balena-io-hardware/fin-info-doc/documentation/PDF/balenaFin/v1.1/conformity/CAN/Lab/DFS.pdf

JianYan Testing Group Shenzhen Co., Ltd.

### Report No: JYTSZE201205705

Authorized Signature:

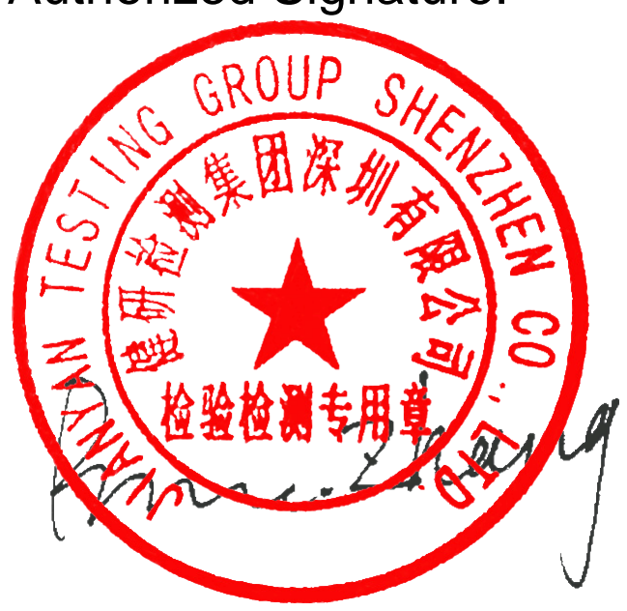
[picture p44: figure]

Bruce Zhang
Laboratory Manager
This report details the results of the testing carried out on one sample. The results contained in this test report do not relate to other samples of the same product and does not permit the use of the JYT product certification mark. The manufacturer should ensure that all products in series production are in conformity with the product sample detailed in this report.

This report may only be reproduced and distributed in full. If the product in this report is used in any configuration other than that detailed in the report, the manufacturer must ensure the new system complies with all relevant standards.

This document cannot be reproduced except in full, without prior written approval of the Company. Any unauthorized alteration, forgery or falsification of the content or appearance of this document is unlawful and offenders may be prosecuted to the fullest extent of the law. Unless otherwise stated the results shown in this test report refer only to the sample(s) tested and such sample(s) are retained for 90 days only.

## 1 Cover Page

# DFS TEST REPORT

Applicant: | Balena Ltd.
Address of Applicant: | 6th Floor, One London Wall London, London, EC2Y 5EB United Kingdom

### Equipment Under Test (EUT)

Product Name: | balenaFin
Model No.: | v1.1
HVIN: | FINV10
Trade mark: | balenaFin
Canada IC: | 26817-FIN0110
Applicable standards: | RSS-247 Issue 2，February 2017
Date of sample receipt: | 23 Aug., 2019
Date of Test: | 24 Aug., to 26 Dec., 2019
Date of report issued: | 12 Jan., 2021
Test Result: | PASS *

*In the configuration tested, the EUT complied with the standards specified above.

### Report No: JYTSZE201205705

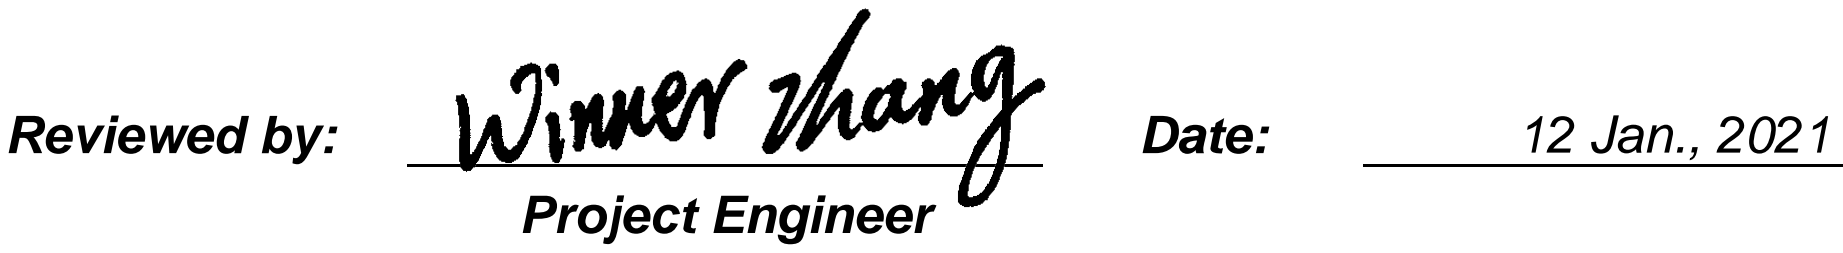
[picture p45: figure]
Reviewed by:; Date:; 12 Jan., 2021; Project Engineer

JianYan Testing Group Shenzhen Co., Ltd. | Project No.: JYTSZE2012057
No.110~116, Building B, Jinyuan Business Building, Xixiang Road,
Bao’an District, Shenzhen, Guangdong, China
Telephone: +86 (0) 755 23118282 Fax: +86 (0) 755 23116366 | Page 2 of 13

## 2 Version

Version No. | Date | Description
00 | 18 Dec., 2020 | Original
01 | 12 Jan., 2021 | Add HVIN
Tested by: | Date: | 12 Jan., 2021

### Test Engineer

Telephone: +86 (0) 755 23118282 Fax: +86 (0) 755 23116366 | Page 3 of 13

## 3 Contents

Page

Telephone: +86 (0) 755 23118282 Fax: +86 (0) 755 23116366 | Page 4 of 13

## 4 Test Summary

Test Items | Limit | Result
Channel Availability Check | > 60 seconds | N/A
UNII Detection Bandwidth | > 100% of the UNII 99% transmission power bandwidth | N/A
Statistical Performance Check | Radar type 1,2,3,4 ≧ 60% Aggregate Radar type 1~4 and 5 ≧ 80% Radar type 6 ≧ 70% | N/A
Channel Move Time | < 10 seconds | N/A
Channel Closing Transmission Time | < 20ms + aggregate of 60ms over remaining 10 second period | Pass
Non-Occupancy Period | > 30 minutes | N/A

Remark:
1. Pass: means meet the requirements.
2. N/A: means not applicable.
3. The cable insertion loss used by “RF Output Power” and other conduction measurement items is 0.5dB (provided by the customer).

Test Method:

ANSI C63.4-2014
ANSI C63.10-2013
KDB 789033 D02 General UNII Test Procedures New Rules v02r01

Telephone: +86 (0) 755 23118282 Fax: +86 (0) 755 23116366 | Page 5 of 13

## 5 General Information

## 5.1 Client Information

Applicant: | Balena Ltd.
Address: | 6th Floor, One London Wall London, London, EC2Y 5EB United Kingdom
Manufacturer: | Balena Ltd.
Address: | 6th Floor, One London Wall London, London, EC2Y 5EB United Kingdom
Factory: | Fae Technology S.p.a.
Address: | Via C. Battisti, 136 Gazzaniga (BG) 24025 - Italia
5.2 General Description of E.U.T.
Product Name: | balenaFin
Model No.: | v1.1
Transmitter frequency range: | Band 2: 5250MHz-5350MHz Band 3: 5470MHz-5725MHz
Modulation type: | OFDM
WLAN Function: | 802.11a/802.11n/802.11ac
Bandwidth: | 20MHz/40MHz/80MHz
Antenna Type: | Internal Antenna External Antenna
Antenna Gain: | Internal Antenna: 1dBi External Antenna: 2dBi
DFS Operation Type: | Master Device Slaver Device with Radar detection function Slaver Device without Radar detection function
Power supply: | DC3.3V
Test Sample Condition: | The test samples were provided in good working order with no visible defects.

## 5.3 Test Environment and test mode

Data Load mode: | Keep the EUT in normal transmitting mode by WiFi
Temperature: | 20 ~ 25 ℃
Humidity: | 60% ~ 65%
Atmospheric pressure: | 1012 kPa

## 5.4 Description of Support Units

Manufacturer | Description | Model | Serial Number
GSP | Adapter | GSCV0600S019V12E | N/A
Raspberry Pi | Compute Module | Compute Module 3/3+ Lite | N/A

## 5.5 Related Submittal(s) / Grant (s)

This is an original grant, no related submittals and grants.

## 5.6 Additions to, deviations, or exclusions from the method

No

Telephone: +86 (0) 755 23118282 Fax: +86 (0) 755 23116366 | Page 6 of 13

## 5.7 Laboratory Facility

The test facility is recognized, certified, or accredited by the following organizations:
- FCC - Designation No.: CN1211
JianYan Testing Group Shenzhen Co., Ltd. has been accredited as a testing laboratory by FCC(Federal Communications Commission). The test firm Registration No. is 727551.
- ISED – CAB identifier.: CN0021
The 3m Semi-anechoic chamber of JianYan Testing Group Shenzhen Co., Ltd. has been Registered by Certification and Engineering Bureau of Industry Canada for radio equipment testing with Registration No.: 10106A-1.
- A2LA - Registration No.: 4346.01
This laboratory is accredited in accordance with the recognized International Standard ISO/IEC 17025:2005 General requirements for the competence of testing and calibration laboratories. The test scope can be found as below link: https://portal.a2la.org/scopepdf/4346-01.pdf

## 5.8 Laboratory Location

JianYan Testing Group Shenzhen Co., Ltd.
Address: No.110~116, Building B, Jinyuan Business Building, Xixiang Road, Bao’an District, Shenzhen, Guangdong, China
Tel: +86-755-23118282, Fax:+86-755-23116366
Email: info@ccis-cb.com, Website: http://www.ccis-cb.com

## 5.9 Test Instruments list

Test Equipment | Manufacturer | Model No. | Serial No. | Cal. Due date (mm-dd-yy) | Cal. Due date (mm-dd-yy)
Spectrum Analyzer | Agilent | N9020A | MY50510123 | 11-10-2018 | 11-09- 2019
11-09-2019 | 11-08- 2020
Vector Signal Generator | Agilent | N5182A | MY49060014 | 11-10-2018 | 11-09- 2019
11-09-2019 | 11-08- 2020
RF Switch Unit | Ascentest | AT890-RFB | -- | -- | --
DFS Test Software | MWRFTEST | MTS 8310 | Version: 2.0.0.0
N7607B Signal Studio | KEYSIGHT | -- | Version: 2.0.0.1

Telephone: +86 (0) 755 23118282 Fax: +86 (0) 755 23116366 | Page 7 of 13

## 6 DFS Technical Requirements

## 6.1 DFS Parameters

Table D.1: Applicability of DFS Requirements Prior to Use of a Channel
Requirement | Operational Mode
Master | Client Without Radar Detection | Client With Radar Detection
Non-Occupancy period | Yes | Not required | Yes
DFS Detection Threshold | Yes | Not required | Yes
Channel Availability Check Time | Yes | Not required | Not required
U-NII Detection Bandwidth | Yes | Not required | Yes

Table D.2: Applicability of DFS requirements during normal operation
Requirement | Operational Mode
Master | Client Without Radar Detection
DFS Detection Threshold | Yes | Not required
Channel Closing Transmission Time | Yes | Yes
Channel Move Time | Yes | Yes
U-NII Detection Bandwidth | Yes | Not required
Additional requirements for devices with multiple bandwidth modes | Operational Mode
Master Device or Client with Radar Detection | Client Without Radar Detection
U-NII Detection Bandwidth and Statistical Performance Check | All BW modes must be tested | Not required
Channel Move Time and Channel Closing Transmission Time | Test using widest BW mode available | Test using the widest BW mode available for the link
All other tests | Any single BW mode | Not required
Note: Frequencies selected for statistical performance check (Section 7.8.4) should include several frequencies within the radar detection bandwidth and frequencies near the edge of the radar detection bandwidth. For 802.11 devices it is suggested to select frequencies in each of the bonded 20 MHz channels and the channel center frequency.

Table D.3: DFS Detection Thresholds
Maximum Transmit Power | Value (See Notes 1,2, and 3)
EIRP ≧ 200 mW | -64 dBm
EIRP < 200 mW and power spectral density < 10 dBm/MHz | -62 dBm
EIRP < 200 mW that do not meet the power spectral density requirement | -64 dBm

Note 1: This is the level at the input of the receiver assuming a 0 dBi receive antenna.
Note 2: Throughout these test procedures an additional 1 dB has been added to the amplitude of the test transmission waveforms to account for variations in measurement equipment. This will ensure that the test signal is at or above the detection threshold level to trigger a DFS response.
Note 3: EIRP is based on the highest antenna gain. For MIMO devices refer to KDB Publication 662911 D01.

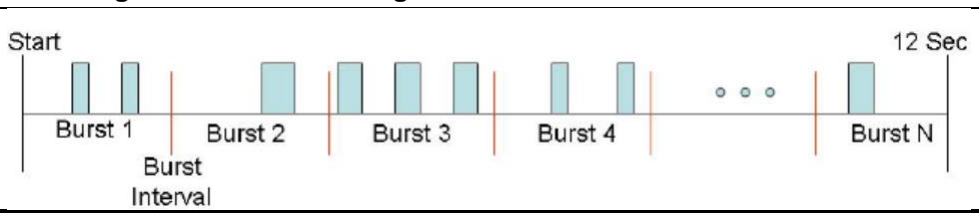
[picture p46: figure]

Telephone: +86 (0) 755 23118282 Fax: +86 (0) 755 23116366 | Page 8 of 13

Table D.4: DFS requirement values
Parameter | Value
Non-occupancy period | Minimum 30 minutes
Channel Availability Check Time | 60 seconds
Channel Move Time | 10 seconds (See Note 1)
Channel Closing Transmission Time | 200 ms + an aggregate of 60ms over remaining 10 second period (See Notes 1 and 2)
U-NII Detection Bandwidth | Minimum 100% of the UNII 99% transmission power bandwidth (See Note 3)

Note 1: Channel Move Time and the Channel Closing Transmission Time should be performed with Radar Type
0. The measurement timing begins at the end of the Radar Type 0 burst.
Note 2: The Channel Closing Transmission Time is comprised of 200 milliseconds starting at the beginning of the Channel Move Time plus any additional intermittent control signals required to facilitate a Channel move (an aggregate of 60 milliseconds) during the remainder of the 10 second period. The aggregate duration of control signals will not count quiet periods in between transmissions.
Note 3: During the U-NII Detection Bandwidth detection test, radar type 0 should be used. For each frequency step, the minimum percentage of detection is 90 percent. Measurements are performed with no data traffic.

Table D.5: Short Pulse Radar Test Waveforms
Radar Type | Pulse Width (μsec) | PRI (μsec) | Number of Pulses | Minimum Percentage of Successful Detection | Minimum Number of Trials
0 | 1 | 1428 | 18 | See Note 1 | See Note 1
1 | 1 | Test A Test B | | 60% | 30
2 | 1-5 | 150-230 | 23-29 | 60% | 30
3 | 6-10 | 200-500 | 16-18 | 60% | 30
4 | 11-20 | 200-500 | 12-16 | 60% | 30
Aggregate (Radar Types 1-4) | | | | 80% | 120
Note 1: Short Pulse Radar Type 0 should be used for the detection bandwidth test, channel move time, and channel closing time tests.

Table D.6: Long Pulse Radar Test Waveform
Radar Type | Pulse Width (μsec) | Chirp Width (MHz) | PRI (μsec) | Number of Pulses per Burst | Number of Bursts | Minimum Percentage of Successful Detection | Minimum Number of Trials
5 | 50-100 | 5-20 | 1000-2000 | 1-3 | 8-20 | 80% | 30

Long Pulse Radar Test Signal Wave form 12 second transmission

Table D.7: Frequency Hopping Radar Test Waveform
Radar Type | Pulse Width (μsec) | PRI (μsec) | Pulses per Hop | Hopping Rate (kHz) | Hopping Sequence Length (msec) | Minimum Percentage of Successful Detection | Minimum Number of Trials
6 | 1 | 333 | 0 | 0.333 | 300 | 70% | 30


Telephone: +86 (0) 755 23118282 Fax: +86 (0) 755 23116366 | Page 9 of 13

## 6.2 DFS Technical Requirements

Requirement | DFS Operational mode
Master | Slave without Radar Detection | Slave with Radar Detection
Channel Availability Check | √ | Not Required | Not Required
UNII Detection Bandwidth | √ | Not Required | √
Statistical Performance Check | √ | Not Required | √
Channel Move Time | √ | Not Required | √
Channel Closing Transmission Time | √ | √ | √
Non-Occupancy Period | √ | Not Required | √

## 6.3 DFS Threshold Level

DFS Threshold Level
5250MHz ~ 5350MHz | -62 dBm @ antenna connector
5470MHz ~ 5725MHz | -62 dBm @ antenna connector
Note: The worst case level was selected to perform the test.

## 6.4 Test Setup Block

For master device

For Slaver without radar detection function device


Telephone: +86 (0) 755 23118282 Fax: +86 (0) 755 23116366 | Page 10 of 13

For Slaver with radar detection function device

## 6.5 EUT Configuration for DFS Test

Test Items | Channel Frequency
Channel Closing Transmission Time | 5290MHz, 5530MHz

## 7 Test Result

## 7.1 Channel Move Time and Channel Closing Transmission Time

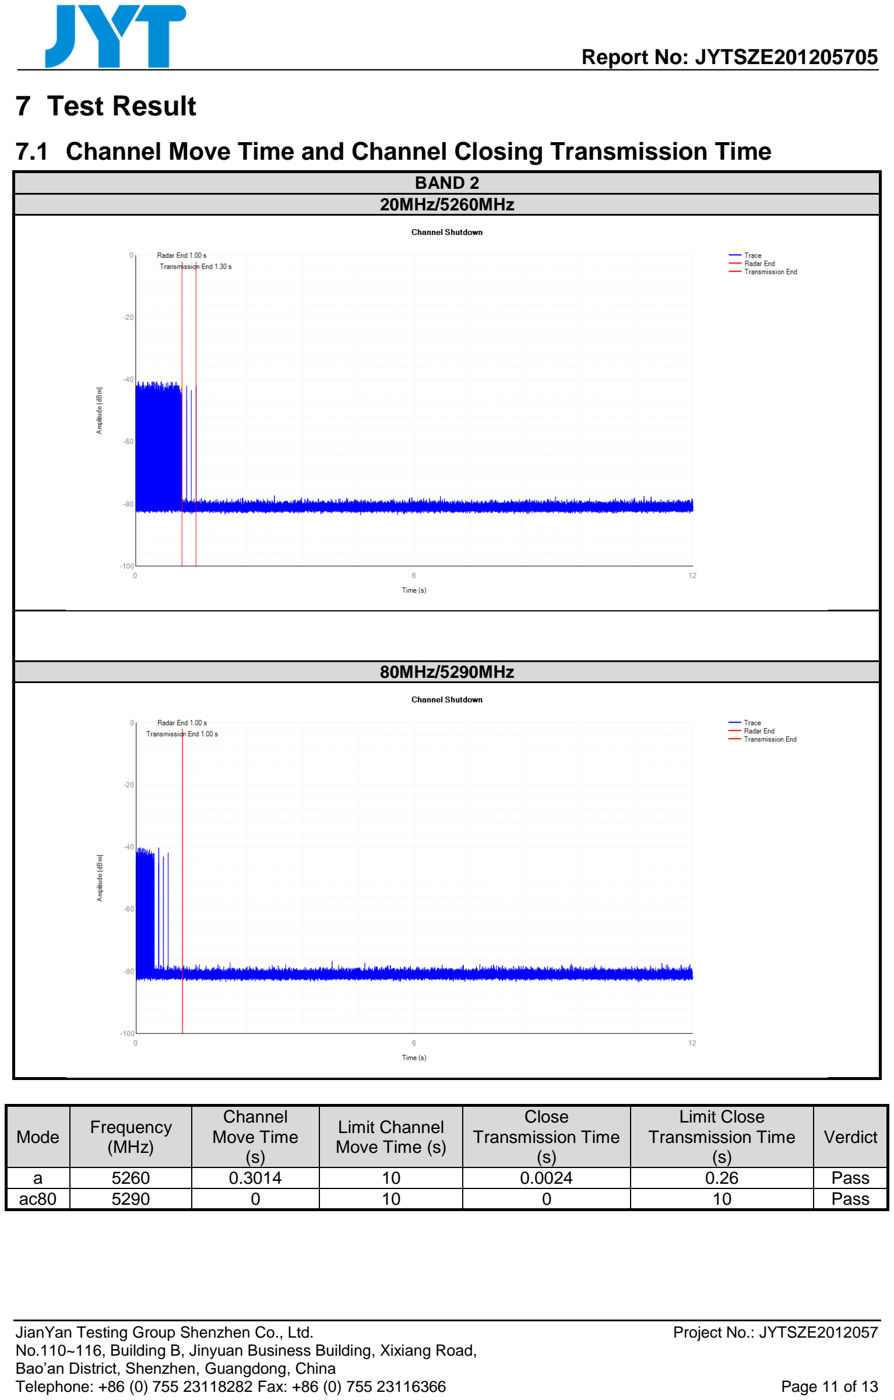
[picture p47: page 11]

Telephone: +86 (0) 755 23118282 Fax: +86 (0) 755 23116366 | Page 11 of 13

BAND 2
20MHz/5260MHz

80MHz/5290MHz

Mode | Frequency (MHz) | Channel Move Time (s) | Limit Channel Move Time (s) | Close Transmission Time (s) | Limit Close Transmission Time (s) | Verdict
a | 5260 | 0.3014 | 10 | 0.0024 | 0.26 | Pass
ac80 | 5290 | 0 | 10 | 0 | 10 | Pass

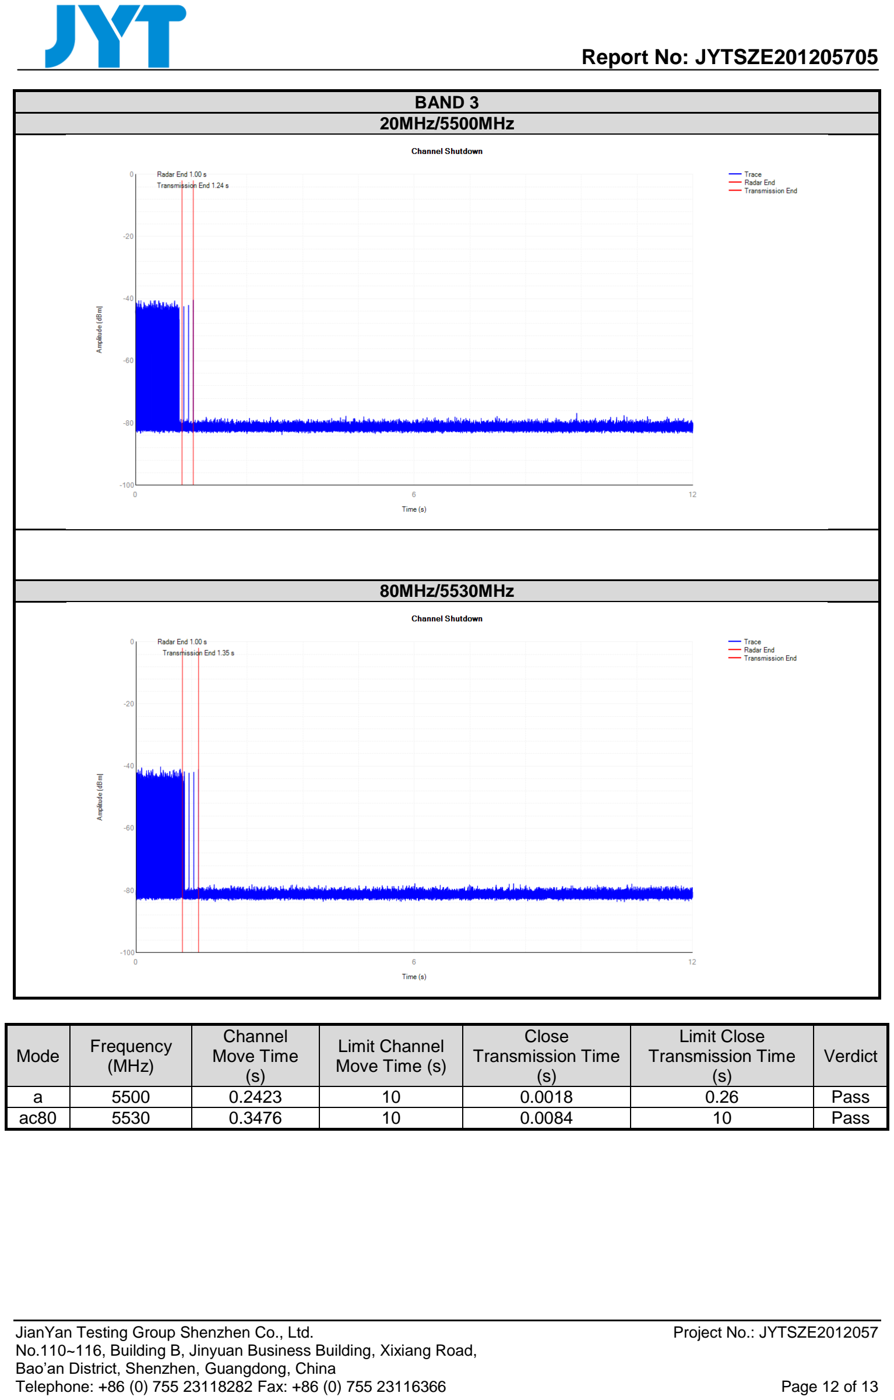
[picture p48: page 12]

Telephone: +86 (0) 755 23118282 Fax: +86 (0) 755 23116366 | Page 12 of 13

BAND 3
20MHz/5500MHz

80MHz/5530MHz

Mode | Frequency (MHz) | Channel Move Time (s) | Limit Channel Move Time (s) | Close Transmission Time (s) | Limit Close Transmission Time (s) | Verdict
a | 5500 | 0.2423 | 10 | 0.0018 | 0.26 | Pass
ac80 | 5530 | 0.3476 | 10 | 0.0084 | 10 | Pass

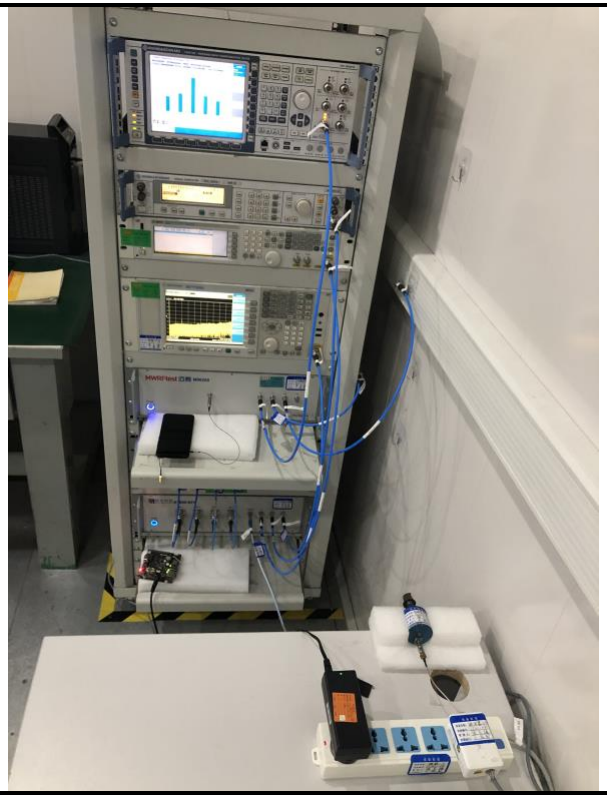
[picture p49: figure]

Telephone: +86 (0) 755 23118282 Fax: +86 (0) 755 23116366 | Page 13 of 13

## 8 Test Setup Photo

## 9 EUT Constructional Details

### Reference to the test report No.: JYTSZE201205701

### ------ End of report ------
