balena-io-hardware/fin-info-doc/documentation/PDF/balenaFin/v1.0/conformity/FCC/Lab/FCC_EMC.pdf

Applicant: Resin.io

Report: EMC_SL18040601-RIO-001_FCC_ISED

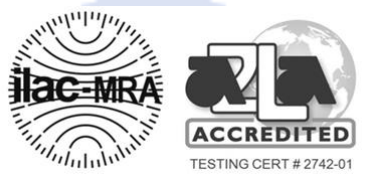
[picture p77: figure]

SIEMIC | 775 Montague Expressway, Milpitas, CA 95035 | Ph.+1 408-526-1188 | Fax: +1 408-526-1088 | www.siemic.com

Page 1 of 27

# EMC TEST REPORT

## Report: EMC_ SL18040601-RIO-001_FCC_ISED

## Supersedes: None

Applicant Name: | Resin.io
Product Name: | Balena Fin
Model Name: | Balena Fin
Test Standard: | FCC 15 Subpart B (Class A) ICES 003 Issue 6:2017
Test Method: | ANCI C63.4
Date of Test: | 04-30/2018 & 05/01/2018
Report Issue Date: | 05/21/2018
Test Result: | ☒ Pass | ☐ Fail
Equipment complied with the specifications: | ☒

Equipment did not comply with the specifications: ☐

This test report is issued under the authority of:

Full Name: | Kushal Shastri | Full Name: | Anish Kumar
Title: | EMC Test Engineer | Title: | Compliance Engineer(Reviewer)
This test report may be reproduced in full only. Test result presented in this test report is applicable to the tested sample only.

### ISSUED BY: SIEMIC Laboratories 775 Montague Expressway, Milpitas, CA 95035 USA

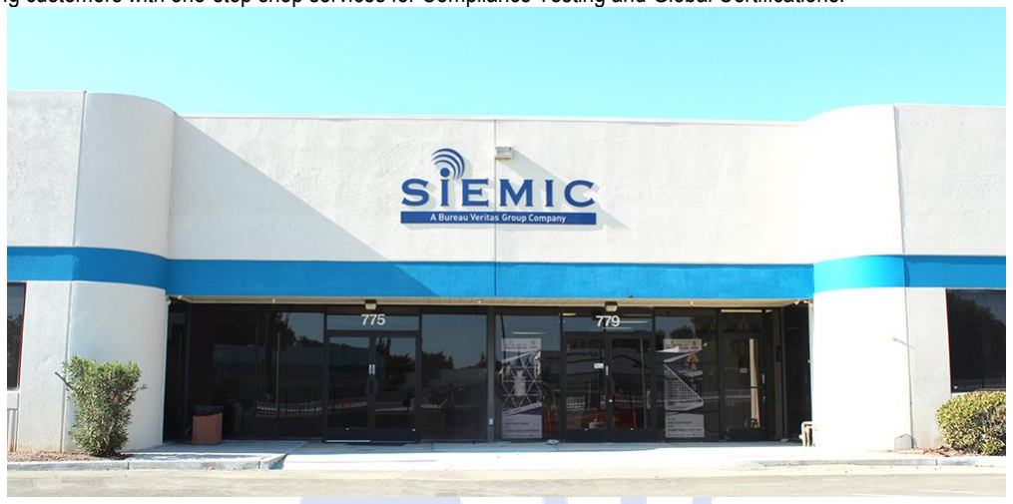
[picture p78: figure]

Page 2 of 27

# Laboratory Introduction

SIEMIC, headquartered in the heart of Silicon Valley, with superior facilities in US and Asia, is one of the leading independent testing and certification facilities providing customers with one-stop shop services for Compliance Testing and Global Certifications.

In addition to testing (http://www.siemic.com/Pages/ComplianceTest.htm) and certification, (http://www.siemic.com/Pages/GlobalCertification.htm) SIEMIC provides initial design reviews and compliance management (http://www.siemic.com/Pages/Management.htm) throughout a project. Our extensive experience with China, (http://www.siemic.com/Pages/ChinaApprovals.htm) Asia Pacific, (http://www.siemic.com/Pages/AsiaApprovals.htm) North America, European, and International (http://www.siemic.com/Pages/GlobalCertification.htm) compliance requirements, assures the fastest, most cost effective way to attain regulatory compliance for the global markets. (http://www.siemic.com/Pages/GlobalCertification.htm)

Accreditations for conformity assessment
Country/Region Accreditation Body | Scope
USA | FCC, A2LA | EMC, RF/Wireless, Telecom
Canada | IC, A2LA, NIST | EMC, RF/Wireless, Telecom
Taiwan | BSMI, NCC, NIST | EMC, RF, Telecom, Safety
Hong Kong | OFTA, NIST | RF/Wireless, Telecom
Australia | NATA, NIST | EMC, RF, Telecom, Safety
Korea | KCC/RRA, NIST | EMI, EMS, RF, Telecom, Safety
Japan | VCCI, JATE, TELEC, RFT | EMI, RF/Wireless, Telecom
Mexico | NOM, COFETEL, Caniety | Safety, EMC, RF/Wireless, Telecom
Europe | A2LA, NIST | EMC, RF, Telecom, Safety
Israel | MOC, NIST | EMC, RF, Telecom, Safety

Accreditations for conformity assessment
Country/Region Accreditation Body | Scope
USA | FCC TCB, NIST | EMC, RF, Telecom
Canada | ISED FCB, NIST | EMC, RF, Telecom
Singapore | iDA, NIST | EMC, RF, Telecom
EU | NB | EMC & RED Directive
Japan | MIC (RCB 208) | RF, Telecom
Hong Kong | OFTA (US002) | RF, Telecom

Page 3 of 27

### Table of Contents

Page 4 of 27

## 1. Report revision history

Report No. | Version No. | Description | Issue Date
EMC_SL18040601-RIO-001_FCC_ISED | Original Report | FCC_ISED Report | 05/21/2018

## 2. Executive summary

The purpose of this test program was to demonstrate compliance of following product:

Company: Resin.io
Product: Balena Fin
Model: Balena Fin

against the current Stipulated Standards. The specified model product stated above has demonstrated compliance with the Stipulated Standard listed on 1st page.

## 3. Customer information

Applicant Name: | Resin.io
Applicant Address: | 7 Winkley Street, London E2 6PY, UK
Manufacturer Name: | Resin.io
Manufacturer Address: | 7 Winkley Street, London E2 6PY, UK

## 4. Test site information

Lab Performing Tests: | SIEMIC Laboratories
Lab Address: | 775 Montague Expressway, Milpitas, CA 95035
FCC Test Site No: | 881796
IC Test Site No: | 4842D-2

## 5. Modification

Index | Item | Description | Note
1 | N/A | N/A | -

Page 5 of 27

## 6. Test software version

Test Item | Vendor | Software | Version
Radiated Emission | EMISoft | EMISoft Vasona | V6.0
Conducted Emission | EMISoft | EMISoft Vasona | V5.0

Page 6 of 27

## 7. EUT Information

### 7.1. EUT Description

Product Name: | Balena Fin
Trade Name: | Resin.in
Model No: | Balena Fin
Serial No.: | N/A
Input Power: | 120VAC/60Hz
Date of EUT received: | 04/15/2018
Equipment Class: | Class A
Highest frequency generated or used in the device or on which the device operates or tunes: | 5.8GHz
Port/Connectors: | 1 X RJ45, 2 X USB, 1 X mini USB, 1 X HDMI
Remark: | N/A

Page 7 of 27

### 7.2. EUT Test modes / Configuration description

### 7.2.1.EUT Test modes: Pre-test mode

Pre-scan Test Mode

Mode 1 | Normal Operation- Manufacturer specific
Remark: | EUT was continuously communicating with laptop via wired connection through a router.

### 7.2.2.EUT Test modes: Final test mode

Final Test Mode

Mode 1 | Normal Operation- Manufacturer specific
Remark: | EUT was continuously communicating with laptop via wired connection through a router.

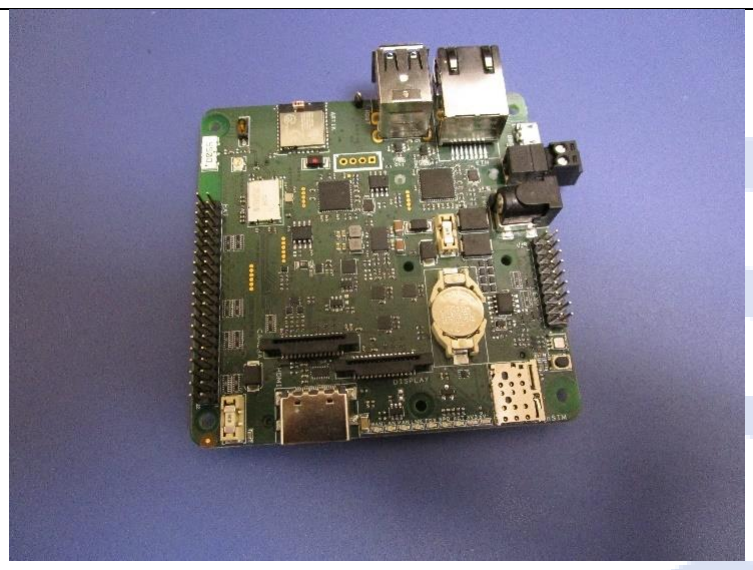
[picture p79: figure]

Page 8 of 27

### 7.3. EUT Photos

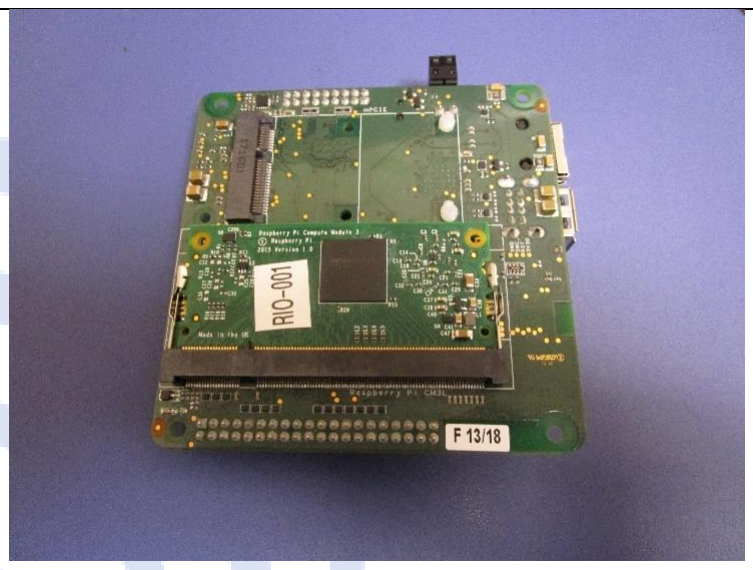
[picture p80: figure]

Picture-1 | Picture-2

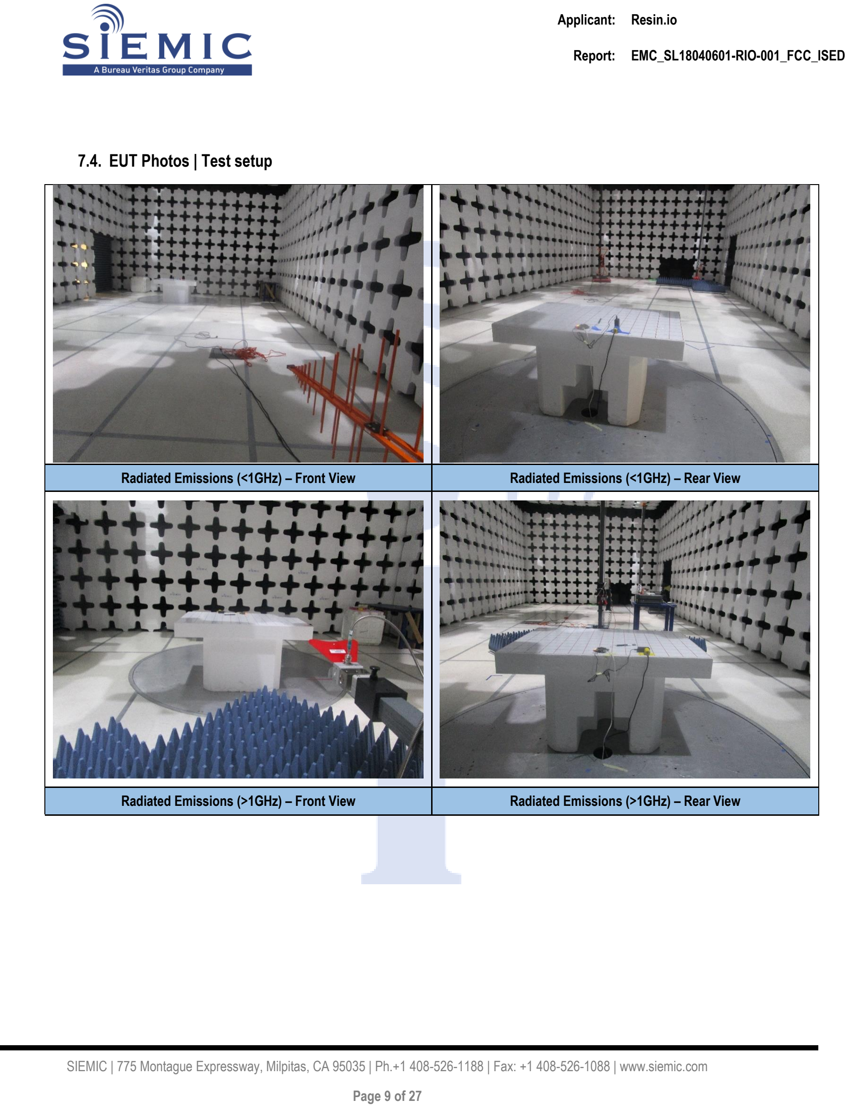
[picture p81: page 9]

Page 9 of 27

### 7.4. EUT Photos | Test setup

Radiated Emissions (<1GHz) – Front View | Radiated Emissions (<1GHz) – Rear View
Radiated Emissions (>1GHz) – Front View | Radiated Emissions (>1GHz) – Rear View

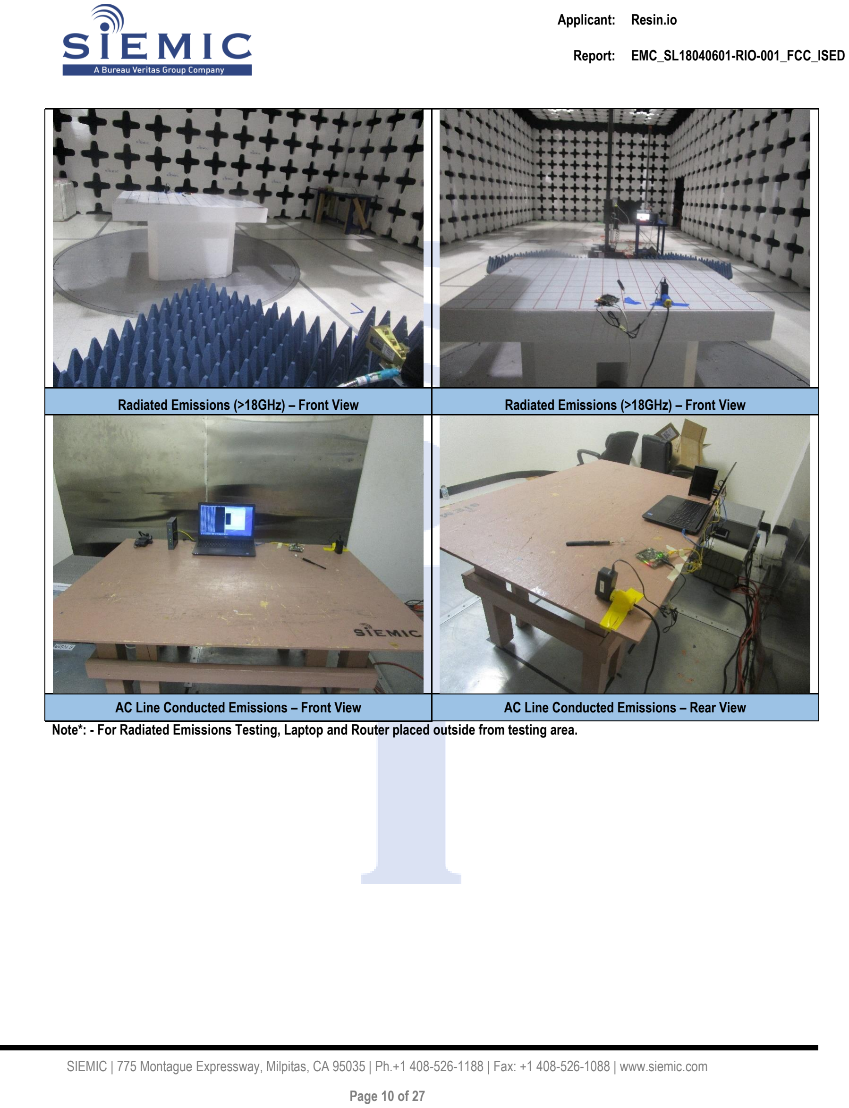
[picture p82: page 10]

Page 10 of 27

Radiated Emissions (>18GHz) – Front View | Radiated Emissions (>18GHz) – Front View
AC Line Conducted Emissions – Front View | AC Line Conducted Emissions – Rear View
Note*: - For Radiated Emissions Testing, Laptop and Router placed outside from testing area.

Page 11 of 27

## 8. Supporting equipment / Software / Cabling information

### 8.1. Support equipment

Item | Support Equipment Description | Model | Serial Number | Manufacturer
1 | Router | WNR3500L | 215802000480 | Net gear
2 | Laptop | Vostro 1520 | C6ZKQK1 | DELL

### 8.2. I/O Ports

Item | Connection Start | Connection Stop | Length / shielding Info
From | I/O Port | To | I/O Port | Length (m) | Shielding
1 | Laptop | RJ45 | Router | RJ45 | <3M | No
2 | EUT | RJ45 | Router | RJ45 | <3M | No

### 8.3. Test software description

Test Item | Software | Description
1 | Command Prompt | For Continuously pinging the EUT via Laptop
2 | Resin.io | Manufacturer Provided Test Mode Software

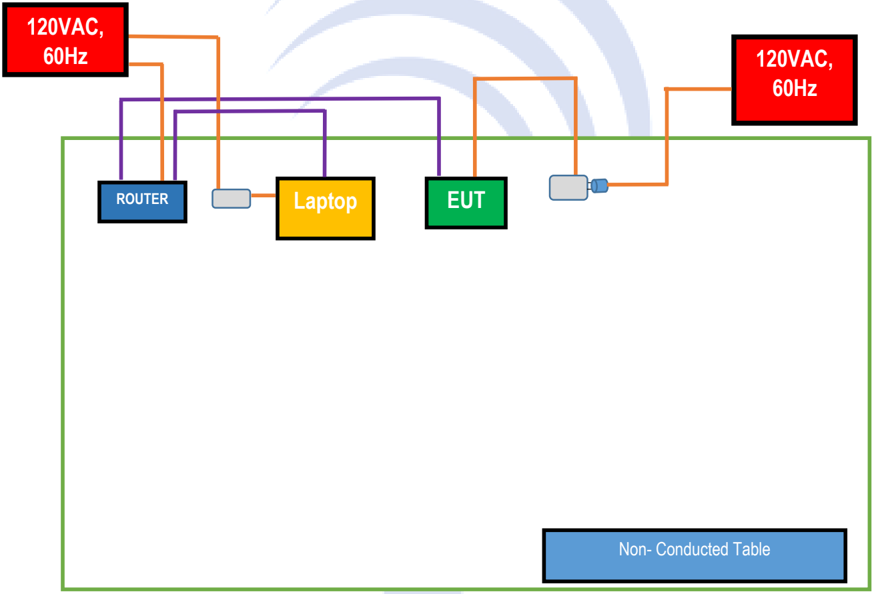
[picture p83: figure]
Non- Conducted Table; EUT; 120VAC, 60Hz; ROUTER; Laptop

Page 12 of 27

### 8.4. System setup block diagram

RJ45

### POWER Cable

Page 13 of 27

## 9. Test summary

Emissions
Test Item | Test Standard | Test Method / Procedure | Pass / Fail
AC Conducted Emissions | FCC 15 Subpart B (Class A) ICES 003 Issue 6:2017 | ANSI C63.4:2014 | X Pass Fail N/A
Radiated Spurious Emissions Below 1GHz | FCC 15 Subpart B (Class A) ICES 003 Issue 6:2017 | ANSI C63.4:2014 | X Pass Fail N/A
Radiated Spurious Emissions Above 1GHz | FCC 15 Subpart B (Class A) ICES 003 Issue 6:2017 | ANSI C63.4:2014 | X Pass Fail N/A

## 10.Measurement uncertainty

Emissions
Test Item | Frequency Range | Description | Uncertainty
AC Conducted Emissions | 150KHz – 30MHz | Confidence level of approximately 95% (in the case where distributions are normal), with a coverage factor of 2 | ±3.5dB
Radiated Spurious Emissions | 30MHz – 1GHz | Confidence level of approximately 95% (in the case where distributions are normal), with a coverage factor of 2 (for EUTs < 0.5m X 0.5m X 0.5m) | +5.6dB/-4.5dB
Radiated Spurious Emissions | >1GHz | Confidence level of approximately 95% (in the case where distributions are normal), with a coverage factor of 2 (for EUTs < 0.5m X 0.5m X 0.5m) | +4.3dB/-4.1dB

Page 14 of 27

## 11.Frequency Range of Radiated Measurements

### (b) For unintentional radiators:

(1) Except as otherwise indicated in paragraphs (b)(2) or (b)(3) of this section, for an unintentional radiator, including a digital device, the spectrum shall be investigated from the lowest radio frequency signal generated or used in the device, without going below the lowest frequency for which a radiated emission limit is specified, up to the frequency shown in the following table:
(2) A unintentional radiator, excluding a digital device, in which the highest frequency generated in the device, the highest frequency used

in the device and the highest frequency on which the device operates or tunes are less than 30 MHz and which, in accordance with §15.109, is required to comply with standards on the level of radiated emissions within the frequency range 9 kHz to 30 MHz, such as a CB receiver or a device designed to conduct its radio frequency emissions via connecting wires or cables, e.g., a carrier current system not intended to radiate, shall be investigated from the lowest radio frequency generated or used in the device, without going below 9 kHz (25 MHz for CB receivers), up to the frequency shown in the following table. If the unintentional radiator contains a digital device, the upper frequency to be investigated shall be that shown in the table below or in the table in paragraph (b)(1) of this section, as based on both the highest frequency generated and the highest frequency used in the digital device, whichever range is higher.

Highest frequency generated or used in the device or on which the device operates or tunes (MHz) | Upper frequency of measurement range (MHz)
Below 1.705 | 30
1.705-10 | 400
10-30 | 500
(3) Except for a CB receiver, a receiver employing superheterodyne techniques shall be investigated from 30 MHz up to at least the second harmonic of the highest local oscillator frequency generated in the device. If such receiver is controlled by a digital device, the frequency range shall be investigated up to the higher of the second harmonic of the highest local oscillator frequency generated in the device or the upper frequency of the measurement range specified for the digital device in paragraph (b)(1) of this section.

Example:

If the EUT has a transceiver operating or tunes at 2.4GHz, then both the Receiver, and the Transmitter needs to be tested separately to the Fifth Harmonic (e.g. Upper Frequency range would be 12GHz). A Transceiver consists of both a transmitter and a receiver, the receiver portion of which is always subject to the part 15 Subpart B Unintentional Radiator rules.

highest frequency generated or used in the device or on which the device operates or tunes (MHz) | Upper frequency of measurement range (MHz)
Below 1.705 | 30.
1.705-108 | 1000.
108-500 | 2000.
500-1000 | 5000.
Above 1000 | 5th harmonic of the highest frequency or 40 GHz, whichever is lower.

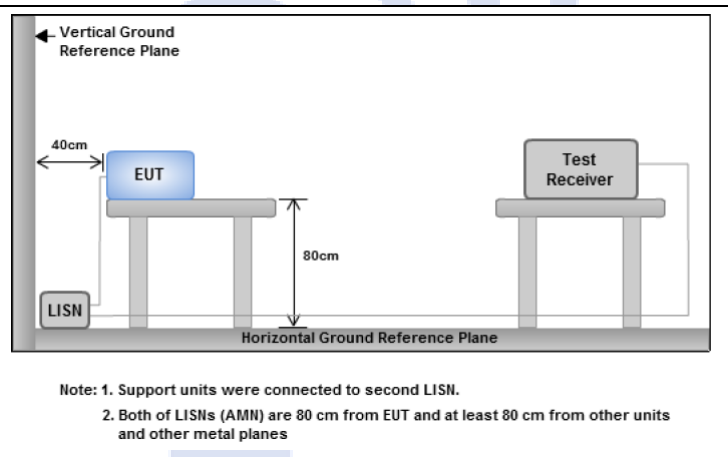
[picture p84: figure]

Page 15 of 27

## 12.Guideline for interference allowed

### 12.1. Conducted emissions

Spec | Item | Requirement | Applicable
§ 15.107 ICES 003 Issue 6:2017 | a) Except for Class A digital devices, for equipment that is designed to be connected to the public | utility (AC) power line, the radio frequency voltage that is conducted back onto the AC power line on any frequency or frequencies within the band 150 kHz to 30 MHz shall not exceed the limits set in § 15.107 (a), as measured using a 50 μH/50 ohms line impedance stabilization network (LISN). Limits for Conducted Emissions at the Mains Ports | YES
Section | Frequency ranges (MHz) | Limit (dBuV)
QP | Average
Class A devices | 0.15 ~ 0.5 | 79 | 66
0.5 ~ 30 | 73 | 60
NOTE 1 The lower limit shall apply at the transition frequencies.

Test Setup

Procedure

1. The EUT and supporting equipment were set up in accordance with the requirements of the standard on top of a 1.5m x 1m x 0.8m high, non-metallic table.
2. The power supply for the EUT was fed through a 50 /50 H EUT LISN, connected to filtered mains.
3. The RF OUT of the EUT LISN was connected to the EMI test receiver via a low-loss coaxial cable.
4. All other supporting equipment was powered separately from another main supply.
5. The EUT was switched on and allowed to warm up to its normal operating condition.
6. A scan was made on the Neutral/Phase line (for AC mains) or Earth line over the required frequency range using an EMI test receiver.
7. High peaks, relative to the limit line, were then selected.
8. The EMI test receiver was then tuned to the selected frequencies and the necessary measurements made with a receiver bandwidth setting of 10 kHz. For FCC tests, only Quasi-peak measurements were made; while for CISPR/EN tests, both Quasi-peak and Average measurements were made
9. All possible modes of operation were investigated. Only the 6 worst case emissions were measured and reported. All other emissions were relatively insignificant.

Page 16 of 27

Description of the
Conducted
Emission
Program

This EMC Measurement software, EMI Soft Vasona offers a common user interface for electromagnetic interference (EMI) measurements. This software is a modern and powerful tool for controlling and monitoring EMI test receivers and EMC test systems. It guarantees reliable collection, evaluation, and documentation of measurement results. Basically, this program will run a pre-scan measurement before it proceeds with the final measurement. The pre-scan routine will run the common scan range from 15 kHz to 30 MHz; the program will first start a peak and average scan on selectable measurement time and step size. After the program complete the pre-scan, this program will perform the Quasi Peak and Average measurement, based on the pre-scan peak data reduction result.

Sample Calculation Example | At 20 MHz limit = 250 µV = 47.96 dBµV Transducer factor of LISN, pulse limiter & cable loss at 20 MHz = 11.20 dB Q-P reading obtained directly from EMI Receiver = 40.00 dBµV (Calibrated for system losses) Therefore, Q-P margin = 47.96 – 40.00 = 7.96 i.e. 7.96 dB below limit
Remarks | N/A
Test Data: | Yes | X N/A
Test Plot: | Yes (See below) | X N/A

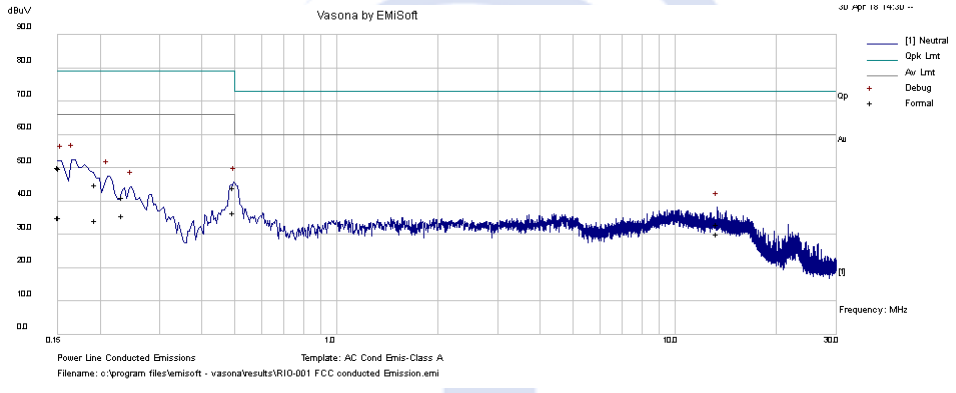
[picture p85: figure]

Page 17 of 27

Test specification: | AC Conducted Emissions (Class A)
Environmental Conditions: | Temp(°C): | 22.60 | Result:
| Humidity (%): | 46.70 | | X Pass
| Atmospheric(mbar): | 1019.30
Mains Power: | 120Vac, 60Hz
Tested by: | Kushal Shastri
Test Date: | 04/30/2018
Remarks: | Neutral Connection
Frequency (MHz) | Raw (dBuV) | Cable Loss (dB) | Factors (dB) | Level (dBuV) | Measurement Type | Line/ Neutral | Limit (dBuV) | Margin (dB) | Pass /Fail
0.151792 | 40.54 | 9.33 | 0.05 | 49.92 | Quasi Peak | Neutral | 79 | -29.08 | Pass
0.15 | 40.65 | 9.33 | 0.05 | 50.03 | Quasi Peak | Neutral | 79 | -28.97 | Pass
0.19378 | 35.47 | 9.32 | 0.04 | 44.83 | Quasi Peak | Neutral | 79 | -34.17 | Pass
0.497519 | 34.62 | 9.33 | 0.04 | 43.99 | Quasi Peak | Neutral | 79 | -35.01 | Pass
0.232978 | 31.89 | 9.32 | 0.04 | 41.25 | Quasi Peak | Neutral | 79 | -37.75 | Pass
13.35767 | 23.44 | 9.37 | 0.32 | 33.12 | Quasi Peak | Neutral | 73 | -39.88 | Pass
0.151792 | 25.7 | 9.33 | 0.05 | 35.08 | Average | Neutral | 66 | -30.92 | Pass
0.15 | 25.65 | 9.33 | 0.05 | 35.03 | Average | Neutral | 66 | -30.97 | Pass
0.19378 | 24.76 | 9.32 | 0.04 | 34.13 | Average | Neutral | 66 | -31.87 | Pass
0.497519 | 27.3 | 9.33 | 0.04 | 36.66 | Average | Neutral | 66 | -29.34 | Pass
0.232978 | 26.43 | 9.32 | 0.04 | 35.79 | Average | Neutral | 66 | -30.21 | Pass
13.35767 | 20.54 | 9.37 | 0.32 | 30.22 | Average | Neutral | 60 | -29.78 | Pass

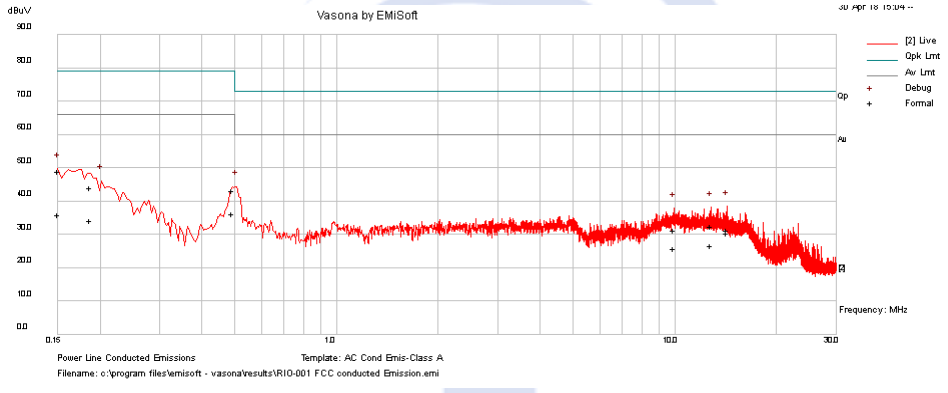
[picture p86: figure]

Page 18 of 27

Test specification: | AC Conducted Emissions (Class A)
Environmental Conditions: | Temp(°C): | 22.60 | Result:
| Humidity (%): | 46.70 | | X Pass
| Atmospheric(mbar): | 1019.30
Mains Power: | 120Vac, 60Hz
Tested by: | Kushal Shastri
Test Date: | 04/30/2018
Remarks: | Live Connection
Frequency (MHz) | Raw (dBuV) | Cable Loss (dB) | Factors (dB) | Level (dBuV) | Measurement Type | Line/ Neutral | Limit (dBuV) | Margin (dB) | Pass /Fail
0.494104 | 33.87 | 9.33 | 0.04 | 43.24 | Quasi Peak | Live | 79 | -35.76 | Pass
0.150086 | 39.45 | 9.33 | 0.05 | 48.83 | Quasi Peak | Live | 79 | -30.17 | Pass
0.187599 | 34.75 | 9.32 | 0.04 | 44.12 | Quasi Peak | Live | 79 | -34.88 | Pass
14.27571 | 21.57 | 9.37 | 0.34 | 31.29 | Quasi Peak | Live | 73 | -41.71 | Pass
12.80789 | 22.69 | 9.37 | 0.31 | 32.37 | Quasi Peak | Live | 73 | -40.63 | Pass
9.938124 | 21.26 | 9.96 | 0.22 | 31.44 | Quasi Peak | Live | 73 | -41.56 | Pass
0.494104 | 26.74 | 9.33 | 0.04 | 36.11 | Average | Live | 66 | -29.89 | Pass
0.150086 | 26.67 | 9.33 | 0.05 | 36.05 | Average | Live | 66 | -29.95 | Pass
0.187599 | 24.84 | 9.32 | 0.04 | 34.2 | Average | Live | 66 | -31.8 | Pass
14.27571 | 20.73 | 9.37 | 0.34 | 30.45 | Average | Live | 60 | -29.55 | Pass
12.80789 | 16.87 | 9.37 | 0.31 | 26.55 | Average | Live | 60 | -33.45 | Pass
9.938124 | 15.51 | 9.96 | 0.22 | 25.7 | Average | Live | 60 | -34.3 | Pass

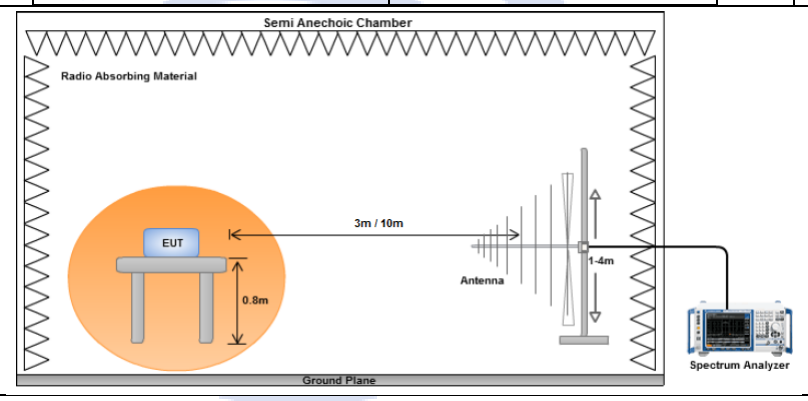
[picture p87: figure]

Page 19 of 27

### 12.2. Radiated Emissions Below 1GHz (Class A)

Requirement(s):

Spec | Item | Requirement | Applicable
§ 15.109 ICES 003 Issue 6:2017 | a) Except for Class A digital devices, the field strength of radiated emissions from unintentional | radiators at a distance of 3 meters shall not exceed the following values: | Yes
Frequency range (MHz) | Quasi Peak Limit (uV/m)
30 – 88 | 38
88 – 216 | 44
216 960 | 47
Above 960 | 49

Test Setup

Procedure

1. The EUT and supporting equipment were set up in accordance with the requirements of the standard on top of a 1.5m X 1.0m X 0.8m high, non-metallic table
2. The EUT was switched on and allowed to warm up to its normal operating condition.
3. The test was carried out at the selected frequency points obtained from the EUT characterisation. Maximization of the emissions, was carried out by rotating the EUT, changing the antenna polarization, and adjusting the antenna height in the following manner:
a. Vertical or horizontal polarisation (whichever gave the higher emission level over a full rotation of the EUT) was chosen.
b. The EUT was then rotated to the direction that gave the maximum emission.
c. Finally, the antenna height was adjusted to the height that gave the maximum emission.
4. A Quasi-peak measurement was then made for that frequency point.
5. Steps 3 and 4 were repeated for the next frequency point, until all selected frequency points were measured.
6. The frequency range covered was from 30MHz to 1GHz using the broadband antenna.

Description of
the Radiated
Emissions
Program

This EMC Measurement software, EMI Soft Vasona offers a common user interface for electromagnetic interference (EMI) measurements. This software is a modern and powerful tool for controlling and monitoring EMI test receivers and EMC test systems. It guarantees reliable collection, evaluation, and documentation of measurement results. Basically, this program will run a pre-scan measurement before it proceeds with the final measurement. The pre-scan routine will run the scan on four different antenna heights, 2 antenna polarity, and 360 degrees table rotation. For example, the program was set to run 30 MHz to 1 GHz scan; the program will first start from a meter antenna height and divide the 30 MHz to 1 GHz into 10 separate parts of maximum hold sweeps. Each parts of maximum hold sweep, the program will collect the data from 0 degree to 360 degrees table rotation. After the program complete the 1m scan, the antenna continues to rise to 2m and continue the scan. The step will repeated for all specified antenna height and polarity. This program will perform the Quasi Peak measurement after the signal maximization process and pre-scan routine. The final measurement will be based on the pre-scan data reduction result.

Page 20 of 27

Sample Calculation Example | At 300 MHz limit = 200 µV/m = 46.00 dBµV/m Log-periodic antenna factor & cable loss at 300 MHz = 18.50 dB Q-P reading obtained directly from EMI Receiver = 40.00 dBµV/m (Calibrated level including antenna factors & cable losses Therefore, Q-P margin = 46.00 – 40.00 = 6.00 i.e. 6 dB below limit
Remarks | N/A
Test Data: | X Yes (See below) | N/A
Test Data: | X Yes (See below) | N/A

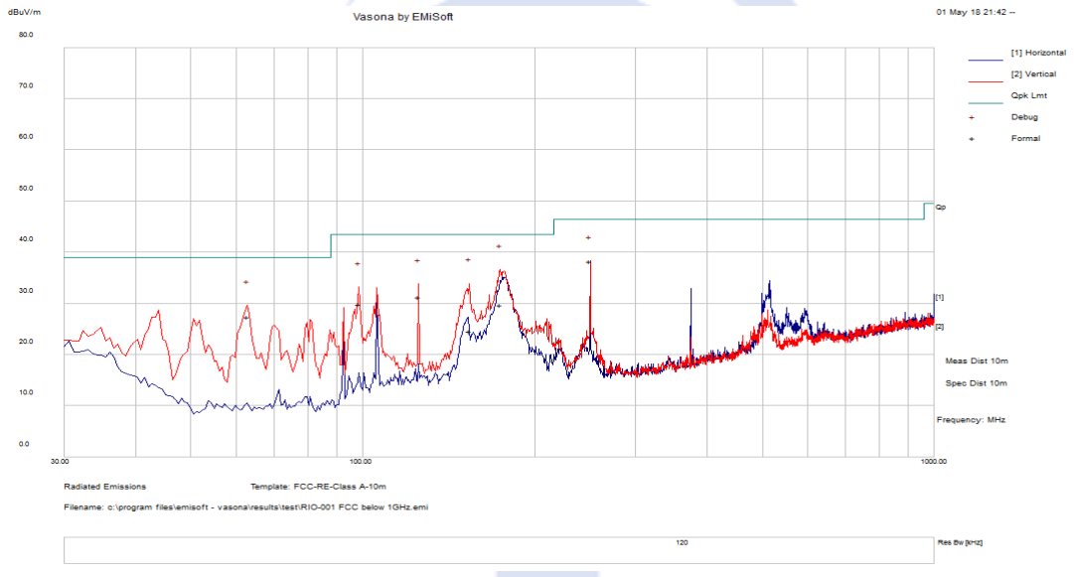
[picture p88: figure]

Page 21 of 27

### Radiated Emission Test Results (Below 1GHz, Class A)

Test specification: | Radiated Emissions (Below 1GHz)
Environmental Conditions: | Temp(°C): | 25.7 | Result:
| Humidity (%): | 43.3 | | X Pass
| Atmospheric(mbar): | 1014.9
Mains Power: | 120VAC~60Hz
Tested by: | Kushal Shastri | | | Fail
Test Date: | 05/01/2018
Remarks: | The testing was done in a 3m chamber
Frequency (MHz) | Raw (dBuV) | Cable Loss (dB) | AF (dB) | Level (dBuV/m) | Measurement Type | Pol | Hgt (cm) | Azt (Deg) | Limit (dBuV/m) | Margin (dB) | Pass /Fail
173.7413 | 41.99 | 12.38 | -24.57 | 29.8 | Quasi Max | V | 176 | 259 | 43.5 | -13.7 | Pass
249.9972 | 50.54 | 12.93 | -25.2 | 38.27 | Quasi Max | V | 105 | 18 | 46.4 | -8.14 | Pass
62.77125 | 43.5 | 11.53 | -27.69 | 27.34 | Quasi Max | V | 169 | 34 | 39 | -11.66 | Pass
153.8784 | 35.96 | 12.21 | -23.61 | 24.57 | Quasi Max | V | 251 | 138 | 43.5 | -18.94 | Pass
125.0022 | 42.09 | 12.12 | -22.93 | 31.29 | Quasi Max | V | 100 | 78 | 43.5 | -12.22 | Pass
98.48094 | 43.86 | 11.87 | -25.8 | 29.93 | Quasi Max | V | 247 | 45 | 43.5 | -13.57 | Pass

Page 22 of 27

### 12.3. Radiated Emissions above 1GHz (Class A)

Requirement(s):

Spec | Item | Requirement | Applicable
§ 15.109 ICES 003 Issue 6:2017 | a) Except for Class A digital devices, the field strength of radiated emissions from | unintentional radiators at a distance of 3 meters shall not exceed the following values: | YES
Frequency range (GHz) | Average limit dB(uV/m) | Peak limit dB(uV/m)
Above 1 | 60 | 80

Test Setup

Procedure

1. The EUT and supporting equipment were set up in accordance with the requirements of the standard on top of a 1.5m X 1.0m X 0.8m high, non-metallic table
2. The EUT was switched on and allowed to warm up to its normal operating condition.
3. The test was carried out at the selected frequency points obtained from the EUT characterisation. Maximization of the emissions, was carried out by rotating the EUT, changing the antenna polarization, and adjusting the antenna height in the following manner:
a. Vertical or horizontal polarisation (whichever gave the higher emission level over a full rotation of the EUT) was chosen.
b. The EUT was then rotated to the direction that gave the maximum emission.
c. Finally, the antenna height was adjusted to the height that gave the maximum emission.
4. A Peak and Average measurement was then made for that frequency point.
5. Steps 3 and 4 were repeated for the next frequency point, until all selected frequency points were measured.
6. The frequency range covered was from 1GHz to 6GHz (for FCC tests, until the 5th harmonic for operating frequencies > 1000MHz) using a horn antenna.
Remarks | NA
Test Data: | X Yes (See below) | N/A
Test Data: | X Yes (See below) | N/A

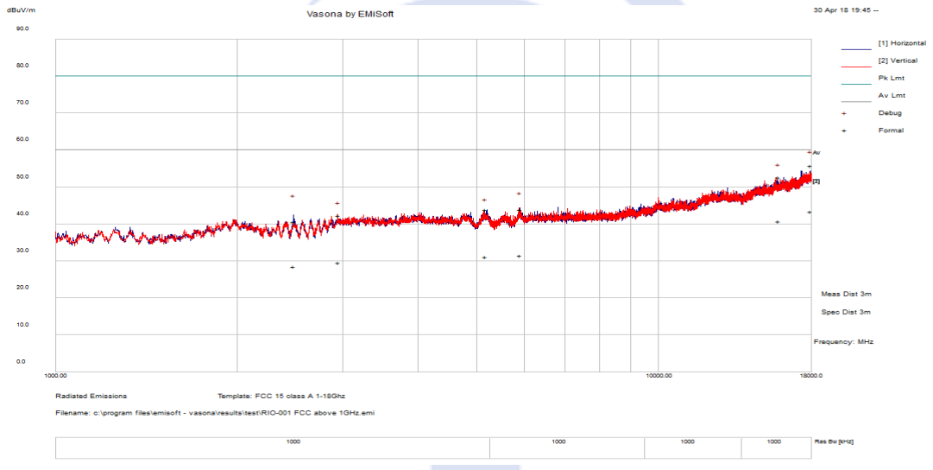
[picture p89: figure]

Page 23 of 27

Test specification: | Radiated Emissions (Above 1GHz)
Environmental Conditions: | Temp(°C): | 25.7 | Result:
| Humidity (%): | 43.3 | | X Pass
| Atmospheric(mbar): | 1014.9
Mains Power: | 120VAC~60Hz
Tested by: | Kushal Shastri | | | Fail
Test Date: | 04/30/2018
Remarks: | 1-18GHz. The testing was done in a 10m chamber
Frequency (MHz) | Raw (dBuV) | Cable Loss (dB) | AF (dB) | Level (dBuV/m) | Measurement Type | Pol | Hgt (cm) | Azt (Deg) | Limit (dBuV/m) | Margin (dB) | Pass /Fail
17938.16 | 39.26 | 7.93 | 8.69 | 55.87 | Peak Max | H | 104 | 86 | 80 | -24.13 | Pass
15897.38 | 39.09 | 7.8 | 5.86 | 52.76 | Peak Max | V | 239 | 93 | 80 | -27.25 | Pass
5899.807 | 39.8 | 4.75 | -0.6 | 43.96 | Peak Max | V | 135 | 156 | 80 | -36.04 | Pass
2484.191 | 41.26 | 3 | -3.66 | 40.6 | Peak Max | H | 287 | 90 | 80 | -39.41 | Pass
5171.113 | 40.64 | 4.33 | -1.03 | 43.95 | Peak Max | V | 142 | 38 | 80 | -36.05 | Pass
2948.423 | 40.91 | 3.25 | -1.79 | 42.37 | Peak Max | V | 118 | 196 | 80 | -37.63 | Pass
17938.16 | 26.88 | 7.93 | 8.69 | 43.5 | Average Max | H | 104 | 86 | 60 | -16.5 | Pass
15897.38 | 27.11 | 7.8 | 5.86 | 40.77 | Average Max | V | 239 | 93 | 60 | -19.23 | Pass
5899.807 | 27.44 | 4.75 | -0.6 | 31.59 | Average Max | V | 135 | 156 | 60 | -28.41 | Pass
2484.191 | 29.21 | 3 | -3.66 | 28.55 | Average Max | H | 287 | 90 | 60 | -31.45 | Pass
5171.113 | 27.84 | 4.33 | -1.03 | 31.15 | Average Max | V | 142 | 38 | 60 | -28.85 | Pass
2948.423 | 28.11 | 3.25 | -1.79 | 29.57 | Average Max | V | 118 | 196 | 60 | -30.43 | Pass

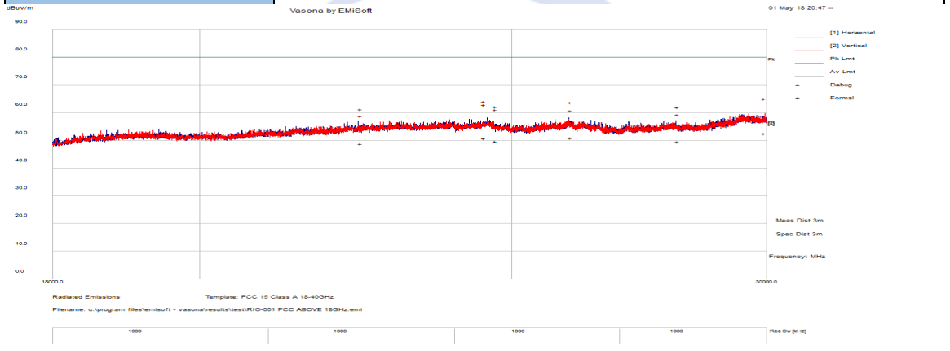
[picture p90: figure]

Page 24 of 27

Test specification: | Radiated Emissions (Above 18GHz)
Environmental Conditions: | Temp(°C): | 25.7 | Result:
| Humidity (%): | 43.3 | | X Pass
| Atmospheric(mbar): | 1014.9
Mains Power: | 120VAC~60Hz
Tested by: | Kushal Shastri | | | Fail
Test Date: | 05/01/2018
Remarks: | 18-30GHz. The testing was done in a 10m chamber.
Frequency (MHz) | Raw (dBuV) | Cable Loss (dB) | AF (dB) | Level (dBuV/m) | Measurement Type | Pol | Hgt (cm) | Azt (Deg) | Limit (dBuV/m) | Margin (dB) | Pass /Fail
29950.07 | 41.46 | 11 | 12.66 | 65.13 | Peak Max | V | 220 | 62 | 80 | -14.87 | Pass
24505.69 | 38.39 | 9.82 | 14.59 | 62.8 | Peak Max | H | 214 | 310 | 80 | -17.2 | Pass
24707.73 | 38.38 | 9.91 | 13.88 | 62.17 | Peak Max | V | 259 | 2 | 80 | -17.83 | Pass
26080.13 | 41.24 | 10.21 | 12.21 | 63.66 | Peak Max | V | 316 | 192 | 80 | -16.34 | Pass
28146.24 | 39.7 | 10.91 | 11.38 | 62 | Peak Max | V | 243 | 235 | 80 | -18 | Pass
22433.19 | 38.56 | 9.37 | 13.33 | 61.26 | Peak Max | V | 103 | 215 | 80 | -18.74 | Pass
29950.07 | 28.87 | 11 | 12.66 | 52.54 | Average Max | V | 220 | 62 | 60 | -7.46 | Pass
24505.69 | 26.44 | 9.82 | 14.59 | 50.85 | Average Max | H | 214 | 310 | 60 | -9.15 | Pass
24707.73 | 25.92 | 9.91 | 13.88 | 49.71 | Average Max | V | 259 | 2 | 60 | -10.29 | Pass
26080.13 | 28.59 | 10.21 | 12.21 | 51.01 | Average Max | V | 316 | 192 | 60 | -8.99 | Pass
28146.24 | 27.24 | 10.91 | 11.38 | 49.54 | Average Max | V | 243 | 235 | 60 | -10.46 | Pass
22433.19 | 26.13 | 9.37 | 13.33 | 48.83 | Average Max | V | 103 | 215 | 60 | -11.17 | Pass

Page 25 of 27

## 13.Annex A | Test instruments and method

Instrument | Model | Serial # | Cal Cycle | Cal Due | In use
| | Conducted Emissions
EMI Test Receiver | ESIB 40 | 100179 | 1 Year | 07/21/2018 | YES
Transient Limiter (9kHz - 100MHz) | EM-7600-5 | 106 | 1 Year | 09/07/2018 | YES
LISN (9kHz - 30MHz) | 3816/2NM | 214372 | 1 Year | 09/27/2018 | YES

Radiated Emissions

50 GHz Spectrum Analyzer | N9030B | MY57140374 | 1 Year | 09/06/2018 | YES
Hybrid Antenna | JB6 | A111717 | 1 Year | 12/05/2018 | YES
Double Ridged Waveguide Horn Antenna (1 - 18 GHz) | 3117 | 218554 | 2 Years | 11/29/2019 | YES
18-40GHz Horn Antenna | SAS-574 | 579 | 1 Year | 08/04/2018 | YES
RF Preamplifier | LPA-6-30 | 11170602 | 1 Year | 08/9/2018 | YES
Pre-Amplifier (1-26.5GHz) | 8449B | 3008A00715 | 1 Year | 8/16/2018 | YES
Pre-Amplifier (18 - 40GHz) | PA-840 | 181251 | 1 Year | 06/23/2018 | YES
5GHz Notch Filter | BRM50705 | 41 | 1 Year | 08/11/2018 | YES
2.4GHz Notch Filter | BRM50702 | G242 | 1 Year | 8/11/2018 | YES

Page 26 of 27

## 14.Annex B | SIEMIC Accreditation

Accreditations | Document | Scope / Remark
ISO 17025 (A2LA) | | Please see the documents for the detailed scope
ISO Guide 65 (A2LA) | | Please see the documents for the detailed scope
TCB Designation | A1, (http://www.siemic.com/Pages/Accreditations/FCC%20TCB%20Designation/Scope%20A1.pdf) A2, (http://www.siemic.com/Pages/Accreditations/FCC%20TCB%20Designation/Scope%20A2.pdf) A3, (http://www.siemic.com/Pages/Accreditations/FCC%20TCB%20Designation/Scope%20A3.pdf) A4, (http://www.siemic.com/Pages/Accreditations/FCC%20TCB%20Designation/Scope%20A4.pdf) B1, (http://www.siemic.com/Pages/Accreditations/FCC%20TCB%20Designation/Scope%20B1.pdf) B2, (http://www.siemic.com/Pages/Accreditations/FCC%20TCB%20Designation/Scope%20B2.pdf) B3, (http://www.siemic.com/Pages/Accreditations/FCC%20TCB%20Designation/Scope%20B3.pdf) B4, (http://www.siemic.com/Pages/Accreditations/FCC%20TCB%20Designation/Scope%20B4.pdf) C
FCC DoC Accreditation | FCC Declaration of Conformity Accreditation
FCC Site Registration | 3-meter site
FCC Site Registration | 10-meter site
IC Site Registration | 3-meter site
IC Site Registration | 10-meter site
EU NB | Radio & Telecommunications Terminal Equipment: EN45001 – EN ISO/IEC 17025
| Electromagnetic Compatibility: EN45001 – EN ISO/IEC 17025
Singapore iDA CB (Certification Body) | Phase I, (http://www.siemic.com/Pages/Accreditations/iDA/SIEMIC%20IDA%20Phase%20I.pdf) Phase II (http://www.siemic.com/Pages/Accreditations/iDA/Final%20recognition%20Letter%20from%20IDA%20for%20Phase%20II%20scope%20update%20request%20for%20SIEMIC,%20Inc.pdf)
Vietnam MIC CAB Accreditation | Please see the document for the detailed scope
Hong Kong OFCA | (Phase II) OFCA Foreign Certification Body for Radio and Telecom
| (Phase I) Conformity Assessment Body for Radio and Telecom
Industry Canada CAB | Radio: Scope A – All Radio Standard Specification in Category I
| Telecom: CS-03 Part I, II, V, VI, VII, VIII
Japan Recognized Certification Body Designation | Radio: A1. Terminal equipment for purpose of calling Telecom: B1. Specified radio equipment specified in Article 38-2, Paragraph 1, Item 1 of the Radio Law
Korea CAB Accreditation | EMI: KCC Notice 2008-39, RRL Notice 2008-3: CA Procedures for EMI KN22: Test Method for EMI EMS: KCC Notice 2008-38, RRL Notice 2008-4: CA Procedures for EM, KN24, KN61000-4-2, -4-3, -4-4, -4-5, -4-6, -4-8, -4-11: Test Method for EMS

Page 27 of 27

Radio: RRL Notice 2008-26, RRL Notice 2008-2, RRL Notice 2008-10,

RRL Notice 2007-49, RRL Notice 2007-20, RRL Notice 2007-21, RRL Notice 2007-80,

RRL Notice 2004-68

Telecom: President Notice 20664, RRL Notice 2007-30, RRL Notice 2008-7 with

attachments 1, 3, 5, 6; President Notice 20664, RRL Notice 2008-7 with attachment 4

Taiwan NCC CAB Recognition | LP0002, PSTN01, ADSL01, ID0002, IS6100, CNS14336, PLMN07, PLMN01, PLMN08
Taiwan BSMI CAB Recognition | CNS 13438
Japan VCCI | R-3083: Radiation 3-meter site C-3421: Main Ports Conducted Interference Measurement T-1597: Telecommunication Ports Conducted Interference Measurement
Australia CAB Recognition | EMC: AS/NZS CISPR 11, AS/NZS CISPR 14.1, AS/NZS CISPR22, AS/NZS 61000.6.3, AS/NZS 61000.6.4

Radio communications: AS/NZS 4281, AS/NZS 4268, AS/NZS 4280.1,

AS/NZS 4280.2, AS/NZS 4295, AS/NZS 4582, AS/NZS 4583, AS/NZS 4769.1,

AS/NZS 4769.2, AS/NZS 4770, AS/NZS 4771

Telecommunications: AS/ACIF S002:05, AS/ACIF S003:06, AS/ACIF S004:06,

AS/ACIF S006:01, AS/ACIF S016:01, AS/ACIF S031:01, AS/ACIF S038:01, AS/ACIF

S040:01, AS/ACIF S041:05, AS/ACIF S043.2:06, AS/ACIF S60950.1

Australia NATA Recognition | AS/ACIF S002, AS/ACIF S003, AS/ACIF S004, AS/ACIF S006, AS/ACIF S016,AS/ACIF S031, AS/ACIF S038, AS/ACIF S040, AS/ACIF S041, AS/ACIF S043.2
