balena-io-hardware/fin-info-doc/documentation/PDF/balenaFin/v1.1/conformity/IEC/IEC-62368-CB-Certificate.pdf

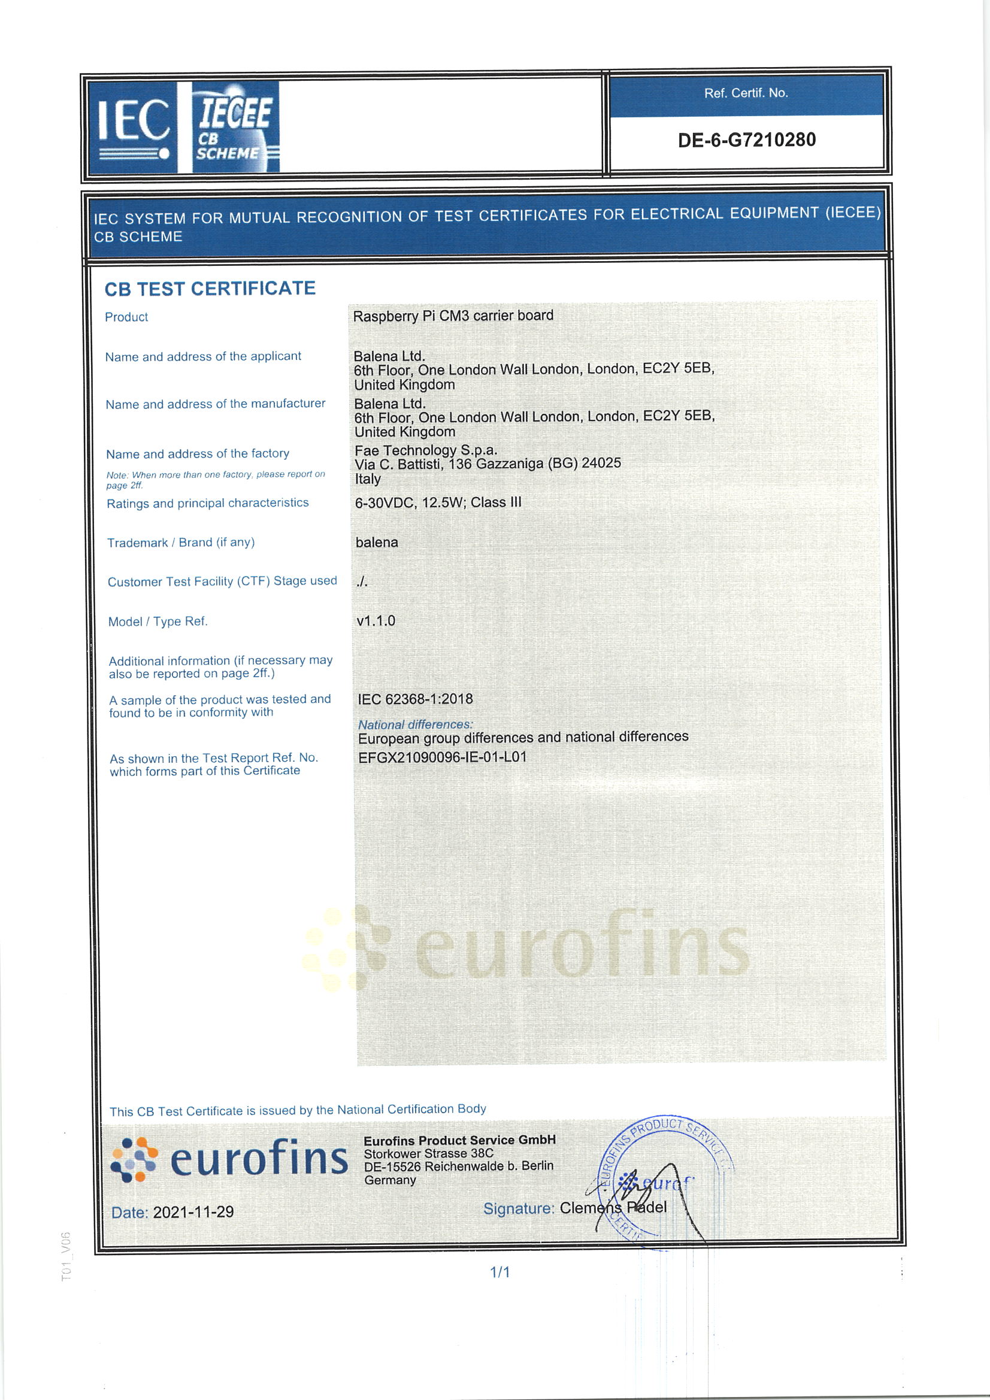
[picture p91: page 1]
