balena-io-hardware/fin-info-doc/documentation/markdown/balenaFin/v1.1/datasheet/pictures/fin_bottom_modem.jpg

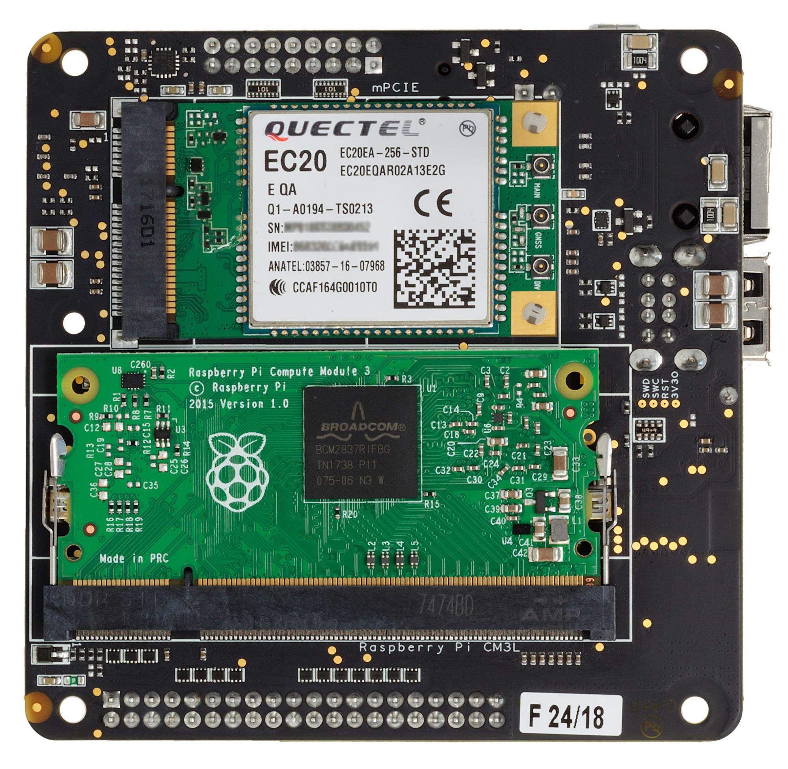
documentation/markdown/balenaFin/v1.1/datasheet/pictures/fin_bottom_modem.jpg
