balena-io-hardware/fin-info-doc/documentation/markdown/balenaFin/v1.1/datasheet/pictures/fin_device_type.png

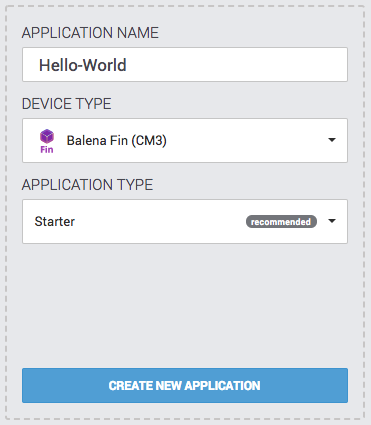
documentation/markdown/balenaFin/v1.1/datasheet/pictures/fin_device_type.png
