balena-io-hardware/fin-info-doc/software/drivers/sd8887/src/wlan/mapp/uaputl/uaputl.h

#define _UAP_H
#define UAP_VERSION         "4.10"
typedef signed char t_s8;
typedef unsigned char t_u8;
typedef signed short t_s16;
typedef unsigned short t_u16;
typedef signed int t_s32;
typedef unsigned int t_u32;
typedef signed long long t_s64;
typedef unsigned long long t_u64;
#if (BYTE_ORDER == LITTLE_ENDIAN)
#undef BIG_ENDIAN_SUPPORT
#endif
#define swap_byte_16(x) \
  ((t_u16)((((t_u16)(x) & 0x00ffU) << 8) | \
         (((t_u16)(x) & 0xff00U) >> 8)))
#define swap_byte_32(x) \
  ((t_u32)((((t_u32)(x) & 0x000000ffUL) << 24) | \
         (((t_u32)(x) & 0x0000ff00UL) <<  8) | \
         (((t_u32)(x) & 0x00ff0000UL) >>  8) | \
         (((t_u32)(x) & 0xff000000UL) >> 24)))
#define swap_byte_64(x) \
  ((t_u64)((t_u64)(((t_u64)(x) & 0x00000000000000ffULL) << 56) | \
         (t_u64)(((t_u64)(x) & 0x000000000000ff00ULL) << 40) | \
         (t_u64)(((t_u64)(x) & 0x0000000000ff0000ULL) << 24) | \
         (t_u64)(((t_u64)(x) & 0x00000000ff000000ULL) <<  8) | \
         (t_u64)(((t_u64)(x) & 0x000000ff00000000ULL) >>  8) | \
         (t_u64)(((t_u64)(x) & 0x0000ff0000000000ULL) >> 24) | \
         (t_u64)(((t_u64)(x) & 0x00ff000000000000ULL) >> 40) | \
         (t_u64)(((t_u64)(x) & 0xff00000000000000ULL) >> 56) ))
#ifdef BIG_ENDIAN_SUPPORT
#define uap_le16_to_cpu(x) swap_byte_16(x)
#define uap_le32_to_cpu(x) swap_byte_32(x)
#define uap_le64_to_cpu(x) swap_byte_64(x)
#define uap_cpu_to_le16(x) swap_byte_16(x)
#define uap_cpu_to_le32(x) swap_byte_32(x)
#define uap_cpu_to_le64(x) swap_byte_64(x)
#define endian_convert_request_header(x)                \
    {                                                   \
        (x)->cmd_code = uap_cpu_to_le16((x)->cmd_code);   \
        (x)->size = uap_cpu_to_le16((x)->size);         \
        (x)->seq_num = uap_cpu_to_le16((x)->seq_num);     \
        (x)->result = uap_cpu_to_le16((x)->result);     \
    }
#define endian_convert_response_header(x)               \
    {                                                   \
        (x)->cmd_code = uap_le16_to_cpu((x)->cmd_code);   \
        (x)->size = uap_le16_to_cpu((x)->size);         \
        (x)->seq_num = uap_le16_to_cpu((x)->seq_num);     \
        (x)->result = uap_le16_to_cpu((x)->result);     \
    }
#define endian_convert_tlv_header_out(x)            \
    {                                               \
        (x)->tag = uap_cpu_to_le16((x)->tag);       \
        (x)->length = uap_cpu_to_le16((x)->length); \
    }
#define endian_convert_tlv_header_in(x)             \
    {                                               \
        (x)->tag = uap_le16_to_cpu((x)->tag);       \
        (x)->length = uap_le16_to_cpu((x)->length); \
    }
#else
#define uap_le16_to_cpu(x) x
#define uap_le32_to_cpu(x) x
#define uap_le64_to_cpu(x) x
#define uap_cpu_to_le16(x) x
#define uap_cpu_to_le32(x) x
#define uap_cpu_to_le64(x) x
#define endian_convert_request_header(x)
#define endian_convert_response_header(x)
#define endian_convert_tlv_header_out(x)
#define endian_convert_tlv_header_in(x)
#endif
#define MRVLPRIVCMD          (SIOCDEVPRIVATE + 14)
#define UAP_IOCTL_CMD		(SIOCDEVPRIVATE + 2)
#define UAP_ADDBA_PARA          0
#define UAP_AGGR_PRIOTBL    1
#define UAP_ADDBA_REJECT    2
#define UAP_FW_INFO         4
#define UAP_DEEP_SLEEP      3
#define UAP_TX_DATA_PAUSE    5
#define UAP_SDCMD52_RW      6
#define UAP_SNMP_MIB        7
#define UAP_DOMAIN_INFO     8
#if defined(DFS_TESTING_SUPPORT)
#define UAP_DFS_TESTING     10
#endif
#define UAP_TX_BF_CFG       9
#define UAP_HS_CFG          11
#define UAP_HS_SET_PARA     12
#define UAP_MGMT_FRAME_CONTROL  13
#define UAP_TX_RATE_CFG      14
#define UAP_CAC_TIMER_STATUS	17
#define UAP_HT_TX_CFG           19
#define UAP_VHT_CFG             20
#define UAP_OPERATION_CTRL       22
#define UAP_CHAN_SWITCH_COUNT_CFG     23
#define UAP_POWER_MODE      (SIOCDEVPRIVATE + 3)
#define UAP_BSS_CTRL        (SIOCDEVPRIVATE + 4)
#define UAP_BSS_START               0
#define UAP_BSS_STOP                1
#define UAP_BSS_RESET               2
#define	UAP_RADIO_CTL       (SIOCDEVPRIVATE + 5)
#define UAP_BSS_CONFIG      (SIOCDEVPRIVATE + 6)
#define	UAP_STA_DEAUTH	    (SIOCDEVPRIVATE + 7)
#define UAPHOSTPKTINJECT    (SIOCDEVPRIVATE + 12)
#define UAP_GET_STA_LIST    (SIOCDEVPRIVATE + 11)
#define UAP_CUSTOM_IE       (SIOCDEVPRIVATE + 13)
#define MAX_MGMT_IE_INDEX       12
#define HS_CFG_FLAG_GET         0
#define HS_CFG_FLAG_SET         1
#define HS_CFG_FLAG_CONDITION   2
#define HS_CFG_FLAG_GPIO        4
#define HS_CFG_FLAG_GAP         8
#define HS_CFG_FLAG_ALL         0x0f
#define HS_CFG_CONDITION_MASK   0x4f
#define HS_CFG_CANCEL   0xffffffff
typedef struct _ds_hs_cfg {
	t_u32 subcmd;
	t_u32 flags;
	t_u32 conditions;
	t_u32 gpio;
	t_u32 gap;
} ds_hs_cfg;
typedef struct _ps_sleep_param {
	t_u32 ctrl_bitmap;
	t_u32 min_sleep;
	t_u32 max_sleep;
} ps_sleep_param;
typedef struct _inact_sleep_param {
	t_u32 inactivity_to;
	t_u32 min_awake;
	t_u32 max_awake;
} inact_sleep_param;
#define PS_FLAG_PS_MODE                 1
#define PS_FLAG_SLEEP_PARAM             2
#define PS_FLAG_INACT_SLEEP_PARAM       4
#define PS_MODE_DISABLE                      0
#define PS_MODE_PERIODIC_DTIM                1
#define PS_MODE_INACTIVITY                   2
#define SLEEP_PARAMETER                     1
#define INACTIVITY_SLEEP_PARAMETER          2
#define PS_SLEEP_PARAM_MIN                  5000
#define PS_SLEEP_PARAM_MAX                  32000
#define PS_AWAKE_PERIOD_MIN                 2000
typedef struct _ps_mgmt {
	t_u16 flags;
	t_u16 ps_mode;
	ps_sleep_param sleep_param;
	inact_sleep_param inact_param;
} ps_mgmt;
typedef struct _addba_param {
	t_u32 subcmd;
	t_u32 action;
	t_u32 timeout;
	t_u32 txwinsize;
	t_u32 rxwinsize;
	t_u8 txamsdu;
	t_u8 rxamsdu;
} addba_param;
#define DEFAULT_BLOCK_ACK_TIMEOUT   0xFFFF
#define MAX_TXRX_WINDOW_SIZE        0x3FF
#define MAX_NUM_TID     8
typedef struct _aggr_prio_tbl {
	t_u32 subcmd;
	t_u32 action;
	t_u8 ampdu[MAX_NUM_TID];
	t_u8 amsdu[MAX_NUM_TID];
} aggr_prio_tbl;
typedef struct _addba_reject_para {
	t_u32 subcmd;
	t_u32 action;
	t_u8 addba_reject[MAX_NUM_TID];
} addba_reject_para;
typedef struct _fw_info {
	t_u32 subcmd;
	t_u32 action;
	t_u32 fw_release_number;
	t_u8 hw_dev_mcs_support;
	t_u8 fw_bands;
	t_u16 region_code;
	t_u32 hw_dot_11n_dev_cap;
} fw_info;
#define ETH_ALEN    6
#define BF_GLOBAL_CONFIGURATION     0x00
#define TRIGGER_SOUNDING_FOR_PEER   0x01
#define SET_GET_BF_PERIODICITY      0x02
#define TX_BF_FOR_PEER_ENBL         0x03
#define SET_SNR_THR_PEER            0x04
#define MAX_PEER_MAC_TUPLES         10
typedef struct _bf_global_cfg_args {
	t_u8 bf_enbl;
	t_u8 sounding_enbl;
	t_u8 fb_type;
	t_u8 snr_threshold;
	t_u16 sounding_interval;
	t_u8 bf_mode;
	t_u8 reserved;
} bf_global_cfg_args;
typedef struct _trigger_sound_args {
	t_u8 peer_mac[ETH_ALEN];
	t_u8 status;
} trigger_sound_args;
typedef struct _bf_periodicity_args {
	t_u8 peer_mac[ETH_ALEN];
	t_u16 interval;
	t_u8 status;
} bf_periodicity_args;
typedef struct _tx_bf_peer_args {
	t_u8 peer_mac[ETH_ALEN];
	t_u16 reserved;
	t_u8 bf_enbl;
	t_u8 sounding_enbl;
	t_u8 fb_type;
} tx_bf_peer_args;
typedef struct _snr_thr_args {
	t_u8 peer_mac[ETH_ALEN];
	t_u8 snr;
} snr_thr_args;
typedef struct _tx_bf_cfg_para {
	t_u32 subcmd;
	t_u32 action;
	t_u16 bf_action;
	t_u16 bf_cmd_action;
	t_u32 no_of_peers;
	union {
		bf_global_cfg_args bf_global_cfg;
		trigger_sound_args bf_sound[MAX_PEER_MAC_TUPLES];
		bf_periodicity_args bf_periodicity[MAX_PEER_MAC_TUPLES];
		tx_bf_peer_args tx_bf_peer[MAX_PEER_MAC_TUPLES];
		snr_thr_args bf_snr[MAX_PEER_MAC_TUPLES];
	} body;
} tx_bf_cfg_para;
typedef struct _deep_sleep_para {
	t_u32 subcmd;
	t_u32 action;
	t_u16 deep_sleep;
	t_u16 idle_time;
} deep_sleep_para;
#define DEEP_SLEEP_IDLE_TIME	100
typedef struct _tx_data_pause_para {
	t_u32 subcmd;
	t_u32 action;
	t_u16 txpause;
	t_u16 txbufcnt;
} tx_data_pause_para;
#define TX_DATA_PAUSE_DISABLE   0
#define TX_DATA_PAUSE_ENABLE    1
#define MAX_TX_BUF_CNT	        2
typedef struct _snmp_mib_param {
	t_u32 subcmd;
	t_u32 action;
	t_u16 oid;
	t_u16 oid_val_len;
	t_u8 oid_value[0];
} snmp_mib_param;
typedef struct _domain_info_param {
	t_u32 subcmd;
	t_u32 action;
	t_u8 tlv[0];
} domain_info_param;
#if defined(DFS_TESTING_SUPPORT)
typedef struct _dfs_testing_param {
	t_u32 subcmd;
	t_u32 action;
	t_u32 usr_cac_period;
	t_u16 usr_nop_period;
	t_u8 no_chan_change;
	t_u8 fixed_new_chan;
} dfs_testing_para;
#endif
typedef struct _cscount_cfg_t {
	t_u32 subcmd;
	t_u32 action;
	t_u8 cs_count;
} cscount_cfg_t;
typedef struct _mgmt_frame_ctrl {
	t_u32 subcmd;
	t_u32 action;
	t_u32 mask;
} mgmt_frame_ctrl;
typedef struct _cac_timer_status {
	t_u32 subcmd;
	t_u32 action;
	t_u32 mode;
} cac_timer_status;
typedef struct _ht_tx_cfg {
	t_u16 httxcap;
	t_u16 httxinfo;
} ht_tx_cfg;
typedef struct _ht_tx_cfg_para {
	t_u32 subcmd;
	t_u32 action;
	ht_tx_cfg tx_cfg;
} ht_tx_cfg_para;
#define DEFAULT_DEV_NAME    "uap0"
#define UAP_SUCCESS     1
#define UAP_FAILURE     0
#define UAP_RET_MAC_BROADCAST   0x1FF
#define UAP_RET_MAC_MULTICAST   0x1FE
#define CMD_SUCCESS     0
#define CMD_FAILURE     -1
#define BSS_FAILURE_START_INVAL     2
#define MAX_LINE_LENGTH         240
#define MAX_CMD_LENGTH          100
#define MRVDRV_SIZE_OF_CMD_BUFFER       (2 * 1024)
#define MAX_NUM_CLIENTS         MAX_STA_COUNT
#define MAX_MAC_ONESHOT_FILTER  16
#define MAX_SSID_LENGTH         32
#define MIN_SSID_LENGTH         1
#define MAX_WPA_PASSPHRASE_LENGTH   64
#define MIN_WPA_PASSPHRASE_LENGTH   8
#define MAX_DATA_RATES          14
#define MAX_CONFIG_LINE         240
#define BASIC_RATE_SET_BIT      0x80
#define MAX_GRP_TIMER           86400
#define MAX_RETRY_LIMIT         254
#define MAX_PREAMBLE_TYPE       2
#define MAX_TX_POWER    30
#define MIN_TX_POWER    0
#define MAX_CHANNELS_BG 14
#define MAX_CHANNELS    165
#define DEFAULT_MAX_VALID_CHANNEL_BG 11
#define MAX_STA_COUNT   10
#define MAX_RTS_THRESHOLD   2347
#define MAX_FRAG_THRESHOLD 2346
#define MIN_FRAG_THRESHOLD 256
#define MAX_STAGE_OUT_TIME  864000
#define MIN_STAGE_OUT_TIME  50
#define MAX_DTIM_PERIOD 100
#define MAX_BEACON_PERIOD 4000
#define MIN_BEACON_PERIOD 50
#define MAX_IE_BUFFER_LEN 256
#define MAX_CUSTOM_IE_COUNT 4
#define MAX_RATES               12
#define DEFAULT_WAIT_TIME       3
#define MAX_DEAUTH_REASON_CODE     0xFFFF
#ifdef __GNUC__
#define PACK_START
#define PACK_END  __attribute__ ((packed))
#else
#define PACK_START   __packed
#define PACK_END
#endif
#define ACTION_GET  0
#define ACTION_SET  1
#define A2HEXDECIMAL(num)  \
    (strncasecmp("0x", (num), 2)?(unsigned int) strtoll((num),NULL,0):a2hex((num)))\
#define IS_HEX_OR_DIGIT(num) \
    (strncasecmp("0x", (num), 2)?ISDIGIT((num)):ishexstring((num)))\
#define MIN(a, b) ((a) < (b) ? (a) : (b))
typedef enum {
	RDEEPROM,
	SCANCHANNELS,
	TXPOWER,
	PROTOCOL,
	CHANNEL,
	CHANNEL_EXT,
	BAND,
	RATE,
	BROADCASTSSID,
	RTSTHRESH,
	FRAGTHRESH,
	DTIMPERIOD,
	RADIOCONTROL,
	TXBEACONRATE,
	MCBCDATARATE,
	PKTFWD,
	STAAGEOUTTIMER,
	PSSTAAGEOUTTIMER,
	AUTHMODE,
	GROUPREKEYTIMER,
	MAXSTANUM,
	BEACONPERIOD,
	RETRYLIMIT,
	STICKYTIMCONFIG,
	STICKYTIMSTAMACADDR,
	COEX2040CONFIG,
	TXRATECFG,
	RSNREPLAYPROT,
	PREAMBLETYPE,
	EAPOL_PWK_HSK,
	EAPOL_GWK_HSK,
	COEX_COMM_BITMAP,
	COEX_COMM_AP_COEX,
	COEX_PROTECTION,
	COEX_SCO_ACL_FREQ,
	COEX_ACL_ENABLED,
	COEX_ACL_BT_TIME,
	COEX_ACL_WLAN_TIME,
	PWK_CIPHER,
	GWK_CIPHER,
	RESTRICT_CLIENT_MODE,
	AKM_SUITE,
	WACPMODE
} valid_inputs;
enum { MSG_NONE, MSG_DEBUG, MSG_ALL };
typedef struct {
	t_u16 type;
	t_u16 len;
	char *name;
} oids_table;
#define CMD_NXP         "MRVL_CMD"
#define PRIV_CMD_HOSTCMD    "hostcmd"
#define BUF_HEADER_SIZE     4
#define TLVHEADER_LEN       4
#define APCMDHEADER              \
                        t_u32 buf_size;         \
                             \
                        t_u16 cmd_code;         \
                                     \
                        t_u16 size;             \
                          \
                        t_u16 seq_num;          \
                                   \
                        t_s16 result
#define TLVHEADER             \
                        t_u16 tag;      \
                           \
                        t_u16 length
typedef PACK_START struct _tlvbuf_header {
	t_u16 type;
	t_u16 len;
	t_u8 data[0];
} PACK_END tlvbuf_header;
#define BITMAP_ACS_MODE         0x01
#define BAND_SELECT_BOTH        0
#define BAND_SELECT_BG          1
#define BAND_SELECT_A           2
#define BITMAP_CHANNEL_ABOVE    0x02
#define BITMAP_CHANNEL_BELOW    0x04
#define CHANNEL_MODE_MASK       0x07
#define MAX_CHANNEL_ABOVE       9
#define DEFAULT_MAX_CHANNEL_ABOVE       7
#define MIN_CHANNEL_BELOW       5
#define DEFAULT_MAX_CHANNEL_ABOVE_NON_US       9
#define DEFAULT_MAX_CHANNEL_BELOW       11
#define DEFAULT_MAX_CHANNEL_BELOW_NON_US       13
enum {
	BAND_2GHZ = 0,
	BAND_5GHZ = 1,
	BAND_4GHZ = 2,
};
enum {
	SEC_CHAN_NONE = 0,
	SEC_CHAN_ABOVE = 1,
	SEC_CHAN_5MHZ = 2,
	SEC_CHAN_BELOW = 3
};
enum {
	CHAN_BW_20MHZ = 0,
	CHAN_BW_10MHZ,
	CHAN_BW_40MHZ,
	CHAN_BW_80MHZ,
};
enum {
	SCAN_MODE_MANUAL = 0,
	SCAN_MODE_ACS,
	SCAN_MODE_USER,
};
typedef PACK_START struct _Band_Config_t {
#ifdef BIG_ENDIAN_SUPPORT
	t_u8 scanMode:2;
	t_u8 chan2Offset:2;
	t_u8 chanWidth:2;
	t_u8 chanBand:2;
#else
	t_u8 chanBand:2;
	t_u8 chanWidth:2;
	t_u8 chan2Offset:2;
	t_u8 scanMode:2;
#endif
} PACK_END Band_Config_t;
typedef PACK_START struct _tlvbuf_channel_config {
	TLVHEADER;
	Band_Config_t bandcfg;
	t_u8 chan_number;
} PACK_END tlvbuf_channel_config;
typedef PACK_START struct _channel_list {
	Band_Config_t bandcfg;
	t_u8 chan_number;
	t_u8 reserved1;
	t_u16 reserved2;
	t_u16 reserved3;
} PACK_END channel_list;
typedef PACK_START struct _tlvbuf_channel_list {
	TLVHEADER;
	channel_list chan_list[0];
} PACK_END tlvbuf_channel_list;
typedef PACK_START struct _tlvbuf_tdls_ext_cap {
	TLVHEADER;
	t_u8 ext_cap[0];
} PACK_END tlvbuf_tdls_ext_cap;
typedef PACK_START struct _tlvbuf_ap_mac_address {
	TLVHEADER;
	t_u8 ap_mac_addr[ETH_ALEN];
} PACK_END tlvbuf_ap_mac_address;
typedef PACK_START struct _tlvbuf_ssid {
	TLVHEADER;
	t_u8 ssid[0];
} PACK_END tlvbuf_ssid;
typedef PACK_START struct _tlvbuf_beacon_period {
	TLVHEADER;
	t_u16 beacon_period_ms;
} PACK_END tlvbuf_beacon_period;
typedef PACK_START struct _tlvbuf_dtim_period {
	TLVHEADER;
	t_u8 dtim_period;
} PACK_END tlvbuf_dtim_period;
typedef PACK_START struct _tlvbuf_bss_status {
	TLVHEADER;
	t_u16 bss_status;
} PACK_END tlvbuf_bss_status;
typedef PACK_START struct _tlvbuf_phyparamdsset {
	TLVHEADER;
	t_u8 channel;
} PACK_END tlvbuf_phyparamdsset;
typedef PACK_START struct _tlvbuf_rates {
	TLVHEADER;
	t_u8 operational_rates[0];
} PACK_END tlvbuf_rates;
typedef PACK_START struct _tlvbuf_tx_power {
	TLVHEADER;
	t_u8 tx_power_dbm;
} PACK_END tlvbuf_tx_power;
typedef PACK_START struct _tlvbuf_bcast_ssid_ctl {
	TLVHEADER;
	t_u8 bcast_ssid_ctl;
} PACK_END tlvbuf_bcast_ssid_ctl;
typedef PACK_START struct _tlvbuf_rsn_replay_prot {
	TLVHEADER;
	t_u8 rsn_replay_prot;
} PACK_END tlvbuf_rsn_replay_prot;
typedef PACK_START struct _tlvbuf_preamble_ctl {
	TLVHEADER;
	t_u8 preamble_type;
} PACK_END tlvbuf_preamble_ctl;
typedef PACK_START struct _tlvbuf_antenna_ctl {
	TLVHEADER;
	t_u8 which_antenna;
	t_u8 antenna_mode;
} PACK_END tlvbuf_antenna_ctl;
typedef PACK_START struct _tlvbuf_rts_threshold {
	TLVHEADER;
	t_u16 rts_threshold;
} PACK_END tlvbuf_rts_threshold;
typedef PACK_START struct _tlvbuf_tx_data_rate {
	TLVHEADER;
	t_u16 tx_data_rate;
} PACK_END tlvbuf_tx_data_rate;
typedef PACK_START struct _tlvbuf_mcbc_data_rate {
	TLVHEADER;
	t_u16 mcbc_datarate;
} PACK_END tlvbuf_mcbc_data_rate;
#define PKT_FWD_FW_BIT  0x01
#define PKT_FWD_INTRA_BCAST 0x02
#define PKT_FWD_INTRA_UCAST 0x04
#define PKT_FWD_INTER_UCAST 0x08
typedef PACK_START struct _tlvbuf_pkt_fwd_ctl {
	TLVHEADER;
	t_u8 pkt_fwd_ctl;
} PACK_END tlvbuf_pkt_fwd_ctl;
typedef struct _sdcmd52_para {
	t_u32 subcmd;
	t_u32 action;
	t_u8 cmd52_params[3];
} sdcmd52_para;
typedef PACK_START struct _tlvbuf_sta_mac_addr_filter {
	TLVHEADER;
	t_u8 filter_mode;
	t_u8 count;
	t_u8 mac_address[0];
} PACK_END tlvbuf_sta_mac_addr_filter;
typedef PACK_START struct _tlvbuf_sta_ageout_timer {
	TLVHEADER;
	t_u32 sta_ageout_timer_ms;
} PACK_END tlvbuf_sta_ageout_timer;
typedef PACK_START struct _tlvbuf_ps_sta_ageout_timer {
	TLVHEADER;
	t_u32 ps_sta_ageout_timer_ms;
} PACK_END tlvbuf_ps_sta_ageout_timer;
typedef PACK_START struct _tlvbuf_max_sta_num {
	TLVHEADER;
	t_u16 max_sta_num_configured;
	t_u16 max_sta_num_supported;
} PACK_END tlvbuf_max_sta_num;
typedef PACK_START struct _tlvbuf_retry_limit {
	TLVHEADER;
	t_u8 retry_limit;
} PACK_END tlvbuf_retry_limit;
typedef PACK_START struct _tlvbuf_sticky_tim_config {
	TLVHEADER;
	t_u16 enable;
	t_u16 duration;
	t_u16 sticky_bitmask;
} PACK_END tlvbuf_sticky_tim_config;
typedef PACK_START struct _tlvbuf_sticky_tim_sta_mac_addr {
	TLVHEADER;
	t_u16 control;
	t_u8 sta_mac_address[ETH_ALEN];
} PACK_END tlvbuf_sticky_tim_sta_mac_addr;
typedef PACK_START struct _tlvbuf_2040_coex {
	TLVHEADER;
	t_u8 enable;
} PACK_END tlvbuf_2040_coex;
typedef PACK_START struct _tlvbuf_eapol_pwk_hsk_timeout {
	TLVHEADER;
	t_u32 pairwise_update_timeout;
} PACK_END tlvbuf_eapol_pwk_hsk_timeout;
typedef PACK_START struct _tlvbuf_eapol_pwk_hsk_retries {
	TLVHEADER;
	t_u32 pwk_retries;
} PACK_END tlvbuf_eapol_pwk_hsk_retries;
typedef PACK_START struct _tlvbuf_eapol_gwk_hsk_timeout {
	TLVHEADER;
	t_u32 groupwise_update_timeout;
} PACK_END tlvbuf_eapol_gwk_hsk_timeout;
typedef PACK_START struct _tlvbuf_eapol_gwk_hsk_retries {
	TLVHEADER;
	t_u32 gwk_retries;
} PACK_END tlvbuf_eapol_gwk_hsk_retries;
typedef PACK_START struct _custom_ie {
	t_u16 ie_index;
	t_u16 mgmt_subtype_mask;
	t_u16 ie_length;
	t_u8 ie_buffer[0];
} PACK_END custom_ie;
typedef PACK_START struct _tlvbuf_custom_ie {
	TLVHEADER;
	custom_ie ie_data[0];
} PACK_END tlvbuf_custom_ie;
typedef PACK_START struct _custom_ie_info {
	t_u16 buf_size;
	t_u16 buf_count;
} PACK_END custom_ie_info;
typedef PACK_START struct _tlvbuf_max_mgmt_ie {
	TLVHEADER;
	t_u16 count;
	custom_ie_info info[0];
} PACK_END tlvbuf_max_mgmt_ie;
#define PROTOCOL_NO_SECURITY        1
#define PROTOCOL_STATIC_WEP         2
#define PROTOCOL_WPA                8
#define PROTOCOL_WPA2               32
#define PROTOCOL_WPA2_MIXED         40
#define CIPHER_NONE                 0
#define CIPHER_WEP_40               1
#define CIPHER_WEP_104              2
#define CIPHER_TKIP                 4
#define CIPHER_AES_CCMP             8
#define CIPHER_BITMAP               0x0c
#define PROTOCOL_BITMAP             0x3E8
#define AES_CCMP_TKIP               12
typedef PACK_START struct _tlvbuf_auth_mode {
	TLVHEADER;
	t_u8 auth_mode;
} PACK_END tlvbuf_auth_mode;
typedef PACK_START struct _tlvbuf_protocol {
	TLVHEADER;
	t_u16 protocol;
} PACK_END tlvbuf_protocol;
typedef PACK_START struct _tlvbuf_cipher {
	TLVHEADER;
	t_u8 pairwise_cipher;
	t_u8 group_cipher;
} PACK_END tlvbuf_cipher;
typedef PACK_START struct _tlvbuf_pwk_cipher {
	TLVHEADER;
	t_u16 protocol;
	t_u8 pairwise_cipher;
	t_u8 reserved;
} PACK_END tlvbuf_pwk_cipher;
typedef PACK_START struct _tlvbuf_gwk_cipher {
	TLVHEADER;
	t_u8 group_cipher;
	t_u8 reserved;
} PACK_END tlvbuf_gwk_cipher;
typedef PACK_START struct _tlvbuf_group_rekey_timer {
	TLVHEADER;
	t_u32 group_rekey_time_sec;
} PACK_END tlvbuf_group_rekey_timer;
#define KEY_MGMT_NONE   0x04
#define KEY_MGMT_PSK    0x02
#define KEY_MGMT_EAP     0x01
#define KEY_MGMT_PSK_SHA256  0X100
#define MAX_AC_QUEUES   4
typedef PACK_START struct _tlvbuf_akmp {
	TLVHEADER;
	t_u16 key_mgmt;
	t_u16 key_mgmt_operation;
} PACK_END tlvbuf_akmp;
typedef PACK_START struct _tlvbuf_wep_key {
	TLVHEADER;
	t_u8 key_index;
	t_u8 is_default;
	t_u8 key[0];
} PACK_END tlvbuf_wep_key;
typedef PACK_START struct _tlvbuf_wpa_passphrase {
	TLVHEADER;
	t_u8 passphrase[0];
} PACK_END tlvbuf_wpa_passphrase;
typedef PACK_START struct _tlvbuf_frag_threshold {
	TLVHEADER;
	t_u16 frag_threshold;
} PACK_END tlvbuf_frag_threshold;
typedef PACK_START struct _mrvl_priv_cmd {
	t_u8 *buf;
	t_u32 used_len;
	t_u32 total_len;
} PACK_END mrvl_priv_cmd;
typedef PACK_START struct _apcmdbuf {
	APCMDHEADER;
} PACK_END apcmdbuf;
#define APCMDHEADERLEN  (sizeof(apcmdbuf))
typedef PACK_START struct _apcmdbuf_sys_info_request {
	APCMDHEADER;
} PACK_END apcmdbuf_sys_info_request;
typedef PACK_START struct _apcmdbuf_sys_info_response {
	APCMDHEADER;
	t_u8 sys_info[64];
} PACK_END apcmdbuf_sys_info_response;
typedef PACK_START struct _apcmdbuf_sys_reset {
	APCMDHEADER;
} PACK_END apcmdbuf_sys_reset;
typedef PACK_START struct _apcmdbuf_sys_configure {
	APCMDHEADER;
	t_u16 action;
} PACK_END apcmdbuf_sys_configure;
#define MAX_TX_PWR_INDOOR    17
typedef PACK_START struct _apcmdbuf_snmp_mib {
	APCMDHEADER;
	t_u16 action;
} PACK_END apcmdbuf_snmp_mib;
typedef PACK_START struct _apcmdbuf_bss_start {
	APCMDHEADER;
} PACK_END apcmdbuf_bss_start;
typedef PACK_START struct _apcmdbuf_bss_stop {
	APCMDHEADER;
} PACK_END apcmdbuf_bss_stop;
typedef PACK_START struct _APCMDBUF_STA_DEAUTH {
	APCMDHEADER;
	t_u8 sta_mac_address[ETH_ALEN];
} PACK_END APCMDBUF_STA_DEAUTH;
enum reg_commands {
	CMD_MAC = 1,
	CMD_BBP,
	CMD_RF
};
typedef PACK_START struct _apcmdbuf_reg_rdwr {
	APCMDHEADER;
	t_u16 action;
	t_u16 offset;
	t_u32 value;
} PACK_END apcmdbuf_reg_rdwr;
enum {
	DOMAIN_CODE_FCC = 0x01,
	DOMAIN_CODE_ETSI,
	DOMAIN_CODE_MKK,
	DOMAIN_CODE_IN,
	DOMAIN_CODE_MY,
};
typedef PACK_START struct _rgn_dom_code {
	TLVHEADER;
	t_u8 domain_code;
	t_u8 reserved;
} PACK_END rgn_dom_code_t;
typedef PACK_START struct _ieeetypes_subband_set {
	t_u8 first_chan;
	t_u8 no_of_chan;
	t_u8 max_tx_pwr;
} PACK_END ieeetypes_subband_set_t;
#define COUNTRY_CODE_LEN    3
#define MAX_SUB_BANDS 40
#define MAX_MULTI_DOMAIN_CAPABILITY_ENTRY_G 1
#define MAX_MULTI_DOMAIN_CAPABILITY_ENTRY_A 31
typedef PACK_START struct domain_param {
	TLVHEADER;
	t_u8 country_code[COUNTRY_CODE_LEN];
	ieeetypes_subband_set_t subband[0];
} PACK_END domain_param_t;
typedef PACK_START struct _apcmdbuf_cfg_80211d {
	APCMDHEADER;
	t_u16 action;
	domain_param_t domain;
} PACK_END apcmdbuf_cfg_80211d;
typedef PACK_START struct _apcmdbuf_mem_access {
	APCMDHEADER;
	t_u16 action;
	t_u16 reserved;
	t_u32 address;
	t_u32 value;
} PACK_END apcmdbuf_mem_access;
typedef PACK_START struct _apcmdbuf_eeprom_access {
	APCMDHEADER;
	t_u16 action;
	t_u16 offset;
	t_u16 byte_count;
	t_u8 value[1];
} PACK_END apcmdbuf_eeprom_access;
typedef PACK_START struct _tlvbuf_coex_common_cfg {
	TLVHEADER;
	t_u32 config_bitmap;
	t_u32 ap_bt_coex;
	t_u32 reserved[3];
} PACK_END tlvbuf_coex_common_cfg;
typedef PACK_START struct _tlvbuf_coex_sco_cfg {
	TLVHEADER;
	t_u16 protection_qtime[4];
	t_u16 protection_rate;
	t_u16 acl_frequency;
	t_u32 reserved[4];
} PACK_END tlvbuf_coex_sco_cfg;
typedef PACK_START struct _tlvbuf_coex_acl_cfg {
	TLVHEADER;
	t_u16 enabled;
	t_u16 bt_time;
	t_u16 wlan_time;
	t_u16 protection_rate;
	t_u32 reserved[4];
} PACK_END tlvbuf_coex_acl_cfg;
typedef PACK_START struct _tlvbuf_coex_stats {
	TLVHEADER;
	t_u32 null_not_sent;
	t_u32 null_queued;
	t_u32 null_not_queued;
	t_u32 cf_end_queued;
	t_u32 cf_end_not_queued;
	t_u32 null_alloc_fail;
	t_u32 cf_end_alloc_fail;
	t_u32 reserved[8];
} PACK_END tlvbuf_coex_stats;
typedef PACK_START struct _apcmdbuf_coex_config {
	APCMDHEADER;
	t_u16 action;
	t_u16 coex_reserved;
	t_u8 tlv_buffer[0];
} PACK_END apcmdbuf_coex_config;
#define MBIT(x)    (((t_u32)1) << (x))
#define IS_CHANNEL_WIDTH_40(Field2) (Field2 & MBIT(2))
#define GET_SECONDARY_CHAN(Field2) (Field2 & (MBIT(0) | MBIT(1)))
#define IS_RIFS_ALLOWED(Field2) (Field2 & MBIT(3))
#define GET_HT_PROTECTION(Field3) (Field3 & (MBIT(0) | MBIT(1)))
#define NONGF_STA_PRESENT(Field3) (Field3 & MBIT(2))
#define OBSS_NONHT_STA_PRESENT(Field3) (Field3 & MBIT(4))
typedef struct PACK_START _HTCap_t {
	t_u16 ht_cap_info;
	t_u8 ampdu_param;
	t_u8 supported_mcs_set[16];
	t_u16 ht_ext_cap;
	t_u32 tx_bf_cap;
	t_u8 asel;
} PACK_END HTCap_t, *pHTCap_t;
typedef struct PACK_START _HTInfo_t {
	t_u8 pri_chan;
	t_u8 field2;
	t_u16 field3;
	t_u16 field4;
	t_u8 basic_mcs_set[16];
} PACK_END HTInfo_t, *pHTInfo_t;
typedef t_u8 mlan_802_11_mac_addr[ETH_ALEN];
typedef struct _mlan_802_11_ssid {
	t_u32 ssid_len;
	t_u8 ssid[MAX_SSID_LENGTH];
} mlan_802_11_ssid;
typedef struct _scan_chan_list {
	t_u8 chan_number;
	Band_Config_t bandcfg;
} scan_chan_list;
typedef struct _mac_filter {
	t_u16 filter_mode;
	t_u16 mac_count;
	mlan_802_11_mac_addr mac_list[MAX_MAC_ONESHOT_FILTER];
} mac_filter;
typedef PACK_START struct _IEEEtypes_WmmAciAifsn_t {
#ifdef BIG_ENDIAN_SUPPORT
	t_u8 reserved:1;
	t_u8 aci:2;
	t_u8 acm:1;
	t_u8 aifsn:4;
#else
	t_u8 aifsn:4;
	t_u8 acm:1;
	t_u8 aci:2;
	t_u8 reserved:1;
#endif
} PACK_END IEEEtypes_WmmAciAifsn_t, *pIEEEtypes_WmmAciAifsn_t;
typedef PACK_START struct _IEEEtypes_WmmEcw_t {
#ifdef BIG_ENDIAN_SUPPORT
	t_u8 ecw_max:4;
	t_u8 ecw_min:4;
#else
	t_u8 ecw_min:4;
	t_u8 ecw_max:4;
#endif
} PACK_END IEEEtypes_WmmEcw_t, *pIEEEtypes_WmmEcw_t;
typedef PACK_START struct _IEEEtypes_WmmAcParameters_t {
	IEEEtypes_WmmAciAifsn_t aci_aifsn;
	IEEEtypes_WmmEcw_t ecw;
	t_u16 tx_op_limit;
} PACK_END IEEEtypes_WmmAcParameters_t, *pIEEEtypes_WmmAcParameters_t;
typedef PACK_START struct _WmmParameter_t {
	t_u8 ouitype[4];
	t_u8 ouisubtype;
	t_u8 version;
	t_u8 qos_info;
	t_u8 reserved;
	IEEEtypes_WmmAcParameters_t ac_params[MAX_AC_QUEUES];
} PACK_END WmmParameter_t, *pWmmParameter_t;
typedef struct _wpa_param {
	t_u8 pairwise_cipher_wpa;
	t_u8 pairwise_cipher_wpa2;
	t_u8 group_cipher;
	t_u8 rsn_protection;
	t_u32 length;
	t_u8 passphrase[64];
	t_u32 gk_rekey_time;
} wpa_param;
typedef struct _wep_key {
	t_u8 key_index;
	t_u8 is_default;
	t_u16 length;
	t_u8 key[26];
} wep_key;
typedef struct _wep_param {
	wep_key key0;
	wep_key key1;
	wep_key key2;
	wep_key key3;
} wep_param;
typedef struct _bss_config_t {
	mlan_802_11_mac_addr mac_addr;
	mlan_802_11_ssid ssid;
	t_u8 bcast_ssid_ctl;
	t_u8 radio_ctl;
	t_u8 dtim_period;
	t_u16 beacon_period;
	t_u8 rates[MAX_DATA_RATES];
	t_u16 tx_data_rate;
	t_u16 tx_beacon_rate;
	t_u16 mcbc_data_rate;
	t_u8 tx_power_level;
	t_u8 tx_antenna;
	t_u8 rx_antenna;
	t_u8 pkt_forward_ctl;
	t_u16 max_sta_count;
	mac_filter filter;
	t_u32 sta_ageout_timer;
	t_u32 ps_sta_ageout_timer;
	t_u16 rts_threshold;
	t_u16 frag_threshold;
	t_u16 retry_limit;
	t_u32 pairwise_update_timeout;
	t_u32 pwk_retries;
	t_u32 groupwise_update_timeout;
	t_u32 gwk_retries;
	t_u8 preamble_type;
	Band_Config_t bandcfg;
	t_u8 channel;
	t_u16 auth_mode;
	t_u16 protocol;
	t_u16 key_mgmt;
	wep_param wep_cfg;
	wpa_param wpa_cfg;
	t_u32 mgmt_ie_passthru_mask;
	t_u16 ht_cap_info;
	t_u8 ampdu_param;
	t_u8 supported_mcs_set[16];
	t_u16 ht_ext_cap;
	t_u32 tx_bf_cap;
	t_u8 asel;
	t_u8 enable_2040coex;
	t_u16 key_mgmt_operation;
	t_u16 bss_status;
#ifdef WIFI_DIRECT_SUPPORT
	t_u8 psk[32];
#endif
	t_u32 num_of_chan;
	scan_chan_list chan_list[MAX_CHANNELS];
	WmmParameter_t wmm_para;
	t_u32 uap_host_based_config;
} bss_config_t;
enum _mlan_band_def {
	BAND_B = 1,
	BAND_G = 2,
	BAND_A = 4,
	BAND_GN = 8,
	BAND_AN = 16,
	BAND_GAC = 32,
	BAND_AAC = 64,
};
typedef struct _sta_stats {
	t_u64 last_rx_in_msec;
} sta_stats;
typedef struct _sta_info {
	t_u8 mac_address[ETH_ALEN];
	t_u8 power_mfg_status;
	t_s8 rssi;
	t_u8 bandmode;
	sta_stats stats;
} sta_info;
typedef struct _sta_list {
	t_u16 sta_count;
	sta_info info[MAX_NUM_CLIENTS];
} sta_list;
typedef struct _deauth_param {
	t_u8 mac_addr[ETH_ALEN];
	t_u16 reason_code;
} deauth_param;
typedef PACK_START struct _apcmdbuf_bss_configure {
	t_u32 action;
} PACK_END apcmdbuf_bss_configure;
#define MAX_EEPROM_LEN         20
#define DEBUG_SUBCOMMAND_GMODE          1
#define DEBUG_SUBCOMMAND_MAJOREVTMASK   2
#define DEBUG_SUBCOMMAND_CHANNEL_SCAN   3
typedef PACK_START struct _channel_scan_entry_t {
	t_u8 chan_num;
	t_u8 num_of_aps;
	t_u32 cca_count;
	t_u32 duration;
	t_u32 channel_weight;
} PACK_END channel_scan_entry_t;
typedef PACK_START struct _channel_scan_entry {
	t_u8 num_channels;
	channel_scan_entry_t cst[0];
} PACK_END channel_scan_entry;
typedef PACK_START struct _apcmdbuf_cfg_data {
	APCMDHEADER;
	t_u16 action;
	t_u16 type;
	t_u16 data_len;
	t_u8 data[0];
} PACK_END apcmdbuf_cfg_data;
#define MAX_CFG_DATA_SIZE   2000
typedef PACK_START struct _apcmdbuf_pmf_params {
	APCMDHEADER;
	t_u16 action;
	PACK_START struct {
		t_u8 mfpc:1;
		t_u8 mfpr:1;
		t_u8 rsvd:6;
	} PACK_END params;
} PACK_END apcmdbuf_pmf_params;
#define HostCmd_CMD_ID_MASK             0x0fff
#define APCMD_RESP_CHECK            0x8000
#define APCMD_SYS_INFO              0x00ae
#define APCMD_SYS_RESET             0x00af
#define APCMD_SYS_CONFIGURE         0x00b0
#define APCMD_BSS_START             0x00b1
#define APCMD_BSS_STOP              0x00b2
#define APCMD_STA_LIST              0x00b3
#define APCMD_STA_DEAUTH            0x00b5
#define HostCmd_SNMP_MIB            0x0016
#define HostCmd_CMD_MAC_REG_ACCESS  0x0019
#define HostCmd_CMD_BBP_REG_ACCESS  0x001a
#define HostCmd_CMD_RF_REG_ACCESS   0x001b
#define HostCmd_EEPROM_ACCESS       0x0059
#define HostCmd_CMD_MEM_ACCESS      0x0086
#define HostCmd_CMD_802_11D_DOMAIN_INFO      0x005b
#define HostCmd_CMD_CFG_DATA        0x008f
#define OID_80211D_ENABLE           0x0009
#define OID_80211H_ENABLE           0x000a
#define HostCmd_ROBUST_COEX         0x00e0
#define HostCmd_CMD_PMF_PARAMS      0x0131
#define PROPRIETARY_TLV_BASE_ID         0x0100
#define MRVL_SSID_TLV_ID                0x0000
#define MRVL_RATES_TLV_ID               0x0001
#define MRVL_PHYPARAMDSSET_TLV_ID       0x0003
#define TLV_TYPE_DOMAIN                 0x0007
#define MRVL_CHANNELLIST_TLV_ID         (PROPRIETARY_TLV_BASE_ID + 0x01)	//0x0101
#define MRVL_AUTH_TLV_ID                (PROPRIETARY_TLV_BASE_ID + 0x1f)	//0x011f
#define MRVL_CHANNELCONFIG_TLV_ID       (PROPRIETARY_TLV_BASE_ID + 0x2a)	//0x012a
#define MRVL_AP_MAC_ADDRESS_TLV_ID      (PROPRIETARY_TLV_BASE_ID + 0x2b)	//0x012b
#define MRVL_BEACON_PERIOD_TLV_ID       (PROPRIETARY_TLV_BASE_ID + 0x2c)	//0x012c
#define MRVL_DTIM_PERIOD_TLV_ID         (PROPRIETARY_TLV_BASE_ID + 0x2d)	//0x012d
#define MRVL_TX_POWER_TLV_ID            (PROPRIETARY_TLV_BASE_ID + 0x2f)	//0x012f
#define MRVL_BCAST_SSID_CTL_TLV_ID      (PROPRIETARY_TLV_BASE_ID + 0x30)	//0x0130
#define MRVL_PREAMBLE_CTL_TLV_ID        (PROPRIETARY_TLV_BASE_ID + 0x31)	//0x0131
#define MRVL_ANTENNA_CTL_TLV_ID         (PROPRIETARY_TLV_BASE_ID + 0x32)	//0x0132
#define MRVL_RTS_THRESHOLD_TLV_ID       (PROPRIETARY_TLV_BASE_ID + 0x33)	//0x0133
#define MRVL_PKT_FWD_CTL_TLV_ID         (PROPRIETARY_TLV_BASE_ID + 0x36)	//0x0136
#define MRVL_STA_INFO_TLV_ID            (PROPRIETARY_TLV_BASE_ID + 0x37)	//0x0137
#define MRVL_STA_MAC_ADDR_FILTER_TLV_ID (PROPRIETARY_TLV_BASE_ID + 0x38)	//0x0138
#define MRVL_STA_AGEOUT_TIMER_TLV_ID    (PROPRIETARY_TLV_BASE_ID + 0x39)	//0x0139
#define MRVL_WEP_KEY_TLV_ID             (PROPRIETARY_TLV_BASE_ID + 0x3b)	//0x013b
#define MRVL_WPA_PASSPHRASE_TLV_ID      (PROPRIETARY_TLV_BASE_ID + 0x3c)	//0x013c
#define MRVL_PROTOCOL_TLV_ID            (PROPRIETARY_TLV_BASE_ID + 0x40)	//0x0140
#define MRVL_AKMP_TLV_ID                (PROPRIETARY_TLV_BASE_ID + 0x41)	//0x0141
#define MRVL_CIPHER_TLV_ID              (PROPRIETARY_TLV_BASE_ID + 0x42)	//0x0142
#define MRVL_FRAG_THRESHOLD_TLV_ID      (PROPRIETARY_TLV_BASE_ID + 0x46)	//0x0146
#define MRVL_GRP_REKEY_TIME_TLV_ID      (PROPRIETARY_TLV_BASE_ID + 0x47)	//0x0147
#define MRVL_MAX_STA_CNT_TLV_ID         (PROPRIETARY_TLV_BASE_ID + 0x55)	//0x0155
#define MRVL_RETRY_LIMIT_TLV_ID         (PROPRIETARY_TLV_BASE_ID + 0x5d)	//0x015d
#define MRVL_MCBC_DATA_RATE_TLV_ID      (PROPRIETARY_TLV_BASE_ID + 0x62)	//0x0162
#define MRVL_RSN_REPLAY_PROT_TLV_ID     (PROPRIETARY_TLV_BASE_ID + 0x64)	//0x0164
#define MRVL_MGMT_IE_LIST_TLV_ID        (PROPRIETARY_TLV_BASE_ID + 0x69)	//0x0169
#define MRVL_BT_COEX_COMMON_CFG_TLV_ID  (PROPRIETARY_TLV_BASE_ID + 0x6c)	//0x016c
#define MRVL_BT_COEX_SCO_CFG_TLV_ID     (PROPRIETARY_TLV_BASE_ID + 0x6d)	//0x016d
#define MRVL_BT_COEX_ACL_CFG_TLV_ID     (PROPRIETARY_TLV_BASE_ID + 0x6e)	//0x016e
#define MRVL_BT_COEX_STATS_TLV_ID       (PROPRIETARY_TLV_BASE_ID + 0x6f)	//0x016f
#define MRVL_EAPOL_PWK_HSK_TIMEOUT_TLV_ID   (PROPRIETARY_TLV_BASE_ID + 0x75)	//0x0175
#define MRVL_EAPOL_PWK_HSK_RETRIES_TLV_ID   (PROPRIETARY_TLV_BASE_ID + 0x76)	//0x0176
#define MRVL_EAPOL_GWK_HSK_TIMEOUT_TLV_ID   (PROPRIETARY_TLV_BASE_ID + 0x77)	//0x0177
#define MRVL_EAPOL_GWK_HSK_RETRIES_TLV_ID   (PROPRIETARY_TLV_BASE_ID + 0x78)	//0x0178
#define MRVL_PS_STA_AGEOUT_TIMER_TLV_ID     (PROPRIETARY_TLV_BASE_ID + 0x7b)	//0x017b
#define MRVL_CIPHER_PWK_TLV_ID              (PROPRIETARY_TLV_BASE_ID + 0x91)	//0x0191
#define MRVL_CIPHER_GWK_TLV_ID              (PROPRIETARY_TLV_BASE_ID + 0x92)	//0x0192
#define MRVL_BSS_STATUS_TLV_ID              (PROPRIETARY_TLV_BASE_ID + 0x93)	//0x0193
#define MRVL_RESTRICT_CLIENT_MODE_TLV_ID    (PROPRIETARY_TLV_BASE_ID + 0xC1)	//0x01C1
#define MRVL_STICKY_TIM_CONFIG_TLV_ID       (PROPRIETARY_TLV_BASE_ID + 0x96)	//0x0196
#define MRVL_STICKY_TIM_STA_MAC_ADDR_TLV_ID       (PROPRIETARY_TLV_BASE_ID + 0x97)	//0x0197
#define MRVL_2040_BSS_COEX_CONTROL_TLV_ID         (PROPRIETARY_TLV_BASE_ID + 0x98)	//0x0198
#define MRVL_MAX_MGMT_IE_TLV_ID             (PROPRIETARY_TLV_BASE_ID + 0xAA)	//0x01aa
#define MRVL_REGION_DOMAIN_CODE_TLV_ID            (PROPRIETARY_TLV_BASE_ID + 0xAB)	//0x01ab
#ifdef RX_PACKET_COALESCE
#define MRVL_RX_PKT_COAL_TLV_ID             (PROPRIETARY_TLV_BASE_ID + 0xC9)
#endif
#define MRVL_TX_BEACON_RATE_TLV_ID        (PROPRIETARY_TLV_BASE_ID + 288)	//0x0220
#ifdef RX_PACKET_COALESCE
typedef PACK_START struct _tlvbuf_rx_pkt_coal_t {
	TLVHEADER;
	t_u32 rx_pkt_count;
	t_u16 delay;
} PACK_END tlvbuf_rx_pkt_coal_t;
#endif
#define MRVL_AP_WMM_PARAM_TLV_ID            (PROPRIETARY_TLV_BASE_ID + 0xD0)
#define MRVL_TDLS_EXT_CAP_TLV_ID                0x007f
#define TDLS_PROHIBIT_MASK                            0x40
#define TDLS_PROHIBIT                       6
#define TDLS_CHANNEL_SWITCH_PROHIBIT_MASK             0x80
#define TDLS_CHANNEL_SWITCH_PROHIBIT        7
#define MAX_TDLS_EXT_CAP_LEN                64
#define HT_CAPABILITY_TLV_ID            0x2d
#define HT_INFO_TLV_ID                  0x3d
#define HT_CAP_CONFIG_MASK              0x10f3
#define DEFAULT_HT_CAP_VALUE            0x117e
#define HT_CAP_CHECK_MASK		0x10c
#define AMPDU_CONFIG_MASK               0x1f
#define IS_11N_40MHZ_ENABLED(cap)  ((cap) & 0x002) >> 1
#define IS_11N_20MHZ_SHORTGI_ENABLED(cap)  ((cap) & 0x0020) >> 5
#define IS_11N_GF_ENABLED(cap)  ((cap) & 0x0010) >> 4
#define MCS_SET_LEN     16
typedef PACK_START struct _tlvbuf_htcap_t {
	TLVHEADER;
	HTCap_t ht_cap;
} PACK_END tlvbuf_htcap_t;
typedef PACK_START struct _tlvbuf_htinfo_t {
	TLVHEADER;
	HTInfo_t ht_info;
} PACK_END tlvbuf_htinfo_t;
#define MAX_BITMAP_RATES_SIZE   18
typedef PACK_START struct _tx_rate_cfg_t {
	int subcmd;
	int action;
	int rate_format;
	int rate;
	int nss;
	int user_data_cnt;
	t_u16 bitmap_rates[MAX_BITMAP_RATES_SIZE];
} PACK_END tx_rate_cfg_t;
#define STREAM_2X2_MASK     0x20
#define MCS_SET_1_MASK      0x0000ff00
#define DEFAULT_MCS_SET_0   0xff
#define DEFAULT_MCS_SET_4   0x01
#define UAP_RATE_BITMAP_MCS0  32
#define UAP_RATE_BITMAP_MCS127 159
#define UAP_RATE_INDEX_MCS0   12
#define UAP_RATE_INDEX_MCS7   19
#define UAP_RATE_INDEX_MCS32  44
#define RESTRICT_CLIENT_MODE_ENABLE_MASK   0x01
#define B_ONLY_MASK   0x0100
#define A_ONLY_MASK   0x0200
#define G_ONLY_MASK   0x0400
#define N_ONLY_MASK   0x0800
#define AC_ONLY_MASK  0x1000
typedef enum _wmm_ac {
	AC_BE,
	AC_BK,
	AC_VI,
	AC_VO,
} wmm_ac;
typedef PACK_START struct _tlvbuf_restrict_client_mode {
	TLVHEADER;
	t_u16 mode_config;
} PACK_END tlvbuf_restrict_client_mode;
#define VENDOR_SPECIFIC_IE_TLV_ID   0xdd
#define WMM_PS_MASK                 0x7f
#define ENABLE_WMM_PS               128
#define DISABLE_WMM_PS              0
#define MAX_AC_QUEUES               4
typedef PACK_START struct _tlvbuf_wmm_para_t {
	TLVHEADER;
	WmmParameter_t wmm_para;
} PACK_END tlvbuf_wmm_para_t;
struct eth_priv_vhtcfg {
	t_u32 band;
	t_u32 txrx;
	t_u32 bwcfg;
	t_u32 vht_cap_info;
	t_u32 vht_tx_mcs;
	t_u32 vht_rx_mcs;
	t_u16 vht_rx_max_rate;
	t_u16 vht_tx_max_rate;
};
typedef struct _vht_cfg_para {
	t_u32 subcmd;
	t_u32 action;
	struct eth_priv_vhtcfg vht_cfg;
} vht_cfg_para;
struct eth_priv_uap_oper_ctrl {
	t_u16 ctrl;
	t_u16 chan_opt;
	t_u8 bandcfg;
	t_u8 channel;
};
typedef struct _uap_operation_ctrl {
	t_u32 subcmd;
	t_u32 action;
	struct eth_priv_uap_oper_ctrl uap_oper;
} uap_operation_ctrl;
#define MRVL_AP_WACP_MODE_TLV_ID        (PROPRIETARY_TLV_BASE_ID + 0x147)
typedef PACK_START struct _tlvbuf_wacp_mode_ {
	TLVHEADER;
	t_u8 wacp_mode;
} PACK_END tlvbuf_wacp_mode;
int mac2raw(char *mac, t_u8 *raw);
void print_mac(t_u8 *raw);
int uap_ioctl(t_u8 *cmd, t_u16 *size, t_u16 buf_size);
void print_auth(tlvbuf_auth_mode *tlv);
void print_tlv(t_u8 *buf, t_u16 len);
void print_cipher(tlvbuf_cipher *tlv);
void print_pwk_cipher(tlvbuf_pwk_cipher *tlv);
void print_gwk_cipher(tlvbuf_gwk_cipher *tlv);
void print_rate(tlvbuf_rates *tlv);
int string2raw(char *str, unsigned char *raw);
void print_mac_filter(tlvbuf_sta_mac_addr_filter *tlv);
int ishexstring(void *hex);
unsigned int a2hex(char *s);
int fparse_for_hex(FILE * fp, t_u8 *dst);
int is_input_valid(valid_inputs cmd, int argc, char *argv[]);
int is_cipher_valid(int pairwisecipher, int groupcipher);
int is_cipher_valid_with_proto(int pairwisecipher, int groupcipher,
			       int protocol);
int get_sys_cfg_rates(t_u8 *rates);
int is_tx_rate_valid(t_u8 rate);
int is_mcbc_rate_valid(t_u8 rate);
void hexdump_data(char *prompt, void *p, int len, char delim);
unsigned char hexc2bin(char chr);
int check_sys_config(t_u8 *buf, t_u16 len);
int check_bss_config(t_u8 *buf);
int get_max_sta_num_supported(t_u16 *max_sta_num_supported);
int get_sys_cfg_protocol(t_u16 *proto);
int is_cipher_valid_with_11n(int pairwisecipher, int groupcipher,
			     int protocol, int enable_11n);
int get_sys_cfg_11n(HTCap_t *pHtCap);
int get_fw_info(fw_info *pfw_info);
t_u8 parse_domain_file(char *country, int band,
		       ieeetypes_subband_set_t *sub_bands, t_u8 *pdomain_code);
int sg_snmp_mib(t_u16 action, t_u16 oid, t_u16 size, t_u8 *oid_buf);
int check_channel_validity_11d(int channel, int band, int set_domain);
int check_tx_pwr_validity_11d(t_u8 tx_pwr);
int prepare_host_cmd_buffer(char *fname, char *cmd_name, t_u8 *buf);
char *mlan_config_get_line(FILE * fp, char *s, t_s32 size, int *line);
static inline int
ISDIGIT(char *x)
{
	unsigned int i;
	for (i = 0; i < strlen(x); i++)
		if (isdigit(x[i]) == 0)
			return UAP_FAILURE;
	return UAP_SUCCESS;
}
static inline int
has_diff_band(int argc, char *argv[])
{
	int i = 0;
	int channel = 0;
	int band[MAX_CHANNELS];
	for (i = 0; i < argc; i++) {
		band[i] = -1;
		sscanf(argv[i], "%d.%d", &channel, &band[i]);
		if (band[i] == -1) {
			if (channel > MAX_CHANNELS_BG) {
				band[i] = 1;
			} else {
				band[i] = 0;
			}
		}
	}
	for (i = 0; i <= (argc - 2); i++) {
		if (band[i] != band[i + 1]) {
			return UAP_FAILURE;
		}
	}
	return UAP_SUCCESS;
}
static inline int
has_dup_channel(int argc, char *argv[])
{
	int i, j;
	for (i = 0; i < (argc - 1); i++) {
		for (j = i + 1; j < argc; j++) {
			if (atoi(argv[i]) == atoi(argv[j])) {
				return UAP_FAILURE;
			}
		}
	}
	return UAP_SUCCESS;
}
static inline int
has_dup_rate(int argc, char *argv[])
{
	int i, j;
	for (i = 0; i < (argc - 1); i++) {
		for (j = i + 1; j < argc; j++) {
			if ((A2HEXDECIMAL(argv[i]) & ~BASIC_RATE_SET_BIT) ==
			    (A2HEXDECIMAL(argv[j]) & ~BASIC_RATE_SET_BIT)) {
				return UAP_FAILURE;
			}
		}
	}
	return UAP_SUCCESS;
}
