balena-io-hardware/fin-info-doc/software/drivers/sd8887/src/wlan/mapp/mlanutl/mlanutl.c

/** @file  mlanutl.c
  *
  * @brief Program to control parameters in the mlandriver
  *
  *
  * Copyright 2014-2020 NXP
  *
  * This software file (the File) is distributed by NXP
  * under the terms of the GNU General Public License Version 2, June 1991
  * (the License).  You may use, redistribute and/or modify the File in
  * accordance with the terms and conditions of the License, a copy of which
  * is available by writing to the Free Software Foundation, Inc.,
  * 51 Franklin Street, Fifth Floor, Boston, MA 02110-1301 USA or on the
  * worldwide web at http://www.gnu.org/licenses/old-licenses/gpl-2.0.txt.
  *
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
  */
/************************************************************************
Change log:
     11/04/2011: initial version
************************************************************************/
#include <stdio.h>
#include <stdlib.h>
#include <unistd.h>
#include <string.h>
#include <ctype.h>
#include <signal.h>
#include <time.h>
#include <sys/time.h>
#include <getopt.h>

#include <sys/socket.h>
#include <linux/netlink.h>
#include <linux/if.h>
#include <sys/stat.h>
#include <net/ethernet.h>

#include    "mlanutl.h"

/** mlanutl version number */
#define MLANUTL_VER "M1.3"

/** Initial number of total private ioctl calls */
#define IW_INIT_PRIV_NUM    128
/** Maximum number of total private ioctl calls supported */
#define IW_MAX_PRIV_NUM     1024

/** Termination flag */
int terminate_flag = 0;

typedef struct {
	t_u8 chanNum;	  /**< Channel Number */
	t_u8 chanLoad;	  /**< Channel Load fraction */
	t_s16 anpi;	  /**< Channel ANPI */

} ChanRptInfo_t;

/********************************************************
			Local Variables
********************************************************/
#define BAND_B       (1U << 0)
#define BAND_G       (1U << 1)
#define BAND_A       (1U << 2)
#define BAND_GN      (1U << 3)
#define BAND_AN      (1U << 4)
#define BAND_GAC     (1U << 5)
#define BAND_AAC     (1U << 6)

static char *band[] = {
	"B",
	"G",
	"A",
	"GN",
	"AN",
	"GAC",
	"AAC",
};

/** Stringification of rateId enumeration */
const char *rateIdStr[] = { "1", "2", "5.5", "11", "--",
	"6", "9", "12", "18", "24", "36", "48", "54", "--",
	"M0", "M1", "M2", "M3", "M4", "M5", "M6", "M7",
	"H0", "H1", "H2", "H3", "H4", "H5", "H6", "H7"
};

#ifdef DEBUG_LEVEL1
#define MMSG        MBIT(0)
#define MFATAL      MBIT(1)
#define MERROR      MBIT(2)
#define MDATA       MBIT(3)
#define MCMND       MBIT(4)
#define MEVENT      MBIT(5)
#define MINTR       MBIT(6)
#define MIOCTL      MBIT(7)

#define MMPA_D      MBIT(15)
#define MDAT_D      MBIT(16)
#define MCMD_D      MBIT(17)
#define MEVT_D      MBIT(18)
#define MFW_D       MBIT(19)
#define MIF_D       MBIT(20)

#define MENTRY      MBIT(28)
#define MWARN       MBIT(29)
#define MINFO       MBIT(30)
#define MHEX_DUMP   MBIT(31)
#endif
static int process_multi_chan_cfg(int argc, char *argv[]);
static int process_multi_chan_policy(int argc, char *argv[]);
static int process_drcs_time_slicing_cfg(int argc, char *argv[]);
#ifdef RX_PACKET_COALESCE
static int process_rx_pkt_coalesce_cfg(int argc, char *argv[]);
static void print_rx_packet_coalesc_help(void);
#endif
static int process_version(int argc, char *argv[]);
static int process_bandcfg(int argc, char *argv[]);
static int process_hostcmd(int argc, char *argv[]);
static int process_httxcfg(int argc, char *argv[]);
static int process_htcapinfo(int argc, char *argv[]);
static int process_addbapara(int argc, char *argv[]);
static int process_aggrpriotbl(int argc, char *argv[]);
static int process_addbareject(int argc, char *argv[]);
static int process_delba(int argc, char *argv[]);
static int process_rejectaddbareq(int argc, char *argv[]);
static int process_vhtcfg(int argc, char *argv[]);
static int process_opermodecfg(int argc, char *argv[]);
static int process_datarate(int argc, char *argv[]);
static int process_txratecfg(int argc, char *argv[]);
static int process_getlog(int argc, char *argv[]);
static int process_getcfgchanlist(int argc, char *argv[]);
static int process_esuppmode(int argc, char *argv[]);
static int process_passphrase(int argc, char *argv[]);
static int process_deauth(int argc, char *argv[]);
#ifdef UAP_SUPPORT
static int process_getstalist(int argc, char *argv[]);
#endif
#if defined(WIFI_DIRECT_SUPPORT)
#if defined(STA_SUPPORT) && defined(UAP_SUPPORT)
static int process_bssrole(int argc, char *argv[]);
#endif
#endif
#ifdef STA_SUPPORT
static int process_setuserscan(int argc, char *argv[]);
static int wlan_process_getscantable(int argc, char *argv[],
				     wlan_ioctl_user_scan_cfg *scan_req);
static int process_getscantable(int argc, char *argv[]);
static int process_extcapcfg(int argc, char *argv[]);
static int process_cancelscan(int argc, char *argv[]);
#endif
static int process_deepsleep(int argc, char *argv[]);
static int process_ipaddr(int argc, char *argv[]);
static int process_otpuserdata(int argc, char *argv[]);
static int process_countrycode(int argc, char *argv[]);
static int process_tcpackenh(int argc, char *argv[]);
#ifdef REASSOCIATION
static int process_assocessid(int argc, char *argv[]);
#endif
#ifdef STA_SUPPORT
static int process_listeninterval(int argc, char *argv[]);
static int process_psmode(int argc, char *argv[]);
#endif
#ifdef DEBUG_LEVEL1
static int process_drvdbg(int argc, char *argv[]);
#endif
static int process_hscfg(int argc, char *argv[]);
static int process_hssetpara(int argc, char *argv[]);
static int process_wakeupresaon(int argc, char *argv[]);
static int process_mgmtfilter(int argc, char *argv[]);
static int process_scancfg(int argc, char *argv[]);
static int process_warmreset(int argc, char *argv[]);
static int process_txpowercfg(int argc, char *argv[]);
static int process_pscfg(int argc, char *argv[]);
static int process_bcntimeoutcfg(int argc, char *argv[]);
static int process_sleeppd(int argc, char *argv[]);
static int process_txcontrol(int argc, char *argv[]);
static int process_host_tdls_config(int argc, char *argv[]);
static int process_tdls_config(int argc, char *argv[]);
static int process_tdls_setinfo(int argc, char *argv[]);
static int process_tdls_discovery(int argc, char *argv[]);
static int process_tdls_setup(int argc, char *argv[]);
static int process_tdls_teardown(int argc, char *argv[]);
static int process_tdls_powermode(int argc, char *argv[]);
static int process_tdls_link_status(int argc, char *argv[]);
static int process_tdls_debug(int argc, char *argv[]);
static int process_tdls_channel_switch(int argc, char *argv[]);
static int process_tdls_stop_channel_switch(int argc, char *argv[]);
static int process_tdls_cs_params(int argc, char *argv[]);
static int process_tdls_disable_channel_switch(int argc, char *argv[]);
static int process_tdls_idle_time(int argc, char *argv[]);
static int process_dfs_offload_enable(int argc, char *argv[]);
static int process_customie(int argc, char *argv[]);
static int process_regrdwr(int argc, char *argv[]);
static int process_rdeeprom(int argc, char *argv[]);
static int process_memrdwr(int argc, char *argv[]);
static int process_sdcmd52rw(int argc, char *argv[]);
static int process_mefcfg(int argc, char *argv[]);
#ifdef STA_SUPPORT
static int process_arpfilter(int argc, char *argv[]);
#endif
static int process_cfgdata(int argc, char *argv[]);
static int process_mgmtframetx(int argc, char *argv[]);
static int process_mgmt_frame_passthrough(int argc, char *argv[]);
static int process_qconfig(int argc, char *argv[]);
static int process_addts(int argc, char *argv[]);
static int process_delts(int argc, char *argv[]);
static int process_wmm_qstatus(int argc, char *argv[]);
static int process_wmm_ts_status(int argc, char *argv[]);
static int process_qos_config(int argc, char *argv[]);
static int process_macctrl(int argc, char *argv[]);
static int process_fwmacaddr(int argc, char *argv[]);
static int process_regioncode(int argc, char *argv[]);
static int process_cfpinfo(int argc, char *argv[]);
static int process_offchannel(int argc, char *argv[]);
static int process_linkstats(int argc, char *argv[]);
#if defined(STA_SUPPORT)
static int process_pmfcfg(int argc, char *argv[]);
#endif
static int process_verext(int argc, char *argv[]);
#if defined(STA_SUPPORT) && defined(STA_WEXT)
static int process_radio_ctrl(int argc, char *argv[]);
#endif
static int process_wmm_cfg(int argc, char *argv[]);
static int process_wmm_param_config(int argc, char *argv[]);
#if defined(STA_SUPPORT)
static int process_11d_cfg(int argc, char *argv[]);
static int process_11d_clr_tbl(int argc, char *argv[]);
#endif
static int process_wws_cfg(int argc, char *argv[]);
#if defined(REASSOCIATION)
static int process_set_get_reassoc(int argc, char *argv[]);
#endif
static int process_txbuf_cfg(int argc, char *argv[]);
#ifdef STA_SUPPORT
static int process_set_get_auth_type(int argc, char *argv[]);
#endif
static int process_11h_local_pwr_constraint(int argc, char *argv[]);
static int process_thermal(int argc, char *argv[]);
static int process_beacon_interval(int argc, char *argv[]);
static int process_cwmode(int argc, char *argv[]);
#ifdef STA_SUPPORT
static int process_get_signal(int argc, char *argv[]);
#endif
static int process_inactivity_timeout_ext(int argc, char *argv[]);
static int process_11n_amsdu_aggr_ctrl(int argc, char *argv[]);
static int process_tx_bf_cap_ioctl(int argc, char *argv[]);
static int process_sdio_clock_ioctl(int argc, char *argv[]);
#if defined(SDIO_MULTI_PORT_TX_AGGR) || defined(SDIO_MULTI_PORT_RX_AGGR)
static int process_sdio_mpa_ctrl(int argc, char *argv[]);
#endif
static int process_sleep_params(int argc, char *argv[]);
#if defined(DFS_TESTING_SUPPORT)
static int process_dfs_testing(int argc, char *argv[]);
#endif
static int process_cfp_code(int argc, char *argv[]);
static int process_set_get_tx_rx_ant(int argc, char *argv[]);
static int process_get_txpwrlimit(int argc, char *argv[]);
static int process_get_chnrgpwr(int argc, char *argv[]);
static int process_compare_rgpwr(int argc, char *argv[]);
static int process_comparetrpc(int argc, char *argv[]);
static int process_sysclock(int argc, char *argv[]);
static int process_associate_ssid_bssid(int argc, char *argv[]);
static int process_tx_bf_cfg(int argc, char *argv[]);
static int process_wps_cfg(int argc, char *argv[]);
static int process_port_ctrl(int argc, char *argv[]);
static int process_bypassed_packet(int argc, char *argv[]);
/* #ifdef FW_WAKEUP_METHOD */
static int process_fw_wakeup_method(int argc, char *argv[]);
/* #endif */
static int process_sdcmd53rw(int argc, char *argv[]);
#if defined(WIFI_DIRECT_SUPPORT)
#endif
static int process_dscpmap(int argc, char *argv[]);
#ifdef WIFI_DIRECT_SUPPORT
static int process_miracastcfg(int argc, char *argv[]);
#endif
static int process_coex_rx_winsize(int argc, char *argv[]);
static int process_txaggrctrl(int argc, char *argv[]);
static int process_auto_tdls(int argc, char *argv[]);
static int process_get_sensor_temp(int argc, char *argv[]);
static int process_chan_graph(int argc, char *argv[]);
static int process_extend_channel_switch(int argc, char *argv[]);
#if defined(SDIO_SUSPEND_RESUME)
static int process_auto_arp(int argc, char *argv[]);
#endif
int process_tsf(int argc, char *argv[]);
static int process_dyn_bw(int argc, char *argv[]);
static int process_tx_ampdu_prot_mode(int argc, char *argv[]);
static int process_ctrldeauth(int argc, char *argv[]);
static int process_robustcoex(int argc, char *argv[]);
static int process_acs(int argc, char *argv[]);
static int process_bootsleep(int argc, char *argv[]);

struct command_node command_list[] = {
	{"version", process_version},
	{"bandcfg", process_bandcfg},
	{"hostcmd", process_hostcmd},
	{"httxcfg", process_httxcfg},
	{"htcapinfo", process_htcapinfo},
	{"addbapara", process_addbapara},
	{"aggrpriotbl", process_aggrpriotbl},
	{"addbareject", process_addbareject},
	{"delba", process_delba},
	{"rejectaddbareq", process_rejectaddbareq},
	{"vhtcfg", process_vhtcfg},
	{"opermodecfg", process_opermodecfg},
	{"getdatarate", process_datarate},
	{"txratecfg", process_txratecfg},
	{"getlog", process_getlog},
	{"esuppmode", process_esuppmode},
	{"passphrase", process_passphrase},
	{"deauth", process_deauth},
#ifdef UAP_SUPPORT
	{"getstalist", process_getstalist},
#endif
#if defined(WIFI_DIRECT_SUPPORT)
#if defined(STA_SUPPORT) && defined(UAP_SUPPORT)
	{"bssrole", process_bssrole},
#endif
#endif
#ifdef STA_SUPPORT
	{"setuserscan", process_setuserscan},
	{"getscantable", process_getscantable},
	{"extcapcfg", process_extcapcfg},
	{"cancelscan", process_cancelscan},
#endif
	{"deepsleep", process_deepsleep},
	{"ipaddr", process_ipaddr},
	{"otpuserdata", process_otpuserdata},
	{"countrycode", process_countrycode},
	{"tcpackenh", process_tcpackenh},
#ifdef REASSOCIATION
	{"assocessid", process_assocessid},
	{"assocessid_bssid", process_assocessid},
#endif
#ifdef STA_SUPPORT
	{"listeninterval", process_listeninterval},
	{"psmode", process_psmode},
#endif
#ifdef DEBUG_LEVEL1
	{"drvdbg", process_drvdbg},
#endif
	{"hscfg", process_hscfg},
	{"hssetpara", process_hssetpara},
	{"wakeupreason", process_wakeupresaon},
	{"mgmtfilter", process_mgmtfilter},
	{"scancfg", process_scancfg},
	{"warmreset", process_warmreset},
	{"txpowercfg", process_txpowercfg},
	{"pscfg", process_pscfg},
	{"bcntimeoutcfg", process_bcntimeoutcfg},
	{"sleeppd", process_sleeppd},
	{"txcontrol", process_txcontrol},
	{"host_tdls_config", process_host_tdls_config},
	{"tdls_config", process_tdls_config},
	{"tdls_setinfo", process_tdls_setinfo},
	{"tdls_discovery", process_tdls_discovery},
	{"tdls_setup", process_tdls_setup},
	{"tdls_teardown", process_tdls_teardown},
	{"tdls_powermode", process_tdls_powermode},
	{"tdls_link_status", process_tdls_link_status},
	{"tdls_debug", process_tdls_debug},
	{"tdls_channel_switch", process_tdls_channel_switch},
	{"tdls_stop_channel_switch", process_tdls_stop_channel_switch},
	{"tdls_cs_params", process_tdls_cs_params},
	{"tdls_disable_cs", process_tdls_disable_channel_switch},
	{"tdls_idle_time", process_tdls_idle_time},
	{"dfs_offload", process_dfs_offload_enable},
	{"customie", process_customie},
	{"regrdwr", process_regrdwr},
	{"rdeeprom", process_rdeeprom},
	{"memrdwr", process_memrdwr},
	{"sdcmd52rw", process_sdcmd52rw},
	{"mefcfg", process_mefcfg},
#ifdef STA_SUPPORT
	{"arpfilter", process_arpfilter},
#endif
	{"cfgdata", process_cfgdata},
	{"mgmtframetx", process_mgmtframetx},
	{"mgmtframectrl", process_mgmt_frame_passthrough},
	{"qconfig", process_qconfig},
	{"addts", process_addts},
	{"delts", process_delts},
	{"ts_status", process_wmm_ts_status},
	{"qstatus", process_wmm_qstatus},
	{"qoscfg", process_qos_config},
	{"macctrl", process_macctrl},
	{"fwmacaddr", process_fwmacaddr},
	{"regioncode", process_regioncode},
	{"cfpinfo", process_cfpinfo},
	{"offchannel", process_offchannel},
	{"linkstats", process_linkstats},
#if defined(STA_SUPPORT)
	{"pmfcfg", process_pmfcfg},
#endif
	{"verext", process_verext},
#if defined(STA_SUPPORT) && defined(STA_WEXT)
	{"radioctrl", process_radio_ctrl},
#endif
	{"wmmcfg", process_wmm_cfg},
	{"wmmparamcfg", process_wmm_param_config},
#if defined(STA_SUPPORT)
	{"11dcfg", process_11d_cfg},
	{"11dclrtbl", process_11d_clr_tbl},
#endif
	{"wwscfg", process_wws_cfg},
#if defined(REASSOCIATION)
	{"reassoctrl", process_set_get_reassoc},
#endif
	{"txbufcfg", process_txbuf_cfg},
#ifdef STA_SUPPORT
	{"authtype", process_set_get_auth_type},
#endif
	{"powercons", process_11h_local_pwr_constraint},
	{"thermal", process_thermal},
	{"bcninterval", process_beacon_interval},
	{"cwmode", process_cwmode},
#ifdef STA_SUPPORT
	{"getsignal", process_get_signal},
#endif
	{"inactivityto", process_inactivity_timeout_ext},
	{"amsduaggrctrl", process_11n_amsdu_aggr_ctrl},
	{"httxbfcap", process_tx_bf_cap_ioctl},
	{"sdioclock", process_sdio_clock_ioctl},
#if defined(SDIO_MULTI_PORT_TX_AGGR) || defined(SDIO_MULTI_PORT_RX_AGGR)
	{"mpactrl", process_sdio_mpa_ctrl},
#endif
	{"sleepparams", process_sleep_params},
#if defined(DFS_TESTING_SUPPORT)
	{"dfstesting", process_dfs_testing},
#endif
	{"cfpcode", process_cfp_code},
	{"antcfg", process_set_get_tx_rx_ant},
	{"get_chnrgpwr", process_get_chnrgpwr},
	{"comparergpwr", process_compare_rgpwr},
	{"get_txpwrlimit", process_get_txpwrlimit},
	{"getcfgchanlist", process_getcfgchanlist},
	{"comparetrpc", process_comparetrpc},
	{"dscpmap", process_dscpmap},
	{"changraph", process_chan_graph},
	{"associate", process_associate_ssid_bssid},
	{"httxbfcfg", process_tx_bf_cfg},
	{"wpssession", process_wps_cfg},
	{"port_ctrl", process_port_ctrl},
	{"pb_bypass", process_bypassed_packet},
/* #ifdef FW_WAKEUP_METHOD */
	{"fwwakeupmethod", process_fw_wakeup_method},
/* #endif */
	{"sysclock", process_sysclock},
	{"sdcmd53rw", process_sdcmd53rw},
	{"mc_cfg", process_multi_chan_cfg},
	{"mc_policy", process_multi_chan_policy},
	{"mc_cfg_ext", process_drcs_time_slicing_cfg},
#ifdef RX_PACKET_COALESCE
	{"rxpktcoal_cfg", process_rx_pkt_coalesce_cfg},
#endif
#if defined(WIFI_DIRECT_SUPPORT)
#endif
#ifdef WIFI_DIRECT_SUPPORT
	{"miracastcfg", process_miracastcfg},
#endif
	{"coex_rx_winsize", process_coex_rx_winsize},
	{"txaggrctrl", process_txaggrctrl},
	{"autotdls", process_auto_tdls},
	{"get_sensor_temp", process_get_sensor_temp},
	{"channel_switch", process_extend_channel_switch},
#if defined(SDIO_SUSPEND_RESUME)
	{"auto_arp", process_auto_arp},
#endif
	{"tsf", process_tsf},
	{"dyn_bw", process_dyn_bw},
	{"tx_ampdu_prot_mode", process_tx_ampdu_prot_mode},
	{"ctrldeauth", process_ctrldeauth},
	{"robustcoex", process_robustcoex},
	{"acs", process_acs},
	{"bootsleep", process_bootsleep},
};

static char *usage[] = {
	"Usage: ",
	"   mlanutl -v  (version)",
	"   mlanutl <ifname> <cmd> [...]",
	"   where",
	"   ifname : wireless network interface name, such as mlanX or uapX",
	"   cmd :",
	"         11dcfg",
	"         11dclrtbl",
	"         addbapara",
	"         addbareject",
	"         addts",
	"         aggrpriotbl",
	"         amsduaggrctrl",
	"         antcfg",
#ifdef STA_SUPPORT
	"         arpfilter",
#endif
#ifdef REASSOCIATION
	"         assocessid",
	"         assocessid_bssid",
#endif
	"         associate",
	"         authtype",
	"         autotdls",
	"         bandcfg",
	"         bcninterval",
#if defined(WIFI_DIRECT_SUPPORT)
#if defined(STA_SUPPORT) && defined(UAP_SUPPORT)
	"         bssrole",
#endif
#endif
	"         cfgdata",
	"         cfpcode",
	"         changraph",
	"         coex_rx_winsize",
	"         countrycode",
	"         customie",
	"         deauth",
	"         deepsleep",
	"         delba",
	"         delts",
#if defined(DFS_TESTING_SUPPORT)
	"         dfstesting",
#endif
#ifdef DEBUG_LEVEL1
	"         drvdbg",
#endif
	"         dscpmap",
	"         esuppmode",
#ifdef STA_SUPPORT
	"         extcapcfg",
	"         cancelscan",
#endif
	"         fwmacaddr",
/* #ifdef FW_WAKEUP_METHOD */
	"         fwwakeupmethod",
/* #endif */
	"         getdatarate",
	"         getlog",
#ifdef STA_SUPPORT
	"         getscantable",
#endif
	"         getsignal",
#ifdef UAP_SUPPORT
	"         getstalist",
#endif
	"         hostcmd",
	"         hscfg",
	"         hssetpara",
	"         mgmtfilter",
	"         htcapinfo",
	"         httxbfcap",
	"         httxbfcfg",
	"         httxcfg",
	"         inactivityto",
	"         ipaddr",
	"         linkstats",
#ifdef STA_SUPPORT
	"         listeninterval",
#endif
	"         macctrl",
	"         mefcfg",
	"         memrdwr",
#ifdef WIFI_DIRECT_SUPPORT
	"         miracastcfg",
#endif
	"         mgmtframectrl",
	"         mgmtframetx",
#if defined(SDIO_MULTI_PORT_TX_AGGR) || defined(SDIO_MULTI_PORT_RX_AGGR)
	"         mpactrl",
#endif
#if defined(WIFI_DIRECT_SUPPORT)
#if CFG80211_VERSION_CODE >= WIFI_DIRECT_KERNEL_VERSION
#endif
#endif
	"         offchannel",
	"         otpuserdata",
	"         passphrase",
	"         pb_bypass",
#if defined(STA_SUPPORT)
	"         pmfcfg",
#endif
	"         port_ctrl",
	"         powercons",
	"         pscfg",
#ifdef STA_SUPPORT
	"         psmode",
#endif
	"         qconfig",
	"         qoscfg",
	"         qstatus",
#ifdef STA_WEXT
	"         radioctrl",
#endif
	"         rdeeprom",
#if defined(REASSOCIATION)
	"         reassoctrl",
#endif
	"         regioncode",
	"         cfpinfo",
	"         regrdwr",
	"         rejectaddbareq",
	"         scancfg",
	"         sdcmd52rw",
	"         sdcmd53rw",
	"         sdioclock",
#ifdef STA_SUPPORT
	"         setuserscan",
#endif
	"         sleepparams",
	"         sleeppd",
	"         sysclock",
	"         tcpackenh",
	"         tdls_idle_time",
	"         tdls_channel_switch",
	"         tdls_config",
	"         tdls_cs_params",
	"         tdls_debug",
	"         tdls_disable_cs",
	"         tdls_discovery",
	"         tdls_link_status",
	"         tdls_powermode",
	"         tdls_setinfo",
	"         tdls_setup",
	"         tdls_stop_channel_switch",
	"         tdls_teardown",
	"         thermal",
	"         ts_status",
	"         tsf",
	"         txaggrctrl",
	"         txbufcfg",
	"         txcontrol",
	"         txpowercfg",
	"         txratecfg",
	"         verext",
	"         version",
	"         vhtcfg",
	"         opermodecfg",
	"         wakeupreason",
	"         warmreset",
	"         wmmcfg",
	"         wmmparamcfg",
	"         wpssession",
	"         wwscfg",
	"         mc_cfg",
	"         mc_policy",
	"         mc_cfg_ext",
#ifdef RX_PACKET_COALESCE
	"         rxpktcoal_cfg",
#endif
	"         get_sensor_temp",
	"         channel_switch",
	"         dfs_offload",

	"         tx_ampdu_prot_mode",
	"         cwmode",
	"         dyn_bw",
	"         ctrldeauth",
	"         robustcoex",
	"         get_chnrgpwr",
	"         comparergpwr",
	"         get_txpwrlimit",
	"         comparetrpc",
	"         getcfgchanlist",
};

/** Socket */
t_s32 sockfd;
/** Device name */
char dev_name[IFNAMSIZ + 1];
#define HOSTCMD "hostcmd"

#define BSSID_FILTER 1
#define SSID_FILTER 2
/********************************************************
			Global Variables
********************************************************/

int setuserscan_filter = 0;
int num_ssid_filter = 0;
/********************************************************
			Local Functions
********************************************************/

/**
 *    @brief isdigit for String.
 *
 *    @param x            Char string
 *    @return             MLAN_STATUS_FAILURE for non-digit.
 *                        MLAN_STATUS_SUCCESS for digit
 */
static int
ISDIGIT(char *x)
{
	unsigned int i;
	for (i = 0; i < strlen(x); i++)
		if (isdigit(x[i]) == 0)
			return MLAN_STATUS_FAILURE;
	return MLAN_STATUS_SUCCESS;
}

/**
 * Check of decimal or hex string
 * @param   num string
 */
#define IS_HEX_OR_DIGIT(num) \
    (strncasecmp("0x", (num), 2)?ISDIGIT((num)):ishexstring((num)))

/**
 *  @brief Convert char to hex integer
 *
 *  @param chr      Char to convert
 *  @return         Hex integer or 0
 */
int
hexval(t_s32 chr)
{
	if (chr >= '0' && chr <= '9')
		return chr - '0';
	if (chr >= 'A' && chr <= 'F')
		return chr - 'A' + 10;
	if (chr >= 'a' && chr <= 'f')
		return chr - 'a' + 10;

	return 0;
}

/**
 *  @brief Hump hex data
 *
 *  @param prompt   A pointer prompt buffer
 *  @param p        A pointer to data buffer
 *  @param len      The len of data buffer
 *  @param delim    Delim char
 *  @return         Hex integer
 */
t_void
hexdump(char *prompt, t_void *p, t_s32 len, char delim)
{
	t_s32 i;
	t_u8 *s = p;

	if (prompt) {
		printf("%s: len=%d\n", prompt, (int)len);
	}
	for (i = 0; i < len; i++) {
		if (i != len - 1)
			printf("%02x%c", *s++, delim);
		else
			printf("%02x\n", *s);
		if ((i + 1) % 16 == 0)
			printf("\n");
	}
	printf("\n");
}

/**
 *  @brief Convert char to hex integer
 *
 *  @param chr      Char
 *  @return         Hex integer
 */
t_u8
hexc2bin(char chr)
{
	if (chr >= '0' && chr <= '9')
		chr -= '0';
	else if (chr >= 'A' && chr <= 'F')
		chr -= ('A' - 10);
	else if (chr >= 'a' && chr <= 'f')
		chr -= ('a' - 10);

	return chr;
}

/**
 *  @brief Convert string to hex integer
 *
 *  @param s        A pointer string buffer
 *  @return         Hex integer
 */
t_u32
a2hex(char *s)
{
	t_u32 val = 0;

	if (!strncasecmp("0x", s, 2)) {
		s += 2;
	}

	while (*s && isxdigit(*s)) {
		val = (val << 4) + hexc2bin(*s++);
	}

	return val;
}

/*
 *  @brief Convert String to integer
 *
 *  @param value    A pointer to string
 *  @return         Integer
 */
t_u32
a2hex_or_atoi(char *value)
{
	if (value[0] == '0' && (value[1] == 'X' || value[1] == 'x')) {
		return a2hex(value + 2);
	} else {
		return (t_u32)atoi(value);
	}
}

/**
 *  @brief Convert string to hex
 *
 *  @param ptr      A pointer to data buffer
 *  @param chr      A pointer to return integer
 *  @return         A pointer to next data field
 */
char *
convert2hex(char *ptr, t_u8 *chr)
{
	t_u8 val;

	for (val = 0; *ptr && isxdigit(*ptr); ptr++) {
		val = (val * 16) + hexval(*ptr);
	}

	*chr = val;

	return ptr;
}

/**
 *  @brief Check the Hex String
 *  @param s  A pointer to the string
 *  @return   MLAN_STATUS_SUCCESS --HexString, MLAN_STATUS_FAILURE --not HexString
 */
int
ishexstring(char *s)
{
	int ret = MLAN_STATUS_FAILURE;
	t_s32 tmp;

	if (!strncasecmp("0x", s, 2)) {
		s += 2;
	}
	while (*s) {
		tmp = toupper(*s);
		if (((tmp >= 'A') && (tmp <= 'F')) ||
		    ((tmp >= '0') && (tmp <= '9'))) {
			ret = MLAN_STATUS_SUCCESS;
		} else {
			ret = MLAN_STATUS_FAILURE;
			break;
		}
		s++;
	}

	return ret;
}

/**
 *  @brief Convert String to Integer
 *  @param buf      A pointer to the string
 *  @return         Integer
 */
int
atoval(char *buf)
{
	if (!strncasecmp(buf, "0x", 2))
		return a2hex(buf + 2);
	else if (!ishexstring(buf))
		return a2hex(buf);
	else
		return atoi(buf);
}

/**
 *  @brief Display usage
 *
 *  @return       NA
 */
static t_void
display_usage(t_void)
{
	t_u32 i;
	for (i = 0; i < NELEMENTS(usage); i++)
		fprintf(stderr, "%s\n", usage[i]);
}

/**
 *  @brief Find and execute command
 *
 *  @param argc     Number of arguments
 *  @param argv     A pointer to arguments array
 *  @return         MLAN_STATUS_SUCCESS for success, otherwise failure
 */
static int
process_command(int argc, char *argv[])
{
	int i = 0, ret = MLAN_STATUS_NOTFOUND;
	struct command_node *node = NULL;

	for (i = 0; i < (int)NELEMENTS(command_list); i++) {
		node = &command_list[i];
		if (!strcasecmp(node->name, argv[2])) {
			ret = node->handler(argc, argv);
			break;
		}
	}

	return ret;
}

/**
 * @brief Converts a string to hex value
 *
 * @param str      A pointer to the string
 * @param raw      A pointer to the raw data buffer
 * @return         Number of bytes read
 **/
int
string2raw(char *str, unsigned char *raw)
{
	int len = (strlen(str) + 1) / 2;

	do {
		if (!isxdigit(*str)) {
			return -1;
		}
		*str = toupper(*str);
		*raw = CHAR2INT(*str) << 4;
		++str;
		*str = toupper(*str);
		if (*str == '\0')
			break;
		*raw |= CHAR2INT(*str);
		++raw;
	} while (*++str != '\0');
	return len;
}

/**
 *  @brief Prepare command buffer
 *  @param buffer   Command buffer to be filled
 *  @param cmd      Command id
 *  @param num      Number of arguments
 *  @param args     Arguments list
 *  @return         MLAN_STATUS_SUCCESS
 */
static int
prepare_buffer(t_u8 *buffer, char *cmd, t_u32 num, char *args[])
{
	t_u8 *pos = NULL;
	unsigned int i = 0;

	memset(buffer, 0, BUFFER_LENGTH);

	/* Flag it for our use */
	pos = buffer;
	strncpy((char *)pos, CMD_NXP, strlen(CMD_NXP));
	pos += (strlen(CMD_NXP));

	/* Insert command */
	strncpy((char *)pos, (char *)cmd, strlen(cmd));
	pos += (strlen(cmd));

	/* Insert arguments */
	for (i = 0; i < num; i++) {
		strncpy((char *)pos, args[i], strlen(args[i]));
		pos += strlen(args[i]);
		if (i < (num - 1)) {
			strncpy((char *)pos, " ", strlen(" "));
			pos += 1;
		}
	}

	return MLAN_STATUS_SUCCESS;
}

/**
 *  @brief Determine the netlink number
 *
 *  @param i socket number
 *
 *  @return         Netlink number to use
 */
static int
get_netlink_num(int i)
{
	FILE *fp;
	int netlink_num = NETLINK_NXP;
	char str[64];
	char *srch = "netlink_num";
	char filename[64] = { 0 };

	if (i == 0) {
		strcpy(filename, "/proc/mwlan/config");
	} else if (i > 0) {
		sprintf(filename, "/proc/mwlan/config%d", i);
	}
	/* Try to open /proc/mwlan/config$ */
	fp = fopen(filename, "r");
	if (fp) {
		while (!feof(fp)) {
			fgets(str, sizeof(str), fp);
			if (strncmp(str, srch, strlen(srch)) == 0) {
				netlink_num = atoi(str + strlen(srch) + 1);
				break;
			}
		}
		fclose(fp);
	} else {
		return -1;
	}
	return netlink_num;
}

/**
 *  @brief Read event data from netlink socket
 *
 *  @param sk_fd    Netlink socket handler
 *  @param buffer   Pointer to the data buffer
 *  @param nlh      Pointer to netlink message header
 *  @param msg      Pointer to message header
 *
 *  @return         Number of bytes read or MLAN_EVENT_FAILURE
 */
int
read_event_netlink_socket(int sk_fd, unsigned char *buffer,
			  struct nlmsghdr *nlh, struct msghdr *msg)
{
	int count = -1;
	count = recvmsg(sk_fd, msg, 0);
#if DEBUG
	printf("DBG:Waiting for message from NETLINK.\n");
#endif
	if (count < 0) {
		printf("ERR:NETLINK read failed!\n");
		terminate_flag++;
		return MLAN_EVENT_FAILURE;
	}
#if DEBUG
	printf("DBG:Received message payload (%d)\n", count);
#endif
	if (count > NLMSG_SPACE(NL_MAX_PAYLOAD)) {
		printf("ERR:Buffer overflow!\n");
		return MLAN_EVENT_FAILURE;
	}
	memset(buffer, 0, NL_MAX_PAYLOAD);
	memcpy(buffer, NLMSG_DATA(nlh), count - NLMSG_HDRLEN);
#if DEBUG
	hexdump(buffer, count - NLMSG_HDRLEN, ' ');
#endif
	return count - NLMSG_HDRLEN;
}

/**
 *  @brief Configure and read event data from netlink socket
 *
 *  @param sk_fd    Array of netlink sockets
 *  @param no_of_sk Number of netlink sockets opened
 *  @param recv_buf Pointer to the array of evt_buf structures
 *  @param timeout  Socket listen timeout value
 *  @param nlh      Pointer to netlink message header
 *  @param msg      Pointer to message header
 *
 *  @return         Number of bytes read or MLAN_EVENT_FAILURE
 */
int
read_event(int *sk_fd, int no_of_sk, evt_buf *recv_buf, int timeout,
	   struct nlmsghdr *nlh, struct msghdr *msg)
{
	struct timeval tv;
	fd_set rfds;
	int i = 0, max_sk_fd = sk_fd[0];
	int ret = MLAN_EVENT_FAILURE;

	/* Setup read fds */
	FD_ZERO(&rfds);
	for (i = 0; i < no_of_sk; i++) {
		if (sk_fd[i] > max_sk_fd)
			max_sk_fd = sk_fd[i];

		if (sk_fd[i] > 0)
			FD_SET(sk_fd[i], &rfds);
	}

	/* Initialize timeout value */
	if (timeout != 0)
		tv.tv_sec = timeout;
	else
		tv.tv_sec = UAP_RECV_WAIT_DEFAULT;
	tv.tv_usec = 0;

	/* Wait for reply */
	ret = select(max_sk_fd + 1, &rfds, NULL, NULL, &tv);
	if (ret == -1) {
		/* Error */
		terminate_flag++;
		return MLAN_EVENT_FAILURE;
	} else if (!ret) {
		/* Timeout. Try again */
		return MLAN_EVENT_FAILURE;
	}
	for (i = 0; i < no_of_sk; i++) {
		if (sk_fd[i] > 0) {
			if (FD_ISSET(sk_fd[i], &rfds)) {
				/* Success */
				recv_buf[i].flag = 1;
				recv_buf[i].length =
					read_event_netlink_socket(sk_fd[i],
								  recv_buf[i].
								  buffer, nlh,
								  msg);
				ret += recv_buf[i].length;
			}
		}
	}
	return ret;
}

/**
 *  @brief Signal handler
 *
 *  @param sig      Received signal number
 *
 *  @return         N/A
 */
void
sig_handler(int sig)
{
	printf("Stopping application.\n");
	terminate_flag = 1;
}

/**
 * @brief      Wait event specified by event ID, and return back the pointer.
 *
 * @param eventID                     Event ID
 * @param pEvent                   Pointer to the Event buffer
 * @param pEventLen                Pointer to the Event Length
 *
 * @return     MLAN_STATUS_SUCCESS/MLAN_STATUS_FAILURE
 */
static int
wait_event(t_u32 eventID, t_u8 *pEvent, int *pEventLen)
{
	int nl_sk[MAX_NO_OF_DEVICES];
	struct nlmsghdr *nlh = NULL;
	struct sockaddr_nl src_addr, dest_addr;
	struct msghdr msg;
	struct iovec iov;
	evt_buf evt_recv_buf[MAX_NO_OF_DEVICES];
	int num_events = 0;
	event_header *event = NULL;
	int ret = MLAN_EVENT_FAILURE;
	int netlink_num[MAX_NO_OF_DEVICES];
	char if_name[IFNAMSIZ + 1];
	t_u32 event_id = 0;
	int i = 0, no_of_sk = 0;
	int buf_len = 0;

	if (!pEvent || !pEventLen) {
		printf("ERR:Input paramater(s) 'pEvent' or 'pEventLen' is NULL");
		goto done;
	}

	buf_len = *pEventLen;
	*pEventLen = 0;
	/* Currently, we support maximum 4 devices */
	/* TODO: determine no_of_sk at run time */
	no_of_sk = MAX_NO_OF_DEVICES;

	for (i = 0; i < no_of_sk; i++) {
		/* Initialise */
		nl_sk[i] = -1;
		netlink_num[i] = get_netlink_num(i);
		if (netlink_num[i] >= 0) {
			/* Open netlink socket */
			nl_sk[i] = socket(PF_NETLINK, SOCK_RAW, netlink_num[i]);
			if (nl_sk[i] < 0) {
				printf("ERR:Could not open netlink socket.\n");
				ret = MLAN_EVENT_FAILURE;
				goto done;
			}

			/* Set source address */
			memset(&src_addr, 0, sizeof(src_addr));
			src_addr.nl_family = AF_NETLINK;
			src_addr.nl_pid = getpid();	/* Our PID */
			src_addr.nl_groups = NL_MULTICAST_GROUP;

			/* Bind socket with source address */
			if (bind
			    (nl_sk[i], (struct sockaddr *)&src_addr,
			     sizeof(src_addr)) < 0) {
				printf("ERR:Could not bind socket!\n");
				ret = MLAN_EVENT_FAILURE;
				goto done;
			}

			/* Set destination address */
			memset(&dest_addr, 0, sizeof(dest_addr));
			dest_addr.nl_family = AF_NETLINK;
			dest_addr.nl_pid = 0;	/* Kernel */
			dest_addr.nl_groups = NL_MULTICAST_GROUP;

			/* Initialize netlink header */
			nlh = (struct nlmsghdr *)
				malloc(NLMSG_SPACE(NL_MAX_PAYLOAD));
			if (!nlh) {
				printf("ERR: Could not alloc buffer\n");
				ret = MLAN_EVENT_FAILURE;
				goto done;
			}
			memset(nlh, 0, NLMSG_SPACE(NL_MAX_PAYLOAD));

			/* Initialize I/O vector */
			iov.iov_base = (void *)nlh;
			iov.iov_len = NLMSG_SPACE(NL_MAX_PAYLOAD);

			/* Initialize message header */
			memset(&msg, 0, sizeof(struct msghdr));
			msg.msg_name = (void *)&dest_addr;
			msg.msg_namelen = sizeof(dest_addr);
			msg.msg_iov = &iov;
			msg.msg_iovlen = 1;

			memset(&evt_recv_buf[i], 0, sizeof(evt_buf));
		}
	}

	signal(SIGTERM, sig_handler);
	signal(SIGINT, sig_handler);
	signal(SIGALRM, sig_handler);
	while (1) {
		if (terminate_flag) {
			printf("Stopping!\n");
			break;
		}
		ret = read_event(nl_sk, no_of_sk, evt_recv_buf, 0, nlh, &msg);

		/* No result. Loop again */
		if (ret == MLAN_EVENT_FAILURE) {
			continue;
		}
		if (ret == 0) {
			/* Zero bytes received */
			printf("ERR:Received zero bytes!\n");
			continue;
		}
		for (i = 0; i < no_of_sk; i++) {
			if (evt_recv_buf[i].flag == 1) {
				num_events++;

				memcpy(&event_id, evt_recv_buf[i].buffer,
				       sizeof(event_id));
				if (((event_id & 0xFF000000) == 0x80000000) ||
				    ((event_id & 0xFF000000) == 0)) {
					event = (event_header
						 *)(evt_recv_buf[i].buffer);
				} else {
					memset(if_name, 0, IFNAMSIZ + 1);
					memcpy(if_name, evt_recv_buf[i].buffer,
					       IFNAMSIZ);
					event = (event_header
						 *)((t_u8 *)(evt_recv_buf[i].
							     buffer) +
						    IFNAMSIZ);
					ret -= IFNAMSIZ;
					evt_recv_buf[i].length -= IFNAMSIZ;
				}
				if (event->event_id == eventID) {
					if (buf_len > evt_recv_buf[i].length) {
						*pEventLen =
							evt_recv_buf[i].length;
						memcpy(pEvent, (t_u8 *)event,
						       evt_recv_buf[i].length);
					} else {
						printf("ERR:Buffer length exceeded \n");
					}
					goto done;
				}
				/* Reset event flag after reading */
				evt_recv_buf[i].flag = 0;
			}
		}
		fflush(stdout);
	}

done:
	for (i = 0; i < no_of_sk; i++) {
		if (nl_sk[i] > 0)
			close(nl_sk[i]);
	}
	if (nlh)
		free(nlh);
	return 0;

}

/**
 * @brief      Set Robustcoex gpiocfg
 *
 * @param argc Number of arguments
 * @param argv Pointer to the arguments array
 *
 * @return     MLAN_STATUS_SUCCESS/MLAN_STATUS_FAILURE
 */

static int
process_robustcoex(int argc, char *argv[])
{
	t_u8 *buffer = NULL;
	struct eth_priv_cmd *cmd;
	struct ifreq ifr;

	if (argc <= 4) {
		printf("Err: Invalid number of arguments\n");
		printf("Usage: ./mlanutl <interface> robustcoex [gpiocfg] [value]\n");
		return MLAN_STATUS_FAILURE;
	}
	if (strcmp(argv[3], "gpiocfg") == 0) {
		if (argc != 7 && argc != 5) {
			printf("ERR: Invalid number of arguments\n");
			printf("Usage: ./mlanutl <interface> robustcoex gpiocfg [Enable][Gpionum][Gpiopolarity]\n");
			printf("Usage: ./mlanutl <interface> robustcoex gpiocfg [Disable]\n");
			return MLAN_STATUS_FAILURE;
		}
	} else {
		printf("ERR: Invalid arguments\n");
		printf("Usage: ./mlanutl <interface> robustcoex [gpiocfg][value]\n");
		return MLAN_STATUS_FAILURE;
	}
	/* Initialize buffer */
	buffer = (t_u8 *)malloc(BUFFER_LENGTH);
	if (!buffer) {
		printf("ERR:Cannot allocate buffer for command!\n");
		return MLAN_STATUS_FAILURE;
	}

	prepare_buffer(buffer, argv[2], (argc - 3), &argv[3]);
	cmd = (struct eth_priv_cmd *)malloc(sizeof(struct eth_priv_cmd));
	if (!cmd) {
		printf("ERR:Cannot allocate buffer for command!\n");
		free(buffer);
		return MLAN_STATUS_FAILURE;
	}

	/* Fill up buffer */
#ifdef USERSPACE_32BIT_OVER_KERNEL_64BIT
	memset(cmd, 0, sizeof(struct eth_priv_cmd));
	memcpy(&cmd->buf, &buffer, sizeof(buffer));
#else
	cmd->buf = buffer;
#endif
	cmd->used_len = 0;
	cmd->total_len = BUFFER_LENGTH;

	/* Perform IOCTL */
	memset(&ifr, 0, sizeof(struct ifreq));
	strncpy(ifr.ifr_ifrn.ifrn_name, dev_name, strlen(dev_name));
	ifr.ifr_ifru.ifru_data = (void *)cmd;

	if (ioctl(sockfd, MLAN_ETH_PRIV, &ifr)) {
		perror("mlanutl");
		fprintf(stderr, "mlanutl: robustcoex fail\n");
		if (cmd)
			free(cmd);
		if (buffer)
			free(buffer);
		return MLAN_STATUS_FAILURE;
	}

	if (buffer)
		free(buffer);
	if (cmd)
		free(cmd);

	return MLAN_STATUS_SUCCESS;
}

/**
 * @brief      Do acs scan
 *
 * @param argc Number of arguments
 * @param argv Pointer to the arguments array
 *
 * @return     MLAN_STATUS_SUCCESS/MLAN_STATUS_FAILURE
 */

static int
process_acs(int argc, char *argv[])
{
	t_u8 *buffer = NULL;
	struct eth_priv_cmd *cmd;
	struct ifreq ifr;
	acs_result *pacs_result = NULL;
	int i = 0;

	if (argc < 3) {
		printf("Err: Invalid number of arguments\n");
		printf("Usage: ./mlanutl <interface> acs [channels]\n");
		return MLAN_STATUS_FAILURE;
	}
	/* Initialize buffer */
	buffer = (t_u8 *)malloc(BUFFER_LENGTH);
	if (!buffer) {
		printf("ERR:Cannot allocate buffer for command!\n");
		return MLAN_STATUS_FAILURE;
	}

	prepare_buffer(buffer, argv[2], (argc - 3), &argv[3]);
	cmd = (struct eth_priv_cmd *)malloc(sizeof(struct eth_priv_cmd));
	if (!cmd) {
		printf("ERR:Cannot allocate buffer for command!\n");
		free(buffer);
		return MLAN_STATUS_FAILURE;
	}

	/* Fill up buffer */
#ifdef USERSPACE_32BIT_OVER_KERNEL_64BIT
	memset(cmd, 0, sizeof(struct eth_priv_cmd));
	memcpy(&cmd->buf, &buffer, sizeof(buffer));
#else
	cmd->buf = buffer;
#endif
	cmd->used_len = 0;
	cmd->total_len = BUFFER_LENGTH;

	/* Perform IOCTL */
	memset(&ifr, 0, sizeof(struct ifreq));
	strncpy(ifr.ifr_ifrn.ifrn_name, dev_name, strlen(dev_name));
	ifr.ifr_ifru.ifru_data = (void *)cmd;

	if (ioctl(sockfd, MLAN_ETH_PRIV, &ifr)) {
		perror("mlanutl");
		fprintf(stderr, "mlanutl: acs fail\n");
		if (cmd)
			free(cmd);
		if (buffer)
			free(buffer);
		return MLAN_STATUS_FAILURE;
	}

	/* Process result */
	if (cmd->used_len) {
		pacs_result = (acs_result *) buffer;
		printf("Best Channel: %d\n", pacs_result->best_ch);
		if (pacs_result->ch_stats_num) {
			printf("Channel Statistics:\n");
			for (i = 0; i < pacs_result->ch_stats_num; i++)
				printf("\t[CH %d]\t\ttotal_networks=%d\tcca_busy_duration=%d\n", pacs_result->ch_stats[i].chan_num, pacs_result->ch_stats[i].total_networks, pacs_result->ch_stats[i].cca_busy_duration);
		}
	}

	if (buffer)
		free(buffer);
	if (cmd)
		free(cmd);

	return MLAN_STATUS_SUCCESS;
}

/**
 *  @brief Get one line from the File
 *
 *  @param fp       File handler
 *  @param str      Storage location for data.
 *  @param size     Maximum number of characters to read.
 *  @param lineno   A pointer to return current line number
 *  @return         returns string or NULL
 */
char *
mlan_config_get_line(FILE * fp, char *str, t_s32 size, int *lineno)
{
	char *start, *end;
	int out, next_line;

	if (!fp || !str)
		return NULL;

	do {
read_line:
		if (!fgets(str, size, fp))
			break;
		start = str;
		start[size - 1] = '\0';
		end = start + strlen(str);
		(*lineno)++;

		out = 1;
		while (out && (start < end)) {
			next_line = 0;
			/* Remove empty lines and lines starting with # */
			switch (start[0]) {
			case ' ':	/* White space */
			case '\t':	/* Tab */
				start++;
				break;
			case '#':
			case '\n':
			case '\0':
				next_line = 1;
				break;
			case '\r':
				if (start[1] == '\n')
					next_line = 1;
				else
					start++;
				break;
			default:
				out = 0;
				break;
			}
			if (next_line)
				goto read_line;
		}

		/* Remove # comments unless they are within a double quoted
		 * string. Remove trailing white space. */
		end = strstr(start, "\"");
		if (end) {
			end = strstr(end + 1, "\"");
			if (!end)
				end = start;
		} else
			end = start;

		end = strstr(end + 1, "#");
		if (end)
			*end-- = '\0';
		else
			end = start + strlen(start) - 1;

		out = 1;
		while (out && (start < end)) {
			switch (*end) {
			case ' ':	/* White space */
			case '\t':	/* Tab */
			case '\n':
			case '\r':
				*end = '\0';
				end--;
				break;
			default:
				out = 0;
				break;
			}
		}

		if (*start == '\0')
			continue;

		return start;
	} while (1);

	return NULL;
}

/**
 *  @brief          Parse function for a configuration line
 *
 *  @param s        Storage buffer for data
 *  @param size     Maximum size of data
 *  @param stream   File stream pointer
 *  @param line     Pointer to current line within the file
 *  @param _pos     Output string or NULL
 *  @return         String or NULL
 */
static char *
config_get_line(char *s, int size, FILE * stream, int *line, char **_pos)
{
	*_pos = mlan_config_get_line(stream, s, size, line);
	return *_pos;
}

/**
 *  @brief Converts colon separated MAC address to hex value
 *
 *  @param mac      A pointer to the colon separated MAC string
 *  @param raw      A pointer to the hex data buffer
 *  @return         MLAN_STATUS_SUCCESS or MLAN_STATUS_FAILURE
 *                  MAC_BROADCAST   - if broadcast mac
 *                  MAC_MULTICAST   - if multicast mac
 */
static int
mac2raw(char *mac, t_u8 *raw)
{
	unsigned int temp_raw[ETH_ALEN];
	int num_tokens = 0;
	int i;

	if (strlen(mac) != ((2 * ETH_ALEN) + (ETH_ALEN - 1))) {
		return MLAN_STATUS_FAILURE;
	}
	num_tokens = sscanf(mac, "%2x:%2x:%2x:%2x:%2x:%2x",
			    temp_raw + 0, temp_raw + 1, temp_raw + 2,
			    temp_raw + 3, temp_raw + 4, temp_raw + 5);
	if (num_tokens != ETH_ALEN) {
		return MLAN_STATUS_FAILURE;
	}
	for (i = 0; i < num_tokens; i++)
		raw[i] = (t_u8)temp_raw[i];

	if (memcmp(raw, "\xff\xff\xff\xff\xff\xff", ETH_ALEN) == 0) {
		return MAC_BROADCAST;
	} else if (raw[0] & 0x01) {
		return MAC_MULTICAST;
	}
	return MLAN_STATUS_SUCCESS;
}

/**
 *  @brief Parses a command line
 *
 *  @param line     The line to parse
 *  @param args     Pointer to the argument buffer to be filled in
 *  @return         Number of arguments in the line or EOF
 */
static int
parse_line(char *line, char *args[])
{
	int arg_num = 0;
	int is_start = 0;
	int is_quote = 0;
	int length = 0;
	int i = 0;

	arg_num = 0;
	length = strlen(line);
	/* Process line */

	/* Find number of arguments */
	is_start = 0;
	is_quote = 0;
	for (i = 0; i < length; i++) {
		/* Ignore leading spaces */
		if (is_start == 0) {
			if (line[i] == ' ') {
				continue;
			} else if (line[i] == '\t') {
				continue;
			} else if (line[i] == '\n') {
				break;
			} else {
				is_start = 1;
				args[arg_num] = &line[i];
				arg_num++;
			}
		}
		if (is_start == 1) {
			/* Ignore comments */
			if (line[i] == '#') {
				if (is_quote == 0) {
					line[i] = '\0';
					arg_num--;
				}
				break;
			}
			/* Separate by '=' */
			if (line[i] == '=') {
				line[i] = '\0';
				is_start = 0;
				continue;
			}
			/* Separate by ',' */
			if (line[i] == ',') {
				line[i] = '\0';
				is_start = 0;
				continue;
			}
			/* Change ',' to ' ', but not inside quotes */
			if ((line[i] == ',') && (is_quote == 0)) {
				line[i] = ' ';
				continue;
			}
		}
		/* Remove newlines */
		if (line[i] == '\n') {
			line[i] = '\0';
		}
		/* Check for quotes */
		if (line[i] == '"') {
			is_quote = (is_quote == 1) ? 0 : 1;
			continue;
		}
		if (((line[i] == ' ') || (line[i] == '\t')) && (is_quote == 0)) {
			line[i] = '\0';
			is_start = 0;
			continue;
		}
	}
	return arg_num;
}

/**
 *  @brief Process version
 *  @param argc   Number of arguments
 *  @param argv   A pointer to arguments array
 *  @return     MLAN_STATUS_SUCCESS--success, otherwise--fail
 */
static int
process_version(int argc, char *argv[])
{
	t_u8 *buffer = NULL;
	struct eth_priv_cmd *cmd = NULL;
	struct ifreq ifr;

	/* Initialize buffer */
	buffer = (t_u8 *)malloc(BUFFER_LENGTH);
	if (!buffer) {
		printf("ERR:Cannot allocate buffer for command!\n");
		return MLAN_STATUS_FAILURE;
	}

	prepare_buffer(buffer, argv[2], 0, NULL);

	cmd = (struct eth_priv_cmd *)malloc(sizeof(struct eth_priv_cmd));
	if (!cmd) {
		printf("ERR:Cannot allocate buffer for command!\n");
		free(buffer);
		return MLAN_STATUS_FAILURE;
	}

	/* Fill up buffer */
#ifdef USERSPACE_32BIT_OVER_KERNEL_64BIT
	memset(cmd, 0, sizeof(struct eth_priv_cmd));
	memcpy(&cmd->buf, &buffer, sizeof(buffer));
#else
	cmd->buf = buffer;
#endif
	cmd->used_len = 0;
	cmd->total_len = BUFFER_LENGTH;

	/* Perform IOCTL */
	memset(&ifr, 0, sizeof(struct ifreq));
	strncpy(ifr.ifr_ifrn.ifrn_name, dev_name, strlen(dev_name));
	ifr.ifr_ifru.ifru_data = (void *)cmd;

	if (ioctl(sockfd, MLAN_ETH_PRIV, &ifr)) {
		perror("mlanutl");
		fprintf(stderr, "mlanutl: version fail\n");
		if (cmd)
			free(cmd);
		if (buffer)
			free(buffer);
		return MLAN_STATUS_FAILURE;
	}

	/* Process result */
	printf("Version string received: %s\n", buffer);

	if (buffer)
		free(buffer);
	if (cmd)
		free(cmd);

	return MLAN_STATUS_SUCCESS;
}

/**
 *  @brief Process band configuration
 *  @param argc   Number of arguments
 *  @param argv   A pointer to arguments array
 *  @return     MLAN_STATUS_SUCCESS--success, otherwise--fail
 */
static int
process_bandcfg(int argc, char *argv[])
{
	t_u8 *buffer = NULL;
	int i;
	struct eth_priv_cmd *cmd = NULL;
	struct eth_priv_bandcfg *bandcfg = NULL;
	struct ifreq ifr;

	/* Initialize buffer */
	buffer = (t_u8 *)malloc(BUFFER_LENGTH);
	if (!buffer) {
		printf("ERR:Cannot allocate buffer for command!\n");
		return MLAN_STATUS_FAILURE;
	}

	prepare_buffer(buffer, argv[2], (argc - 3), &argv[3]);

	cmd = (struct eth_priv_cmd *)malloc(sizeof(struct eth_priv_cmd));
	if (!cmd) {
		printf("ERR:Cannot allocate buffer for command!\n");
		free(buffer);
		return MLAN_STATUS_FAILURE;
	}

	/* Fill up buffer */
#ifdef USERSPACE_32BIT_OVER_KERNEL_64BIT
	memset(cmd, 0, sizeof(struct eth_priv_cmd));
	memcpy(&cmd->buf, &buffer, sizeof(buffer));
#else
	cmd->buf = buffer;
#endif
	cmd->used_len = 0;
	cmd->total_len = BUFFER_LENGTH;

	/* Perform IOCTL */
	memset(&ifr, 0, sizeof(struct ifreq));
	strncpy(ifr.ifr_ifrn.ifrn_name, dev_name, strlen(dev_name));
	ifr.ifr_ifru.ifru_data = (void *)cmd;

	if (ioctl(sockfd, MLAN_ETH_PRIV, &ifr)) {
		perror("mlanutl");
		fprintf(stderr, "mlanutl: bandcfg fail\n");
		if (cmd)
			free(cmd);
		if (buffer)
			free(buffer);
		return MLAN_STATUS_FAILURE;
	}

	/* Process result */
	bandcfg = (struct eth_priv_bandcfg *)buffer;
	if (argc == 3) {
		/* GET operation */
		printf("Band Configuration:\n");
		printf("  Infra Band: %d (", (int)bandcfg->config_bands);
		for (i = 0; i < 7; i++) {
			if ((bandcfg->config_bands >> i) & 0x1)
				printf(" %s", band[i]);
		}
		printf(" )\n");
		printf("  Adhoc Start Band: %d (",
		       (int)bandcfg->adhoc_start_band);
		for (i = 0; i < 7; i++) {
			if ((bandcfg->adhoc_start_band >> i) & 0x1)
				printf(" %s", band[i]);
		}
		printf(" )\n");
		printf("  Adhoc Start Channel: %d\n",
		       (int)bandcfg->adhoc_channel);
	}

	if (buffer)
		free(buffer);
	if (cmd)
		free(cmd);

	return MLAN_STATUS_SUCCESS;
}

/**
 *  @brief get hostcmd data
 *
 *  @param ln           A pointer to line number
 *  @param buf          A pointer to hostcmd data
 *  @param size         A pointer to the return size of hostcmd buffer
 *  @return             MLAN_STATUS_SUCCESS
 */
static int
mlan_get_hostcmd_data(FILE * fp, int *ln, t_u8 *buf, t_u16 *size)
{
	t_s32 errors = 0, i;
	char line[512], *pos, *pos1, *pos2, *pos3;
	t_u16 len;

	while ((pos = mlan_config_get_line(fp, line, sizeof(line), ln))) {
		(*ln)++;
		if (strcmp(pos, "}") == 0) {
			break;
		}

		pos1 = strchr(pos, ':');
		if (pos1 == NULL) {
			printf("Line %d: Invalid hostcmd line '%s'\n", *ln,
			       pos);
			errors++;
			continue;
		}
		*pos1++ = '\0';

		pos2 = strchr(pos1, '=');
		if (pos2 == NULL) {
			printf("Line %d: Invalid hostcmd line '%s'\n", *ln,
			       pos);
			errors++;
			continue;
		}
		*pos2++ = '\0';

		len = a2hex_or_atoi(pos1);
		if (len < 1 || len > BUFFER_LENGTH) {
			printf("Line %d: Invalid hostcmd line '%s'\n", *ln,
			       pos);
			errors++;
			continue;
		}

		*size += len;

		if (*pos2 == '"') {
			pos2++;
			pos3 = strchr(pos2, '"');
			if (pos3 == NULL) {
				printf("Line %d: invalid quotation '%s'\n", *ln,
				       pos);
				errors++;
				continue;
			}
			*pos3 = '\0';
			memset(buf, 0, len);
			memmove(buf, pos2, MIN(strlen(pos2), len));
			buf += len;
		} else if (*pos2 == '\'') {
			pos2++;
			pos3 = strchr(pos2, '\'');
			if (pos3 == NULL) {
				printf("Line %d: invalid quotation '%s'\n", *ln,
				       pos);
				errors++;
				continue;
			}
			*pos3 = ',';
			for (i = 0; i < len; i++) {
				pos3 = strchr(pos2, ',');
				if (pos3 != NULL) {
					*pos3 = '\0';
					*buf++ = (t_u8)a2hex_or_atoi(pos2);
					pos2 = pos3 + 1;
				} else
					*buf++ = 0;
			}
		} else if (*pos2 == '{') {
			t_u16 tlvlen = 0, tmp_tlvlen;
			mlan_get_hostcmd_data(fp, ln, buf + len, &tlvlen);
			tmp_tlvlen = tlvlen;
			while (len--) {
				*buf++ = (t_u8)(tmp_tlvlen & 0xff);
				tmp_tlvlen >>= 8;
			}
			*size += tlvlen;
			buf += tlvlen;
		} else {
			t_u32 value = a2hex_or_atoi(pos2);
			while (len--) {
				*buf++ = (t_u8)(value & 0xff);
				value >>= 8;
			}
		}
	}
	return MLAN_STATUS_SUCCESS;
}

/**
 *  @brief Prepare host-command buffer
 *  @param fp       File handler
 *  @param cmd_name Command name
 *  @param buf      A pointer to comand buffer
 *  @return         MLAN_STATUS_SUCCESS--success, otherwise--fail
 */
int
prepare_host_cmd_buffer(FILE * fp, char *cmd_name, t_u8 *buf)
{
	char line[256], cmdname[256], *pos, cmdcode[10];
	HostCmd_DS_GEN *hostcmd;
	t_u32 hostcmd_size = 0;
	int ln = 0;
	int cmdname_found = 0, cmdcode_found = 0;

	hostcmd = (HostCmd_DS_GEN *)(buf + sizeof(t_u32));
	hostcmd->command = 0xffff;

	snprintf(cmdname, sizeof(cmdname), "%s={", cmd_name);
	cmdname_found = 0;
	while ((pos = mlan_config_get_line(fp, line, sizeof(line), &ln))) {
		if (strcmp(pos, cmdname) == 0) {
			t_u16 len = 0;
			cmdname_found = 1;
			snprintf(cmdcode, sizeof(cmdcode), "CmdCode=");
			cmdcode_found = 0;
			while ((pos =
				mlan_config_get_line(fp, line, sizeof(line),
						     &ln))) {
				if (strncmp(pos, cmdcode, strlen(cmdcode)) == 0) {
					cmdcode_found = 1;
					hostcmd->command =
						a2hex_or_atoi(pos +
							      strlen(cmdcode));
					hostcmd->size = S_DS_GEN;
					mlan_get_hostcmd_data(fp, &ln,
							      buf +
							      sizeof(t_u32) +
							      hostcmd->size,
							      &len);
					hostcmd->size += len;
					break;
				}
			}
			if (!cmdcode_found) {
				fprintf(stderr,
					"mlanutl: CmdCode not found in conf file\n");
				return MLAN_STATUS_FAILURE;
			}
			break;
		}
	}

	if (!cmdname_found) {
		fprintf(stderr,
			"mlanutl: cmdname '%s' is not found in conf file\n",
			cmd_name);
		return MLAN_STATUS_FAILURE;
	}

	hostcmd->seq_num = 0;
	hostcmd->result = 0;
	hostcmd->command = cpu_to_le16(hostcmd->command);
	hostcmd->size = cpu_to_le16(hostcmd->size);

	hostcmd_size = (t_u32)(hostcmd->size);
	memcpy(buf, (t_u8 *)&hostcmd_size, sizeof(t_u32));

	return MLAN_STATUS_SUCCESS;
}

/**
 *  @brief Prints a MAC address in colon separated form from raw data
 *
 *  @param raw      A pointer to the hex data buffer
 *  @return         N/A
 */
void
print_mac(t_u8 *raw)
{
	printf("%02x:%02x:%02x:%02x:%02x:%02x", (unsigned int)raw[0],
	       (unsigned int)raw[1], (unsigned int)raw[2], (unsigned int)raw[3],
	       (unsigned int)raw[4], (unsigned int)raw[5]);
	return;
}

/**
 *  @brief Process host_cmd response
 *  @param cmd_name Command name
 *  @param buf      A pointer to the response buffer
 *  @return         MLAN_STATUS_SUCCESS--success, otherwise--fail
 */
int
process_host_cmd_resp(char *cmd_name, t_u8 *buf)
{
	t_u32 hostcmd_size = 0;
	HostCmd_DS_GEN *hostcmd = NULL;
	int ret = MLAN_STATUS_SUCCESS;

	buf += strlen(CMD_NXP) + strlen(cmd_name);
	memcpy((t_u8 *)&hostcmd_size, buf, sizeof(t_u32));
	buf += sizeof(t_u32);

	hostcmd = (HostCmd_DS_GEN *)buf;
	hostcmd->command = le16_to_cpu(hostcmd->command);
	hostcmd->size = le16_to_cpu(hostcmd->size);
	hostcmd->seq_num = le16_to_cpu(hostcmd->seq_num);
	hostcmd->result = le16_to_cpu(hostcmd->result);

	hostcmd->command &= ~HostCmd_RET_BIT;
	if (!hostcmd->result) {
		switch (hostcmd->command) {
		case HostCmd_CMD_CFG_DATA:
			{
				HostCmd_DS_802_11_CFG_DATA *pstcfgData =
					(HostCmd_DS_802_11_CFG_DATA *)(buf +
								       S_DS_GEN);
				pstcfgData->data_len =
					le16_to_cpu(pstcfgData->data_len);
				pstcfgData->action =
					le16_to_cpu(pstcfgData->action);

				if (pstcfgData->action == HostCmd_ACT_GEN_GET) {
					hexdump("cfgdata", pstcfgData->data,
						pstcfgData->data_len, ' ');
				}
				break;
			}
		case HostCmd_CMD_802_11_TPC_ADAPT_REQ:
			{
				mlan_ioctl_11h_tpc_resp *tpcIoctlResp =
					(mlan_ioctl_11h_tpc_resp *)(buf +
								    S_DS_GEN);
				if (tpcIoctlResp->status_code == 0) {
					printf("tpcrequest:  txPower(%d), linkMargin(%d), rssi(%d)\n", tpcIoctlResp->tx_power, tpcIoctlResp->link_margin, tpcIoctlResp->rssi);
				} else {
					printf("tpcrequest:  failure, status = %d\n", tpcIoctlResp->status_code);
				}
				break;
			}
		case HostCmd_CMD_802_11_CRYPTO:
			{
				t_u16 alg =
					le16_to_cpu((t_u16)
						    *(buf + S_DS_GEN +
						      sizeof(t_u16)));
				if (alg == CIPHER_TEST_AES_CCM ||
				    alg == CIPHER_TEST_GCMP) {
					HostCmd_DS_802_11_CRYPTO_AES_CCM
						*cmd_aes_ccm =
						(HostCmd_DS_802_11_CRYPTO_AES_CCM
						 *)(buf + S_DS_GEN);

					cmd_aes_ccm->encdec
						=
						le16_to_cpu(cmd_aes_ccm->
							    encdec);
					cmd_aes_ccm->algorithm =
						le16_to_cpu(cmd_aes_ccm->
							    algorithm);
					cmd_aes_ccm->key_length =
						le16_to_cpu(cmd_aes_ccm->
							    key_length);
					cmd_aes_ccm->nonce_length =
						le16_to_cpu(cmd_aes_ccm->
							    nonce_length);
					cmd_aes_ccm->AAD_length =
						le16_to_cpu(cmd_aes_ccm->
							    AAD_length);
					cmd_aes_ccm->data.header.type =
						le16_to_cpu(cmd_aes_ccm->data.
							    header.type);
					cmd_aes_ccm->data.header.len =
						le16_to_cpu(cmd_aes_ccm->data.
							    header.len);

					printf("crypto_result: encdec=%d algorithm=%d, KeyLen=%d," " NonceLen=%d,AADLen=%d,dataLen=%d\n", cmd_aes_ccm->encdec, cmd_aes_ccm->algorithm, cmd_aes_ccm->key_length, cmd_aes_ccm->nonce_length, cmd_aes_ccm->AAD_length, cmd_aes_ccm->data.header.len);

					hexdump("Key", cmd_aes_ccm->key,
						cmd_aes_ccm->key_length, ' ');
					hexdump("Nonce", cmd_aes_ccm->nonce,
						cmd_aes_ccm->nonce_length, ' ');
					hexdump("AAD", cmd_aes_ccm->AAD,
						cmd_aes_ccm->AAD_length, ' ');
					hexdump("Data", cmd_aes_ccm->data.data,
						cmd_aes_ccm->data.header.len,
						' ');
				} else if (alg == CIPHER_TEST_WAPI) {
					HostCmd_DS_802_11_CRYPTO_WAPI *cmd_wapi
						=
						(HostCmd_DS_802_11_CRYPTO_WAPI
						 *) (buf + S_DS_GEN);

					cmd_wapi->encdec
						= le16_to_cpu(cmd_wapi->encdec);
					cmd_wapi->algorithm
						=
						le16_to_cpu(cmd_wapi->
							    algorithm);
					cmd_wapi->key_length =
						le16_to_cpu(cmd_wapi->
							    key_length);
					cmd_wapi->nonce_length =
						le16_to_cpu(cmd_wapi->
							    nonce_length);
					cmd_wapi->AAD_length =
						le16_to_cpu(cmd_wapi->
							    AAD_length);

					printf("crypto_result: encdec=%d algorithm=%d, KeyLen=%d," " NonceLen=%d,AADLen=%d,dataLen=%d\n", cmd_wapi->encdec, cmd_wapi->algorithm, cmd_wapi->key_length, cmd_wapi->nonce_length, cmd_wapi->AAD_length, cmd_wapi->data_length);

					hexdump("Key", cmd_wapi->key,
						cmd_wapi->key_length, ' ');
					hexdump("Nonce", cmd_wapi->nonce,
						cmd_wapi->nonce_length, ' ');
					hexdump("AAD", cmd_wapi->AAD,
						cmd_wapi->AAD_length, ' ');
				} else {
					HostCmd_DS_802_11_CRYPTO *cmd =
						(HostCmd_DS_802_11_CRYPTO *)(buf
									     +
									     S_DS_GEN);
					cmd->encdec = le16_to_cpu(cmd->encdec);
					cmd->algorithm =
						le16_to_cpu(cmd->algorithm);
					cmd->key_IV_length =
						le16_to_cpu(cmd->key_IV_length);
					cmd->key_length =
						le16_to_cpu(cmd->key_length);
					cmd->data.header.type =
						le16_to_cpu(cmd->data.header.
							    type);
					cmd->data.header.len =
						le16_to_cpu(cmd->data.header.
							    len);

					printf("crypto_result: encdec=%d algorithm=%d,KeyIVLen=%d," " KeyLen=%d,dataLen=%d\n", cmd->encdec, cmd->algorithm, cmd->key_IV_length, cmd->key_length, cmd->data.header.len);
					hexdump("KeyIV", cmd->keyIV,
						cmd->key_IV_length, ' ');
					hexdump("Key", cmd->key,
						cmd->key_length, ' ');
					hexdump("Data", cmd->data.data,
						cmd->data.header.len, ' ');
				}
				break;
			}
		case HostCmd_CMD_802_11_AUTO_TX:
			{
				HostCmd_DS_802_11_AUTO_TX *at =
					(HostCmd_DS_802_11_AUTO_TX *)(buf +
								      S_DS_GEN);

				if (le16_to_cpu(at->action) ==
				    HostCmd_ACT_GEN_GET) {
					if (S_DS_GEN + sizeof(at->action) ==
					    hostcmd->size) {
						printf("auto_tx not configured\n");

					} else {
						MrvlIEtypesHeader_t *header =
							&at->auto_tx.header;

						header->type =
							le16_to_cpu(header->
								    type);
						header->len =
							le16_to_cpu(header->
								    len);

						if ((S_DS_GEN +
						     sizeof(at->action)
						     +
						     sizeof(MrvlIEtypesHeader_t)
						     + header->len ==
						     hostcmd->size) &&
						    (header->type ==
						     TLV_TYPE_AUTO_TX)) {

							AutoTx_MacFrame_t *atmf
								=
								&at->auto_tx.
								auto_tx_mac_frame;

							printf("Interval: %d second(s)\n", le16_to_cpu(atmf->interval));
							printf("Priority: %#x\n", atmf->priority);
							printf("Frame Length: %d\n", le16_to_cpu(atmf->frame_len));
							printf("Dest Mac Address: " "%02x:%02x:%02x:%02x:%02x:%02x\n", atmf->dest_mac_addr[0], atmf->dest_mac_addr[1], atmf->dest_mac_addr[2], atmf->dest_mac_addr[3], atmf->dest_mac_addr[4], atmf->dest_mac_addr[5]);
							printf("Src Mac Address: " "%02x:%02x:%02x:%02x:%02x:%02x\n", atmf->src_mac_addr[0], atmf->src_mac_addr[1], atmf->src_mac_addr[2], atmf->src_mac_addr[3], atmf->src_mac_addr[4], atmf->src_mac_addr[5]);

							hexdump("Frame Payload",
								atmf->payload,
								le16_to_cpu
								(atmf->
								 frame_len)
								-
								MLAN_MAC_ADDR_LENGTH
								* 2, ' ');
						} else {
							printf("incorrect auto_tx command response\n");
						}
					}
				}
				break;
			}
		case HostCmd_CMD_802_11_SUBSCRIBE_EVENT:
			{
				HostCmd_DS_802_11_SUBSCRIBE_EVENT *se =
					(HostCmd_DS_802_11_SUBSCRIBE_EVENT
					 *)(buf + S_DS_GEN);
				if (le16_to_cpu(se->action) ==
				    HostCmd_ACT_GEN_GET) {
					int len =
						S_DS_GEN +
						sizeof
						(HostCmd_DS_802_11_SUBSCRIBE_EVENT);
					printf("\nEvent\t\tValue\tFreq\tsubscribed\n\n");
					while (len < hostcmd->size) {
						MrvlIEtypesHeader_t *header =
							(MrvlIEtypesHeader_t
							 *)(buf + len);
						switch (le16_to_cpu
							(header->type)) {
						case TLV_TYPE_RSSI_LOW:
							{
								MrvlIEtypes_RssiThreshold_t
									*low_rssi
									=
									(MrvlIEtypes_RssiThreshold_t
									 *)(buf
									    +
									    len);
								printf("Beacon Low RSSI\t%d\t%d\t%s\n", low_rssi->RSSI_value, low_rssi->RSSI_freq, (le16_to_cpu(se->events) & 0x0001) ? "yes" : "no");
								break;
							}
						case TLV_TYPE_SNR_LOW:
							{
								MrvlIEtypes_SnrThreshold_t
									*low_snr
									=
									(MrvlIEtypes_SnrThreshold_t
									 *)(buf
									    +
									    len);
								printf("Beacon Low SNR\t%d\t%d\t%s\n", low_snr->SNR_value, low_snr->SNR_freq, (le16_to_cpu(se->events) & 0x0002) ? "yes" : "no");
								break;
							}
						case TLV_TYPE_FAILCOUNT:
							{
								MrvlIEtypes_FailureCount_t
									*failure_count
									=
									(MrvlIEtypes_FailureCount_t
									 *)(buf
									    +
									    len);
								printf("Failure Count\t%d\t%d\t%s\n", failure_count->fail_value, failure_count->fail_freq, (le16_to_cpu(se->events) & 0x0004) ? "yes" : "no");
								break;
							}
						case TLV_TYPE_BCNMISS:
							{
								MrvlIEtypes_BeaconsMissed_t
									*bcn_missed
									=
									(MrvlIEtypes_BeaconsMissed_t
									 *)(buf
									    +
									    len);
								printf("Beacon Missed\t%d\tN/A\t%s\n", bcn_missed->beacon_missed, (le16_to_cpu(se->events) & 0x0008) ? "yes" : "no");
								break;
							}
						case TLV_TYPE_RSSI_HIGH:
							{
								MrvlIEtypes_RssiThreshold_t
									*high_rssi
									=
									(MrvlIEtypes_RssiThreshold_t
									 *)(buf
									    +
									    len);
								printf("Bcn High RSSI\t%d\t%d\t%s\n", high_rssi->RSSI_value, high_rssi->RSSI_freq, (le16_to_cpu(se->events) & 0x0010) ? "yes" : "no");
								break;
							}

						case TLV_TYPE_SNR_HIGH:
							{
								MrvlIEtypes_SnrThreshold_t
									*high_snr
									=
									(MrvlIEtypes_SnrThreshold_t
									 *)(buf
									    +
									    len);
								printf("Beacon High SNR\t%d\t%d\t%s\n", high_snr->SNR_value, high_snr->SNR_freq, (le16_to_cpu(se->events) & 0x0020) ? "yes" : "no");
								break;
							}
						case TLV_TYPE_RSSI_LOW_DATA:
							{
								MrvlIEtypes_RssiThreshold_t
									*low_rssi
									=
									(MrvlIEtypes_RssiThreshold_t
									 *)(buf
									    +
									    len);
								printf("Data Low RSSI\t%d\t%d\t%s\n", low_rssi->RSSI_value, low_rssi->RSSI_freq, (le16_to_cpu(se->events) & 0x0040) ? "yes" : "no");
								break;
							}
						case TLV_TYPE_SNR_LOW_DATA:
							{
								MrvlIEtypes_SnrThreshold_t
									*low_snr
									=
									(MrvlIEtypes_SnrThreshold_t
									 *)(buf
									    +
									    len);
								printf("Data Low SNR\t%d\t%d\t%s\n", low_snr->SNR_value, low_snr->SNR_freq, (le16_to_cpu(se->events) & 0x0080) ? "yes" : "no");
								break;
							}
						case TLV_TYPE_RSSI_HIGH_DATA:
							{
								MrvlIEtypes_RssiThreshold_t
									*high_rssi
									=
									(MrvlIEtypes_RssiThreshold_t
									 *)(buf
									    +
									    len);
								printf("Data High RSSI\t%d\t%d\t%s\n", high_rssi->RSSI_value, high_rssi->RSSI_freq, (le16_to_cpu(se->events) & 0x0100) ? "yes" : "no");
								break;
							}
						case TLV_TYPE_SNR_HIGH_DATA:
							{
								MrvlIEtypes_SnrThreshold_t
									*high_snr
									=
									(MrvlIEtypes_SnrThreshold_t
									 *)(buf
									    +
									    len);
								printf("Data High SNR\t%d\t%d\t%s\n", high_snr->SNR_value, high_snr->SNR_freq, (le16_to_cpu(se->events) & 0x0200) ? "yes" : "no");
								break;
							}
						case TLV_TYPE_LINK_QUALITY:
							{
								MrvlIEtypes_LinkQuality_t
									*link_qual
									=
									(MrvlIEtypes_LinkQuality_t
									 *)(buf
									    +
									    len);
								printf("Link Quality Parameters:\n");
								printf("------------------------\n");
								printf("Link Quality Event Subscribed\t%s\n", (le16_to_cpu(se->events) & 0x0400) ? "yes" : "no");
								printf("Link SNR Threshold   = %d\n", le16_to_cpu(link_qual->link_SNR_thrs));
								printf("Link SNR Frequency   = %d\n", le16_to_cpu(link_qual->link_SNR_freq));
								printf("Min Rate Value       = %d\n", le16_to_cpu(link_qual->min_rate_val));
								printf("Min Rate Frequency   = %d\n", le16_to_cpu(link_qual->min_rate_freq));
								printf("Tx Latency Value     = %d\n", le32_to_cpu(link_qual->tx_latency_val));
								printf("Tx Latency Threshold = %d\n", le32_to_cpu(link_qual->tx_latency_thrs));

								break;
							}
						case TLV_TYPE_PRE_BEACON_LOST:
							{
								MrvlIEtypes_PreBeaconLost_t
									*pre_bcn_lost
									=
									(MrvlIEtypes_PreBeaconLost_t
									 *)(buf
									    +
									    len);
								printf("------------------------\n");
								printf("Pre-Beacon Lost Event Subscribed\t%s\n", (le16_to_cpu(se->events) & 0x0800) ? "yes" : "no");
								printf("Pre-Beacon Lost: %d\n", pre_bcn_lost->pre_beacon_lost);
								break;
							}
						default:
							printf("Unknown subscribed event TLV Type=%#x," " Len=%d\n", le16_to_cpu(header->type), le16_to_cpu(header->len));
							break;
						}

						len += (sizeof
							(MrvlIEtypesHeader_t)
							+
							le16_to_cpu(header->
								    len));
					}
				}
				break;
			}
		case HostCmd_CMD_MAC_REG_ACCESS:
		case HostCmd_CMD_BBP_REG_ACCESS:
		case HostCmd_CMD_RF_REG_ACCESS:
		case HostCmd_CMD_CAU_REG_ACCESS:
			{
				HostCmd_DS_REG *preg =
					(HostCmd_DS_REG *)(buf + S_DS_GEN);
				preg->action = le16_to_cpu(preg->action);
				if (preg->action == HostCmd_ACT_GEN_GET) {
					preg->value = le32_to_cpu(preg->value);
					printf("value = 0x%08x\n", preg->value);
				}
				break;
			}
		case HostCmd_CMD_MEM_ACCESS:
			{
				HostCmd_DS_MEM *pmem =
					(HostCmd_DS_MEM *)(buf + S_DS_GEN);
				pmem->action = le16_to_cpu(pmem->action);
				if (pmem->action == HostCmd_ACT_GEN_GET) {
					pmem->value = le32_to_cpu(pmem->value);
					printf("value = 0x%08x\n", pmem->value);
				}
				break;
			}
		case HostCmd_CMD_LINK_STATS_SUMMARY:
			{
				HostCmd_DS_LINK_STATS_SUMMARY *linkstats =
					(HostCmd_DS_LINK_STATS_SUMMARY *)(buf +
									  S_DS_GEN);
				/* GET operation */
				printf("Link Statistics: \n");
				/* format */
				printf("Duration:   %u\n",
				       (int)le32_to_cpu(linkstats->
							timeSinceLastQuery_ms));

				printf("Beacon count:     %u\n",
				       le16_to_cpu(linkstats->bcnCnt));
				printf("Beacon missing:   %u\n",
				       le16_to_cpu(linkstats->bcnMiss));
				printf("Beacon RSSI avg:  %d\n",
				       le16_to_cpu(linkstats->bcnRssiAvg));
				printf("Beacon SNR avg:   %d\n",
				       le16_to_cpu(linkstats->bcnSnrAvg));

				printf("Rx packets:       %u\n",
				       (int)le32_to_cpu(linkstats->rxPkts));
				printf("Rx RSSI avg:      %d\n",
				       le16_to_cpu(linkstats->rxRssiAvg));
				printf("Rx SNR avg:       %d\n",
				       le16_to_cpu(linkstats->rxSnrAvg));

				printf("Tx packets:       %u\n",
				       (int)le32_to_cpu(linkstats->txPkts));
				printf("Tx Attempts:      %u\n",
				       (int)le32_to_cpu(linkstats->txAttempts));
				printf("Tx Failures:      %u\n",
				       (int)le32_to_cpu(linkstats->txFailures));
				printf("Tx Initial Rate:  %s\n",
				       rateIdStr[linkstats->txInitRate]);

				printf("Tx AC VO:         %u [ %u ]\n",
				       le16_to_cpu(linkstats->
						   txQueuePktCnt[WMM_AC_VO]),
				       (int)le32_to_cpu(linkstats->
							txQueueDelay[WMM_AC_VO])
				       / 1000);
				printf("Tx AC VI:         %u [ %u ]\n",
				       le16_to_cpu(linkstats->
						   txQueuePktCnt[WMM_AC_VI]),
				       (int)le32_to_cpu(linkstats->
							txQueueDelay[WMM_AC_VI])
				       / 1000);
				printf("Tx AC BE:         %u [ %u ]\n",
				       le16_to_cpu(linkstats->
						   txQueuePktCnt[WMM_AC_BE]),
				       (int)le32_to_cpu(linkstats->
							txQueueDelay[WMM_AC_BE])
				       / 1000);
				printf("Tx AC BK:         %u [ %u ]\n",
				       le16_to_cpu(linkstats->
						   txQueuePktCnt[WMM_AC_BK]),
				       (int)le32_to_cpu(linkstats->
							txQueueDelay[WMM_AC_BK])
				       / 1000);
				break;
			}
		case HostCmd_CMD_WMM_PARAM_CONFIG:
			{
				HostCmd_DS_WMM_PARAM_CONFIG *wmm_param =
					(HostCmd_DS_WMM_PARAM_CONFIG *) (buf +
									 S_DS_GEN);
				printf("WMM Params: \n");
				printf("\tBE: AIFSN=%d, CW_MAX=%d CW_MIN=%d, TXOP=%d\n", wmm_param->ac_params[AC_BE].aci_aifsn.aifsn, wmm_param->ac_params[AC_BE].ecw.ecw_max, wmm_param->ac_params[AC_BE].ecw.ecw_min, le16_to_cpu(wmm_param->ac_params[AC_BE].tx_op_limit));
				printf("\tBK: AIFSN=%d, CW_MAX=%d CW_MIN=%d, TXOP=%d\n", wmm_param->ac_params[AC_BK].aci_aifsn.aifsn, wmm_param->ac_params[AC_BK].ecw.ecw_max, wmm_param->ac_params[AC_BK].ecw.ecw_min, le16_to_cpu(wmm_param->ac_params[AC_BK].tx_op_limit));
				printf("\tVI: AIFSN=%d, CW_MAX=%d CW_MIN=%d, TXOP=%d\n", wmm_param->ac_params[AC_VI].aci_aifsn.aifsn, wmm_param->ac_params[AC_VI].ecw.ecw_max, wmm_param->ac_params[AC_VI].ecw.ecw_min, le16_to_cpu(wmm_param->ac_params[AC_VI].tx_op_limit));
				printf("\tVO: AIFSN=%d, CW_MAX=%d CW_MIN=%d, TXOP=%d\n", wmm_param->ac_params[AC_VO].aci_aifsn.aifsn, wmm_param->ac_params[AC_VO].ecw.ecw_max, wmm_param->ac_params[AC_VO].ecw.ecw_min, le16_to_cpu(wmm_param->ac_params[AC_VO].tx_op_limit));
				break;
			}
		default:
			printf("HOSTCMD_RESP: CmdCode=%#04x, Size=%#04x,"
			       " SeqNum=%#04x, Result=%#04x\n",
			       hostcmd->command, hostcmd->size,
			       hostcmd->seq_num, hostcmd->result);
			hexdump("payload",
				(t_void *)(buf + S_DS_GEN),
				hostcmd->size - S_DS_GEN, ' ');
			break;
		}
	} else {
		printf("HOSTCMD failed: CmdCode=%#04x, Size=%#04x,"
		       " SeqNum=%#04x, Result=%#04x\n",
		       hostcmd->command, hostcmd->size,
		       hostcmd->seq_num, hostcmd->result);
	}
	return ret;
}

/**
 *  @brief Trims leading and traling spaces only
 *  @param str  A pointer to argument string
 *  @return     pointer to trimmed string
 */
char *
trim_spaces(char *str)
{
	char *str_end = NULL;

	if (!str)
		return NULL;

	/* Trim leading spaces */
	while (!*str && isspace(*str))
		str++;

	if (*str == 0)		/* All spaces? */
		return str;

	/* Trim trailing spaces */
	str_end = str + strlen(str) - 1;
	while (str_end > str && isspace(*str_end))
		str_end--;

	/* null terminate the string */
	*(str_end + 1) = '\0';

	return str;
}

/**
 *  @brief Process hostcmd command
 *  @param argc   Number of arguments
 *  @param argv   A pointer to arguments array
 *  @return     MLAN_STATUS_SUCCESS--success, otherwise--fail
 */
static int
process_hostcmd(int argc, char *argv[])
{
	t_u8 *buffer = NULL, *raw_buf = NULL;
	struct eth_priv_cmd *cmd = NULL;
	struct ifreq ifr;
	FILE *fp = NULL;
	FILE *fp_raw = NULL;
	FILE *fp_dtsi = NULL;
	char cmdname[256];
	boolean call_ioctl = TRUE;
	t_u32 buf_len = 0, i, j, k;
	char *line = NULL, *pos = NULL;
	int li = 0, blk_count = 0, ob = 0;
	int ret = MLAN_STATUS_SUCCESS;

	struct cmd_node {
		char cmd_string[256];
		struct cmd_node *next;
	};
	struct cmd_node *command = NULL, *header = NULL, *new_node = NULL;

	if (argc < 5) {
		printf("Error: invalid no of arguments\n");
		printf("Syntax: ./mlanutl mlanX hostcmd <hostcmd.conf> <cmdname>\n");
		ret = MLAN_STATUS_FAILURE;
		goto done;
	}

	snprintf(cmdname, sizeof(cmdname), "%s", argv[4]);

	if (!strcmp(cmdname, "generate_raw")) {
		call_ioctl = FALSE;
	}

	if (!call_ioctl && argc != 6) {
		printf("Error: invalid no of arguments\n");
		printf("Syntax: ./mlanutl mlanX hostcmd <hostcmd.conf> %s <raw_data_file>\n", cmdname);
		ret = MLAN_STATUS_FAILURE;
		goto done;
	}

	fp = fopen(argv[3], "r");
	if (fp == NULL) {
		fprintf(stderr, "Cannot open file %s\n", argv[3]);
		ret = MLAN_STATUS_FAILURE;
		goto done;
	}

	/* Initialize buffer */
	buffer = (t_u8 *)malloc(BUFFER_LENGTH);
	if (!buffer) {
		printf("ERR:Cannot allocate buffer for command!\n");
		fclose(fp);
		ret = MLAN_STATUS_FAILURE;
		goto done;
	}
	memset(buffer, 0, BUFFER_LENGTH);

	if (call_ioctl) {
		/* Prepare the hostcmd buffer */
		prepare_buffer(buffer, argv[2], 0, NULL);
		if (MLAN_STATUS_FAILURE ==
		    prepare_host_cmd_buffer(fp, cmdname,
					    buffer + strlen(CMD_NXP) +
					    strlen(argv[2]))) {
			fclose(fp);
			ret = MLAN_STATUS_FAILURE;
			goto done;
		}
		fclose(fp);
	} else {
		line = (char *)malloc(MAX_CONFIG_LINE);
		if (!line) {
			printf("ERR:Cannot allocate memory for line\n");
			fclose(fp);
			ret = MLAN_STATUS_FAILURE;
			goto done;
		}
		memset(line, 0, MAX_CONFIG_LINE);

		while (config_get_line(line, MAX_CONFIG_LINE, fp, &li, &pos)) {
			line = trim_spaces(line);
			if (line[strlen(line) - 1] == '{') {
				if (ob == 0) {
					new_node =
						(struct cmd_node *)
						malloc(sizeof(struct cmd_node));
					if (!new_node) {
						printf("ERR:Cannot allocate memory for cmd_node\n");
						fclose(fp);
						ret = MLAN_STATUS_FAILURE;
						goto done;
					}
					memset(new_node, 0,
					       sizeof(struct cmd_node));
					new_node->next = NULL;
					if (blk_count == 0) {
						header = new_node;
						command = new_node;
					} else {
						command->next = new_node;
						command = new_node;
					}
					strncpy(command->cmd_string, line,
						(strchr(line, '=') - line));
					memmove(command->cmd_string,
						trim_spaces(command->
							    cmd_string),
						strlen(trim_spaces
						       (command->cmd_string)) +
						1);
				}
				ob++;
				continue;	/* goto while() */
			}
			if (line[strlen(line) - 1] == '}') {
				ob--;
				if (ob == 0)
					blk_count++;
				continue;	/* goto while() */
			}
		}

		rewind(fp);	/* Set the source file pointer to the beginning again */
		command = header;	/* Set 'command' at the beginning of the command list */

		fp_raw = fopen(argv[5], "w");
		if (fp_raw == NULL) {
			fprintf(stderr,
				"Cannot open the destination raw_data file %s\n",
				argv[5]);
			fclose(fp);
			ret = MLAN_STATUS_FAILURE;
			goto done;
		}

		/* prepare .dtsi output */
		snprintf(cmdname, sizeof(cmdname), "%s.dtsi", argv[5]);
		fp_dtsi = fopen(cmdname, "w");
		if (fp_dtsi == NULL) {
			fprintf(stderr, "Cannot open the destination file %s\n",
				cmdname);
			fclose(fp);
			fclose(fp_raw);
			ret = MLAN_STATUS_FAILURE;
			goto done;
		}

		for (k = 0; k < blk_count && command != NULL; k++) {
			if (MLAN_STATUS_FAILURE ==
			    prepare_host_cmd_buffer(fp, command->cmd_string,
						    buffer))
				memset(buffer, 0, BUFFER_LENGTH);

			memcpy(&buf_len, buffer, sizeof(t_u32));
			if (buf_len) {
				raw_buf = buffer + sizeof(t_u32);	/* raw_buf points to start of actual <raw data> */
				printf("buf_len = %d\n", (int)buf_len);
				if (k > 0)
					fprintf(fp_raw, "\n\n");
				fprintf(fp_raw, "%s={\n", command->cmd_string);
				fprintf(fp_dtsi,
					"/ {\n\tnxp_cfgdata {\n\t\tnxp,%s = /bits/ 8 <\n",
					command->cmd_string);
				i = j = 0;
				while (i < buf_len) {
					for (j = 0; j < 16; j++) {
						fprintf(fp_raw, "%02x ",
							*(raw_buf + i));
						if (i >= 8) {
							fprintf(fp_dtsi,
								"0x%02x",
								*(raw_buf + i));
							if ((j < 16 - 1) &&
							    (i < buf_len - 1))
								fprintf(fp_dtsi,
									" ");
						}
						if (++i >= buf_len)
							break;
					}
					fputc('\n', fp_raw);
					fputc('\n', fp_dtsi);
				}
				fprintf(fp_raw, "}");
				fprintf(fp_dtsi, "\t\t>;\n\t};\n};\n");
			}
			command = command->next;
			rewind(fp);
		}

		fclose(fp_dtsi);
		fclose(fp_raw);
		fclose(fp);
	}

	if (call_ioctl) {
		cmd = (struct eth_priv_cmd *)
			malloc(sizeof(struct eth_priv_cmd));
		if (!cmd) {
			printf("ERR:Cannot allocate buffer for command!\n");
			ret = MLAN_STATUS_FAILURE;
			goto done;
		}

		/* Fill up buffer */
#ifdef USERSPACE_32BIT_OVER_KERNEL_64BIT
		memset(cmd, 0, sizeof(struct eth_priv_cmd));
		memcpy(&cmd->buf, &buffer, sizeof(buffer));
#else
		cmd->buf = buffer;
#endif
		cmd->used_len = 0;
		cmd->total_len = BUFFER_LENGTH;

		/* Perform IOCTL */
		memset(&ifr, 0, sizeof(struct ifreq));
		strncpy(ifr.ifr_ifrn.ifrn_name, dev_name, strlen(dev_name));
		ifr.ifr_ifru.ifru_data = (void *)cmd;

		if (ioctl(sockfd, MLAN_ETH_PRIV, &ifr)) {
			perror("mlanutl");
			fprintf(stderr, "mlanutl: hostcmd fail\n");
			ret = MLAN_STATUS_FAILURE;
			goto done;
		}

		/* Process result */
		process_host_cmd_resp(argv[2], buffer);
	}

done:
	while (header) {
		command = header;
		header = header->next;
		free(command);
	}
	if (line)
		free(line);
	if (buffer)
		free(buffer);
	if (cmd)
		free(cmd);

	return ret;
}

/**
 *  @brief Process HT Tx configuration
 *  @param argc   Number of arguments
 *  @param argv   A pointer to arguments array
 *  @return     MLAN_STATUS_SUCCESS--success, otherwise--fail
 */
static int
process_httxcfg(int argc, char *argv[])
{
	t_u8 *buffer = NULL;
	t_u32 *data = NULL;
	struct eth_priv_cmd *cmd = NULL;
	struct ifreq ifr;

	/* Initialize buffer */
	buffer = (t_u8 *)malloc(BUFFER_LENGTH);
	if (!buffer) {
		printf("ERR:Cannot allocate buffer for command!\n");
		return MLAN_STATUS_FAILURE;
	}

	prepare_buffer(buffer, argv[2], (argc - 3), &argv[3]);

	cmd = (struct eth_priv_cmd *)malloc(sizeof(struct eth_priv_cmd));
	if (!cmd) {
		printf("ERR:Cannot allocate buffer for command!\n");
		free(buffer);
		return MLAN_STATUS_FAILURE;
	}

	/* Fill up buffer */
#ifdef USERSPACE_32BIT_OVER_KERNEL_64BIT
	memset(cmd, 0, sizeof(struct eth_priv_cmd));
	memcpy(&cmd->buf, &buffer, sizeof(buffer));
#else
	cmd->buf = buffer;
#endif
	cmd->used_len = 0;
	cmd->total_len = BUFFER_LENGTH;

	/* Perform IOCTL */
	memset(&ifr, 0, sizeof(struct ifreq));
	strncpy(ifr.ifr_ifrn.ifrn_name, dev_name, strlen(dev_name));
	ifr.ifr_ifru.ifru_data = (void *)cmd;

	if (ioctl(sockfd, MLAN_ETH_PRIV, &ifr)) {
		perror("mlanutl");
		fprintf(stderr, "mlanutl: httxcfg fail\n");
		if (cmd)
			free(cmd);
		if (buffer)
			free(buffer);
		return MLAN_STATUS_FAILURE;
	}

	if (argc == 3) {
		/* Get result */
		data = (t_u32 *)buffer;
		printf("HT Tx cfg: \n");
		printf("    BG band:  0x%08x\n", data[0]);
		printf("     A band:  0x%08x\n", data[1]);
	}

	if (buffer)
		free(buffer);
	if (cmd)
		free(cmd);

	return MLAN_STATUS_SUCCESS;
}

/**
 *  @brief Process HT capability configuration
 *  @param argc   Number of arguments
 *  @param argv   A pointer to arguments array
 *  @return     MLAN_STATUS_SUCCESS--success, otherwise--fail
 */
static int
process_htcapinfo(int argc, char *argv[])
{
	t_u8 *buffer = NULL;
	struct eth_priv_cmd *cmd = NULL;
	struct eth_priv_htcapinfo *ht_cap = NULL;
	struct ifreq ifr;

	/* Initialize buffer */
	buffer = (t_u8 *)malloc(BUFFER_LENGTH);
	if (!buffer) {
		printf("ERR:Cannot allocate buffer for command!\n");
		return MLAN_STATUS_FAILURE;
	}

	prepare_buffer(buffer, argv[2], (argc - 3), &argv[3]);

	cmd = (struct eth_priv_cmd *)malloc(sizeof(struct eth_priv_cmd));
	if (!cmd) {
		printf("ERR:Cannot allocate buffer for command!\n");
		free(buffer);
		return MLAN_STATUS_FAILURE;
	}

	/* Fill up buffer */
#ifdef USERSPACE_32BIT_OVER_KERNEL_64BIT
	memset(cmd, 0, sizeof(struct eth_priv_cmd));
	memcpy(&cmd->buf, &buffer, sizeof(buffer));
#else
	cmd->buf = buffer;
#endif
	cmd->used_len = 0;
	cmd->total_len = BUFFER_LENGTH;

	/* Perform IOCTL */
	memset(&ifr, 0, sizeof(struct ifreq));
	strncpy(ifr.ifr_ifrn.ifrn_name, dev_name, strlen(dev_name));
	ifr.ifr_ifru.ifru_data = (void *)cmd;

	if (ioctl(sockfd, MLAN_ETH_PRIV, &ifr)) {
		perror("mlanutl");
		fprintf(stderr, "mlanutl: htcapinfo fail\n");
		if (cmd)
			free(cmd);
		if (buffer)
			free(buffer);
		return MLAN_STATUS_FAILURE;
	}

	/* Process result */
	if (argc == 3) {
		ht_cap = (struct eth_priv_htcapinfo *)buffer;
		printf("HT cap info: \n");
		printf("    BG band:  0x%08x\n", ht_cap->ht_cap_info_bg);
		printf("     A band:  0x%08x\n", ht_cap->ht_cap_info_a);
	}

	if (buffer)
		free(buffer);
	if (cmd)
		free(cmd);

	return MLAN_STATUS_SUCCESS;
}

/**
 *  @brief Process HT Add BA parameters
 *  @param argc   Number of arguments
 *  @param argv   A pointer to arguments array
 *  @return     MLAN_STATUS_SUCCESS--success, otherwise--fail
 */
static int
process_addbapara(int argc, char *argv[])
{
	t_u8 *buffer = NULL;
	struct eth_priv_cmd *cmd = NULL;
	struct ifreq ifr;
	struct eth_priv_addba *addba = NULL;

	/* Initialize buffer */
	buffer = (t_u8 *)malloc(BUFFER_LENGTH);
	if (!buffer) {
		printf("ERR:Cannot allocate buffer for command!\n");
		return MLAN_STATUS_FAILURE;
	}

	prepare_buffer(buffer, argv[2], (argc - 3), &argv[3]);

	cmd = (struct eth_priv_cmd *)malloc(sizeof(struct eth_priv_cmd));
	if (!cmd) {
		printf("ERR:Cannot allocate buffer for command!\n");
		free(buffer);
		return MLAN_STATUS_FAILURE;
	}

	/* Fill up buffer */
#ifdef USERSPACE_32BIT_OVER_KERNEL_64BIT
	memset(cmd, 0, sizeof(struct eth_priv_cmd));
	memcpy(&cmd->buf, &buffer, sizeof(buffer));
#else
	cmd->buf = buffer;
#endif
	cmd->used_len = 0;
	cmd->total_len = BUFFER_LENGTH;

	/* Perform IOCTL */
	memset(&ifr, 0, sizeof(struct ifreq));
	strncpy(ifr.ifr_ifrn.ifrn_name, dev_name, strlen(dev_name));
	ifr.ifr_ifru.ifru_data = (void *)cmd;

	if (ioctl(sockfd, MLAN_ETH_PRIV, &ifr)) {
		perror("mlanutl");
		fprintf(stderr, "mlanutl: addbapara fail\n");
		if (cmd)
			free(cmd);
		if (buffer)
			free(buffer);
		return MLAN_STATUS_FAILURE;
	}

	if (argc == 3) {
		/* Get */
		addba = (struct eth_priv_addba *)buffer;
		printf("Add BA configuration: \n");
		printf("    Time out : %d\n", addba->time_out);
		printf("    TX window: %d\n", addba->tx_win_size);
		printf("    RX window: %d\n", addba->rx_win_size);
		printf("    TX AMSDU : %d\n", addba->tx_amsdu);
		printf("    RX AMSDU : %d\n", addba->rx_amsdu);
	}

	if (buffer)
		free(buffer);
	if (cmd)
		free(cmd);

	return MLAN_STATUS_SUCCESS;
}

/**
 *  @brief Process Aggregation priority table parameters
 *  @param argc   Number of arguments
 *  @param argv   A pointer to arguments array
 *  @return     MLAN_STATUS_SUCCESS--success, otherwise--fail
 */
static int
process_aggrpriotbl(int argc, char *argv[])
{
	t_u8 *buffer = NULL;
	struct eth_priv_cmd *cmd = NULL;
	struct ifreq ifr;
	int i;

	/* Initialize buffer */
	buffer = (t_u8 *)malloc(BUFFER_LENGTH);
	if (!buffer) {
		printf("ERR:Cannot allocate buffer for command!\n");
		return MLAN_STATUS_FAILURE;
	}

	prepare_buffer(buffer, argv[2], (argc - 3), &argv[3]);

	cmd = (struct eth_priv_cmd *)malloc(sizeof(struct eth_priv_cmd));
	if (!cmd) {
		printf("ERR:Cannot allocate buffer for command!\n");
		free(buffer);
		return MLAN_STATUS_FAILURE;
	}

	/* Fill up buffer */
#ifdef USERSPACE_32BIT_OVER_KERNEL_64BIT
	memset(cmd, 0, sizeof(struct eth_priv_cmd));
	memcpy(&cmd->buf, &buffer, sizeof(buffer));
#else
	cmd->buf = buffer;
#endif
	cmd->used_len = 0;
	cmd->total_len = BUFFER_LENGTH;

	/* Perform IOCTL */
	memset(&ifr, 0, sizeof(struct ifreq));
	strncpy(ifr.ifr_ifrn.ifrn_name, dev_name, strlen(dev_name));
	ifr.ifr_ifru.ifru_data = (void *)cmd;

	if (ioctl(sockfd, MLAN_ETH_PRIV, &ifr)) {
		perror("mlanutl");
		fprintf(stderr, "mlanutl: aggrpriotbl fail\n");
		if (cmd)
			free(cmd);
		if (buffer)
			free(buffer);
		return MLAN_STATUS_FAILURE;
	}

	if (argc == 3) {
		/* Get */
		printf("Aggregation priority table cfg: \n");
		printf("    TID      AMPDU      AMSDU \n");
		for (i = 0; i < MAX_NUM_TID; i++) {
			printf("     %d        %3d        %3d \n",
			       i, buffer[2 * i], buffer[2 * i + 1]);
		}
	}

	if (buffer)
		free(buffer);
	if (cmd)
		free(cmd);

	return MLAN_STATUS_SUCCESS;
}

/**
 *  @brief Process HT Add BA reject configurations
 *  @param argc   Number of arguments
 *  @param argv   A pointer to arguments array
 *  @return     MLAN_STATUS_SUCCESS--success, otherwise--fail
 */
static int
process_addbareject(int argc, char *argv[])
{
	t_u8 *buffer = NULL;
	struct eth_priv_cmd *cmd = NULL;
	struct ifreq ifr;
	int i;

	/* Initialize buffer */
	buffer = (t_u8 *)malloc(BUFFER_LENGTH);
	if (!buffer) {
		printf("ERR:Cannot allocate buffer for command!\n");
		return MLAN_STATUS_FAILURE;
	}

	prepare_buffer(buffer, argv[2], (argc - 3), &argv[3]);

	cmd = (struct eth_priv_cmd *)malloc(sizeof(struct eth_priv_cmd));
	if (!cmd) {
		printf("ERR:Cannot allocate buffer for command!\n");
		free(buffer);
		return MLAN_STATUS_FAILURE;
	}

	/* Fill up buffer */
#ifdef USERSPACE_32BIT_OVER_KERNEL_64BIT
	memset(cmd, 0, sizeof(struct eth_priv_cmd));
	memcpy(&cmd->buf, &buffer, sizeof(buffer));
#else
	cmd->buf = buffer;
#endif
	cmd->used_len = 0;
	cmd->total_len = BUFFER_LENGTH;

	/* Perform IOCTL */
	memset(&ifr, 0, sizeof(struct ifreq));
	strncpy(ifr.ifr_ifrn.ifrn_name, dev_name, strlen(dev_name));
	ifr.ifr_ifru.ifru_data = (void *)cmd;

	if (ioctl(sockfd, MLAN_ETH_PRIV, &ifr)) {
		perror("mlanutl");
		fprintf(stderr, "mlanutl: addbareject fail\n");
		if (cmd)
			free(cmd);
		if (buffer)
			free(buffer);
		return MLAN_STATUS_FAILURE;
	}

	if (argc == 3) {
		/* Get */
		printf("Add BA reject configuration: \n");
		printf("    TID      Reject \n");
		for (i = 0; i < MAX_NUM_TID; i++) {
			printf("     %d        %d\n", i, buffer[i]);
		}
	}

	if (buffer)
		free(buffer);
	if (cmd)
		free(cmd);

	return MLAN_STATUS_SUCCESS;
}

/**
 *  @brief Process HT Del BA command
 *  @param argc   Number of arguments
 *  @param argv   A pointer to arguments array
 *  @return     MLAN_STATUS_SUCCESS--success, otherwise--fail
 */
static int
process_delba(int argc, char *argv[])
{
	t_u8 *buffer = NULL;
	struct eth_priv_cmd *cmd = NULL;
	struct ifreq ifr;

	/* Initialize buffer */
	buffer = (t_u8 *)malloc(BUFFER_LENGTH);
	if (!buffer) {
		printf("ERR:Cannot allocate buffer for command!\n");
		return MLAN_STATUS_FAILURE;
	}

	prepare_buffer(buffer, argv[2], (argc - 3), &argv[3]);

	cmd = (struct eth_priv_cmd *)malloc(sizeof(struct eth_priv_cmd));
	if (!cmd) {
		printf("ERR:Cannot allocate buffer for command!\n");
		free(buffer);
		return MLAN_STATUS_FAILURE;
	}

	/* Fill up buffer */
#ifdef USERSPACE_32BIT_OVER_KERNEL_64BIT
	memset(cmd, 0, sizeof(struct eth_priv_cmd));
	memcpy(&cmd->buf, &buffer, sizeof(buffer));
#else
	cmd->buf = buffer;
#endif
	cmd->used_len = 0;
	cmd->total_len = BUFFER_LENGTH;

	/* Perform IOCTL */
	memset(&ifr, 0, sizeof(struct ifreq));
	strncpy(ifr.ifr_ifrn.ifrn_name, dev_name, strlen(dev_name));
	ifr.ifr_ifru.ifru_data = (void *)cmd;

	if (ioctl(sockfd, MLAN_ETH_PRIV, &ifr)) {
		perror("mlanutl");
		fprintf(stderr, "mlanutl: delba fail\n");
		if (cmd)
			free(cmd);
		if (buffer)
			free(buffer);
		return MLAN_STATUS_FAILURE;
	}

	if (buffer)
		free(buffer);
	if (cmd)
		free(cmd);

	return MLAN_STATUS_SUCCESS;
}

/**
 *  @brief Process reject addba req command
 *  @param argc   Number of arguments
 *  @param argv   A pointer to arguments array
 *  @return     MLAN_STATUS_SUCCESS--success, otherwise--fail
 */
static int
process_rejectaddbareq(int argc, char *argv[])
{
	t_u8 *buffer = NULL;
	struct eth_priv_cmd *cmd = NULL;
	struct ifreq ifr;

	/* Initialize buffer */
	buffer = (t_u8 *)malloc(BUFFER_LENGTH);
	if (!buffer) {
		printf("ERR:Cannot allocate buffer for command!\n");
		return MLAN_STATUS_FAILURE;
	}

	prepare_buffer(buffer, argv[2], (argc - 3), &argv[3]);

	cmd = (struct eth_priv_cmd *)malloc(sizeof(struct eth_priv_cmd));
	if (!cmd) {
		printf("ERR:Cannot allocate buffer for command!\n");
		free(buffer);
		return MLAN_STATUS_FAILURE;
	}

	/* Fill up buffer */
#ifdef USERSPACE_32BIT_OVER_KERNEL_64BIT
	memset(cmd, 0, sizeof(struct eth_priv_cmd));
	memcpy(&cmd->buf, &buffer, sizeof(buffer));
#else
	cmd->buf = buffer;
#endif
	cmd->used_len = 0;
	cmd->total_len = BUFFER_LENGTH;

	/* Perform IOCTL */
	memset(&ifr, 0, sizeof(struct ifreq));
	strncpy(ifr.ifr_ifrn.ifrn_name, dev_name, strlen(dev_name));
	ifr.ifr_ifru.ifru_data = (void *)cmd;

	if (ioctl(sockfd, MLAN_ETH_PRIV, &ifr)) {
		perror("mlanutl");
		fprintf(stderr, "mlanutl: rejectaddbareq fail\n");
		if (cmd)
			free(cmd);
		if (buffer)
			free(buffer);
		return MLAN_STATUS_FAILURE;
	}

	/* Process result */
	printf("Reject addba req command response: %s\n", buffer);

	if (buffer)
		free(buffer);
	if (cmd)
		free(cmd);

	return MLAN_STATUS_SUCCESS;
}

/**
 *  @brief Process VHT configuration
 *  @param argc   Number of arguments
 *  @param argv   A pointer to arguments array
 *  @return     MLAN_STATUS_SUCCESS--success, otherwise--fail
 */
static int
process_vhtcfg(int argc, char *argv[])
{
	t_u8 *buffer = NULL;
	struct eth_priv_cmd *cmd = NULL;
	struct eth_priv_vhtcfg vhtcfg;
	struct ifreq ifr;
	t_u8 i, num = 0;

	/* Initialize buffer */
	buffer = (t_u8 *)malloc(BUFFER_LENGTH);
	if (!buffer) {
		printf("ERR:Cannot allocate buffer for command!\n");
		return MLAN_STATUS_FAILURE;
	}

	/* Sanity tests */
	if (argc < 5) {
		printf("Insufficient parameters\n");
		printf("For STA interface: mlanutl mlanX vhtcfg <band> <txrx> [bwcfg] [vhtcap]\n");
		printf("For uAP interface: mlanutl uapX vhtcfg <band> <txrx> [bwcfg] [vhtcap] [vht_tx_mcs] [vht_rx_mcs]\n");
		free(buffer);
		return MLAN_STATUS_FAILURE;
	}

	prepare_buffer(buffer, argv[2], (argc - 3), &argv[3]);

	cmd = (struct eth_priv_cmd *)malloc(sizeof(struct eth_priv_cmd));
	if (!cmd) {
		printf("ERR:Cannot allocate buffer for command!\n");
		free(buffer);
		return MLAN_STATUS_FAILURE;
	}

	/* Fill up buffer */
#ifdef USERSPACE_32BIT_OVER_KERNEL_64BIT
	memset(cmd, 0, sizeof(struct eth_priv_cmd));
	memcpy(&cmd->buf, &buffer, sizeof(buffer));
#else
	cmd->buf = buffer;
#endif
	cmd->used_len = 0;
	cmd->total_len = BUFFER_LENGTH;

	/* Perform IOCTL */
	memset(&ifr, 0, sizeof(struct ifreq));
	strncpy(ifr.ifr_ifrn.ifrn_name, dev_name, strlen(dev_name));
	ifr.ifr_ifru.ifru_data = (void *)cmd;

	if (ioctl(sockfd, MLAN_ETH_PRIV, &ifr)) {
		perror("mlanutl");
		fprintf(stderr, "mlanutl: vhtcfg fail\n");
		if (cmd)
			free(cmd);
		if (buffer)
			free(buffer);
		return MLAN_STATUS_FAILURE;
	}

	/* Process result */
	/* the first attribute is the number of vhtcfg entries */
	num = *buffer;
	if (argc == 5) {
		/* GET operation */
		printf("11AC VHT Configuration: \n");
		for (i = 0; i < num; i++) {
			memcpy(&vhtcfg, buffer + 1 + i * sizeof(vhtcfg),
			       sizeof(vhtcfg));
			/* Band */
			if (vhtcfg.band == 1)
				printf("Band: 2.4G\n");
			else
				printf("Band: 5G\n");
			/* BW confi9 */

			if (vhtcfg.bwcfg == 0)
				printf("    BW config: Follow BW in the 11N config\n");
			else
				printf("    BW config: Follow BW in VHT Capabilities\n");

			/* Tx/Rx */
			if (vhtcfg.txrx & 0x1)
				printf("    VHT operation for Tx: 0x%08x\n",
				       vhtcfg.vht_cap_info);
			if (vhtcfg.txrx & 0x2)
				/* VHT capabilities */
				printf("    VHT Capabilities Info: 0x%08x\n",
				       vhtcfg.vht_cap_info);
			/* MCS */
			if (vhtcfg.txrx & 0x2) {
				printf("    Tx MCS set: 0x%04x\n",
				       vhtcfg.vht_tx_mcs);
				printf("    Rx MCS set: 0x%04x\n",
				       vhtcfg.vht_rx_mcs);
			}
		}
	} else {
		/* SET operation */
	}

	if (buffer)
		free(buffer);
	if (cmd)
		free(cmd);

	return MLAN_STATUS_SUCCESS;
}

/**
 *  @brief Process Operating Mode Notification configuration
 *  @param argc   Number of arguments
 *  @param argv   A pointer to arguments array
 *  @return     MLAN_STATUS_SUCCESS--success, otherwise--fail
 */
static int
process_opermodecfg(int argc, char *argv[])
{
	t_u8 *buffer = NULL;
	struct eth_priv_cmd *cmd = NULL;
	struct eth_priv_opermodecfg *cfg = NULL;
	struct ifreq ifr;

	/* Initialize buffer */
	buffer = (t_u8 *)malloc(BUFFER_LENGTH);
	if (!buffer) {
		printf("ERR:Cannot allocate buffer for command!\n");
		return MLAN_STATUS_FAILURE;
	}

	prepare_buffer(buffer, argv[2], (argc - 3), &argv[3]);

	cmd = (struct eth_priv_cmd *)malloc(sizeof(struct eth_priv_cmd));
	if (!cmd) {
		printf("ERR:Cannot allocate buffer for command!\n");
		free(buffer);
		return MLAN_STATUS_FAILURE;
	}

	/* Fill up buffer */
#ifdef USERSPACE_32BIT_OVER_KERNEL_64BIT
	memset(cmd, 0, sizeof(struct eth_priv_cmd));
	memcpy(&cmd->buf, &buffer, sizeof(buffer));
#else
	cmd->buf = buffer;
#endif
	cmd->used_len = 0;
	cmd->total_len = BUFFER_LENGTH;

	/* Perform IOCTL */
	memset(&ifr, 0, sizeof(struct ifreq));
	strncpy(ifr.ifr_ifrn.ifrn_name, dev_name, strlen(dev_name));
	ifr.ifr_ifru.ifru_data = (void *)cmd;

	if (ioctl(sockfd, MLAN_ETH_PRIV, &ifr)) {
		perror("mlanutl");
		fprintf(stderr, "mlanutl: opermodecfg fail\n");
		if (cmd)
			free(cmd);
		if (buffer)
			free(buffer);
		return MLAN_STATUS_FAILURE;
	}

	/* Process result */
	cfg = (struct eth_priv_opermodecfg *)(buffer);
	printf("11AC Operating Mode Notification Configuration: \n");
	printf("    bw: %d\n", cfg->bw);
	printf("    nss: %d\n", cfg->nss);

	if (buffer)
		free(buffer);
	if (cmd)
		free(cmd);

	return MLAN_STATUS_SUCCESS;
}

static char *rate_format[3] = { "LG", "HT", "VHT" };

static char *lg_rate[] = { "1 Mbps", "2 Mbps", "5.5 Mbps", "11 Mbps",
	"6 Mbps", "9 Mbps", "12 Mbps", "18 Mbps",
	"24 Mbps", "36 Mbps", "48 Mbps", "54 Mbps"
};

/**
 *  @brief Process Get data rate
 *  @param argc   Number of arguments
 *  @param argv   A pointer to arguments array
 *  @return     MLAN_STATUS_SUCCESS--success, otherwise--fail
 */
static int
process_datarate(int argc, char *argv[])
{
	t_u8 *buffer = NULL;
	struct eth_priv_cmd *cmd = NULL;
	struct eth_priv_data_rate *datarate = NULL;
	struct ifreq ifr;
	char *bw[] = { "20 MHz", "40 MHz", "80 MHz", "160 MHz" };

	/* Initialize buffer */
	buffer = (t_u8 *)malloc(BUFFER_LENGTH);
	if (!buffer) {
		printf("ERR:Cannot allocate buffer for command!\n");
		return MLAN_STATUS_FAILURE;
	}

	prepare_buffer(buffer, argv[2], 0, NULL);

	cmd = (struct eth_priv_cmd *)malloc(sizeof(struct eth_priv_cmd));
	if (!cmd) {
		printf("ERR:Cannot allocate buffer for command!\n");
		free(buffer);
		return MLAN_STATUS_FAILURE;
	}

	/* Fill up buffer */
#ifdef USERSPACE_32BIT_OVER_KERNEL_64BIT
	memset(cmd, 0, sizeof(struct eth_priv_cmd));
	memcpy(&cmd->buf, &buffer, sizeof(buffer));
#else
	cmd->buf = buffer;
#endif
	cmd->used_len = 0;
	cmd->total_len = BUFFER_LENGTH;

	/* Perform IOCTL */
	memset(&ifr, 0, sizeof(struct ifreq));
	strncpy(ifr.ifr_ifrn.ifrn_name, dev_name, strlen(dev_name));
	ifr.ifr_ifru.ifru_data = (void *)cmd;

	if (ioctl(sockfd, MLAN_ETH_PRIV, &ifr)) {
		perror("mlanutl");
		fprintf(stderr, "mlanutl: getdatarate fail\n");
		if (cmd)
			free(cmd);
		if (buffer)
			free(buffer);
		return MLAN_STATUS_FAILURE;
	}

	/* Process result */
	datarate = (struct eth_priv_data_rate *)buffer;
	printf("Data Rate:\n");
	printf("  TX: \n");
	if (datarate->tx_rate_format <= 2) {
		printf("    Type: %s\n", rate_format[datarate->tx_rate_format]);
		if ((datarate->tx_rate_format == 0) &&
		    datarate->tx_data_rate <= 11)
			/* LG */
			printf("    Rate: %s\n",
			       lg_rate[datarate->tx_data_rate]);
		else {
			/* HT and VHT */
			if (datarate->tx_bw <= 3)
				printf("    BW:   %s\n", bw[datarate->tx_bw]);
			if (datarate->tx_gi == 0)
				printf("    GI:   Long\n");
			else
				printf("    GI:   Short\n");
			if (datarate->tx_rate_format == 3)
				printf("    NSS:  %d\n", datarate->tx_nss + 1);
			if (datarate->tx_mcs_index != 0xFF)
				printf("    MCS:  MCS %d\n",
				       (int)datarate->tx_mcs_index);
			else
				printf("    MCS:  Auto\n");
			printf("    Rate: %f Mbps\n",
			       (float)datarate->tx_data_rate / 2);
		}
	}

	printf("  RX: \n");
	if (datarate->rx_rate_format <= 2) {
		printf("    Type: %s\n", rate_format[datarate->rx_rate_format]);
		if ((datarate->rx_rate_format == 0) &&
		    datarate->rx_data_rate <= 11)
			/* LG */
			printf("    Rate: %s\n",
			       lg_rate[datarate->rx_data_rate]);
		else {
			/* HT and VHT */
			if (datarate->rx_bw <= 3)
				printf("    BW:   %s\n", bw[datarate->rx_bw]);
			if (datarate->rx_gi == 0)
				printf("    GI:   Long\n");
			else
				printf("    GI:   Short\n");
			if (datarate->rx_rate_format == 3)
				printf("    NSS:  %d\n", datarate->rx_nss + 1);
			if (datarate->rx_mcs_index != 0xFF)
				printf("    MCS:  MCS %d\n",
				       (int)datarate->rx_mcs_index);
			else
				printf("    MCS:  Auto\n");
			printf("    Rate: %f Mbps\n",
			       (float)datarate->rx_data_rate / 2);
		}
	}

	if (buffer)
		free(buffer);
	if (cmd)
		free(cmd);

	return MLAN_STATUS_SUCCESS;
}

/**
 *  @brief Process tx rate configuration
 *  @param argc   Number of arguments
 *  @param argv   A pointer to arguments array
 *  @return     MLAN_STATUS_SUCCESS--success, otherwise--fail
 */
static int
process_txratecfg(int argc, char *argv[])
{
	t_u8 *buffer = NULL;
	struct eth_priv_cmd *cmd = NULL;
	struct eth_priv_tx_rate_cfg *txratecfg = NULL;
	struct ifreq ifr;

	/* Initialize buffer */
	buffer = (t_u8 *)malloc(BUFFER_LENGTH);
	if (!buffer) {
		printf("ERR:Cannot allocate buffer for command!\n");
		return MLAN_STATUS_FAILURE;
	}

	prepare_buffer(buffer, argv[2], (argc - 3), &argv[3]);

	cmd = (struct eth_priv_cmd *)malloc(sizeof(struct eth_priv_cmd));
	if (!cmd) {
		printf("ERR:Cannot allocate buffer for command!\n");
		free(buffer);
		return MLAN_STATUS_FAILURE;
	}

	/* Fill up buffer */
#ifdef USERSPACE_32BIT_OVER_KERNEL_64BIT
	memset(cmd, 0, sizeof(struct eth_priv_cmd));
	memcpy(&cmd->buf, &buffer, sizeof(buffer));
#else
	cmd->buf = buffer;
#endif
	cmd->used_len = 0;
	cmd->total_len = BUFFER_LENGTH;

	/* Perform IOCTL */
	memset(&ifr, 0, sizeof(struct ifreq));
	strncpy(ifr.ifr_ifrn.ifrn_name, dev_name, strlen(dev_name));
	ifr.ifr_ifru.ifru_data = (void *)cmd;

	if (ioctl(sockfd, MLAN_ETH_PRIV, &ifr)) {
		perror("mlanutl");
		fprintf(stderr, "mlanutl: txratecfg fail\n");
		if (cmd)
			free(cmd);
		if (buffer)
			free(buffer);
		return MLAN_STATUS_FAILURE;
	}

	/* Process result */
	txratecfg = (struct eth_priv_tx_rate_cfg *)buffer;
	if (argc == 3) {
		/* GET operation */
		printf("Tx Rate Configuration: \n");
		/* format */
		if (txratecfg->rate_format == 0xFF) {
			printf("    Type:       0xFF (Auto)\n");
		} else if (txratecfg->rate_format <= 2) {
			printf("    Type:       %d (%s)\n",
			       txratecfg->rate_format,
			       rate_format[txratecfg->rate_format]);
			if (txratecfg->rate_format == 0)
				printf("    Rate Index: %d (%s)\n",
				       txratecfg->rate_index,
				       lg_rate[txratecfg->rate_index]);
			else if (txratecfg->rate_format >= 1)
				printf("    MCS Index:  %d\n",
				       (int)txratecfg->rate_index);
			if (txratecfg->rate_format == 2)
				printf("    NSS:        %d\n",
				       (int)txratecfg->nss);
		} else {
			printf("    Unknown rate format.\n");
		}
	}

	if (buffer)
		free(buffer);
	if (cmd)
		free(cmd);

	return MLAN_STATUS_SUCCESS;
}

/**
 *  @brief Process get channel list used by cfg80211
 *  @param argc   Number of arguments
 *  @param argv   A pointer to arguments array
 *  @return     MLAN_STATUS_SUCCESS--success, otherwise--fail
 */
static int
process_getcfgchanlist(int argc, char *argv[])
{
	t_u8 *buffer = NULL;
	struct eth_priv_cmd *cmd = NULL;
	struct ifreq ifr;
	int i = 0;
	wlan_ieee80211_chan_list *chan_list = NULL;

	/* Initialize buffer */
	buffer = (t_u8 *)malloc(BUFFER_LENGTH);
	if (!buffer) {
		printf("ERR:Cannot allocate buffer for command!\n");
		return MLAN_STATUS_FAILURE;
	}

	prepare_buffer(buffer, argv[2], (argc - 3), &argv[3]);

	cmd = (struct eth_priv_cmd *)malloc(sizeof(struct eth_priv_cmd));
	if (!cmd) {
		printf("ERR:Cannot allocate buffer for command!\n");
		free(buffer);
		return MLAN_STATUS_FAILURE;
	}

	/* Fill up buffer */
#ifdef USERSPACE_32BIT_OVER_KERNEL_64BIT
	memset(cmd, 0, sizeof(struct eth_priv_cmd));
	memcpy(&cmd->buf, &buffer, sizeof(buffer));
#else
	cmd->buf = buffer;
#endif
	cmd->used_len = 0;
	cmd->total_len = BUFFER_LENGTH;

	/* Perform IOCTL */
	memset(&ifr, 0, sizeof(struct ifreq));
	strncpy(ifr.ifr_ifrn.ifrn_name, dev_name, strlen(dev_name));
	ifr.ifr_ifru.ifru_data = (void *)cmd;

	if (ioctl(sockfd, MLAN_ETH_PRIV, &ifr)) {
		perror("mlanutl");
		fprintf(stderr, "mlanutl: getcfgchanlist\n");
		if (cmd)
			free(cmd);
		if (buffer)
			free(buffer);
		return MLAN_STATUS_FAILURE;
	}
	/* Process results */
	chan_list = (wlan_ieee80211_chan_list *) buffer;
	printf("Channel Flags:\n");
	printf("            IEEE80211_CHAN_DISABLED		= 1<<0\n");
	printf("            IEEE80211_CHAN_NO_IR		= 1<<1\n");
	printf("            IEEE80211_CHAN_RADAR		= 1<<3\n");
	printf("            IEEE80211_CHAN_NO_HT40PLUS		= 1<<4\n");
	printf("            IEEE80211_CHAN_NO_HT40MINUS		= 1<<5\n");
	printf("            IEEE80211_CHAN_NO_OFDM		= 1<<6\n");
	printf("            IEEE80211_CHAN_NO_80MHZ		= 1<<7\n");
	printf("            IEEE80211_CHAN_NO_160MHZ		= 1<<8\n");
	printf("            IEEE80211_CHAN_INDOOR_ONLY		= 1<<9\n");
	printf("            IEEE80211_CHAN_IR_CONCURRENT	= 1<<10\n");
	printf("            IEEE80211_CHAN_NO_20MHZ		= 1<<11\n");
	printf("            IEEE80211_CHAN_NO_10MHZ		= 1<<12\n");
	printf("---------------------------------------");
	printf("---------------------------------------\n");
	printf("# | chan  |  freq  | disable | NO_IR | RADAR |NO_OFDM|NO_HT40+|NO_HT40-|NO_80|\n");
	printf("---------------------------------------");
	printf("---------------------------------------\n");
	for (i = 0; i < chan_list->num_chan; i++) {
		printf("    [%03d]     %04d       %c       %c       %c       %c       %c       %c        %c\n", chan_list->chan_list[i].hw_value, chan_list->chan_list[i].center_freq, (chan_list->chan_list[i].flags & IEEE80211_CHAN_DISABLED) ? 'Y' : '-', (chan_list->chan_list[i].flags & IEEE80211_CHAN_NO_IR) ? 'Y' : '-', (chan_list->chan_list[i].flags & IEEE80211_CHAN_RADAR) ? 'Y' : '-', (chan_list->chan_list[i].flags & IEEE80211_CHAN_NO_OFDM) ? 'Y' : '-', (chan_list->chan_list[i].flags & IEEE80211_CHAN_NO_HT40PLUS) ? 'Y' : '-', (chan_list->chan_list[i].flags & IEEE80211_CHAN_NO_HT40MINUS) ? 'Y' : '-', (chan_list->chan_list[i].flags & IEEE80211_CHAN_NO_80MHZ) ? 'Y' : '-');
	}

	if (buffer)
		free(buffer);
	if (cmd)
		free(cmd);

	return MLAN_STATUS_SUCCESS;

}

/**
 *  @brief Process get wireless stats
 *  @param argc   Number of arguments
 *  @param argv   A pointer to arguments array
 *  @return     MLAN_STATUS_SUCCESS--success, otherwise--fail
 */
static int
process_getlog(int argc, char *argv[])
{
	t_u8 *buffer = NULL;
	struct eth_priv_cmd *cmd = NULL;
	struct eth_priv_get_log *stats = NULL;
	struct ifreq ifr;
	struct timeval tv;
	int i = 0;

	/* Initialize buffer */
	buffer = (t_u8 *)malloc(BUFFER_LENGTH);
	if (!buffer) {
		printf("ERR:Cannot allocate buffer for command!\n");
		return MLAN_STATUS_FAILURE;
	}

	prepare_buffer(buffer, argv[2], (argc - 3), &argv[3]);

	cmd = (struct eth_priv_cmd *)malloc(sizeof(struct eth_priv_cmd));
	if (!cmd) {
		printf("ERR:Cannot allocate buffer for command!\n");
		free(buffer);
		return MLAN_STATUS_FAILURE;
	}

	/* Fill up buffer */
#ifdef USERSPACE_32BIT_OVER_KERNEL_64BIT
	memset(cmd, 0, sizeof(struct eth_priv_cmd));
	memcpy(&cmd->buf, &buffer, sizeof(buffer));
#else
	cmd->buf = buffer;
#endif
	cmd->used_len = 0;
	cmd->total_len = BUFFER_LENGTH;

	/* Perform IOCTL */
	memset(&ifr, 0, sizeof(struct ifreq));
	strncpy(ifr.ifr_ifrn.ifrn_name, dev_name, strlen(dev_name));
	ifr.ifr_ifru.ifru_data = (void *)cmd;

	if (ioctl(sockfd, MLAN_ETH_PRIV, &ifr)) {
		perror("mlanutl");
		fprintf(stderr, "mlanutl: getlog fail\n");
		if (cmd)
			free(cmd);
		if (buffer)
			free(buffer);
		return MLAN_STATUS_FAILURE;
	}

	gettimeofday(&tv, NULL);

	/* Process results */
	stats = (struct eth_priv_get_log *)buffer;
	printf("Get log: timestamp %d.%06d sec\n", (int)tv.tv_sec,
	       (int)tv.tv_usec);
	printf("dot11GroupTransmittedFrameCount    %u\n"
	       "dot11FailedCount                   %u\n"
	       "dot11RetryCount                    %u\n"
	       "dot11MultipleRetryCount            %u\n"
	       "dot11FrameDuplicateCount           %u\n"
	       "dot11RTSSuccessCount               %u\n"
	       "dot11RTSFailureCount               %u\n"
	       "dot11ACKFailureCount               %u\n"
	       "dot11ReceivedFragmentCount         %u\n"
	       "dot11GroupReceivedFrameCount       %u\n"
	       "dot11FCSErrorCount                 %u\n"
	       "dot11TransmittedFrameCount         %u\n"
	       "wepicverrcnt-1                     %u\n"
	       "wepicverrcnt-2                     %u\n"
	       "wepicverrcnt-3                     %u\n"
	       "wepicverrcnt-4                     %u\n"
	       "beaconReceivedCount                %u\n"
	       "beaconMissedCount                  %u\n", stats->mcast_tx_frame,
	       stats->failed, stats->retry, stats->multi_retry,
	       stats->frame_dup, stats->rts_success, stats->rts_failure,
	       stats->ack_failure, stats->rx_frag, stats->mcast_rx_frame,
	       stats->fcs_error, stats->tx_frame, stats->wep_icv_error[0],
	       stats->wep_icv_error[1], stats->wep_icv_error[2],
	       stats->wep_icv_error[3], stats->bcn_rcv_cnt,
	       stats->bcn_miss_cnt);
	if (cmd->used_len == sizeof(struct eth_priv_get_log)) {
		printf("dot11TransmittedFragmentCount      %u\n",
		       stats->tx_frag_cnt);
		printf("dot11QosTransmittedFragmentCount   ");
		for (i = 0; i < 8; i++) {
			printf("%u ", stats->qos_tx_frag_cnt[i]);
		}
		printf("\ndot11QosFailedCount                ");
		for (i = 0; i < 8; i++) {
			printf("%u ", stats->qos_failed_cnt[i]);
		}
		printf("\ndot11QosRetryCount                 ");
		for (i = 0; i < 8; i++) {
			printf("%u ", stats->qos_retry_cnt[i]);
		}
		printf("\ndot11QosMultipleRetryCount         ");
		for (i = 0; i < 8; i++) {
			printf("%u ", stats->qos_multi_retry_cnt[i]);
		}
		printf("\ndot11QosFrameDuplicateCount        ");
		for (i = 0; i < 8; i++) {
			printf("%u ", stats->qos_frm_dup_cnt[i]);
		}
		printf("\ndot11QosRTSSuccessCount            ");
		for (i = 0; i < 8; i++) {
			printf("%u ", stats->qos_rts_suc_cnt[i]);
		}
		printf("\ndot11QosRTSFailureCount            ");
		for (i = 0; i < 8; i++) {
			printf("%u ", stats->qos_rts_failure_cnt[i]);
		}
		printf("\ndot11QosACKFailureCount            ");
		for (i = 0; i < 8; i++) {
			printf("%u ", stats->qos_ack_failure_cnt[i]);
		}
		printf("\ndot11QosReceivedFragmentCount      ");
		for (i = 0; i < 8; i++) {
			printf("%u ", stats->qos_rx_frag_cnt[i]);
		}
		printf("\ndot11QosTransmittedFrameCount      ");
		for (i = 0; i < 8; i++) {
			printf("%u ", stats->qos_tx_frm_cnt[i]);
		}
		printf("\ndot11QosDiscardedFrameCount        ");
		for (i = 0; i < 8; i++) {
			printf("%u ", stats->qos_discarded_frm_cnt[i]);
		}
		printf("\ndot11QosMPDUsReceivedCount         ");
		for (i = 0; i < 8; i++) {
			printf("%u ", stats->qos_mpdus_rx_cnt[i]);
		}
		printf("\ndot11QosRetriesReceivedCount       ");
		for (i = 0; i < 8; i++) {
			printf("%u ", stats->qos_retries_rx_cnt[i]);
		}
		printf("\ndot11RSNAStatsCMACICVErrors          %u\n"
		       "dot11RSNAStatsCMACReplays            %u\n"
		       "dot11RSNAStatsRobustMgmtCCMPReplays  %u\n"
		       "dot11RSNAStatsTKIPICVErrors          %u\n"
		       "dot11RSNAStatsTKIPReplays            %u\n"
		       "dot11RSNAStatsCCMPDecryptErrors      %u\n"
		       "dot11RSNAstatsCCMPReplays            %u\n"
		       "dot11TransmittedAMSDUCount           %u\n"
		       "dot11FailedAMSDUCount                %u\n"
		       "dot11RetryAMSDUCount                 %u\n"
		       "dot11MultipleRetryAMSDUCount         %u\n"
		       "dot11TransmittedOctetsInAMSDUCount   %llu\n"
		       "dot11AMSDUAckFailureCount            %u\n"
		       "dot11ReceivedAMSDUCount              %u\n"
		       "dot11ReceivedOctetsInAMSDUCount      %llu\n"
		       "dot11TransmittedAMPDUCount           %u\n"
		       "dot11TransmittedMPDUsInAMPDUCount    %u\n"
		       "dot11TransmittedOctetsInAMPDUCount   %llu\n"
		       "dot11AMPDUReceivedCount              %u\n"
		       "dot11MPDUInReceivedAMPDUCount        %u\n"
		       "dot11ReceivedOctetsInAMPDUCount      %llu\n"
		       "dot11AMPDUDelimiterCRCErrorCount     %u\n",
		       stats->cmacicv_errors,
		       stats->cmac_replays,
		       stats->mgmt_ccmp_replays,
		       stats->tkipicv_errors,
		       stats->tkip_replays,
		       stats->ccmp_decrypt_errors,
		       stats->ccmp_replays,
		       stats->tx_amsdu_cnt,
		       stats->failed_amsdu_cnt,
		       stats->retry_amsdu_cnt,
		       stats->multi_retry_amsdu_cnt,
		       stats->tx_octets_in_amsdu_cnt,
		       stats->amsdu_ack_failure_cnt,
		       stats->rx_amsdu_cnt,
		       stats->rx_octets_in_amsdu_cnt,
		       stats->tx_ampdu_cnt,
		       stats->tx_mpdus_in_ampdu_cnt,
		       stats->tx_octets_in_ampdu_cnt,
		       stats->ampdu_rx_cnt,
		       stats->mpdu_in_rx_ampdu_cnt,
		       stats->rx_octets_in_ampdu_cnt,
		       stats->ampdu_delimiter_crc_error_cnt);
	}

	if (buffer)
		free(buffer);
	if (cmd)
		free(cmd);

	return MLAN_STATUS_SUCCESS;
}

/**
 *  @brief Process esuppmode command
 *  @param argc   Number of arguments
 *  @param argv   A pointer to arguments array
 *  @return     MLAN_STATUS_SUCCESS--success, otherwise--fail
 */
static int
process_esuppmode(int argc, char *argv[])
{
	t_u8 *buffer = NULL;
	struct eth_priv_cmd *cmd = NULL;
	struct eth_priv_esuppmode_cfg *esuppmodecfg = NULL;
	struct ifreq ifr;

	/* Initialize buffer */
	buffer = (t_u8 *)malloc(BUFFER_LENGTH);
	if (!buffer) {
		printf("ERR:Cannot allocate buffer for command!\n");
		return MLAN_STATUS_FAILURE;
	}

	prepare_buffer(buffer, argv[2], (argc - 3), &argv[3]);

	cmd = (struct eth_priv_cmd *)malloc(sizeof(struct eth_priv_cmd));
	if (!cmd) {
		printf("ERR:Cannot allocate buffer for command!\n");
		free(buffer);
		return MLAN_STATUS_FAILURE;
	}

	/* Fill up buffer */
#ifdef USERSPACE_32BIT_OVER_KERNEL_64BIT
	memset(cmd, 0, sizeof(struct eth_priv_cmd));
	memcpy(&cmd->buf, &buffer, sizeof(buffer));
#else
	cmd->buf = buffer;
#endif
	cmd->used_len = 0;
	cmd->total_len = BUFFER_LENGTH;

	/* Perform IOCTL */
	memset(&ifr, 0, sizeof(struct ifreq));
	strncpy(ifr.ifr_ifrn.ifrn_name, dev_name, strlen(dev_name));
	ifr.ifr_ifru.ifru_data = (void *)cmd;

	if (ioctl(sockfd, MLAN_ETH_PRIV, &ifr)) {
		perror("mlanutl");
		fprintf(stderr, "mlanutl: esuppmode fail\n");
		if (cmd)
			free(cmd);
		if (buffer)
			free(buffer);
		return MLAN_STATUS_FAILURE;
	}

	/* Process result */
	esuppmodecfg = (struct eth_priv_esuppmode_cfg *)buffer;
	if (argc == 3) {
		/* GET operation */
		printf("Esupplicant Mode Configuration: \n");
		/* RSN mode */
		printf("    RSN mode:         0x%x ( ", esuppmodecfg->rsn_mode);
		if (esuppmodecfg->rsn_mode & MBIT(0))
			printf("No-RSN ");
		if (esuppmodecfg->rsn_mode & MBIT(3))
			printf("WPA ");
		if (esuppmodecfg->rsn_mode & MBIT(4))
			printf("WPA-None ");
		if (esuppmodecfg->rsn_mode & MBIT(5))
			printf("WPA2 ");
		printf(")\n");
		/* Pairwise cipher */
		printf("    Pairwise cipher:  0x%x ( ",
		       esuppmodecfg->pairwise_cipher);
		if (esuppmodecfg->pairwise_cipher & MBIT(2))
			printf("TKIP ");
		if (esuppmodecfg->pairwise_cipher & MBIT(3))
			printf("AES ");
		printf(")\n");
		/* Group cipher */
		printf("    Group cipher:     0x%x ( ",
		       esuppmodecfg->group_cipher);
		if (esuppmodecfg->group_cipher & MBIT(2))
			printf("TKIP ");
		if (esuppmodecfg->group_cipher & MBIT(3))
			printf("AES ");
		printf(")\n");
	}

	if (buffer)
		free(buffer);
	if (cmd)
		free(cmd);

	return MLAN_STATUS_SUCCESS;
}

/**
 *  @brief Process passphrase command
 *  @param argc   Number of arguments
 *  @param argv   A pointer to arguments array
 *  @return     MLAN_STATUS_SUCCESS--success, otherwise--fail
 */
static int
process_passphrase(int argc, char *argv[])
{
	t_u8 *buffer = NULL;
	struct eth_priv_cmd *cmd = NULL;
	struct ifreq ifr;

	/* Initialize buffer */
	buffer = (t_u8 *)malloc(BUFFER_LENGTH);
	if (!buffer) {
		printf("ERR:Cannot allocate buffer for command!\n");
		return MLAN_STATUS_FAILURE;
	}

	/* The argument being a string, this requires special handling */
	prepare_buffer(buffer, argv[2], 0, NULL);
	if (argc >= 4) {
		strcpy((char *)(buffer + strlen(CMD_NXP) + strlen(argv[2])),
		       argv[3]);
	}

	cmd = (struct eth_priv_cmd *)malloc(sizeof(struct eth_priv_cmd));
	if (!cmd) {
		printf("ERR:Cannot allocate buffer for command!\n");
		free(buffer);
		return MLAN_STATUS_FAILURE;
	}

	/* Fill up buffer */
#ifdef USERSPACE_32BIT_OVER_KERNEL_64BIT
	memset(cmd, 0, sizeof(struct eth_priv_cmd));
	memcpy(&cmd->buf, &buffer, sizeof(buffer));
#else
	cmd->buf = buffer;
#endif
	cmd->used_len = 0;
	cmd->total_len = BUFFER_LENGTH;

	/* Perform IOCTL */
	memset(&ifr, 0, sizeof(struct ifreq));
	strncpy(ifr.ifr_ifrn.ifrn_name, dev_name, strlen(dev_name));
	ifr.ifr_ifru.ifru_data = (void *)cmd;

	if (ioctl(sockfd, MLAN_ETH_PRIV, &ifr)) {
		perror("mlanutl");
		fprintf(stderr, "mlanutl: passphrase fail\n");
		if (cmd)
			free(cmd);
		if (buffer)
			free(buffer);
		return MLAN_STATUS_FAILURE;
	}

	/* Process result */
	printf("Passphrase Configuration: %s\n", (char *)buffer);

	if (buffer)
		free(buffer);
	if (cmd)
		free(cmd);

	return MLAN_STATUS_SUCCESS;
}

/**
 *  @brief Process deauth command
 *  @param argc   Number of arguments
 *  @param argv   A pointer to arguments array
 *  @return     MLAN_STATUS_SUCCESS--success, otherwise--fail
 */
static int
process_deauth(int argc, char *argv[])
{
	t_u8 *buffer = NULL;
	struct eth_priv_cmd *cmd = NULL;
	struct ifreq ifr;

	/* Initialize buffer */
	buffer = (t_u8 *)malloc(BUFFER_LENGTH);
	if (!buffer) {
		printf("ERR:Cannot allocate buffer for command!\n");
		return MLAN_STATUS_FAILURE;
	}

	/* The argument being a string, this requires special handling */
	prepare_buffer(buffer, argv[2], 0, NULL);
	if (argc >= 4) {
		strcpy((char *)(buffer + strlen(CMD_NXP) + strlen(argv[2])),
		       argv[3]);
	}

	cmd = (struct eth_priv_cmd *)malloc(sizeof(struct eth_priv_cmd));
	if (!cmd) {
		printf("ERR:Cannot allocate buffer for command!\n");
		free(buffer);
		return MLAN_STATUS_FAILURE;
	}

	/* Fill up buffer */
#ifdef USERSPACE_32BIT_OVER_KERNEL_64BIT
	memset(cmd, 0, sizeof(struct eth_priv_cmd));
	memcpy(&cmd->buf, &buffer, sizeof(buffer));
#else
	cmd->buf = buffer;
#endif
	cmd->used_len = 0;
	cmd->total_len = BUFFER_LENGTH;

	/* Perform IOCTL */
	memset(&ifr, 0, sizeof(struct ifreq));
	strncpy(ifr.ifr_ifrn.ifrn_name, dev_name, strlen(dev_name));
	ifr.ifr_ifru.ifru_data = (void *)cmd;

	if (ioctl(sockfd, MLAN_ETH_PRIV, &ifr)) {
		perror("mlanutl");
		fprintf(stderr, "mlanutl: deauth fail\n");
		if (cmd)
			free(cmd);
		if (buffer)
			free(buffer);
		return MLAN_STATUS_FAILURE;
	}

	if (buffer)
		free(buffer);
	if (cmd)
		free(cmd);

	return MLAN_STATUS_SUCCESS;
}

#ifdef UAP_SUPPORT
/**
 *  @brief Process getstalist command
 *  @param argc   Number of arguments
 *  @param argv   A pointer to arguments array
 *  @return     MLAN_STATUS_SUCCESS--success, otherwise--fail
 */
static int
process_getstalist(int argc, char *argv[])
{
	t_u8 *buffer = NULL;
	struct eth_priv_cmd *cmd = NULL;
	struct ifreq ifr;
	struct eth_priv_getstalist *list = NULL;
	int i = 0, rssi = 0;

	/* Initialize buffer */
	buffer = (t_u8 *)malloc(BUFFER_LENGTH);
	if (!buffer) {
		printf("ERR:Cannot allocate buffer for command!\n");
		return MLAN_STATUS_FAILURE;
	}

	/* The argument being a string, this requires special handling */
	prepare_buffer(buffer, argv[2], 0, NULL);

	cmd = (struct eth_priv_cmd *)malloc(sizeof(struct eth_priv_cmd));
	if (!cmd) {
		printf("ERR:Cannot allocate buffer for command!\n");
		free(buffer);
		return MLAN_STATUS_FAILURE;
	}

	/* Fill up buffer */
#ifdef USERSPACE_32BIT_OVER_KERNEL_64BIT
	memset(cmd, 0, sizeof(struct eth_priv_cmd));
	memcpy(&cmd->buf, &buffer, sizeof(buffer));
#else
	cmd->buf = buffer;
#endif
	cmd->used_len = 0;
	cmd->total_len = BUFFER_LENGTH;

	/* Perform IOCTL */
	memset(&ifr, 0, sizeof(struct ifreq));
	strncpy(ifr.ifr_ifrn.ifrn_name, dev_name, strlen(dev_name));
	ifr.ifr_ifru.ifru_data = (void *)cmd;

	if (ioctl(sockfd, MLAN_ETH_PRIV, &ifr)) {
		perror("mlanutl");
		fprintf(stderr, "mlanutl: getstalist fail\n");
		if (cmd)
			free(cmd);
		if (buffer)
			free(buffer);
		return MLAN_STATUS_FAILURE;
	}
	list = (struct eth_priv_getstalist *)(buffer + strlen(CMD_NXP) +
					      strlen(argv[2]));

	printf("Number of STA = %d\n\n", list->sta_count);

	for (i = 0; i < list->sta_count; i++) {
		printf("STA %d information:\n", i + 1);
		printf("=====================\n");
		printf("MAC Address: ");
		print_mac(list->client_info[i].mac_address);
		printf("\nPower mfg status: %s\n",
		       (list->client_info[i].power_mfg_status ==
			0) ? "active" : "power save");

	/** On some platform, s8 is same as unsigned char*/
		rssi = (int)list->client_info[i].rssi;
		if (rssi > 0x7f)
			rssi = -(256 - rssi);
		printf("Rssi : %d dBm\n\n", rssi);
	}

	if (buffer)
		free(buffer);
	if (cmd)
		free(cmd);

	return MLAN_STATUS_SUCCESS;
}
#endif

#if defined(WIFI_DIRECT_SUPPORT)
#if defined(STA_SUPPORT) && defined(UAP_SUPPORT)
/**
 *  @brief Process BSS role command
 *  @param argc   Number of arguments
 *  @param argv   A pointer to arguments array
 *  @return     MLAN_STATUS_SUCCESS--success, otherwise--fail
 */
static int
process_bssrole(int argc, char *argv[])
{
	t_u8 *buffer = NULL;
	struct eth_priv_cmd *cmd = NULL;
	struct ifreq ifr;

	/* Initialize buffer */
	buffer = (t_u8 *)malloc(BUFFER_LENGTH);
	if (!buffer) {
		printf("ERR:Cannot allocate buffer for command!\n");
		return MLAN_STATUS_FAILURE;
	}

	prepare_buffer(buffer, argv[2], (argc - 3), &argv[3]);

	cmd = (struct eth_priv_cmd *)malloc(sizeof(struct eth_priv_cmd));
	if (!cmd) {
		printf("ERR:Cannot allocate buffer for command!\n");
		free(buffer);
		return MLAN_STATUS_FAILURE;
	}

	/* Fill up buffer */
#ifdef USERSPACE_32BIT_OVER_KERNEL_64BIT
	memset(cmd, 0, sizeof(struct eth_priv_cmd));
	memcpy(&cmd->buf, &buffer, sizeof(buffer));
#else
	cmd->buf = buffer;
#endif
	cmd->used_len = 0;
	cmd->total_len = BUFFER_LENGTH;

	/* Perform IOCTL */
	memset(&ifr, 0, sizeof(struct ifreq));
	strncpy(ifr.ifr_ifrn.ifrn_name, dev_name, strlen(dev_name));
	ifr.ifr_ifru.ifru_data = (void *)cmd;

	if (ioctl(sockfd, MLAN_ETH_PRIV, &ifr)) {
		perror("mlanutl");
		fprintf(stderr, "mlanutl: bssrole fail\n");
		if (cmd)
			free(cmd);
		if (buffer)
			free(buffer);
		return MLAN_STATUS_FAILURE;
	}

	/* Process result */
	if (argc == 3) {
		/* GET operation */
		printf("BSS role: %d\n", buffer[0]);
	}

	if (buffer)
		free(buffer);
	if (cmd)
		free(cmd);

	return MLAN_STATUS_SUCCESS;
}
#endif
#endif

#ifdef STA_SUPPORT
/**
 *  @brief Helper function for process_getscantable_idx
 *
 *  @param pbuf     A pointer to the buffer
 *  @param buf_len  Buffer length
 *
 *  @return         NA
 *
 */
static void
dump_scan_elems(const t_u8 *pbuf, uint buf_len)
{
	uint idx;
	uint marker = 2 + pbuf[1];

	for (idx = 0; idx < buf_len; idx++) {
		if (idx % 0x10 == 0) {
			printf("\n%04x: ", idx);
		}

		if (idx == marker) {
			printf("|");
			marker = idx + pbuf[idx + 1] + 2;
		} else {
			printf(" ");
		}

		printf("%02x ", pbuf[idx]);
	}

	printf("\n");
}
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
int
main(int argc, char *argv[])
{
	int ret = MLAN_STATUS_SUCCESS;

	if ((argc == 2) && (strcmp(argv[1], "-v") == 0)) {
		fprintf(stdout, "NXP mlanutl version %s\n", MLANUTL_VER);
		exit(0);
	}
	if (argc < 3) {
		fprintf(stderr, "Invalid number of parameters!\n");
		display_usage();
		exit(1);
	}

	strncpy(dev_name, argv[1], IFNAMSIZ - 1);

	/*
	 * Create a socket
	 */
	sockfd = socket(AF_INET, SOCK_STREAM, 0);
	if (sockfd < 0) {
		fprintf(stderr, "mlanutl: Cannot open socket.\n");
		exit(1);
	}

	ret = process_command(argc, argv);

	if (ret == MLAN_STATUS_NOTFOUND) {
		ret = process_generic(argc, argv);

		if (ret) {
			fprintf(stderr, "Invalid command specified!\n");
			display_usage();
			ret = 1;
		}
	}

	close(sockfd);
	return ret;
}
