balena-io-hardware/fin-info-doc/software/drivers/sd8887/src/wlan/mlan/mlan_fw.h

#define _MLAN_FW_H_
#define INTF_HEADER_LEN     4
#ifdef PRAGMA_PACK
#pragma pack(push, 1)
#endif
#define WPA_CCMP_256_KEY_LEN 32
typedef MLAN_PACK_START struct {
	t_u8 dest_addr[MLAN_MAC_ADDR_LENGTH];
	t_u8 src_addr[MLAN_MAC_ADDR_LENGTH];
	t_u16 h803_len;
} MLAN_PACK_END Eth803Hdr_t;
typedef MLAN_PACK_START struct {
	t_u8 llc_dsap;
	t_u8 llc_ssap;
	t_u8 llc_ctrl;
	t_u8 snap_oui[3];
	t_u16 snap_type;
} MLAN_PACK_END Rfc1042Hdr_t;
typedef MLAN_PACK_START struct {
	Eth803Hdr_t eth803_hdr;
	Rfc1042Hdr_t rfc1042_hdr;
} MLAN_PACK_END RxPacketHdr_t;
#define B_SUPPORTED_RATES               5
#define G_SUPPORTED_RATES               9
#define BG_SUPPORTED_RATES              13
#define A_SUPPORTED_RATES               9
#define QOS_DATA                        8
#define SHORT_SLOT_TIME_DISABLED(CapInfo) (CapInfo &= ~MBIT(10))
#define SHORT_SLOT_TIME_ENABLED(CapInfo)  (CapInfo |= MBIT(10))
#define SPECTRUM_MGMT_DISABLED(CapInfo) (CapInfo &= ~MBIT(8))
#define SPECTRUM_MGMT_ENABLED(CapInfo)  ( CapInfo |= MBIT(8))
#define RADIO_MEASUREMENT_DISABLED(CapInfo) (CapInfo &= ~MBIT(12))
#define RADIO_MEASUREMENT_ENABLED(CapInfo)  ( CapInfo |= MBIT(12))
#define HOSTCMD_SUPPORTED_RATES         14
#define N_SUPPORTED_RATES               3
#ifdef STA_SUPPORT
#define ALL_802_11_BANDS           (BAND_A | BAND_B | BAND_G | BAND_GN | BAND_AAC | BAND_GAC)
#else
#define ALL_802_11_BANDS        (BAND_B | BAND_G | BAND_A)
#endif
#ifdef STA_SUPPORT
#define FW_MULTI_BANDS_SUPPORT  (MBIT(8)  | MBIT(9)  | MBIT(10) | MBIT(11) | \
							MBIT(12) | MBIT(13))
#else
#define FW_MULTI_BANDS_SUPPORT  (MBIT(8) | MBIT(9) | MBIT(10))
#endif
#define IS_SUPPORT_MULTI_BANDS(_adapter)        \
	(_adapter->fw_cap_info & FW_MULTI_BANDS_SUPPORT)
#define GET_FW_DEFAULT_BANDS(_adapter)  \
	(((((_adapter->fw_cap_info & 0x3000) << 1) | \
	  (_adapter->fw_cap_info & ~0xF000)) >> 8) & ALL_802_11_BANDS)
extern t_u8 SupportedRates_B[B_SUPPORTED_RATES];
extern t_u8 SupportedRates_G[G_SUPPORTED_RATES];
extern t_u8 SupportedRates_BG[BG_SUPPORTED_RATES];
extern t_u8 SupportedRates_A[A_SUPPORTED_RATES];
extern t_u8 SupportedRates_N[N_SUPPORTED_RATES];
extern t_u8 AdhocRates_G[G_SUPPORTED_RATES];
extern t_u8 AdhocRates_B[B_SUPPORTED_RATES];
extern t_u8 AdhocRates_BG[BG_SUPPORTED_RATES];
extern t_u8 AdhocRates_A[A_SUPPORTED_RATES];
#define WAKEUP_FW_UNCHANGED                     0
#define WAKEUP_FW_THRU_INTERFACE                1
#define WAKEUP_FW_THRU_GPIO                     2
#define DEF_WAKEUP_FW_GPIO                      0
#define DEFAULT_AUTO_DS_MODE                  MTRUE
#define DEFAULT_PS_MODE                 Wlan802_11PowerModePSP
#define EVENT_NAN_GENERIC 0x00000075
#define NAN_EVT_SUBTYPE_SD_EVENT 0
#define NAN_EVT_SUBTYPE_NAN_STARTED 1
#define NAN_EVT_SUBTYPE_SDF_TX_DONE 2
#define HostCmd_WEP_KEY_INDEX_MASK              0x3fff
#define WEP_40_BIT_LEN  5
#define WEP_104_BIT_LEN 13
#define KEY_INFO_ENABLED        0x01
typedef enum _KEY_TYPE_ID {
	KEY_TYPE_ID_WEP = 0,
	KEY_TYPE_ID_TKIP = 1,
	KEY_TYPE_ID_AES = 2,
	KEY_TYPE_ID_WAPI = 3,
	KEY_TYPE_ID_AES_CMAC = 4,
	KEY_TYPE_ID_CCMP_256 = 7,
} KEY_TYPE_ID;
#define KEY_INFO_MCAST_KEY      0x01
#define KEY_INFO_UCAST_KEY      0x02
typedef enum _KEY_INFO_WEP {
	KEY_INFO_WEP_MCAST = 0x01,
	KEY_INFO_WEP_UNICAST = 0x02,
	KEY_INFO_WEP_ENABLED = 0x04
} KEY_INFO_WEP;
typedef enum _KEY_INFO_TKIP {
	KEY_INFO_TKIP_MCAST = 0x01,
	KEY_INFO_TKIP_UNICAST = 0x02,
	KEY_INFO_TKIP_ENABLED = 0x04
} KEY_INFO_TKIP;
typedef enum _KEY_INFO_AES {
	KEY_INFO_AES_MCAST = 0x01,
	KEY_INFO_AES_UNICAST = 0x02,
	KEY_INFO_AES_ENABLED = 0x04,
	KEY_INFO_AES_MCAST_IGTK = 0x400,
} KEY_INFO_AES;
#define WPA_AES_KEY_LEN                 16
#define WPA_TKIP_KEY_LEN                32
#define CMAC_AES_KEY_LEN                16
#define WPA_IGTK_KEY_LEN                16
#define WAPI_KEY_LEN            50
typedef enum _KEY_INFO_WAPI {
	KEY_INFO_WAPI_MCAST = 0x01,
	KEY_INFO_WAPI_UNICAST = 0x02,
	KEY_INFO_WAPI_ENABLED = 0x04
} KEY_INFO_WAPI;
#define MV_ETH_FRAME_LEN   1514
#define MRVDRV_SNAP_HEADER_LEN          8
#define MAX_POLL_TRIES			100
#define MAX_MULTI_INTERFACE_POLL_TRIES  150
#define MAX_FIRMWARE_POLL_TRIES		100
#define EXTRA_LEN	256
#define MRVDRV_ETH_TX_PACKET_BUFFER_SIZE \
	(MV_ETH_FRAME_LEN + sizeof(TxPD) + EXTRA_LEN)
#define MRVDRV_ETH_RX_PACKET_BUFFER_SIZE \
	(MV_ETH_FRAME_LEN + sizeof(RxPD) \
	 + MRVDRV_SNAP_HEADER_LEN + EXTRA_LEN)
#define FIRMWARE_READY          0xfedc
#define FIRMWARE_TRANSFER_NBLOCK	2
typedef enum _WLAN_802_11_PRIVACY_FILTER {
	Wlan802_11PrivFilterAcceptAll,
	Wlan802_11PrivFilter8021xWEP
} WLAN_802_11_PRIVACY_FILTER;
typedef enum _WLAN_802_11_WEP_STATUS {
	Wlan802_11WEPEnabled,
	Wlan802_11WEPDisabled,
	Wlan802_11WEPKeyAbsent,
	Wlan802_11WEPNotSupported
} WLAN_802_11_WEP_STATUS;
#define CAL_SNR(RSSI, NF)		((t_s16)((t_s16)(RSSI) - (t_s16)(NF)))
#define MLAN_TX_DATA_BUF_SIZE_2K        2048
#define PROPRIETARY_TLV_BASE_ID                 0x0100
#define MRVL_TERMINATE_TLV_ID                   0xffff
#define TLV_TYPE_SSID                           0x0000
#define TLV_TYPE_RATES                          0x0001
#define TLV_TYPE_PHY_FH                         0x0002
#define TLV_TYPE_PHY_DS                         0x0003
#define TLV_TYPE_CF                             0x0004
#define TLV_TYPE_IBSS                           0x0006
#define TLV_TYPE_DOMAIN                         0x0007
#define TLV_TYPE_POWER_CONSTRAINT               0x0020
#define TLV_TYPE_POWER_CAPABILITY               0x0021
#define TLV_TYPE_HT_CAPABILITY                  0x002d
#define TLV_TYPE_HOST_MLME                      (PROPRIETARY_TLV_BASE_ID + 307)
#define TLV_TYPE_VENDOR_SPECIFIC_IE             0x00dd
#define TLV_TYPE_KEY_MATERIAL       (PROPRIETARY_TLV_BASE_ID + 0x00)
#define TLV_TYPE_CHANLIST           (PROPRIETARY_TLV_BASE_ID + 0x01)
#define TLV_TYPE_NUMPROBES          (PROPRIETARY_TLV_BASE_ID + 0x02)
#define TLV_TYPE_RSSI_LOW           (PROPRIETARY_TLV_BASE_ID + 0x04)
#define TLV_TYPE_SNR_LOW            (PROPRIETARY_TLV_BASE_ID + 0x05)
#define TLV_TYPE_FAILCOUNT          (PROPRIETARY_TLV_BASE_ID + 0x06)
#define TLV_TYPE_BCNMISS            (PROPRIETARY_TLV_BASE_ID + 0x07)
#define TLV_TYPE_LEDBEHAVIOR        (PROPRIETARY_TLV_BASE_ID + 0x09)
#define TLV_TYPE_PASSTHROUGH        (PROPRIETARY_TLV_BASE_ID + 0x0a)
#define TLV_TYPE_POWER_TBL_2_4GHZ   (PROPRIETARY_TLV_BASE_ID + 0x0c)
#define TLV_TYPE_POWER_TBL_5GHZ     (PROPRIETARY_TLV_BASE_ID + 0x0d)
#define TLV_TYPE_WMMQSTATUS         (PROPRIETARY_TLV_BASE_ID + 0x10)
#define TLV_TYPE_WILDCARDSSID       (PROPRIETARY_TLV_BASE_ID + 0x12)
#define TLV_TYPE_TSFTIMESTAMP       (PROPRIETARY_TLV_BASE_ID + 0x13)
#define TLV_TYPE_ARP_FILTER         (PROPRIETARY_TLV_BASE_ID + 0x15)
#define TLV_TYPE_RSSI_HIGH          (PROPRIETARY_TLV_BASE_ID + 0x16)
#define TLV_TYPE_SNR_HIGH           (PROPRIETARY_TLV_BASE_ID + 0x17)
#define TLV_TYPE_STARTBGSCANLATER   (PROPRIETARY_TLV_BASE_ID + 0x1e)
#define TLV_TYPE_REPEAT_COUNT       (PROPRIETARY_TLV_BASE_ID + 0xb0)
#define TLV_TYPE_AUTH_TYPE          (PROPRIETARY_TLV_BASE_ID + 0x1f)
#define TLV_TYPE_BSSID              (PROPRIETARY_TLV_BASE_ID + 0x23)
#define TLV_TYPE_LINK_QUALITY       (PROPRIETARY_TLV_BASE_ID + 0x24)
#define TLV_TYPE_RSSI_LOW_DATA      (PROPRIETARY_TLV_BASE_ID + 0x26)
#define TLV_TYPE_SNR_LOW_DATA       (PROPRIETARY_TLV_BASE_ID + 0x27)
#define TLV_TYPE_RSSI_HIGH_DATA     (PROPRIETARY_TLV_BASE_ID + 0x28)
#define TLV_TYPE_SNR_HIGH_DATA      (PROPRIETARY_TLV_BASE_ID + 0x29)
#define TLV_TYPE_CHANNELBANDLIST    (PROPRIETARY_TLV_BASE_ID + 0x2a)
#define TLV_TYPE_PASSPHRASE         (PROPRIETARY_TLV_BASE_ID + 0x3c)
#define TLV_TYPE_ENCRYPTION_PROTO   (PROPRIETARY_TLV_BASE_ID + 0x40)
#define TLV_TYPE_CIPHER             (PROPRIETARY_TLV_BASE_ID + 0x42)
#define TLV_TYPE_PMK                (PROPRIETARY_TLV_BASE_ID + 0x44)
#define TLV_TYPE_PRE_BCNMISS         (PROPRIETARY_TLV_BASE_ID + 0x49)
#define TLV_TYPE_WAPI_IE             (PROPRIETARY_TLV_BASE_ID + 0x5e)
#define TLV_TYPE_MGMT_IE             (PROPRIETARY_TLV_BASE_ID + 0x69)
#define TLV_TYPE_MAX_MGMT_IE         (PROPRIETARY_TLV_BASE_ID + 0xaa)
#define TLV_TYPE_KEY_PARAM_V2        (PROPRIETARY_TLV_BASE_ID + 0x9C)
#define TLV_TYPE_PS_PARAMS_IN_HS     (PROPRIETARY_TLV_BASE_ID + 0xB5)
#define TLV_TYPE_HS_WAKE_HOLDOFF     (PROPRIETARY_TLV_BASE_ID + 0xB6)
#define TLV_TYPE_HS_WAKEUP_SOURCE_GPIO     (PROPRIETARY_TLV_BASE_ID + 0x105)
#define TLV_TYPE_MGMT_FRAME_WAKEUP     (PROPRIETARY_TLV_BASE_ID + 0x116)
#define TLV_TYPE_WAKEUP_EXTEND       (PROPRIETARY_TLV_BASE_ID + 0x118)
#define TLV_TYPE_ROBUSTCOEX           (PROPRIETARY_TLV_BASE_ID + 0x11B)
#define TLV_TYPE_TDLS_IDLE_TIMEOUT   (PROPRIETARY_TLV_BASE_ID + 0xC2)
#define TLV_TYPE_HT_CAP              (PROPRIETARY_TLV_BASE_ID + 0x4a)
#define TLV_TYPE_HT_INFO             (PROPRIETARY_TLV_BASE_ID + 0x4b)
#define TLV_SECONDARY_CHANNEL_OFFSET (PROPRIETARY_TLV_BASE_ID + 0x4c)
#define TLV_TYPE_2040BSS_COEXISTENCE (PROPRIETARY_TLV_BASE_ID + 0x4d)
#define TLV_TYPE_OVERLAP_BSS_SCAN_PARAM (PROPRIETARY_TLV_BASE_ID + 0x4e)
#define TLV_TYPE_EXTCAP              (PROPRIETARY_TLV_BASE_ID + 0x4f)
#define TLV_TYPE_HT_OPERATIONAL_MCS_SET (PROPRIETARY_TLV_BASE_ID + 0x50)
#define TLV_TYPE_MGMT_FRAME          (PROPRIETARY_TLV_BASE_ID + 0x68)
#define TLV_TYPE_RXBA_SYNC           (PROPRIETARY_TLV_BASE_ID + 0x99)
#ifdef WIFI_DIRECT_SUPPORT
#define TLV_TYPE_UAP_PSK   (PROPRIETARY_TLV_BASE_ID + 0xa8)
#define TLV_TYPE_WIFI_DIRECT_NOA            (PROPRIETARY_TLV_BASE_ID + 0x83)
#define TLV_TYPE_WIFI_DIRECT_OPP_PS         (PROPRIETARY_TLV_BASE_ID + 0x84)
#endif
#define TLV_TYPE_2040_BSS_COEX_CONTROL\
		(PROPRIETARY_TLV_BASE_ID + 0x98)
#define TLV_BTCOEX_WL_AGGR_WINSIZE					(PROPRIETARY_TLV_BASE_ID + 0xca)
#define TLV_BTCOEX_WL_SCANTIME    					(PROPRIETARY_TLV_BASE_ID + 0Xcb)
#define TLV_TYPE_EAPOL_PKT                          (PROPRIETARY_TLV_BASE_ID + 0xcf)
#define TLV_TYPE_COALESCE_RULE                      (PROPRIETARY_TLV_BASE_ID + 0x9a)
#define TLV_TYPE_EES_CFG                            (PROPRIETARY_TLV_BASE_ID + 0xda)
#define TLV_TYPE_EES_NET_CFG                        (PROPRIETARY_TLV_BASE_ID + 0xdb)
#define ADDBA_TID_MASK   (MBIT(2) | MBIT(3) | MBIT(4) | MBIT(5))
#define DELBA_TID_MASK   (MBIT(12) | MBIT(13) | MBIT(14) | MBIT(15))
#define SSN_MASK         0xfff0
#define BA_RESULT_SUCCESS        0x0
#define BA_RESULT_FAILURE        0x1
#define BA_RESULT_TIMEOUT        0x2
#define BA_RESULT_DATA_INVALID   0x3
#define IS_BASTREAM_SETUP(ptr)  (ptr->ba_status)
#define BA_STREAM_NOT_ALLOWED   0xff
#define IS_11N_ENABLED(priv) ((priv->config_bands & BAND_GN || priv->config_bands & BAND_AN) \
	 && priv->curr_bss_params.bss_descriptor.pht_cap && !priv->curr_bss_params.bss_descriptor.disable_11n)
#define INITIATOR_BIT(DelBAParamSet) (((DelBAParamSet) & \
			MBIT(DELBA_INITIATOR_POS)) >> DELBA_INITIATOR_POS)
#define MLAN_TX_DATA_BUF_SIZE_4K        4096
#define MLAN_TX_DATA_BUF_SIZE_8K        8192
#define MLAN_TX_DATA_BUF_SIZE_12K        12288
#define MAX_RX_AMPDU_SIZE_64K   0x03
#define NON_GREENFIELD_STAS     0x04
#define HWSPEC_GREENFIELD_SUPP   MBIT(29)
#define HWSPEC_RXSTBC_SUPP   MBIT(26)
#define HWSPEC_SHORTGI40_SUPP    MBIT(24)
#define HWSPEC_SHORTGI20_SUPP    MBIT(23)
#define HWSPEC_LDPC_SUPP         MBIT(22)
#define HWSPEC_CHANBW40_SUPP     MBIT(17)
#define CAPINFO_40MHZ_INTOLARENT MBIT(8)
#define DEFAULT_11N_CAP_MASK_BG (HWSPEC_SHORTGI20_SUPP | HWSPEC_RXSTBC_SUPP | HWSPEC_LDPC_SUPP)
#define DEFAULT_11N_CAP_MASK_A  (HWSPEC_CHANBW40_SUPP | HWSPEC_SHORTGI20_SUPP | \
		HWSPEC_SHORTGI40_SUPP | HWSPEC_RXSTBC_SUPP | HWSPEC_LDPC_SUPP)
#define DEFAULT_11N_TX_BF_CAP   0x19E74608
#define IGN_HW_DEV_CAP      (CAPINFO_40MHZ_INTOLARENT)
#define ISSUPP_RSN_REPLAY_DETECTION(FwCapInfo) (FwCapInfo & MBIT(28))
#define ISSUPP_11NENABLED(FwCapInfo) (FwCapInfo & MBIT(11))
#define ISSUPP_MAXAMSDU(Dot11nDevCap) (Dot11nDevCap & MBIT(31))
#define ISSUPP_BEAMFORMING(Dot11nDevCap) (Dot11nDevCap & MBIT(30))
#define ISSUPP_GREENFIELD(Dot11nDevCap) (Dot11nDevCap & MBIT(29))
#define ISSUPP_AMPDU(Dot11nDevCap) (Dot11nDevCap & MBIT(28))
#define ISSUPP_MIMOPS(Dot11nDevCap) (Dot11nDevCap & MBIT(27))
#define ISSUPP_RXSTBC(Dot11nDevCap) (Dot11nDevCap & MBIT(26))
#define ISSUPP_TXSTBC(Dot11nDevCap) (Dot11nDevCap & MBIT(25))
#define ISSUPP_SHORTGI40(Dot11nDevCap) (Dot11nDevCap & MBIT(24))
#define RESETSUPP_SHORTGI40(Dot11nDevCap) (Dot11nDevCap &= ~MBIT(24))
#define ISSUPP_SHORTGI20(Dot11nDevCap) (Dot11nDevCap & MBIT(23))
#define ISSUPP_RXLDPC(Dot11nDevCap) (Dot11nDevCap & MBIT(22))
#define ISSUPP_GETTXBASTREAM(Dot11nDevCap) ((Dot11nDevCap >> 18) & 0xF)
#define ISSUPP_CHANWIDTH40(Dot11nDevCap) (Dot11nDevCap & MBIT(17))
#define ISSUPP_CHANWIDTH20(Dot11nDevCap) (Dot11nDevCap & MBIT(16))
#define ISSUPP_CHANWIDTH10(Dot11nDevCap) (Dot11nDevCap & MBIT(15))
#define ISENABLED_40MHZ_INTOLARENT(Dot11nDevCap) (Dot11nDevCap & MBIT(8))
#define RESET_40MHZ_INTOLARENT(Dot11nDevCap) (Dot11nDevCap &= ~MBIT(8))
#define ISSUPP_RXANTENNAD(Dot11nDevCap) (Dot11nDevCap & MBIT(7))
#define ISSUPP_RXANTENNAC(Dot11nDevCap) (Dot11nDevCap & MBIT(6))
#define ISSUPP_RXANTENNAB(Dot11nDevCap) (Dot11nDevCap & MBIT(5))
#define ISSUPP_RXANTENNAA(Dot11nDevCap) (Dot11nDevCap & MBIT(4))
#define ISSUPP_TXANTENNAD(Dot11nDevCap) (Dot11nDevCap & MBIT(3))
#define ISSUPP_TXANTENNAC(Dot11nDevCap) (Dot11nDevCap & MBIT(2))
#define ISSUPP_TXANTENNAB(Dot11nDevCap) (Dot11nDevCap & MBIT(1))
#define ISSUPP_TXANTENNAA(Dot11nDevCap) (Dot11nDevCap & MBIT(0))
#define SETSUPP_CHANWIDTH40(Dot11nDevCap) (Dot11nDevCap |= MBIT(17))
#define RESETSUPP_CHANWIDTH40(Dot11nDevCap) (Dot11nDevCap &= ~MBIT(17))
#define GET_TXMCSSUPP(DevMCSSupported) (DevMCSSupported >> 4)
#define GET_RXMCSSUPP(DevMCSSupported) (DevMCSSupported & 0x0f)
#define GETHT_SUPPCHANWIDTH(HTCapInfo) (HTCapInfo & MBIT(1))
#define GETHT_GREENFIELD(HTCapInfo) (HTCapInfo & MBIT(4))
#define GETHT_SHORTGI20(HTCapInfo) (HTCapInfo & MBIT(5))
#define GETHT_SHORTGI40(HTCapInfo) (HTCapInfo & MBIT(6))
#define GETHT_TXSTBC(HTCapInfo) (HTCapInfo & MBIT(7))
#define GETHT_RXSTBC(HTCapInfo) ((HTCapInfo >> 8) & 0x03)
#define GETHT_DELAYEDBACK(HTCapInfo) (HTCapInfo & MBIT(10))
#define GETHT_MAXAMSDU(HTCapInfo) (HTCapInfo & MBIT(11))
#define GETHT_40MHZ_INTOLARANT(HTCapInfo) (HTCapInfo & MBIT(14))
#define SETHT_LDPCCODINGCAP(HTCapInfo) (HTCapInfo |= MBIT(0))
#define SETHT_SUPPCHANWIDTH(HTCapInfo) (HTCapInfo |= MBIT(1))
#define SETHT_GREENFIELD(HTCapInfo) (HTCapInfo |= MBIT(4))
#define SETHT_SHORTGI20(HTCapInfo) (HTCapInfo |= MBIT(5))
#define SETHT_SHORTGI40(HTCapInfo) (HTCapInfo |= MBIT(6))
#define SETHT_TXSTBC(HTCapInfo) (HTCapInfo |= MBIT(7))
#define SETHT_RXSTBC(HTCapInfo, value) (HTCapInfo |= (value << 8))
#define SETHT_DELAYEDBACK(HTCapInfo) (HTCapInfo |= MBIT(10))
#define SETHT_MAXAMSDU(HTCapInfo) (HTCapInfo |= MBIT(11))
#define SETHT_DSSSCCK40(HTCapInfo) (HTCapInfo |= MBIT(12))
#define SETHT_40MHZ_INTOLARANT(HTCapInfo) (HTCapInfo |= MBIT(14))
#define SETHT_STATIC_SMPS(HTCapInfo) ((HTCapInfo) |= (MBIT(2) | MBIT(3)))
#define RESETHT_LDPCCODINGCAP(HTCapInfo) (HTCapInfo &= ~MBIT(0))
#define RESETHT_SUPPCHANWIDTH(HTCapInfo) (HTCapInfo &= ~MBIT(1))
#define RESETHT_GREENFIELD(HTCapInfo) (HTCapInfo &= ~MBIT(4))
#define RESETHT_SHORTGI20(HTCapInfo) (HTCapInfo &= ~MBIT(5))
#define RESETHT_SHORTGI40(HTCapInfo) (HTCapInfo &= ~MBIT(6))
#define RESETHT_TXSTBC(HTCapInfo) (HTCapInfo &= ~MBIT(7))
#define RESETHT_RXSTBC(HTCapInfo) (HTCapInfo &= ~(0x03 << 8))
#define RESETHT_DELAYEDBACK(HTCapInfo) (HTCapInfo &= ~MBIT(10))
#define RESETHT_MAXAMSDU(HTCapInfo) (HTCapInfo &= ~MBIT(11))
#define RESETHT_40MHZ_INTOLARANT(HTCapInfo) (HTCapInfo &= ~MBIT(14))
#define RESETHT_SM_POWERSAVE(HTCapInfo) ((HTCapInfo) &= ~(MBIT(2) | MBIT(3)))
#define RESETHT_EXTCAP_RDG(HTExtCap) (HTExtCap &= ~MBIT(11))
#define SETHT_MCS32(x) (x[4] |= 1)
#define SETHT_MCS_SET_DEFINED(x) (x[12] |= 1)
#define SETHT_RX_HIGHEST_DT_SUPP(x, y) ((*(t_u16 *) (x + 10)) = y)
#define AMPDU_FACTOR_64K	0x03
#define SETAMPDU_SIZE(x, y) do { \
	x = x & ~0x03; \
	x |= y & 0x03; \
} while (0) \
#define SETAMPDU_SPACING(x, y) do { \
	x = x & ~0x1c; \
	x |= (y & 0x07) << 2; \
} while (0) \
#define ISSUPP_BANDA(FwCapInfo) (FwCapInfo & MBIT(10))
#define ISALLOWED_CHANWIDTH40(Field2) (Field2 & MBIT(2))
#define SET_CHANWIDTH40(Field2) (Field2 |= MBIT(2))
#define RESET_CHANWIDTH40(Field2) (Field2 &= ~(MBIT(0) | MBIT(1) | MBIT(2)))
#define GET_SECONDARYCHAN(Field2) (Field2 & (MBIT(0) | MBIT(1)))
#define ISSUPP_EXTCAP_FILS(ext_cap) (ext_cap.FILS)
#define SET_EXTCAP_FILS(ext_cap) (ext_cap.FILS = 1)
#define RESET_EXTCAP_FILS(ext_cap) (ext_cap.FILS = 0)
#define ISSUPP_EXTCAP_TDLS(ext_cap) (ext_cap.TDLSSupport)
#define SET_EXTCAP_TDLS(ext_cap) (ext_cap.TDLSSupport = 1)
#define RESET_EXTCAP_TDLS(ext_cap) (ext_cap.TDLSSupport = 0)
#define ISSUPP_EXTCAP_TDLS_UAPSD(ext_cap) (ext_cap.TDLSPeerUAPSDSupport)
#define SET_EXTCAP_TDLS_UAPSD(ext_cap) (ext_cap.TDLSPeerUAPSDSupport = 1)
#define RESET_EXTCAP_TDLS_UAPSD(ext_cap) (ext_cap.TDLSPeerUAPSDSupport = 0)
#define ISSUPP_EXTCAP_TDLS_CHAN_SWITCH(ext_cap) (ext_cap.TDLSChannelSwitching)
#define SET_EXTCAP_TDLS_CHAN_SWITCH(ext_cap) (ext_cap.TDLSChannelSwitching = 1)
#define RESET_EXTCAP_TDLS_CHAN_SWITCH(ext_cap) (ext_cap.TDLSChannelSwitching = 0)
#define ISSUPP_EXTCAP_INTERWORKING(ext_cap) (ext_cap.Interworking)
#define SET_EXTCAP_INTERWORKING(ext_cap) (ext_cap.Interworking = 1)
#define RESET_EXTCAP_INTERWORKING(ext_cap) (ext_cap.Interworking = 0)
#define ISSUPP_EXTCAP_OPERMODENTF(ext_cap) (ext_cap.OperModeNtf)
#define SET_EXTCAP_OPERMODENTF(ext_cap) (ext_cap.OperModeNtf = 1)
#define RESET_EXTCAP_OPERMODENTF(ext_cap) (ext_cap.OperModeNtf = 0)
#define ISSUPP_EXTCAP_QOS_MAP(ext_cap) (ext_cap.Qos_Map)
#define SET_EXTCAP_QOS_MAP(ext_cap) (ext_cap.Qos_Map = 1)
#define RESET_EXTCAP_QOS_MAP(ext_cap) (ext_cap.Qos_Map = 0)
#define ISSUPP_EXTCAP_BSS_TRANSITION(ext_cap) (ext_cap.BSS_Transition)
#define SET_EXTCAP_BSS_TRANSITION(ext_cap) (ext_cap.BSS_Transition = 1)
#define RESET_EXTCAP_BSS_TRANSITION(ext_cap) (ext_cap.BSS_Transition = 0)
#define ISSUPP_EXTCAP_TDLS_WIDER_BANDWIDTH(ext_cap) (ext_cap.TDLSWildBandwidth)
#define SET_EXTCAP_TDLS_WIDER_BANDWIDTH(ext_cap) (ext_cap.TDLSWildBandwidth = 1)
#define RESET_EXTCAP_TDLS_WIDER_BANDWIDTH(ext_cap) (ext_cap.TDLSWildBandwidth = 0)
#define ISSUPP_EXTCAP_EXT_CHANNEL_SWITCH(ext_cap) (ext_cap.ExtChanSwitching)
#define SET_EXTCAP_EXT_CHANNEL_SWITCH(ext_cap) (ext_cap.ExtChanSwitching = 1)
#define SET_EXTCAP_EXT_TIMING_MEASUREMENT(ext_cap) (ext_cap.TimingMeasurement = 1)
#define RESET_EXTCAP_EXT_CHANNEL_SWITCH(ext_cap) (ext_cap.ExtChanSwitching = 0)
#define LLC_SNAP_LEN    8
#define BW_FOLLOW_HTCAP             0
#define BW_FOLLOW_VHTCAP            1
#define HWSPEC_11ACSGI80_SUPP       MBIT(5)
#define HWSPEC_11ACRXSTBC_SUPP      MBIT(8)
#define ISSUPP_11ACENABLED(FwCapInfo) (FwCapInfo & (MBIT(12)|MBIT(13)))
#define ISSUPP_11AC2GENABLED(FwCapInfo) (FwCapInfo & MBIT(12))
#define ISSUPP_11AC5GENABLED(FwCapInfo) (FwCapInfo & MBIT(13))
#define ISSUPP_11ACVHTHTCVHT(Dot11acDevCap) (Dot11acDevCap & MBIT(22))
#define ISSUPP_11ACVHTTXOPPS(Dot11acDevCap) (Dot11acDevCap & MBIT(21))
#define ISSUPP_11ACMURXBEAMFORMEE(Dot11acDevCap) (Dot11acDevCap & MBIT(20))
#define ISSUPP_11ACMUTXBEAMFORMEE(Dot11acDevCap) (Dot11acDevCap & MBIT(19))
#define ISSUPP_11ACSUBEAMFORMEE(Dot11acDevCap) (Dot11acDevCap & MBIT(12))
#define ISSUPP_11ACSUBEAMFORMER(Dot11acDevCap) (Dot11acDevCap & MBIT(11))
#define ISSUPP_11ACRXSTBC(Dot11acDevCap) (Dot11acDevCap & MBIT(8))
#define ISSUPP_11ACTXSTBC(Dot11acDevCap) (Dot11acDevCap & MBIT(7))
#define ISSUPP_11ACSGI160(Dot11acDevCap) (Dot11acDevCap & MBIT(6))
#define ISSUPP_11ACSGI80(Dot11acDevCap) (Dot11acDevCap & MBIT(5))
#define ISSUPP_11ACLDPC(Dot11acDevCap) (Dot11acDevCap & MBIT(4))
#define ISSUPP_11ACBW8080(Dot11acDevCap) (Dot11acDevCap & MBIT(3))
#define ISSUPP_11ACBW160(Dot11acDevCap) (Dot11acDevCap & MBIT(2))
#define SET_VHTCAP_MAXMPDULEN(VHTCapInfo, value) (VHTCapInfo |= (value & 0x03))
#define SET_VHTCAP_CHWDSET(VHTCapInfo, value) (VHTCapInfo |= ((value & 0x3) << 2))
#define SET_VHTCAP_RXSTBC(VHTCapInfo, value) (VHTCapInfo |= ((value & 0x7) << 8))
#define SET_VHTCAP_SNBFERANT(VHTCapInfo, value) (VHTCapInfo |= ((value & 0x7) << 13))
#define SET_VHTCAP_NUMSNDDM(VHTCapInfo, value) (VHTCapInfo |= ((value & 0x7) << 16))
#define SET_VHTCAP_MAXAMPDULENEXP(VHTCapInfo, value) (VHTCapInfo |= ((value & 0x7) << 23))
#define SET_VHTCAP_LINKADPCAP(VHTCapInfo, value) (VHTCapInfo |= ((value & 0x3) << 26))
#define RESET_11ACVHTLINKCAPA(Dot11acDevCap, value) (Dot11acDevCap &= ~(0x03))
#define RESET_11ACAMPDULENEXP(Dot11acDevCap, value) (Dot11acDevCap &= ~(0x07))
#define RESET_11ACVHTHTCVHT(Dot11acDevCap) (Dot11acDevCap &= ~MBIT(22))
#define RESET_11ACVHTTXOPPS(Dot11acDevCap) (Dot11acDevCap &= ~MBIT(21))
#define RESET_11ACMURXBEAMFORMEE(Dot11acDevCap) (Dot11acDevCap &= ~MBIT(20))
#define RESET_11ACMUTXBEAMFORMEE(Dot11acDevCap) (Dot11acDevCap &= ~MBIT(19))
#define RESET_11ACSOUNDINGNUM(Dot11acDevCap) (Dot11acDevCap &= ~((0x07) << 16))
#define RESET_11ACBFANTNUM(Dot11acDevCap) (Dot11acDevCap &= ~((0x07) << 13))
#define RESET_11ACSUBEAMFORMEE(Dot11acDevCap) (Dot11acDevCap &= ~MBIT(12))
#define RESET_11ACSUBEAMFORMER(Dot11acDevCap) (Dot11acDevCap &= ~MBIT(11))
#define RESET_11ACRXSTBC(Dot11acDevCap) (Dot11acDevCap &= ~((0x07) << 8))
#define RESET_11ACTXSTBC(Dot11acDevCap) (Dot11acDevCap &= ~MBIT(7))
#define RESET_11ACSGI160(Dot11acDevCap) (Dot11acDevCap &= ~MBIT(6))
#define RESET_11ACSGI80(Dot11acDevCap) (Dot11acDevCap &= ~MBIT(5))
#define RESET_11ACLDPC(Dot11acDevCap) (Dot11acDevCap &= ~MBIT(4))
#define RESET_11ACBW8080(Dot11acDevCap) (Dot11acDevCap &= ~MBIT(3))
#define RESET_11ACBW160(Dot11acDevCap) (Dot11acDevCap &= ~MBIT(2))
#define RESET_11ACMAXMPDULEN(Dot11acDevCap) (Dot11acDevCap &= ~(0x03))
#define DEFAULT_11AC_CAP_MASK_BG (HWSPEC_11ACSGI80_SUPP | HWSPEC_11ACRXSTBC_SUPP)
#define DEFAULT_11AC_CAP_MASK_A  (HWSPEC_11ACSGI80_SUPP | HWSPEC_11ACRXSTBC_SUPP)
#define GET_VHTCAP_MAXMPDULEN(VHTCapInfo) (VHTCapInfo & 0x3)
#define GET_VHTCAP_CHWDSET(VHTCapInfo)    ((VHTCapInfo >> 2) & 0x3)
#define GET_VHTCAP_RXSTBC(VHTCapInfo)     ((VHTCapInfo >> 8) & 0x7)
#define GET_VHTCAP_SNBFERANT(VHTCapInfo)  ((VHTCapInfo >> 13) & 0x7)
#define GET_VHTCAP_NUMSNDDM(VHTCapInfo)   ((VHTCapInfo >> 16) & 0x7)
#define GET_VHTCAP_MAXAMPDULENEXP(VHTCapInfo)   ((VHTCapInfo >> 23) & 0x7)
#define GET_VHTCAP_LINKADPCAP(VHTCapInfo)  ((VHTCapInfo >> 26) & 0x3)
#define SET_OPER_MODE_80M(oper_mode)  (oper_mode = (oper_mode & ~MBIT(0))| MBIT(1))
#define SET_OPER_MODE_40M(oper_mode)  (oper_mode = (oper_mode & ~MBIT(1))| MBIT(0))
#define SET_OPER_MODE_20M(oper_mode)  (oper_mode &= ~(0x03))
#define IS_OPER_MODE_20M(oper_mode) (((oper_mode) & (MBIT(0) | MBIT(1))) == 0)
#define SET_OPER_MODE_2NSS(oper_mode)  (oper_mode = (oper_mode &~(MBIT(5)|MBIT(6)))| MBIT(4))
#define SET_OPER_MODE_1NSS(oper_mode)  (oper_mode &= ~(MBIT(4)|MBIT(5)|MBIT(6)))
#define GET_VHTMCS(MCSMapSet)         (MCSMapSet & 0xFFFF)
#define GET_VHTNSSMCS(MCSMapSet, nss) ((MCSMapSet >> (2*(nss-1)))&0x3)
#define RET_VHTNSSMCS(MCSMapSet, nss) ((MCSMapSet >> (2*(nss-1)))&0x3)
#define SET_VHTNSSMCS(MCSMapSet, nss, value) \
            (MCSMapSet |= (value & 0x3) << (2 * (nss - 1)))
#define GET_DEVTXMCSMAP(DevMCSMap)      (DevMCSMap >> 16)
#define GET_DEVNSSTXMCS(DevMCSMap, nss) ((DevMCSMap >> (2*(nss-1)+16))&0x3)
#define SET_DEVNSSTXMCS(DevMCSMap, nss, value) \
            (DevMCSMap |= (value & 0x3) << (2 * (nss - 1) + 16))
#define RESET_DEVTXMCSMAP(DevMCSMap)    (DevMCSMap &= 0xFFFF)
#define GET_DEVRXMCSMAP(DevMCSMap)      (DevMCSMap & 0xFFFF)
#define GET_DEVNSSRXMCS(DevMCSMap, nss) ((DevMCSMap >> (2*(nss-1)))&0x3)
#define SET_DEVNSSRXMCS(DevMCSMap, nss, value) \
            (DevMCSMap |= (value & 0x3) << (2 * (nss - 1)))
#define RESET_DEVRXMCSMAP(DevMCSMap)    (DevMCSMap &= 0xFFFF0000)
#define TLV_TYPE_RATE_DROP_PATTERN  (PROPRIETARY_TLV_BASE_ID + 0x51)
#define TLV_TYPE_RATE_DROP_CONTROL  (PROPRIETARY_TLV_BASE_ID + 0x52)
#define TLV_TYPE_RATE_SCOPE         (PROPRIETARY_TLV_BASE_ID + 0x53)
#define TLV_TYPE_POWER_GROUP        (PROPRIETARY_TLV_BASE_ID + 0x54)
#define MOD_CLASS_HR_DSSS       0x03
#define MOD_CLASS_OFDM          0x07
#define MOD_CLASS_HT            0x08
#define MOD_CLASS_VHT           0x09
#define HT_BW_20    0
#define HT_BW_40    1
#define HT_BW_80    2
#define TLV_TYPE_BSS_SCAN_RSP        (PROPRIETARY_TLV_BASE_ID + 0x56)
#define TLV_TYPE_BSS_SCAN_INFO       (PROPRIETARY_TLV_BASE_ID + 0x57)
#define TLV_TYPE_CHANRPT_11H_BASIC   (PROPRIETARY_TLV_BASE_ID + 0x5b)
#define TLV_TYPE_IEEE_ACTION_FRAME   (PROPRIETARY_TLV_BASE_ID + 0x8c)
#define TLV_TYPE_SCAN_CHANNEL_GAP    (PROPRIETARY_TLV_BASE_ID + 0xc5)
#define TLV_TYPE_CHANNEL_STATS       (PROPRIETARY_TLV_BASE_ID + 0xc6)
#define TLV_TYPE_BSS_MODE            (PROPRIETARY_TLV_BASE_ID + 0xce)
#define HostCmd_CMD_GET_HW_SPEC               0x0003
#define HostCmd_CMD_802_11_SCAN               0x0006
#define HostCmd_CMD_802_11_GET_LOG            0x000b
#define HostCmd_CMD_MAC_MULTICAST_ADR         0x0010
#define HostCmd_CMD_802_11_EEPROM_ACCESS      0x0059
#define HostCmd_CMD_802_11_ASSOCIATE          0x0012
#define HostCmd_CMD_802_11_SNMP_MIB           0x0016
#define HostCmd_CMD_MAC_REG_ACCESS            0x0019
#define HostCmd_CMD_BBP_REG_ACCESS            0x001a
#define HostCmd_CMD_RF_REG_ACCESS             0x001b
#define HostCmd_CMD_802_11_RADIO_CONTROL      0x001c
#define HostCmd_CMD_802_11_RF_CHANNEL         0x001d
#define HostCmd_CMD_802_11_RF_TX_POWER        0x001e
#define HostCmd_CMD_802_11_RF_ANTENNA         0x0020
#define HostCmd_CMD_802_11_DEAUTHENTICATE     0x0024
#define HostCmd_CMD_802_11_DISASSOCIATE       0x0026
#define HostCmd_CMD_MAC_CONTROL               0x0028
#define HostCmd_CMD_802_11_AD_HOC_START       0x002b
#define HostCmd_CMD_802_11_AD_HOC_JOIN        0x002c
#define HostCmd_CMD_CW_MODE_CTRL              0x0239
#define HostCmd_CMD_802_11_KEY_MATERIAL       0x005e
#define HostCmd_CMD_802_11_AD_HOC_STOP        0x0040
#define HostCmd_CMD_802_11_MAC_ADDRESS        0x004D
#define HostCmd_CMD_WMM_TS_STATUS             0x005d
#define HostCmd_CMD_802_11D_DOMAIN_INFO       0x005b
#define HostCmd_CHANNEL_TRPC_CONFIG           0x00fb
#define HostCmd_CMD_802_11_TPC_INFO           0x005f
#define HostCmd_CMD_802_11_TPC_ADAPT_REQ      0x0060
#define HostCmd_CMD_802_11_CHAN_SW_ANN        0x0061
#define HostCmd_CMD_MEASUREMENT_REQUEST       0x0062
#define HostCmd_CMD_MEASUREMENT_REPORT        0x0063
#define HostCmd_CMD_802_11_SLEEP_PARAMS       0x0066
#define HostCmd_CMD_802_11_PS_INACTIVITY_TIMEOUT 0x0067
#define HostCmd_CMD_802_11_SLEEP_PERIOD       0x0068
#define HostCmd_CMD_802_11_BG_SCAN_CONFIG     0x006b
#define HostCmd_CMD_802_11_BG_SCAN_QUERY      0x006c
#define HostCmd_CMD_WMM_ADDTS_REQ             0x006E
#define HostCmd_CMD_WMM_DELTS_REQ             0x006F
#define HostCmd_CMD_WMM_QUEUE_CONFIG          0x0070
#define HostCmd_CMD_WMM_GET_STATUS            0x0071
#define HostCmd_CMD_802_11_FW_WAKE_METHOD     0x0074
#define HostCmd_CMD_802_11_SUBSCRIBE_EVENT    0x0075
#define HostCmd_CMD_802_11_TX_RATE_QUERY      0x007f
#define HostCmd_CMD_GET_TSF                   0x0080
#define HostCmd_CMD_WMM_QUEUE_STATS           0x0081
#define HostCmd_CMD_802_11_IBSS_COALESCING_STATUS 0x0083
#define HostCmd_CMD_MEM_ACCESS                0x0086
#define HostCmd_CMD_SDIO_GPIO_INT_CONFIG      0x0088
#ifdef MFG_CMD_SUPPORT
#define HostCmd_CMD_MFG_COMMAND               0x0089
#endif
#define HostCmd_CMD_INACTIVITY_TIMEOUT_EXT    0x008a
#define HostCmd_CMD_DBGS_CFG                  0x008b
#define HostCmd_CMD_GET_MEM                   0x008c
#define HostCmd_CMD_CFG_DATA                  0x008f
#define HostCmd_CMD_SDIO_PULL_CTRL            0x0093
#define HostCmd_CMD_ECL_SYSTEM_CLOCK_CONFIG   0x0094
#define HostCmd_CMD_VERSION_EXT               0x0097
#define HostCmd_CMD_MEF_CFG                   0x009a
#define HostCmd_CMD_RSSI_INFO                 0x00a4
#define HostCmd_CMD_FUNC_INIT                 0x00a9
#define HostCmd_CMD_FUNC_SHUTDOWN             0x00aa
#define HostCmd_CMD_802_11_ROBUSTCOEX                0x00e0
#define HostCmd_CMD_802_11_EAPOL_PKT    			0x012e
#define HostCmd_CMD_RSSI_INFO_EXT             0x0237
#define HostCmd_CMD_MULTI_CHAN_CONFIG                0x011e
#define HostCmd_CMD_MULTI_CHAN_POLICY                0x0121
#define TLV_TYPE_MULTI_CHAN_INFO             (PROPRIETARY_TLV_BASE_ID + 0xb7)
#define TLV_TYPE_MULTI_CHAN_GROUP_INFO_TLV_ID (PROPRIETARY_TLV_BASE_ID + 0xb8)
#define MRVL_DRCS_TIME_SLICE_TLV_ID  (PROPRIETARY_TLV_BASE_ID + 263)
#define HostCmd_CMD_DRCS_CONFIG                     0x024a
#ifdef RX_PACKET_COALESCE
#define TLV_TYPE_RX_PKT_COAL_CONFIG           (PROPRIETARY_TLV_BASE_ID + 0xC9)
#endif
#define HostCmd_CMD_CHAN_REPORT_REQUEST              0x00dd
#define HostCmd_CMD_SUPPLICANT_PMK            0x00c4
#define HostCmd_CMD_SUPPLICANT_PROFILE        0x00c5
#define HostCmd_CMD_11N_ADDBA_REQ             0x00ce
#define HostCmd_CMD_11N_CFG                   0x00cd
#define HostCmd_CMD_11N_ADDBA_RSP             0x00cf
#define HostCmd_CMD_11N_DELBA                 0x00d0
#define HostCmd_CMD_RECONFIGURE_TX_BUFF       0x00d9
#define HostCmd_CMD_AMSDU_AGGR_CTRL           0x00df
#define HostCmd_CMD_11AC_CFG                   0x0112
#define HostCmd_CMD_TX_BF_CFG                 0x0104
#define HostCmd_CMD_TXPWR_CFG                 0x00d1
#define  HostCmd_CMD_SOFT_RESET               0x00d5
#define HostCmd_CMD_TX_RATE_CFG               0x00d6
#define HostCmd_CMD_802_11_PS_MODE_ENH        0x00e4
#define HostCmd_CMD_802_11_HS_CFG_ENH         0x00e5
#define HostCmd_CMD_CAU_REG_ACCESS            0x00ed
#define  HostCmd_CMD_MGMT_IE_LIST             0x00f2
#define  HostCmd_CMD_TDLS_CONFIG              0x0100
#define HostCmd_CMD_TDLS_OPERATION          0x0122
#define HostCmd_CMD_SDIO_SP_RX_AGGR_CFG     0x0223
#define SDIO_SP_RX_AGGR_ENABLE          MBIT(16)
#define FW_CAPINFO_ECSA          MBIT(18)
#define FW_CAPINFO_GET_LOG          MBIT(20)
#define FW_CAPINFO_SUPPLICANT_SUPPORT    MBIT(21)
#define FW_CAPINFO_AUTH_SUPPORT    MBIT(22)
#define FW_CAPINFO_ADHOC_SUPPORT    MBIT(25)
#define IS_FW_SUPPORT_ADHOC(_adapter)    (_adapter->fw_cap_info & FW_CAPINFO_ADHOC_SUPPORT)
#define IS_FW_SUPPORT_SUPPLICANT(_adapter)    (_adapter->fw_cap_info & FW_CAPINFO_SUPPLICANT_SUPPORT)
#define IS_FW_SUPPORT_AUTHENTICATOR(_adapter)    (_adapter->fw_cap_info & FW_CAPINFO_AUTH_SUPPORT)
#ifdef RX_PACKET_COALESCE
#define HostCmd_CMD_RX_PKT_COALESCE_CFG       0x012c
#endif
#define  HostCmd_CMD_802_11_SCAN_EXT          0x0107
#define HostCmd_CMD_RX_MGMT_IND               0x010c
#define HostCmd_CMD_SET_BSS_MODE               0x00f7
#ifdef UAP_SUPPORT
#define HOST_CMD_APCMD_SYS_INFO                0x00ae
#define HOST_CMD_APCMD_SYS_RESET               0x00af
#define HOST_CMD_APCMD_SYS_CONFIGURE           0x00b0
#define HOST_CMD_APCMD_BSS_START               0x00b1
#define HOST_CMD_APCMD_BSS_STOP                0x00b2
#define HOST_CMD_APCMD_STA_LIST                0x00b3
#define HOST_CMD_APCMD_STA_DEAUTH              0x00b5
#define HOST_CMD_APCMD_OPER_CTRL              0x0233
#endif
#define HOST_CMD_PMIC_CONFIGURE                0x23E
#define HostCmd_CMD_CFG_TX_DATA_PAUSE           0x0103
#ifdef WIFI_DIRECT_SUPPORT
#define HOST_CMD_P2P_PARAMS_CONFIG              0x00ea
#define HOST_CMD_WIFI_DIRECT_MODE_CONFIG    0x00eb
#endif
#define HostCmd_CMD_802_11_REMAIN_ON_CHANNEL     0x010d
#define HostCmd_CMD_COALESCE_CFG                 0x010a
#define HostCmd_CMD_GTK_REKEY_OFFLOAD_CFG       0x010f
#define HostCmd_CMD_OTP_READ_USER_DATA          0x0114
#define HostCmd_CMD_HS_WAKEUP_REASON         0x0116
#define HostCmd_CMD_REJECT_ADDBA_REQ         0x0119
#define HostCmd_CMD_FW_DUMP_EVENT            0x0125
#define HostCMD_CONFIG_LOW_POWER_MODE   0x0128
#define HostCmd_CMD_TARGET_ACCESS            0x012a
#define HostCmd_DS_GET_SENSOR_TEMP	0x0227
#define HostCmd_CMD_WMM_PARAM_CONFIG                0x023a
#ifdef STA_SUPPORT
#define HostCmd_CMD_STA_CONFIGURE            0x023f
#endif
#define HostCmd_CMD_CHAN_REGION_CFG			0x0242
typedef enum _mod_grp {
	MOD_CCK,		//0
	MOD_OFDM_PSK,		//1
	MOD_OFDM_QAM16,		//2
	MOD_OFDM_QAM64,		//3
	MOD_HT_20_PSK,		//4
	MOD_HT_20_QAM16,	//5
	MOD_HT_20_QAM64,	//6
	MOD_HT_40_PSK,		//7
	MOD_HT_40_QAM16,	//8
	MOD_HT_40_QAM64,	//9
#ifdef STREAM_2x2
	MOD_HT2_20_PSK,		//10
	MOD_HT2_20_QAM16,	//11
	MOD_HT2_20_QAM64,	//12
	MOD_HT2_40_PSK,		//13
	MOD_HT2_40_QAM16,	//14
	MOD_HT2_40_QAM64,	//15
#endif
	MOD_VHT_20_QAM256,	//16
	MOD_VHT_40_QAM256,	//17
	MOD_VHT_80_PSK,		//18
	MOD_VHT_80_QAM16,	//19
	MOD_VHT_80_QAM64,	//20
	MOD_VHT_80_QAM256,	//21
#ifdef STREAM_2x2
	MOD_VHT2_20_QAM256,	//22
	MOD_VHT2_40_QAM256,	//23
	MOD_VHT2_80_PSK,	//24
	MOD_VHT2_80_QAM16,	//25
	MOD_VHT2_80_QAM64,	//26
	MOD_VHT2_80_QAM256,	//27
#endif
} mod_grp;
typedef MLAN_PACK_START struct _power_table_attr {
	t_u8 rows_2g;
	t_u8 cols_2g;
	t_u8 rows_5g;
	t_u8 cols_5g;
} MLAN_PACK_END power_table_attr_t;
#define FW_CFP_TABLE_MAX_ROWS_BG		14
#define FW_CFP_TABLE_MAX_COLS_BG		11
#define FW_CFP_TABLE_MAX_ROWS_A		39
#define FW_CFP_TABLE_MAX_COLS_A		17
#define HostCmd_CMD_DYN_BW                  0x0252
#define HostCmd_CMD_BOOT_SLEEP              0x0258
#define HostCmd_CMD_TX_AMPDU_PROT_MODE      0x0263
#define HostCmd_CMD_ACS     0x025a
typedef enum _ENH_PS_MODES {
	GET_PS = 0,
	SLEEP_CONFIRM = 5,
	DIS_AUTO_PS = 0xfe,
	EN_AUTO_PS = 0xff,
} ENH_PS_MODES;
#define HostCmd_RET_BIT                       0x8000
#define HostCmd_ACT_GEN_GET                   0x0000
#define HostCmd_ACT_GEN_SET                   0x0001
#define HostCmd_ACT_GEN_GET_CURRENT           0x0003
#define HostCmd_ACT_GEN_REMOVE                0x0004
#define HostCmd_ACT_GEN_RESET                 0x0005
#define HostCmd_ACT_SET_RX                    0x0001
#define HostCmd_ACT_SET_TX                    0x0002
#define HostCmd_ACT_SET_BOTH                  0x0003
#define HostCmd_ACT_GET_RX                    0x0004
#define HostCmd_ACT_GET_TX                    0x0008
#define HostCmd_ACT_GET_BOTH                  0x000c
#define HostCmd_RESULT_OK                     0x0000
#define HostCmd_RESULT_ERROR                  0x0001
#define HostCmd_RESULT_NOT_SUPPORT            0x0002
#define HostCmd_RESULT_PENDING                0x0003
#define HostCmd_RESULT_BUSY                   0x0004
#define HostCmd_RESULT_PARTIAL_DATA           0x0005
#define HostCmd_ACT_MAC_RX_ON                 0x0001
#define HostCmd_ACT_MAC_TX_ON                 0x0002
#define HostCmd_ACT_MAC_WEP_ENABLE            0x0008
#define HostCmd_ACT_MAC_ETHERNETII_ENABLE     0x0010
#define HostCmd_ACT_MAC_PROMISCUOUS_ENABLE    0x0080
#define HostCmd_ACT_MAC_ALL_MULTICAST_ENABLE  0x0100
#define HostCmd_ACT_MAC_RTS_CTS_ENABLE        0x0200
#define HostCmd_ACT_MAC_STRICT_PROTECTION_ENABLE  0x0400
#define HostCmd_ACT_MAC_FORCE_11N_PROTECTION_OFF  0x0800
#define HostCmd_ACT_MAC_ADHOC_G_PROTECTION_ON     0x2000
#define HostCmd_ACT_MAC_STATIC_DYNAMIC_BW_ENABLE  MBIT(16)
#define HostCmd_ACT_MAC_DYNAMIC_BW                MBIT(17)
#define HostCmd_BSS_MODE_BSS                0x0001
#define HostCmd_BSS_MODE_IBSS               0x0002
#define HostCmd_BSS_MODE_ANY                0x0003
#define HOST_SLEEP_CFG_GPIO_FF              0xff
#define HOST_SLEEP_CFG_GAP_FF               0xff
#define MRVDRV_NUM_OF_CMD_BUFFER        30
#define MRVDRV_MAX_BSSID_LIST           200
#define CMD_F_HOSTCMD           (1 << 0)
#define CMD_F_CANCELED          (1 << 1)
#define CMD_F_SCAN              (1 << 2)
#define HostCmd_CMD_ID_MASK             0x0fff
#define HostCmd_SEQ_NUM_MASK            0x00ff
#define HostCmd_BSS_NUM_MASK            0x0f00
#define HostCmd_BSS_TYPE_MASK           0xf000
#define HostCmd_SET_SEQ_NO_BSS_INFO(seq, num, type)    \
	((((seq) & 0x00ff) |         \
		(((num) & 0x000f) << 8)) | \
		(((type) & 0x000f) << 12))
#define HostCmd_GET_SEQ_NO(seq)       \
	((seq) & HostCmd_SEQ_NUM_MASK)
#define HostCmd_GET_BSS_NO(seq)         \
	(((seq) & HostCmd_BSS_NUM_MASK) >> 8)
#define HostCmd_GET_BSS_TYPE(seq)       \
	(((seq) & HostCmd_BSS_TYPE_MASK) >> 12)
#define EVENT_DUMMY_HOST_WAKEUP_SIGNAL  0x00000001
#define EVENT_LINK_LOST                 0x00000003
#define EVENT_LINK_SENSED               0x00000004
#define EVENT_MIB_CHANGED               0x00000006
#define EVENT_INIT_DONE                 0x00000007
#define EVENT_DEAUTHENTICATED           0x00000008
#define EVENT_DISASSOCIATED             0x00000009
#define EVENT_PS_AWAKE                  0x0000000a
#define EVENT_PS_SLEEP                  0x0000000b
#define EVENT_MIC_ERR_MULTICAST         0x0000000d
#define EVENT_MIC_ERR_UNICAST           0x0000000e
#define EVENT_ADHOC_BCN_LOST            0x00000011
#define EVENT_STOP_TX                   0x00000013
#define EVENT_START_TX                  0x00000014
#define EVENT_CHANNEL_SWITCH            0x00000015
#define EVENT_MEAS_REPORT_RDY           0x00000016
#define EVENT_WMM_STATUS_CHANGE         0x00000017
#define EVENT_BG_SCAN_REPORT            0x00000018
#define EVENT_BG_SCAN_STOPPED       0x00000065
#define EVENT_RSSI_LOW                  0x00000019
#define EVENT_SNR_LOW                   0x0000001a
#define EVENT_MAX_FAIL                  0x0000001b
#define EVENT_RSSI_HIGH                 0x0000001c
#define EVENT_SNR_HIGH                  0x0000001d
#define EVENT_IBSS_COALESCED            0x0000001e
#define EVENT_IBSS_STATION_CONNECT      0x00000020
#define EVENT_IBSS_STATION_DISCONNECT   0x00000021
#define EVENT_DATA_RSSI_LOW             0x00000024
#define EVENT_DATA_SNR_LOW              0x00000025
#define EVENT_DATA_RSSI_HIGH            0x00000026
#define EVENT_DATA_SNR_HIGH             0x00000027
#define EVENT_LINK_QUALITY              0x00000028
#define EVENT_PORT_RELEASE              0x0000002b
#define EVENT_PRE_BEACON_LOST           0x00000031
#define EVENT_ADDBA                     0x00000033
#define EVENT_DELBA                     0x00000034
#define EVENT_BA_STREAM_TIMEOUT         0x00000037
#define EVENT_AMSDU_AGGR_CTRL           0x00000042
#define EVENT_WEP_ICV_ERR               0x00000046
#define EVENT_HS_ACT_REQ                0x00000047
#define EVENT_BW_CHANGE                 0x00000048
#ifdef WIFI_DIRECT_SUPPORT
#define EVENT_WIFIDIRECT_GENERIC_EVENT         0x00000049
#define EVENT_WIFIDIRECT_SERVICE_DISCOVERY     0x0000004a
#endif
#define EVENT_REMAIN_ON_CHANNEL_EXPIRED        0x0000005f
#define EVENT_TDLS_GENERIC_EVENT        0x00000052
#define EVENT_CHANNEL_SWITCH_ANN        0x00000050
#define EVENT_RADAR_DETECTED            0x00000053
#define EVENT_CHANNEL_REPORT_RDY        0x00000054
#define EVENT_EXT_SCAN_REPORT           0x00000058
#define EVENT_EXT_SCAN_STATUS_REPORT    0x0000007f
#define EVENT_FW_DEBUG_INFO             0x00000063
#define EVENT_RXBA_SYNC                 0x00000059
#ifdef UAP_SUPPORT
#define EVENT_MICRO_AP_STA_DEAUTH       0x0000002c
#define EVENT_MICRO_AP_STA_ASSOC        0x0000002d
#define EVENT_MICRO_AP_BSS_START        0x0000002e
#define EVENT_MICRO_AP_BSS_IDLE         0x00000043
#define EVENT_MICRO_AP_BSS_ACTIVE       0x00000044
#endif
#define EVENT_TX_DATA_PAUSE                  0x00000055
#define EVENT_SAD_REPORT                     0x00000066
#define EVENT_MULTI_CHAN_INFO               0x0000006a
#define EVENT_TX_STATUS_REPORT               0x00000074
#define EVENT_BT_COEX_WLAN_PARA_CHANGE	 0x00000076
#define EVENT_RESET_PN_ON_REKEY         0x00000092
#define EVENT_EXCEED_MAX_P2P_CONN     0x00000089
#define EVENT_FW_HANG_REPORT     0x0000008F
#define EVENT_FW_DUMP_INFO      0x00000073
#define EVENT_ID_MASK                   0xffff
#define BSS_NUM_MASK                    0xf
#define EVENT_GET_BSS_NUM(event_cause)          \
	(((event_cause) >> 16) & BSS_NUM_MASK)
#define EVENT_GET_BSS_TYPE(event_cause)         \
	(((event_cause) >> 24) & 0x00ff)
#define TDLS_EVENT_TYPE_SETUP_FAILURE         1
#define TDLS_EVENT_TYPE_SETUP_REQ             2
#define TDLS_EVENT_TYPE_LINK_TORN_DOWN        3
#define TDLS_EVENT_TYPE_LINK_ESTABLISHED      4
#define TDLS_EVENT_TYPE_DEBUG                 5
#define TDLS_EVENT_TYPE_PACKET                6
#define TDLS_EVENT_TYPE_CHAN_SWITCH_RESULT    7
#define TDLS_EVENT_TYPE_START_CHAN_SWITCH     8
#define TDLS_EVENT_TYPE_CHAN_SWITCH_STOPPED    9
#define RXPD_FLAG_PKT_DIRECT_LINK             1
#define TDLS_BASE_CHANNEL   0
#define TDLS_OFF_CHANNEL    1
typedef MLAN_PACK_START struct _chan_switch_result {
	t_u8 current_channel;
	t_u8 status;
	t_u8 reason;
} MLAN_PACK_END chan_switch_result;
typedef MLAN_PACK_START struct _ie_data {
	t_u16 ie_length;
	t_u8 ie_ptr[0];
} MLAN_PACK_END tdls_ie_data;
typedef MLAN_PACK_START struct _Event_tdls_generic {
	t_u16 event_type;
	t_u8 peer_mac_addr[MLAN_MAC_ADDR_LENGTH];
	union {
		chan_switch_result switch_result;
		t_u8 cs_stop_reason;
		t_u16 reason_code;
		tdls_ie_data ie_data;
	} u;
} MLAN_PACK_END Event_tdls_generic;
typedef enum _tdls_error_code_e {
	NO_ERROR = 0,
	INTERNAL_ERROR,
	MAX_TDLS_LINKS_EST,
	TDLS_LINK_EXISTS,
	TDLS_LINK_NONEXISTENT,
	TDLS_PEER_STA_UNREACHABLE = 25,
} tdls_error_code_e;
typedef MLAN_PACK_START struct _event_nan_generic {
	t_u16 event_sub_type;
} MLAN_PACK_END event_nan_generic;
#define RXPD_FLAG_PN_CHECK_SUPPORT             (1 << 2)
typedef MLAN_PACK_START struct _Event_WEP_ICV_ERR {
	t_u16 reason_code;
	t_u8 src_mac_addr[MLAN_MAC_ADDR_LENGTH];
	t_u8 wep_key_index;
	t_u8 wep_key_length;
	t_u8 key[MAX_WEP_KEY_SIZE];
} MLAN_PACK_END Event_WEP_ICV_ERR;
typedef MLAN_PACK_START struct _WLAN_802_11_FIXED_IEs {
	t_u8 time_stamp[8];
	t_u16 beacon_interval;
	t_u16 capabilities;
} MLAN_PACK_END WLAN_802_11_FIXED_IEs;
typedef MLAN_PACK_START struct _WLAN_802_11_VARIABLE_IEs {
	t_u8 element_id;
	t_u8 length;
	t_u8 data[1];
} MLAN_PACK_END WLAN_802_11_VARIABLE_IEs;
#define TDLS_IDLE_TIMEOUT             60
typedef MLAN_PACK_START struct _MrvlIEtypes_TDLS_Idle_Timeout_t {
	MrvlIEtypesHeader_t header;
	t_u16 value;
} MLAN_PACK_END MrvlIEtypes_TDLS_Idle_Timeout_t;
#if defined(STA_SUPPORT)
#define PAIRWISE_CIPHER_SUITE_LEN    4
#define AKM_SUITE_LEN    4
#define MFPC_BIT    7
#define MFPR_BIT    6
#endif
#define MRVDRV_TxPD_POWER_MGMT_NULL_PACKET 0x01
#define MRVDRV_TxPD_POWER_MGMT_LAST_PACKET 0x08
#define MRVDRV_TxPD_FLAGS_TDLS_PACKET MBIT(4)
#define MRVDRV_TxPD_FLAGS_TX_PACKET_STATUS  MBIT(5)
#define PKT_TYPE_802DOT11   0x05
#define PKT_TYPE_MGMT_FRAME 0xE5
#define PKT_TYPE_AMSDU      0xE6
#define PKT_TYPE_BAR        0xE7
#define PKT_TYPE_DEBUG      0xEF
#define RXPD_CHAN_MASK		0x3FE0
#define TXPD_RATE_MASK		0xff8000
#define TXPD_BW_ENABLE		MBIT(20)
#define TXPD_TXPW_ENABLE    MBIT(7)
#define TXPD_TXPW_NEGATIVE	MBIT(6)
#define TXPD_TXRATE_ENABLE	MBIT(15)
#define TXPD_RETRY_ENABLE	MBIT(12)
typedef MLAN_PACK_START struct _TxPD {
	t_u8 bss_type;
	t_u8 bss_num;
	t_u16 tx_pkt_length;
	t_u16 tx_pkt_offset;
	t_u16 tx_pkt_type;
	t_u32 tx_control;
	t_u8 priority;
	t_u8 flags;
	t_u8 pkt_delay_2ms;
	t_u8 reserved;
	t_u32 tx_control_1;
} MLAN_PACK_END TxPD, *PTxPD;
typedef MLAN_PACK_START struct _RxPD {
	t_u8 bss_type;
	t_u8 bss_num;
	t_u16 rx_pkt_length;
	t_u16 rx_pkt_offset;
	t_u16 rx_pkt_type;
	t_u16 seq_num;
	t_u8 priority;
	t_u8 rx_rate;
	t_s8 snr;
	t_s8 nf;
	t_u8 rate_info;
	t_u8 reserved[3];
	t_u8 flags;
	t_u8 antenna;
	t_u64 toa_tod_tstamps;
	t_u32 rx_info;
	t_u32 hi_rx_count32;
	t_u16 lo_rx_count16;
	t_u8 reserved3[2];
} MLAN_PACK_END RxPD, *PRxPD;
typedef MLAN_PACK_START struct _IEEEtypes_FrameCtl_t {
	t_u8 protocol_version:2;
	t_u8 type:2;
	t_u8 sub_type:4;
	t_u8 to_ds:1;
	t_u8 from_ds:1;
	t_u8 more_frag:1;
	t_u8 retry:1;
	t_u8 pwr_mgmt:1;
	t_u8 more_data:1;
	t_u8 wep:1;
	t_u8 order:1;
} MLAN_PACK_END IEEEtypes_FrameCtl_t;
typedef MLAN_PACK_START struct _MrvlIETypes_MgmtFrameSet_t {
	t_u16 type;
	t_u16 len;
	IEEEtypes_FrameCtl_t frame_control;
} MLAN_PACK_END MrvlIETypes_MgmtFrameSet_t;
typedef MLAN_PACK_START struct _IEEEtypes_Beacon_t {
	t_u8 time_stamp[8];
	t_u16 beacon_interval;
	t_u16 cap_info;
} MLAN_PACK_END IEEEtypes_Beacon_t;
#define ASSOC_EVENT_FIX_SIZE    12
typedef MLAN_PACK_START struct _MrvlIEtypes_channel_band_t {
	MrvlIEtypesHeader_t header;
	Band_Config_t bandcfg;
	t_u8 channel;
} MLAN_PACK_END MrvlIEtypes_channel_band_t;
#ifdef UAP_SUPPORT
typedef MLAN_PACK_START struct _UapTxPD {
	t_u8 bss_type;
	t_u8 bss_num;
	t_u16 tx_pkt_length;
	t_u16 tx_pkt_offset;
	t_u16 tx_pkt_type;
	t_u32 tx_control;
	t_u8 priority;
	t_u8 flags;
	t_u8 pkt_delay_2ms;
	t_u8 reserved;
	t_u32 tx_control_1;
} MLAN_PACK_END UapTxPD, *PUapTxPD;
typedef MLAN_PACK_START struct _UapRxPD {
	t_u8 bss_type;
	t_u8 bss_num;
	t_u16 rx_pkt_length;
	t_u16 rx_pkt_offset;
	t_u16 rx_pkt_type;
	t_u16 seq_num;
	t_u8 priority;
	t_u8 rx_rate;
	t_s8 snr;
	t_s8 nf;
	t_u8 rate_info;
	t_u8 reserved1[3];
	t_u8 flags;
	t_u8 antenna;
	t_u64 toa_tod_tstamps;
	t_u32 rx_info;
	t_u32 hi_rx_count32;
	t_u16 lo_rx_count16;
	t_u8 reserved3[2];
} MLAN_PACK_END UapRxPD, *PUapRxPD;
typedef MLAN_PACK_START struct _IEEEtypes_AssocRqst_t {
	t_u16 cap_info;
	t_u16 listen_interval;
} MLAN_PACK_END IEEEtypes_AssocRqst_t;
typedef MLAN_PACK_START struct _IEEEtypes_ReAssocRqst_t {
	t_u16 cap_info;
	t_u16 listen_interval;
	t_u8 current_ap_addr[MLAN_MAC_ADDR_LENGTH];
} MLAN_PACK_END IEEEtypes_ReAssocRqst_t;
#endif
typedef MLAN_PACK_START struct _wlan_802_11_header {
	t_u16 frm_ctl;
	t_u16 duration_id;
	mlan_802_11_mac_addr addr1;
	mlan_802_11_mac_addr addr2;
	mlan_802_11_mac_addr addr3;
	t_u16 seq_ctl;
	mlan_802_11_mac_addr addr4;
} MLAN_PACK_END wlan_802_11_header;
typedef MLAN_PACK_START struct _wlan_mgmt_pkt {
	t_u16 frm_len;
	wlan_802_11_header wlan_header;
} MLAN_PACK_END wlan_mgmt_pkt;
#ifdef STA_SUPPORT
#define MAX_NO_OF_CHAN          40
typedef MLAN_PACK_START struct _chan_power_11d {
	t_u8 chan;
	t_u8 band;
	t_u8 pwr;
	t_u8 ap_seen;
} MLAN_PACK_END chan_power_11d_t;
typedef MLAN_PACK_START struct _parsed_region_chan_11d {
	chan_power_11d_t chan_pwr[MAX_NO_OF_CHAN];
	t_u8 no_of_chan;
} MLAN_PACK_END parsed_region_chan_11d_t;
#endif
typedef MLAN_PACK_START struct _ChanScanMode_t {
#ifdef BIG_ENDIAN_SUPPORT
	t_u8 reserved_7:1;
	t_u8 passive_to_active_scan:1;
	t_u8 first_chan:1;
	t_u8 hidden_ssid_report:1;
	t_u8 rsp_timeout_en:1;
	t_u8 multidomain_scan:1;
	t_u8 disable_chan_filt:1;
	t_u8 passive_scan:1;
#else
	t_u8 passive_scan:1;
	t_u8 disable_chan_filt:1;
	t_u8 multidomain_scan:1;
	t_u8 rsp_timeout_en:1;
	t_u8 hidden_ssid_report:1;
	t_u8 first_chan:1;
	t_u8 passive_to_active_scan:1;
	t_u8 reserved_7:1;
#endif
} MLAN_PACK_END ChanScanMode_t;
typedef MLAN_PACK_START struct _ChanScanParamSet_t {
	Band_Config_t bandcfg;
	t_u8 chan_number;
	ChanScanMode_t chan_scan_mode;
	t_u16 min_scan_time;
	t_u16 max_scan_time;
} MLAN_PACK_END ChanScanParamSet_t;
typedef MLAN_PACK_START struct _MrvlIEtypes_ChanListParamSet_t {
	MrvlIEtypesHeader_t header;
	ChanScanParamSet_t chan_scan_param[1];
} MLAN_PACK_END MrvlIEtypes_ChanListParamSet_t;
typedef MLAN_PACK_START struct _MrvlIEtypes_EESParamSet_t {
	MrvlIEtypesHeader_t header;
	t_u16 ees_mode;
	t_u16 report_cond;
	t_u16 high_period;
	t_u16 high_period_count;
	t_u16 mid_period;
	t_u16 mid_period_count;
	t_u16 low_period;
	t_u16 low_period_count;
} MLAN_PACK_END MrvlIEtypes_EESParamSet_t;
typedef MLAN_PACK_START struct _MrvlIEtype_EESNetworkCfg_t {
	MrvlIEtypesHeader_t header;
	t_u8 network_count;
	t_u8 max_conn_count;
	t_u8 black_list_exp;
} MLAN_PACK_END MrvlIEtype_EESNetworkCfg_t;
typedef struct _ChanBandParamSet_t {
	Band_Config_t bandcfg;
	t_u8 chan_number;
} ChanBandParamSet_t;
typedef MLAN_PACK_START struct _MrvlIEtypes_ChanBandListParamSet_t {
	MrvlIEtypesHeader_t header;
	ChanBandParamSet_t chan_band_param[1];
} MLAN_PACK_END MrvlIEtypes_ChanBandListParamSet_t;
typedef MLAN_PACK_START struct _MrvlIEtypes_RatesParamSet_t {
	MrvlIEtypesHeader_t header;
	t_u8 rates[1];
} MLAN_PACK_END MrvlIEtypes_RatesParamSet_t;
typedef MLAN_PACK_START struct _MrvlIEtypes_Bssid_List_t {
	MrvlIEtypesHeader_t header;
	t_u8 bssid[MLAN_MAC_ADDR_LENGTH];
} MLAN_PACK_END MrvlIEtypes_Bssid_List_t;
typedef MLAN_PACK_START struct _MrvlIEtypes_SsIdParamSet_t {
	MrvlIEtypesHeader_t header;
	t_u8 ssid[1];
} MLAN_PACK_END MrvlIEtypes_SsIdParamSet_t;
typedef MLAN_PACK_START struct _MrvlIEtypes_HostMlme_t {
	MrvlIEtypesHeader_t header;
	t_u8 host_mlme;
} MLAN_PACK_END MrvlIEtypes_HostMlme_t;
typedef MLAN_PACK_START struct _MrvlIEtypes_NumProbes_t {
	MrvlIEtypesHeader_t header;
	t_u16 num_probes;
} MLAN_PACK_END MrvlIEtypes_NumProbes_t;
typedef MLAN_PACK_START struct _MrvlIEtypes_WildCardSsIdParamSet_t {
	MrvlIEtypesHeader_t header;
	t_u8 max_ssid_length;
	t_u8 ssid[1];
} MLAN_PACK_END MrvlIEtypes_WildCardSsIdParamSet_t;
#define TSF_DATA_SIZE            8
typedef MLAN_PACK_START struct _MrvlIEtypes_TsfTimestamp_t {
	MrvlIEtypesHeader_t header;
	t_u8 tsf_data[1];
} MLAN_PACK_END MrvlIEtypes_TsfTimestamp_t;
typedef MLAN_PACK_START struct _CfParamSet_t {
	t_u8 cfp_cnt;
	t_u8 cfp_period;
	t_u16 cfp_max_duration;
	t_u16 cfp_duration_remaining;
} MLAN_PACK_END CfParamSet_t;
typedef MLAN_PACK_START struct _IbssParamSet_t {
	t_u16 atim_window;
} MLAN_PACK_END IbssParamSet_t;
typedef MLAN_PACK_START struct _MrvlIEtypes_SsParamSet_t {
	MrvlIEtypesHeader_t header;
	union {
		CfParamSet_t cf_param_set[1];
		IbssParamSet_t ibss_param_set[1];
	} cf_ibss;
} MLAN_PACK_END MrvlIEtypes_SsParamSet_t;
typedef MLAN_PACK_START struct _FhParamSet_t {
	t_u16 dwell_time;
	t_u8 hop_set;
	t_u8 hop_pattern;
	t_u8 hop_index;
} MLAN_PACK_END FhParamSet_t;
typedef MLAN_PACK_START struct _DsParamSet_t {
	t_u8 current_chan;
} MLAN_PACK_END DsParamSet_t;
typedef MLAN_PACK_START struct _MrvlIEtypes_PhyParamSet_t {
	MrvlIEtypesHeader_t header;
	union {
		FhParamSet_t fh_param_set[1];
		DsParamSet_t ds_param_set[1];
	} fh_ds;
} MLAN_PACK_END MrvlIEtypes_PhyParamSet_t;
typedef MLAN_PACK_START struct _MrvlIEtypes_AuthType_t {
	MrvlIEtypesHeader_t header;
	t_u16 auth_type;
} MLAN_PACK_END MrvlIEtypes_AuthType_t;
typedef MLAN_PACK_START struct _MrvlIEtypes_ScanChanGap_t {
	MrvlIEtypesHeader_t header;
	t_u16 gap;
} MLAN_PACK_END MrvlIEtypes_ScanChanGap_t;
typedef MLAN_PACK_START struct _MrvlIEtypes_ChannelStats_t {
	MrvlIEtypesHeader_t header;
	ChanStatistics_t chanStat[0];
} MLAN_PACK_END MrvlIEtypes_ChannelStats_t;
typedef MLAN_PACK_START struct {
	MrvlIEtypesHeader_t header;
	t_u8 srcAddr[MLAN_MAC_ADDR_LENGTH];
	t_u8 dstAddr[MLAN_MAC_ADDR_LENGTH];
	IEEEtypes_ActionFrame_t actionFrame;
} MLAN_PACK_END MrvlIETypes_ActionFrame_t;
typedef MLAN_PACK_START struct _MrvlIEtypes_RxBaSync_t {
	MrvlIEtypesHeader_t header;
	t_u8 mac[MLAN_MAC_ADDR_LENGTH];
	t_u8 tid;
	t_u8 reserved;
	t_u16 seq_num;
	t_u16 bitmap_len;
	t_u8 bitmap[1];
} MLAN_PACK_END MrvlIEtypes_RxBaSync_t;
typedef MLAN_PACK_START struct _MrvlIEtypes_RsnParamSet_t {
	MrvlIEtypesHeader_t header;
	t_u8 rsn_ie[0];
} MLAN_PACK_END MrvlIEtypes_RsnParamSet_t;
#define KEY_INFO_MCAST_KEY      0x01
#define KEY_INFO_UCAST_KEY      0x02
#define KEY_INFO_ENABLE_KEY     0x04
#define KEY_INFO_DEFAULT_KEY    0x08
#define KEY_INFO_TX_KEY         0x10
#define KEY_INFO_RX_KEY         0x20
#define KEY_INFO_CMAC_AES_KEY   0x400
#define WPA_PN_SIZE             8
#define IGTK_PN_SIZE            8
#define WAPI_KEY_SIZE           32
#define KEY_PARAMS_FIXED_LEN    10
#define KEY_INDEX_MASK          0xf
typedef MLAN_PACK_START struct _wep_param_t {
	t_u16 key_len;
	t_u8 key[MAX_WEP_KEY_SIZE];
} MLAN_PACK_END wep_param_t;
typedef MLAN_PACK_START struct _tkip_param {
	t_u8 pn[WPA_PN_SIZE];
	t_u16 key_len;
	t_u8 key[WPA_TKIP_KEY_LEN];
} MLAN_PACK_END tkip_param;
typedef MLAN_PACK_START struct _aes_param {
	t_u8 pn[WPA_PN_SIZE];
	t_u16 key_len;
	t_u8 key[WPA_AES_KEY_LEN];
} MLAN_PACK_END aes_param;
typedef MLAN_PACK_START struct _wapi_param {
	t_u8 pn[PN_SIZE];
	t_u16 key_len;
	t_u8 key[WAPI_KEY_SIZE];
} MLAN_PACK_END wapi_param;
typedef MLAN_PACK_START struct _cmac_aes_param {
	t_u8 ipn[IGTK_PN_SIZE];
	t_u16 key_len;
	t_u8 key[CMAC_AES_KEY_LEN];
} MLAN_PACK_END cmac_aes_param;
typedef MLAN_PACK_START struct _ccmp256_param {
	t_u8 pn[WPA_PN_SIZE];
	t_u16 key_len;
	t_u8 key[WPA_CCMP_256_KEY_LEN];
} MLAN_PACK_END ccmp_256_param;
typedef MLAN_PACK_START struct _MrvlIEtype_KeyParamSetV2_t {
	t_u16 type;
	t_u16 length;
	t_u8 mac_addr[MLAN_MAC_ADDR_LENGTH];
	t_u8 key_idx;
	t_u8 key_type;
	t_u16 key_info;
	union {
		wep_param_t wep;
		tkip_param tkip;
		aes_param aes;
		wapi_param wapi;
		cmac_aes_param cmac_aes;
		ccmp_256_param ccmp256;
	} key_params;
} MLAN_PACK_END MrvlIEtype_KeyParamSetV2_t;
typedef MLAN_PACK_START struct _HostCmd_DS_802_11_KEY_MATERIAL {
	t_u16 action;
	MrvlIEtype_KeyParamSetV2_t key_param_set;
} MLAN_PACK_END HostCmd_DS_802_11_KEY_MATERIAL;
typedef MLAN_PACK_START struct _HostCmd_DS_GTK_REKEY_PARAMS {
	t_u16 action;
	t_u8 kck[MLAN_KCK_LEN];
	t_u8 kek[MLAN_KEK_LEN];
	t_u32 replay_ctr_low;
	t_u32 replay_ctr_high;
} MLAN_PACK_END HostCmd_DS_GTK_REKEY_PARAMS;
typedef MLAN_PACK_START struct _WmmQosInfo_t {
#ifdef BIG_ENDIAN_SUPPORT
	t_u8 qos_uapsd:1;
	t_u8 reserved:3;
	t_u8 para_set_count:4;
#else
	t_u8 para_set_count:4;
	t_u8 reserved:3;
	t_u8 qos_uapsd:1;
#endif
} MLAN_PACK_END WmmQosInfo_t, *pWmmQosInfo_t;
typedef MLAN_PACK_START struct _WmmEcw_t {
#ifdef BIG_ENDIAN_SUPPORT
	t_u8 ecw_max:4;
	t_u8 ecw_min:4;
#else
	t_u8 ecw_min:4;
	t_u8 ecw_max:4;
#endif
} MLAN_PACK_END WmmEcw_t, *pWmmEcw_t;
typedef MLAN_PACK_START struct _WmmAciAifsn_t {
#ifdef BIG_ENDIAN_SUPPORT
	t_u8 reserved:1;
	t_u8 aci:2;
	t_u8 acm:1;
	t_u8 aifsn:4;
#else
	t_u8 aifsn:4;
	t_u8 acm:1;
	t_u8 aci:2;
	t_u8 reserved:1;
#endif
} MLAN_PACK_END WmmAciAifsn_t, *pWmmAciAifsn_t;
typedef MLAN_PACK_START struct _WmmAcParameters_t {
	WmmAciAifsn_t aci_aifsn;
	WmmEcw_t ecw;
	t_u16 tx_op_limit;
} MLAN_PACK_END WmmAcParameters_t, *pWmmAcParameters_t;
typedef MLAN_PACK_START struct _WmmParameter_t {
	t_u8 ouitype[4];
	t_u8 ouisubtype;
	t_u8 version;
	t_u8 qos_info;
	t_u8 reserved;
	WmmAcParameters_t ac_params[MAX_AC_QUEUES];
} MLAN_PACK_END WmmParameter_t, *pWmmParameter_t;
typedef MLAN_PACK_START struct _HostCmd_DS_WMM_PARAM_CONFIG {
	t_u16 action;
	WmmAcParameters_t ac_params[MAX_AC_QUEUES];
} MLAN_PACK_END HostCmd_DS_WMM_PARAM_CONFIG;
typedef MLAN_PACK_START struct _HostCmd_DS_GEN {
	t_u16 command;
	t_u16 size;
	t_u16 seq_num;
	t_u16 result;
} MLAN_PACK_END HostCmd_DS_GEN
;
#define S_DS_GEN        sizeof(HostCmd_DS_GEN)
typedef MLAN_PACK_START struct _mod_group_setting {
	t_u8 mod_group;
	t_u8 power;
} MLAN_PACK_END mod_group_setting;
typedef MLAN_PACK_START struct _MrvlIETypes_ChanTRPCConfig_t {
	MrvlIEtypesHeader_t header;
	t_u16 start_freq;
	t_u8 width;
	t_u8 chan_num;
	mod_group_setting mod_group[0];
} MLAN_PACK_END MrvlIETypes_ChanTRPCConfig_t;
typedef MLAN_PACK_START struct _HostCmd_DS_CHANNEL_TRPC_CONFIG {
	t_u16 action;
	t_u16 sub_band;
	MrvlIETypes_ChanTRPCConfig_t tlv[0];
} MLAN_PACK_END HostCmd_DS_CHANNEL_TRPC_CONFIG;
#define ADDR_TYPE_BROADCAST		1
#define ADDR_TYPE_UNICAST		2
#define ADDR_TYPE_MULTICAST		3
#define ETHER_TYPE_ANY			0xffff
#define ETHER_TYPE_ARP			0x0608
#define IPV4_ADDR_ANY			0xffffffff
typedef MLAN_PACK_START struct _arpfilter_header {
	t_u16 type;
	t_u16 len;
} MLAN_PACK_END arpfilter_header;
typedef MLAN_PACK_START struct _filter_entry {
	t_u16 addr_type;
	t_u16 eth_type;
	t_u32 ipv4_addr;
} MLAN_PACK_END filter_entry;
typedef MLAN_PACK_START struct _HostCmd_DS_MEF_CFG {
	t_u32 criteria;
	t_u16 nentries;
} MLAN_PACK_END HostCmd_DS_MEF_CFG;
typedef MLAN_PACK_START struct _HostCmd_DS_802_11_SLEEP_PERIOD {
	t_u16 action;
	t_u16 sleep_pd;
} MLAN_PACK_END HostCmd_DS_802_11_SLEEP_PERIOD;
typedef MLAN_PACK_START struct _HostCmd_DS_802_11_SLEEP_PARAMS {
	t_u16 action;
	t_u16 error;
	t_u16 offset;
	t_u16 stable_time;
	t_u8 cal_control;
	t_u8 external_sleep_clk;
	t_u16 reserved;
} MLAN_PACK_END HostCmd_DS_802_11_SLEEP_PARAMS;
typedef enum _sleep_resp_ctrl {
	RESP_NOT_NEEDED = 0,
	RESP_NEEDED,
} sleep_resp_ctrl;
typedef MLAN_PACK_START struct __ps_param {
	t_u16 null_pkt_interval;
	t_u16 multiple_dtims;
	t_u16 bcn_miss_timeout;
	t_u16 local_listen_interval;
	t_u16 adhoc_wake_period;
	t_u16 mode;
	t_u16 delay_to_ps;
} MLAN_PACK_END ps_param;
typedef MLAN_PACK_START struct __auto_ds_param {
	t_u16 deep_sleep_timeout;
} MLAN_PACK_END auto_ds_param;
typedef MLAN_PACK_START struct __sleep_confirm_param {
	t_u16 resp_ctrl;
} MLAN_PACK_END sleep_confirm_param;
#define BITMAP_AUTO_DS         0x01
#define BITMAP_STA_PS          0x10
#define BITMAP_BCN_TMO         0x20
#define BITMAP_UAP_INACT_PS    0x100
#define BITMAP_UAP_DTIM_PS     0x200
typedef MLAN_PACK_START struct _auto_ps_param {
	t_u16 ps_bitmap;
} MLAN_PACK_END auto_ps_param;
#define AUTO_PS_FIX_SIZE    4
#define TLV_TYPE_AUTO_DS_PARAM        (PROPRIETARY_TLV_BASE_ID + 0x71)
#define TLV_TYPE_PS_PARAM             (PROPRIETARY_TLV_BASE_ID + 0x72)
#define TLV_TYPE_BCN_TIMEOUT          (PROPRIETARY_TLV_BASE_ID + 0x11F)
typedef MLAN_PACK_START struct _MrvlIEtypes_auto_ds_param_t {
	MrvlIEtypesHeader_t header;
	auto_ds_param param;
} MLAN_PACK_END MrvlIEtypes_auto_ds_param_t;
typedef MLAN_PACK_START struct _MrvlIEtypes_ps_param_t {
	MrvlIEtypesHeader_t header;
	ps_param param;
} MLAN_PACK_END MrvlIEtypes_ps_param_t;
typedef MLAN_PACK_START struct _MrvlIEtypes_bcn_timeout_t {
	MrvlIEtypesHeader_t header;
	t_u16 bcn_miss_tmo_window;
	t_u16 bcn_miss_tmo_period;
	t_u16 bcn_rq_tmo_window;
	t_u16 bcn_rq_tmo_period;
} MLAN_PACK_END MrvlIEtypes_bcn_timeout_t;
typedef MLAN_PACK_START struct _HostCmd_DS_PS_MODE_ENH {
	t_u16 action;
	union {
		ps_param opt_ps;
		auto_ds_param auto_ds;
		sleep_confirm_param sleep_cfm;
		t_u16 ps_bitmap;
		auto_ps_param auto_ps;
	} params;
} MLAN_PACK_END HostCmd_DS_802_11_PS_MODE_ENH;
#define TLV_TYPE_FW_VER_INFO        (PROPRIETARY_TLV_BASE_ID + 0xC7)
typedef MLAN_PACK_START struct _MrvlIEtypes_fw_ver_info_t {
	MrvlIEtypesHeader_t header;
	t_u16 api_id;
	t_u8 major_ver;
	t_u8 minor_ver;
} MLAN_PACK_END MrvlIEtypes_fw_ver_info_t;
enum API_VER_ID {
	KEY_API_VER_ID = 1,
	FW_API_VER_ID = 2,
	UAP_FW_API_VER_ID = 3,
	CHANRPT_API_VER_ID = 4,
};
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
