balena-io-hardware/fin-info-doc/software/drivers/sd8887/src/bluetooth/bt/bt_main.c

/** @file bt_main.c
 *
 *  @brief This file contains the major functions in BlueTooth
 *  driver. It includes init, exit, open, close and main
 *  thread etc..
 *
 *
 *  Copyright 2014-2020 NXP
 *
 *  This software file (the File) is distributed by NXP
 *  under the terms of the GNU General Public License Version 2, June 1991
 *  (the License).  You may use, redistribute and/or modify the File in
 *  accordance with the terms and conditions of the License, a copy of which
 *  is available by writing to the Free Software Foundation, Inc.,
 *  51 Franklin Street, Fifth Floor, Boston, MA 02110-1301 USA or on the
 *  worldwide web at http://www.gnu.org/licenses/old-licenses/gpl-2.0.txt.
 *
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
 */
/**
  * @mainpage M-BT Linux Driver
  *
  * @section overview_sec Overview
  *
  * The M-BT is a Linux reference driver for NXP Bluetooth chipset.
  *
  * @section copyright_sec Copyright
  *
  * Copyright 2014-2020 NXP
  *
  */

#include <linux/module.h>

#ifdef CONFIG_OF
#include <linux/of.h>
#endif

#include <linux/mmc/sdio_func.h>

#include "bt_drv.h"
#include "mbt_char.h"
#include "bt_sdio.h"

/** Version */
#define VERSION "C4X14114"

/** Driver version */
static char mbt_driver_version[] = "SD8887-%s-" VERSION "-(" "FP" FPNUM ")"
#ifdef DEBUG_LEVEL2
	"-dbg"
#endif
	" ";

/** Declare and initialize fw_version */
static char fw_version[32] = "0.0.0.p0";

#define AID_SYSTEM        1000	/* system server */

#define AID_BLUETOOTH     1002	/* bluetooth subsystem */

#define AID_NET_BT_STACK  3008	/* bluetooth stack */

/** Define module name */

#define MODULE_NAME  "bt_fm_nfc"

/** Declaration of chardev class */
static struct class *chardev_class;

/** Interface specific variables */

/**
 * The global variable of a pointer to bt_private
 * structure variable
 **/
bt_private *m_priv[MAX_BT_ADAPTER];

/** Default Driver mode */
static int drv_mode = (DRV_MODE_BT);

/** fw serial download flag */
int bt_fw_serial = 1;

/** Firmware flag */
static int fw = 1;
/** default powermode */
static int psmode = 1;
/** default BLE deep sleep */
static int deep_sleep = 1;
/** init cmds file */
static char *init_cmds;
/** Init config file (MAC address, register etc.) */
static char *init_cfg;
/** Calibration config file (MAC address, init powe etc.) */
static char *cal_cfg;
/** Calibration config file EXT */
static char *cal_cfg_ext;
/** Init MAC address */
static char *bt_mac;

/** Setting mbt_drvdbg value based on DEBUG level */
#ifdef DEBUG_LEVEL1
#ifdef DEBUG_LEVEL2
#define DEFAULT_DEBUG_MASK  (0xffffffff & ~DBG_EVENT)
#else
#define DEFAULT_DEBUG_MASK  (DBG_MSG | DBG_FATAL | DBG_ERROR)
#endif /* DEBUG_LEVEL2 */
u32 mbt_drvdbg = DEFAULT_DEBUG_MASK;
#endif

#ifdef CONFIG_OF
static int dts_enable = 1;
#endif

#ifdef SDIO_SUSPEND_RESUME
/** PM keep power */
int mbt_pm_keep_power = 1;
#endif

/** Offset of sequence number in event */
#define OFFSET_SEQNUM 4

/**
 *  @brief handle received packet
 *  @param priv    A pointer to bt_private structure
 *  @param skb     A pointer to rx skb
 *
 *  @return        N/A
 */
void
bt_recv_frame(bt_private *priv, struct sk_buff *skb)
{
	struct hci_dev *hdev = NULL;
	if (priv->bt_dev.m_dev[BT_SEQ].spec_type == BLUEZ_SPEC)
		hdev = (struct hci_dev *)priv->bt_dev.m_dev[BT_SEQ].dev_pointer;
	if (hdev) {
		skb->dev = (void *)hdev;
		hdev->stat.byte_rx += skb->len;
#if LINUX_VERSION_CODE < KERNEL_VERSION(3, 13, 0)
		hci_recv_frame(skb);
#else
		hci_recv_frame(hdev, skb);
#endif
	}
	return;
}

/**
 *  @brief Alloc bt device
 *
 *  @return    pointer to structure mbt_dev or NULL
 */
struct mbt_dev *
alloc_mbt_dev(void)
{
	struct mbt_dev *mbt_dev;
	ENTER();

	mbt_dev = kzalloc(sizeof(struct mbt_dev), GFP_KERNEL);
	if (!mbt_dev) {
		LEAVE();
		return NULL;
	}

	LEAVE();
	return mbt_dev;
}

/**
 *  @brief Frees m_dev
 *
 *  @return    N/A
 */
void
free_m_dev(struct m_dev *m_dev)
{
	ENTER();
	kfree(m_dev->dev_pointer);
	m_dev->dev_pointer = NULL;
	LEAVE();
}

/**
 *  @brief clean up m_devs
 *
 *  @return    N/A
 */
void
clean_up_m_devs(bt_private *priv)
{
	struct m_dev *m_dev = NULL;
	struct hci_dev *hdev = NULL;

	ENTER();
	if (priv->bt_dev.m_dev[BT_SEQ].dev_pointer) {
		m_dev = &(priv->bt_dev.m_dev[BT_SEQ]);
		PRINTM(MSG, "BT: Delete %s\n", m_dev->name);
		if (m_dev->spec_type == BLUEZ_SPEC) {
			hdev = (struct hci_dev *)m_dev->dev_pointer;
			/** check if dev->name has been assigned */
			if (strstr(hdev->name, "hci"))
				hci_unregister_dev(hdev);
			hci_free_dev(hdev);
		}
		priv->bt_dev.m_dev[BT_SEQ].dev_pointer = NULL;
	}
	LEAVE();
	return;
}

/**
 *  @brief This function verify the received event pkt
 *
 *  Event format:
 *  +--------+--------+--------+--------+--------+
 *  | Event  | Length |  ncmd  |      Opcode     |
 *  +--------+--------+--------+--------+--------+
 *  | 1-byte | 1-byte | 1-byte |      2-byte     |
 *  +--------+--------+--------+--------+--------+
 *
 *  @param priv    A pointer to bt_private structure
 *  @param skb     A pointer to rx skb
 *  @return    BT_STATUS_SUCCESS or BT_STATUS_FAILURE
 */
int
check_evtpkt(bt_private *priv, struct sk_buff *skb)
{
	struct hci_event_hdr *hdr = (struct hci_event_hdr *)skb->data;
	struct hci_ev_cmd_complete *ec;
	u16 opcode, ocf;
	int ret = BT_STATUS_SUCCESS;
	ENTER();
	if (!priv->bt_dev.sendcmdflag) {
		ret = BT_STATUS_FAILURE;
		goto exit;
	}
	if (hdr->evt == HCI_EV_CMD_COMPLETE) {
		ec = (struct hci_ev_cmd_complete *)
			(skb->data + HCI_EVENT_HDR_SIZE);
		opcode = __le16_to_cpu(ec->opcode);
		ocf = hci_opcode_ocf(opcode);
		PRINTM(CMD,
		       "BT: CMD_COMPLTE opcode=0x%x, ocf=0x%x, send_cmd_opcode=0x%x\n",
		       opcode, ocf, priv->bt_dev.send_cmd_opcode);
		if (opcode != priv->bt_dev.send_cmd_opcode) {
			ret = BT_STATUS_FAILURE;
			goto exit;
		}
		switch (ocf) {
		case BT_CMD_MODULE_CFG_REQ:
		case BT_CMD_BLE_DEEP_SLEEP:
		case BT_CMD_CONFIG_MAC_ADDR:
		case BT_CMD_CSU_WRITE_REG:
		case BT_CMD_LOAD_CONFIG_DATA:
		case BT_CMD_LOAD_CONFIG_DATA_EXT:
		case BT_CMD_AUTO_SLEEP_MODE:
		case BT_CMD_HOST_SLEEP_CONFIG:
		case BT_CMD_SDIO_PULL_CFG_REQ:
		case BT_CMD_SET_EVT_FILTER:
			// case BT_CMD_ENABLE_DEVICE_TESTMODE:
			priv->bt_dev.sendcmdflag = FALSE;
			priv->adapter->cmd_complete = TRUE;
			wake_up_interruptible(&priv->adapter->cmd_wait_q);
			break;
		case BT_CMD_GET_FW_VERSION:
			{
				u8 *pos = (skb->data + HCI_EVENT_HDR_SIZE +
					   sizeof(struct hci_ev_cmd_complete) +
					   1);
				snprintf(fw_version, sizeof(fw_version),
					 "%u.%u.%u.p%u", pos[2], pos[1], pos[0],
					 pos[3]);
				priv->bt_dev.sendcmdflag = FALSE;
				priv->adapter->cmd_complete = TRUE;
				wake_up_interruptible(&priv->adapter->
						      cmd_wait_q);
				break;
			}
		case BT_CMD_HISTOGRAM:
			{
				u8 *status =
					skb->data + HCI_EVENT_HDR_SIZE +
					sizeof(struct hci_ev_cmd_complete);
				u8 *pos =
					(skb->data + HCI_EVENT_HDR_SIZE +
					 sizeof(struct hci_ev_cmd_complete) +
					 1);
				if (*status == 0) {
					priv->hist_data_len =
						hdr->plen -
						sizeof(struct
						       hci_ev_cmd_complete) - 1;
					if (priv->hist_data_len >
					    sizeof(priv->hist_data))
						priv->hist_data_len =
							sizeof(priv->hist_data);
					memcpy(priv->hist_data, pos,
					       priv->hist_data_len);
					PRINTM(CMD, "histogram len=%d\n",
					       priv->hist_data_len);
				}
				priv->bt_dev.sendcmdflag = FALSE;
				priv->adapter->cmd_complete = TRUE;
				wake_up_interruptible(&priv->adapter->
						      cmd_wait_q);
				break;
			}
		case BT_CMD_RESET:
		case BT_CMD_ENABLE_WRITE_SCAN:
			{
				priv->bt_dev.sendcmdflag = FALSE;
				priv->adapter->cmd_complete = TRUE;
				if (priv->adapter->wait_event_timeout == TRUE) {
					wake_up(&priv->adapter->cmd_wait_q);
					priv->adapter->wait_event_timeout =
						FALSE;
				} else
					wake_up_interruptible(&priv->adapter->
							      cmd_wait_q);
			}
			break;
		case BT_CMD_HOST_SLEEP_ENABLE:
			priv->bt_dev.sendcmdflag = FALSE;
			break;
		default:
			/** Ignore command not defined but send by driver */
			if (opcode == priv->bt_dev.send_cmd_opcode) {
				priv->bt_dev.sendcmdflag = FALSE;
				priv->adapter->cmd_complete = TRUE;
				wake_up_interruptible(&priv->adapter->
						      cmd_wait_q);
			} else {
				ret = BT_STATUS_FAILURE;
			}
			break;
		}
	} else
		ret = BT_STATUS_FAILURE;
exit:
	if (ret == BT_STATUS_SUCCESS)
		kfree_skb(skb);
	LEAVE();
	return ret;
}

/**
*  @brief This function stores the FW dumps received from events
*
*  @param priv    A pointer to bt_private structure
*  @param skb     A pointer to rx skb
*
*  @return        N/A
*/
void
bt_store_firmware_dump(bt_private *priv, u8 *buf, u32 len)
{
	struct file *pfile_fwdump = NULL;
	loff_t pos = 0;
	u16 seqnum = 0;
	bt_timeval t;
	u32 sec;

	ENTER();

	seqnum = __le16_to_cpu(*(u16 *) (buf + OFFSET_SEQNUM));

	if (priv->adapter->fwdump_fname && seqnum != 1) {
		pfile_fwdump =
			filp_open((const char *)priv->adapter->fwdump_fname,
				  O_CREAT | O_WRONLY | O_APPEND, 0644);
		if (IS_ERR(pfile_fwdump)) {
			PRINTM(MSG, "Cannot create firmware dump file.\n");
			LEAVE();
			return;
		}
	} else {
		if (!priv->adapter->fwdump_fname) {
			gfp_t flag;
			flag = (in_atomic() ||
				irqs_disabled())? GFP_ATOMIC : GFP_KERNEL;
			priv->adapter->fwdump_fname = kzalloc(64, flag);
		} else
			memset(priv->adapter->fwdump_fname, 0, 64);

		get_monotonic_time(&t);
		sec = (u32)t.time_sec;
		sprintf(priv->adapter->fwdump_fname, "%s%u",
			"/var/log/bt_fwdump_", sec);
		pfile_fwdump =
			filp_open(priv->adapter->fwdump_fname,
				  O_CREAT | O_WRONLY | O_APPEND, 0644);
		if (IS_ERR(pfile_fwdump)) {
			sprintf(priv->adapter->fwdump_fname, "%s%u",
				"/data/bt_fwdump_", sec);
			pfile_fwdump =
				filp_open((const char *)priv->adapter->
					  fwdump_fname,
					  O_CREAT | O_WRONLY | O_APPEND, 0644);
		}
	}

	if (IS_ERR(pfile_fwdump)) {
		PRINTM(MSG, "Cannot create firmware dump file\n");
		LEAVE();
		return;
	}
#if LINUX_VERSION_CODE < KERNEL_VERSION(4, 14, 0)
	vfs_write(pfile_fwdump, buf, len, &pos);
#else
	kernel_write(pfile_fwdump, buf, len, &pos);
#endif
	filp_close(pfile_fwdump, NULL);
	LEAVE();
	return;
}

/**
 *  @brief This function process the received event
 *
 *  Event format:
 *  +--------+--------+--------+--------+-----+
 *  |   EC   | Length |           Data        |
 *  +--------+--------+--------+--------+-----+
 *  | 1-byte | 1-byte |          n-byte       |
 *  +--------+--------+--------+--------+-----+
 *
 *  @param priv    A pointer to bt_private structure
 *  @param skb     A pointer to rx skb
 *  @return    BT_STATUS_SUCCESS or BT_STATUS_FAILURE
 */
int
bt_process_event(bt_private *priv, struct sk_buff *skb)
{
	int ret = BT_STATUS_SUCCESS;
#ifdef DEBUG_LEVEL1
	struct m_dev *m_dev = &(priv->bt_dev.m_dev[BT_SEQ]);
#endif
	BT_EVENT *pevent;

	ENTER();
	if (!m_dev) {
		PRINTM(CMD, "BT: bt_process_event without m_dev\n");
		ret = BT_STATUS_FAILURE;
		goto exit;
	}
	pevent = (BT_EVENT *)skb->data;
	if (pevent->EC != 0xff) {
		PRINTM(CMD, "BT: Not NXP Event=0x%x\n", pevent->EC);
		ret = BT_STATUS_FAILURE;
		goto exit;
	}
	switch (pevent->data[0]) {
	case BT_CMD_HISTOGRAM:
		break;
	case BT_CMD_AUTO_SLEEP_MODE:
		if (pevent->data[2] == BT_STATUS_SUCCESS) {
			if (pevent->data[1] == BT_PS_ENABLE)
				priv->adapter->psmode = 1;
			else
				priv->adapter->psmode = 0;
			PRINTM(CMD, "BT: PS Mode %s:%s\n", m_dev->name,
			       (priv->adapter->psmode) ? "Enable" : "Disable");

		} else {
			PRINTM(CMD, "BT: PS Mode Command Fail %s\n",
			       m_dev->name);
		}
		break;
	case BT_CMD_HOST_SLEEP_CONFIG:
		if (pevent->data[3] == BT_STATUS_SUCCESS) {
			PRINTM(CMD, "BT: %s: gpio=0x%x, gap=0x%x\n",
			       m_dev->name, pevent->data[1], pevent->data[2]);
		} else {
			PRINTM(CMD, "BT: %s: HSCFG Command Fail\n",
			       m_dev->name);
		}
		break;
	case BT_CMD_HOST_SLEEP_ENABLE:
		if (pevent->data[1] == BT_STATUS_SUCCESS) {
			priv->adapter->hs_state = HS_ACTIVATED;
			if (priv->adapter->suspend_fail == FALSE) {
#ifdef SDIO_SUSPEND_RESUME
#ifdef MMC_PM_KEEP_POWER
#ifdef MMC_PM_FUNC_SUSPENDED
				bt_is_suspended(priv);
#endif
#endif
#endif
				if (priv->adapter->wait_event_timeout) {
					wake_up(&priv->adapter->cmd_wait_q);
					priv->adapter->wait_event_timeout =
						FALSE;
				} else
					wake_up_interruptible(&priv->adapter->
							      cmd_wait_q);

			}
			if (priv->adapter->psmode)
				priv->adapter->ps_state = PS_SLEEP;
			PRINTM(CMD, "BT: EVENT %s: HS ACTIVATED!\n",
			       m_dev->name);

		} else {
			PRINTM(CMD, "BT: %s: HS Enable Fail\n", m_dev->name);
		}
		break;
	case BT_CMD_MODULE_CFG_REQ:
		if ((priv->bt_dev.sendcmdflag == TRUE) &&
		    ((pevent->data[1] == MODULE_BRINGUP_REQ)
		     || (pevent->data[1] == MODULE_SHUTDOWN_REQ))) {
			if (pevent->data[1] == MODULE_BRINGUP_REQ) {
				PRINTM(CMD, "BT: EVENT %s:%s\n", m_dev->name,
				       (pevent->data[2] && (pevent->data[2] !=
							    MODULE_CFG_RESP_ALREADY_UP))
				       ? "Bring up Fail" : "Bring up success");
				priv->bt_dev.devType = pevent->data[3];
				PRINTM(CMD, "devType:%s\n",
				       (pevent->data[3] ==
					DEV_TYPE_AMP) ? "AMP controller" :
				       "BR/EDR controller");
				priv->bt_dev.devFeature = pevent->data[4];
				PRINTM(CMD, "devFeature:  %s,    %s,    %s"
				       "\n",
				       ((pevent->
					 data[4] & DEV_FEATURE_BT) ?
					"BT Feature" : "No BT Feature"),
				       ((pevent->
					 data[4] & DEV_FEATURE_BTAMP) ?
					"BTAMP Feature" : "No BTAMP Feature"),
				       ((pevent->
					 data[4] & DEV_FEATURE_BLE) ?
					"BLE Feature" : "No BLE Feature")
					);
			}
			if (pevent->data[1] == MODULE_SHUTDOWN_REQ) {
				PRINTM(CMD, "BT: EVENT %s:%s\n", m_dev->name,
				       (pevent->data[2]) ? "Shut down Fail"
				       : "Shut down success");

			}
			if (pevent->data[2]) {
				priv->bt_dev.sendcmdflag = FALSE;
				priv->adapter->cmd_complete = TRUE;
				wake_up_interruptible(&priv->adapter->
						      cmd_wait_q);
			}
		} else {
			PRINTM(CMD, "BT_CMD_MODULE_CFG_REQ resp for APP\n");
			ret = BT_STATUS_FAILURE;
		}
		break;
	case BT_EVENT_POWER_STATE:
		if (pevent->data[1] == BT_PS_SLEEP)
			priv->adapter->ps_state = PS_SLEEP;
		if (priv->adapter->ps_state == PS_SLEEP)
			os_sched_timeout(5);
		PRINTM(CMD, "BT: EVENT %s:%s\n", m_dev->name,
		       (priv->adapter->ps_state) ? "PS_SLEEP" : "PS_AWAKE");

		break;
	case BT_CMD_SDIO_PULL_CFG_REQ:
		if (pevent->data[pevent->length - 1] == BT_STATUS_SUCCESS)
			PRINTM(CMD, "BT: %s: SDIO pull configuration success\n",
			       m_dev->name);

		else {
			PRINTM(CMD, "BT: %s: SDIO pull configuration fail\n",
			       m_dev->name);

		}
		break;
	default:
		PRINTM(CMD, "BT: Unknown Event=%d %s\n", pevent->data[0],
		       m_dev->name);
		ret = BT_STATUS_FAILURE;
		break;
	}
exit:
	if (ret == BT_STATUS_SUCCESS)
		kfree_skb(skb);
	LEAVE();
	return ret;
}

/**
 *  @brief This function save the dump info to file
 *
 *  @param dir_name     directory name
 *  @param file_name    file_name
 *  @param buf			buffer
 *  @param buf_len		buffer length
 *
 *  @return   		    0 --success otherwise fail
 */
int
bt_save_dump_info_to_file(char *dir_name, char *file_name, u8 *buf, u32 buf_len)
{
	int ret = BT_STATUS_SUCCESS;
	struct file *pfile = NULL;
	u8 name[64];
	loff_t pos;
#if LINUX_VERSION_CODE < KERNEL_VERSION(4, 14, 0)
	mm_segment_t fs;
#endif

	ENTER();

	if (!dir_name || !file_name || !buf) {
		PRINTM(ERROR, "Can't save dump info to file\n");
		ret = BT_STATUS_FAILURE;
		goto done;
	}

	memset(name, 0, sizeof(name));
	snprintf((char *)name, sizeof(name), "%s/%s", dir_name, file_name);
	pfile = filp_open((const char *)name, O_CREAT | O_RDWR, 0644);
	if (IS_ERR(pfile)) {
		PRINTM(MSG,
		       "Create file %s error, try to save dump file in /var\n",
		       name);
		memset(name, 0, sizeof(name));
		snprintf((char *)name, sizeof(name), "%s/%s", "/var",
			 file_name);
		pfile = filp_open((const char *)name, O_CREAT | O_RDWR, 0644);
	}
	if (IS_ERR(pfile)) {
		PRINTM(ERROR, "Create Dump file for %s error\n", name);
		ret = BT_STATUS_FAILURE;
		goto done;
	}

	PRINTM(MSG, "Dump data %s saved in %s\n", file_name, name);

	pos = 0;
#if LINUX_VERSION_CODE < KERNEL_VERSION(4, 14, 0)
	fs = get_fs();
	set_fs(KERNEL_DS);
	vfs_write(pfile, (const char __user *)buf, buf_len, &pos);
	set_fs(fs);
#else
	kernel_write(pfile, (const char __user *)buf, buf_len, &pos);
#endif
	filp_close(pfile, NULL);

	PRINTM(MSG, "Dump data %s saved in %s successfully\n", file_name, name);

done:
	LEAVE();
	return ret;
}

#define DEBUG_HOST_READY		0xEE
#define DEBUG_FW_DONE			0xFF
#define DUMP_MAX_POLL_TRIES			200

#define DEBUG_DUMP_CTRL_REG               0xA2
#define DEBUG_DUMP_START_REG              0xA3
#define DEBUG_DUMP_END_REG                0xAA

typedef enum {
	DUMP_TYPE_ITCM = 0,
	DUMP_TYPE_DTCM = 1,
	DUMP_TYPE_SQRAM = 2,
	DUMP_TYPE_APU_REGS = 3,
	DUMP_TYPE_CIU_REGS = 4,
	DUMP_TYPE_ICU_REGS = 5,
	DUMP_TYPE_MAC_REGS = 6,
	DUMP_TYPE_EXTEND_7 = 7,
	DUMP_TYPE_EXTEND_8 = 8,
	DUMP_TYPE_EXTEND_9 = 9,
	DUMP_TYPE_EXTEND_10 = 10,
	DUMP_TYPE_EXTEND_11 = 11,
	DUMP_TYPE_EXTEND_12 = 12,
	DUMP_TYPE_EXTEND_13 = 13,
	DUMP_TYPE_EXTEND_LAST = 14
} dumped_mem_type;

#define MAX_NAME_LEN               8
#define MAX_FULL_NAME_LEN               32

/** Memory type mapping structure */
typedef struct {
	/** memory name */
	u8 mem_name[MAX_NAME_LEN];
	/** memory pointer */
	u8 *mem_Ptr;
	/** file structure */
	struct file *pfile_mem;
	/** donbe flag */
	u8 done_flag;
	/** dump type */
	u8 type;
} memory_type_mapping;

memory_type_mapping bt_mem_type_mapping_tbl[] = {
	{"ITCM", NULL, NULL, 0xF0, FW_DUMP_TYPE_MEM_ITCM},
	{"DTCM", NULL, NULL, 0xF1, FW_DUMP_TYPE_MEM_DTCM},
	{"SQRAM", NULL, NULL, 0xF2, FW_DUMP_TYPE_MEM_SQRAM},
	{"APU", NULL, NULL, 0xF3, FW_DUMP_TYPE_REG_APU},
	{"CIU", NULL, NULL, 0xF4, FW_DUMP_TYPE_REG_CIU},
	{"ICU", NULL, NULL, 0xF5, FW_DUMP_TYPE_REG_ICU},
	{"MAC", NULL, NULL, 0xF6, FW_DUMP_TYPE_REG_MAC},
	{"EXT7", NULL, NULL, 0xF7},
	{"EXT8", NULL, NULL, 0xF8},
	{"EXT9", NULL, NULL, 0xF9},
	{"EXT10", NULL, NULL, 0xFA},
	{"EXT11", NULL, NULL, 0xFB},
	{"EXT12", NULL, NULL, 0xFC},
	{"EXT13", NULL, NULL, 0xFD},
	{"EXTLAST", NULL, NULL, 0xFE},
};

typedef enum {
	RDWR_STATUS_SUCCESS = 0,
	RDWR_STATUS_FAILURE = 1,
	RDWR_STATUS_DONE = 2
} rdwr_status;
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
